rgalland/SNES_S-CPU_Schematics/S-CPU_gates/AND.png

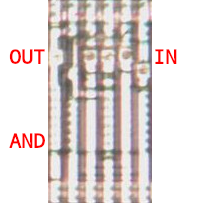
S-CPU_gates/AND.png
