rgalland/SNES_S-CPU_Schematics/S-CPU_gates/AOI_22.png

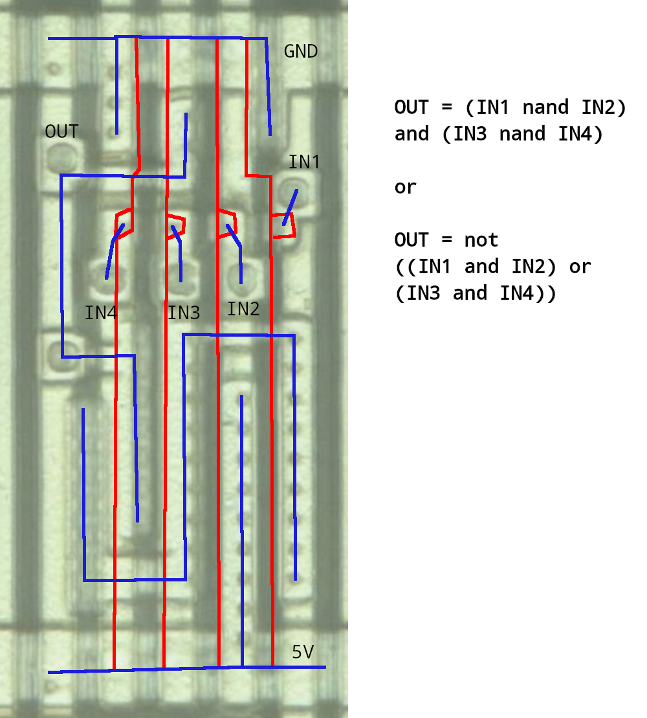
S-CPU_gates/AOI_22.png
