rgalland/SNES_S-CPU_Schematics/S-CPU_gates/AOI_222.png

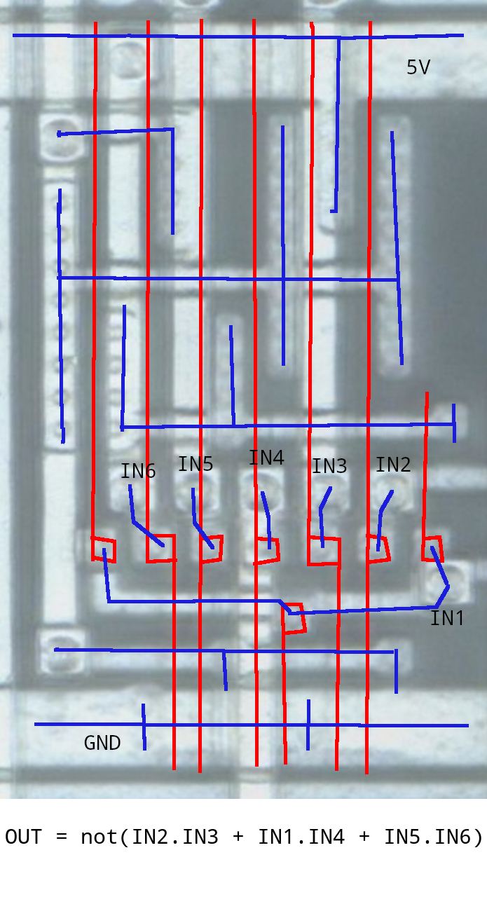
S-CPU_gates/AOI_222.png
