rgalland/SNES_S-CPU_Schematics/S-CPU_gates/Buf.png

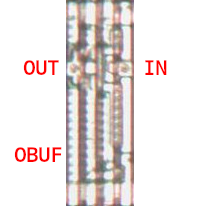
S-CPU_gates/Buf.png
