rgalland/SNES_S-CPU_Schematics/S-CPU_gates/BUF_HiZ.png

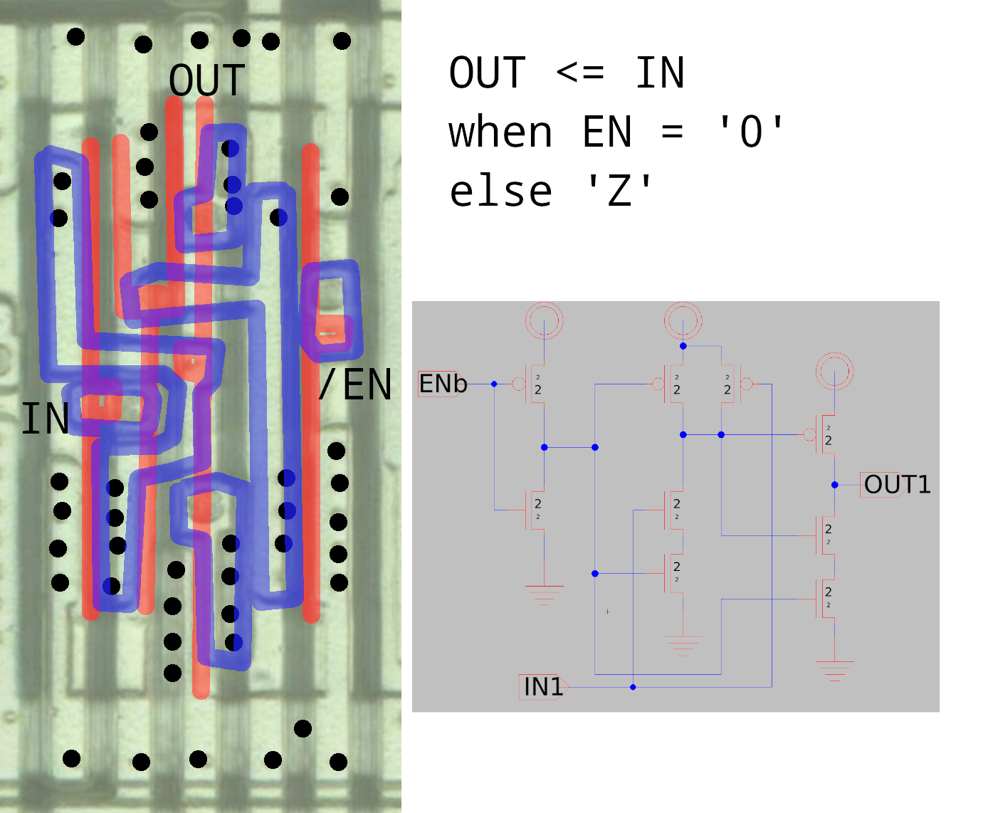
S-CPU_gates/BUF_HiZ.png
