rgalland/SNES_S-CPU_Schematics/S-CPU_gates/bus_direction_buffer.png

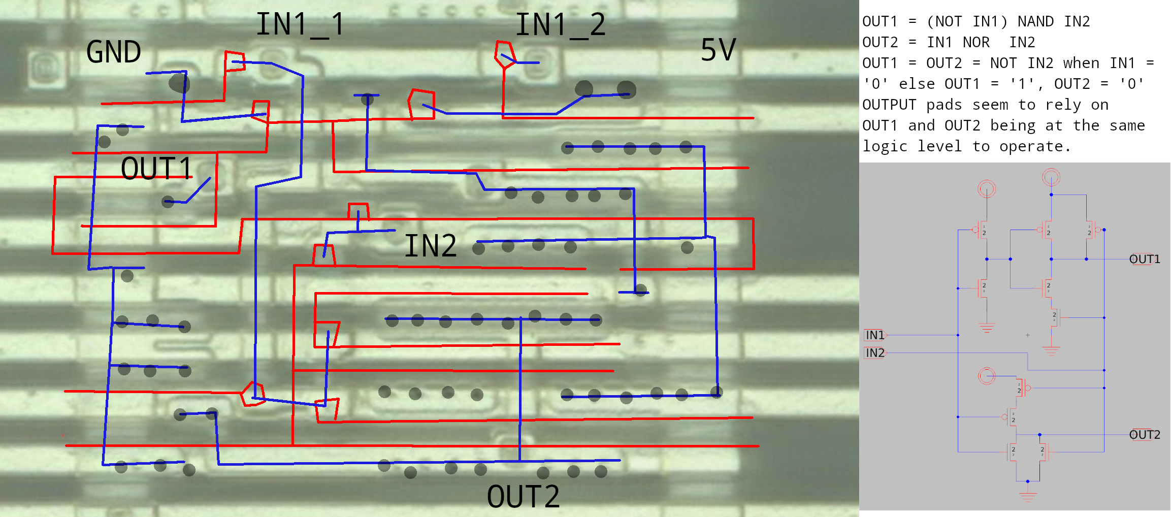
S-CPU_gates/bus_direction_buffer.png
