rgalland/SNES_S-CPU_Schematics/S-CPU_gates/DEMUX_3-8.png

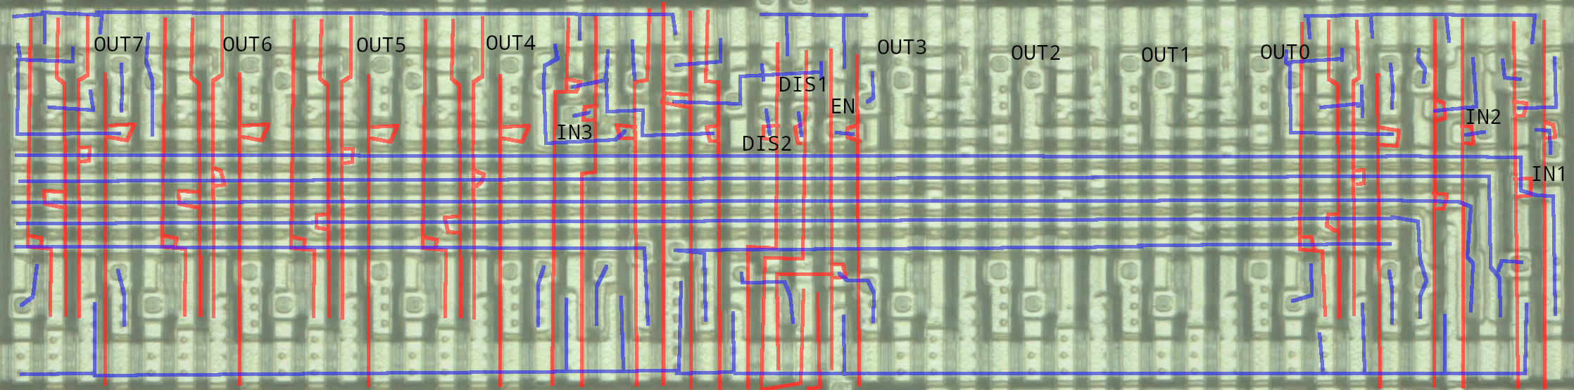
S-CPU_gates/DEMUX_3-8.png
