rgalland/SNES_S-CPU_Schematics/S-CPU_gates/dff.png

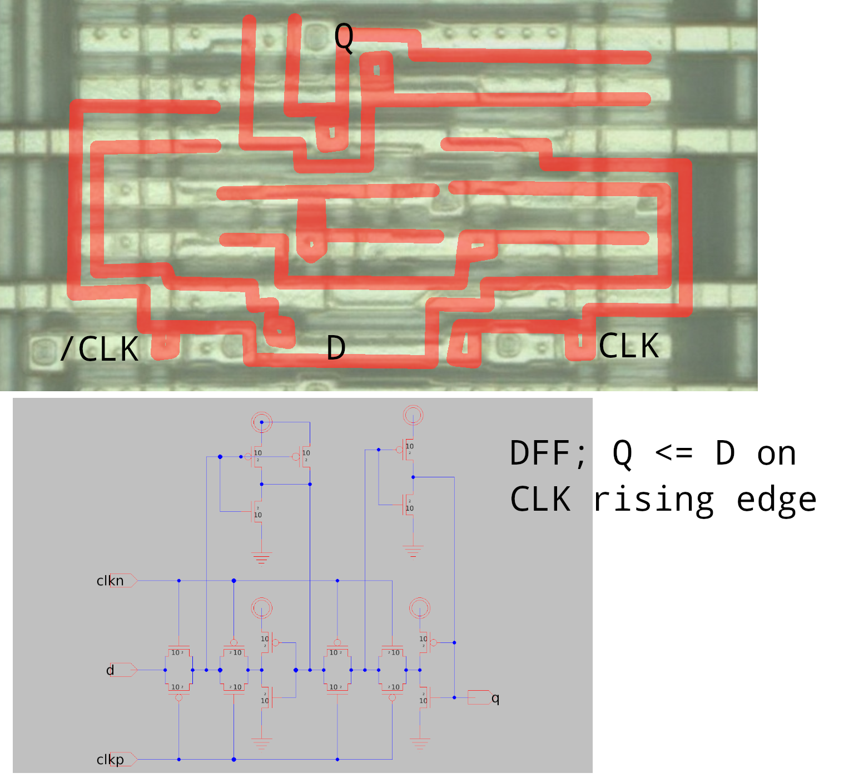
S-CPU_gates/dff.png
