rgalland/SNES_S-CPU_Schematics/S-CPU_gates/dff_wEn.png

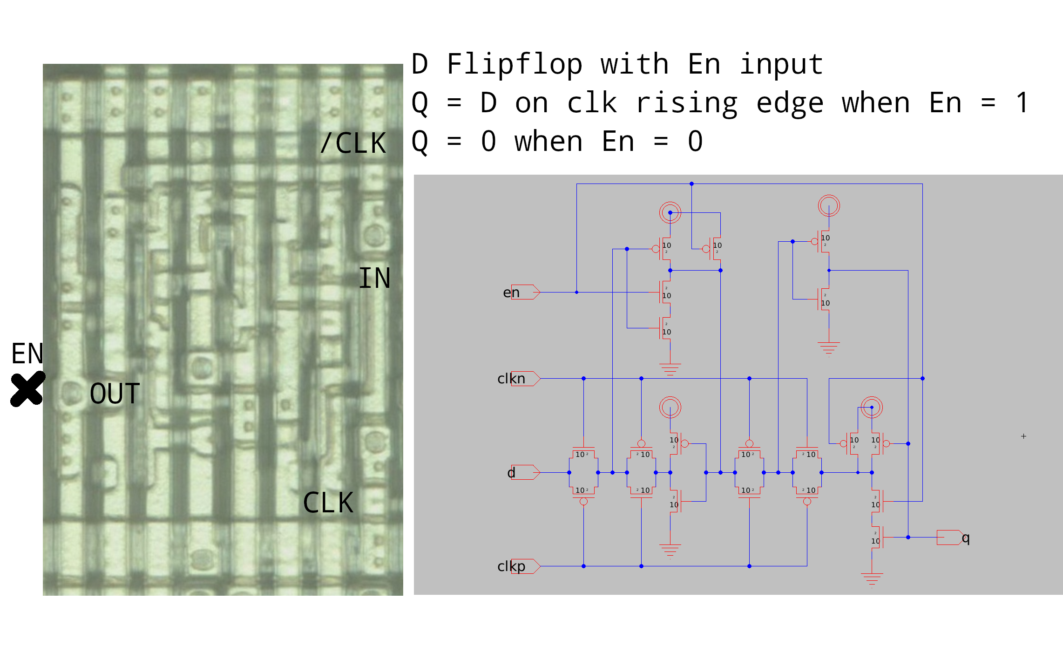
S-CPU_gates/dff_wEn.png
