rgalland/SNES_S-CPU_Schematics/S-CPU_gates/dff_wEn_v4.png

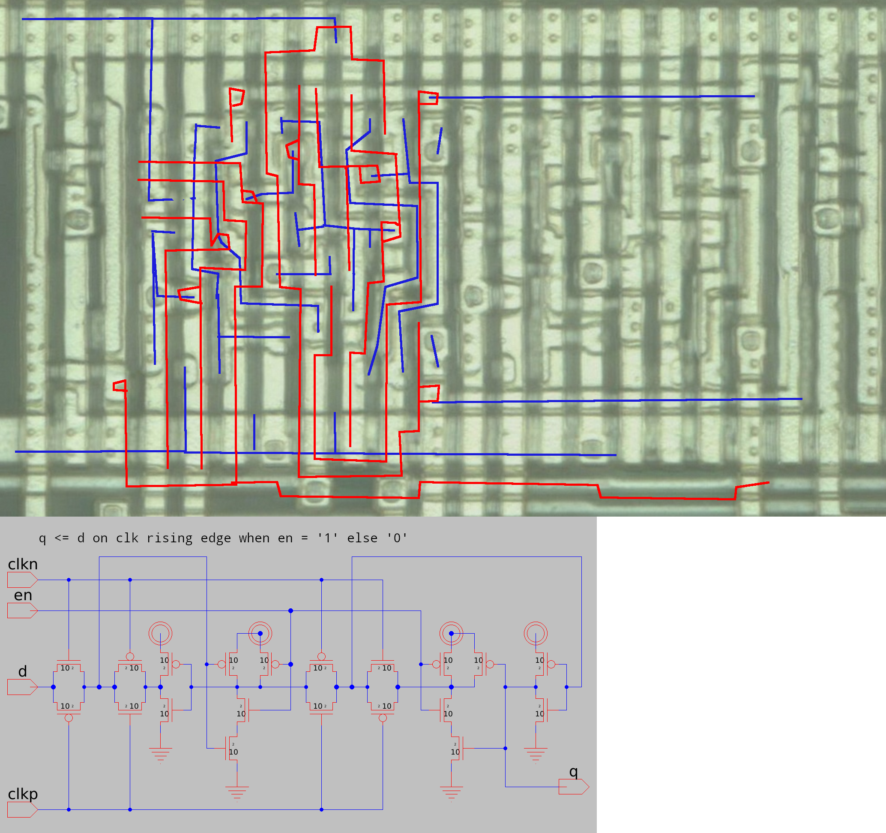
S-CPU_gates/dff_wEn_v4.png
