rgalland/SNES_S-CPU_Schematics/S-CPU_gates/dff_wEn_wCLKInv.png

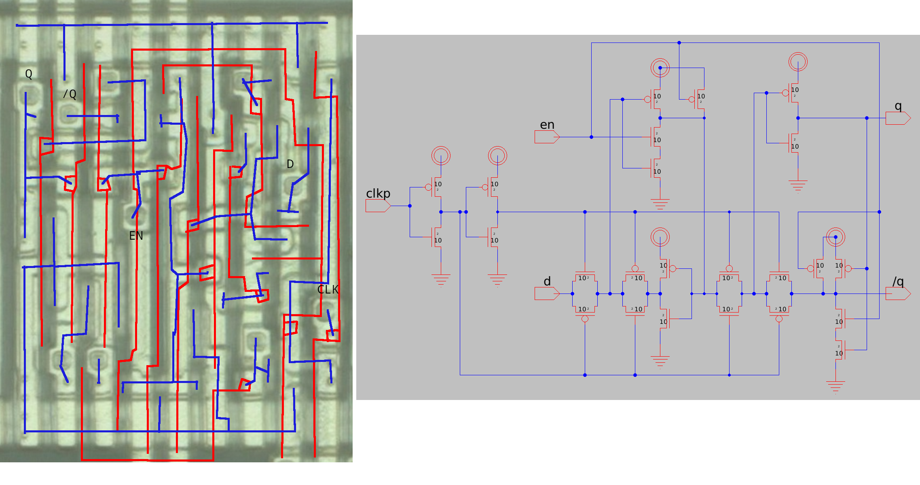
S-CPU_gates/dff_wEn_wCLKInv.png
