rgalland/SNES_S-CPU_Schematics/S-CPU_gates/dff_wRST_wCLKInv.png

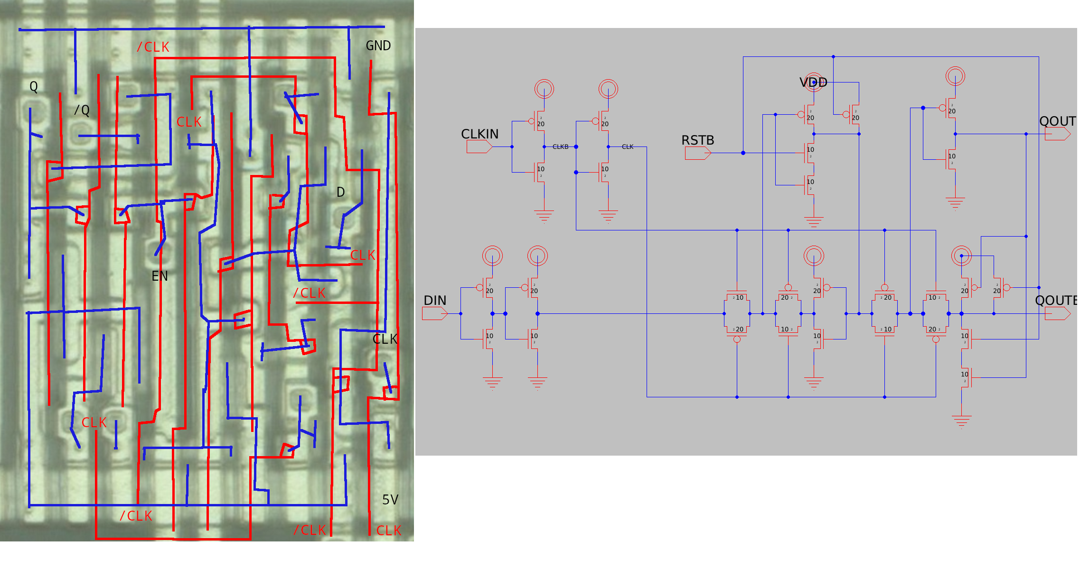
S-CPU_gates/dff_wRST_wCLKInv.png
