rgalland/SNES_S-CPU_Schematics/S-CPU_gates/DFFR_wCLKInv.png

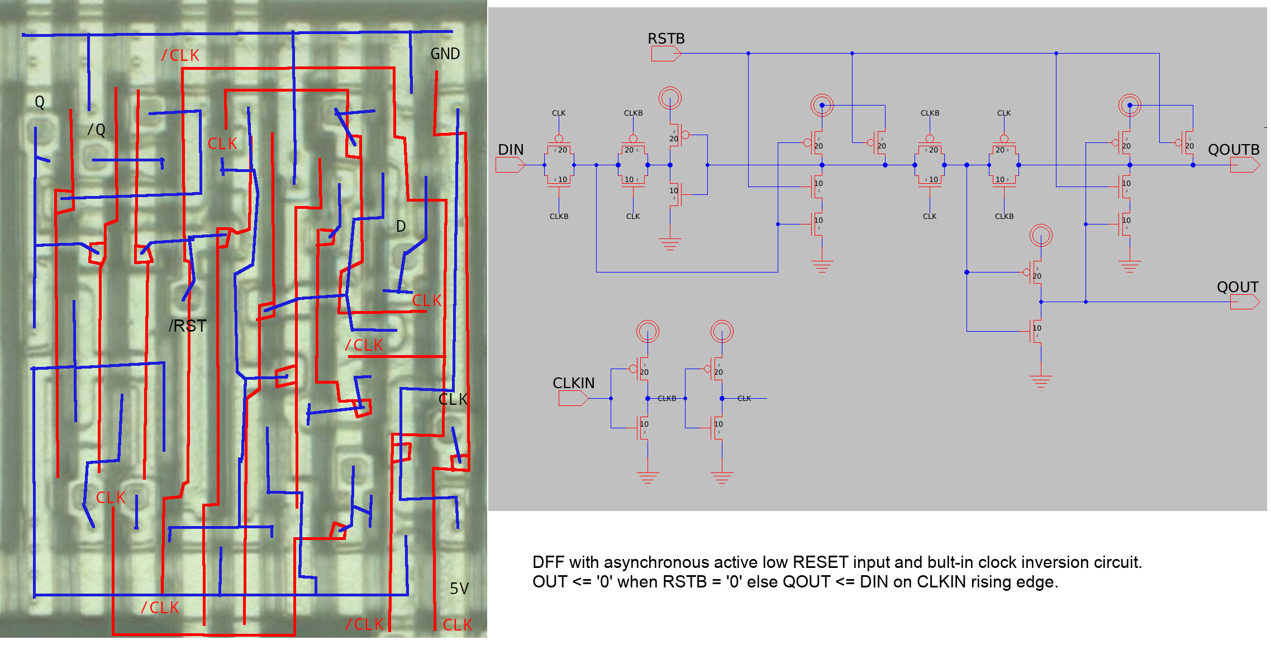
S-CPU_gates/DFFR_wCLKInv.png
