rgalland/SNES_S-CPU_Schematics/S-CPU_gates/latch.png

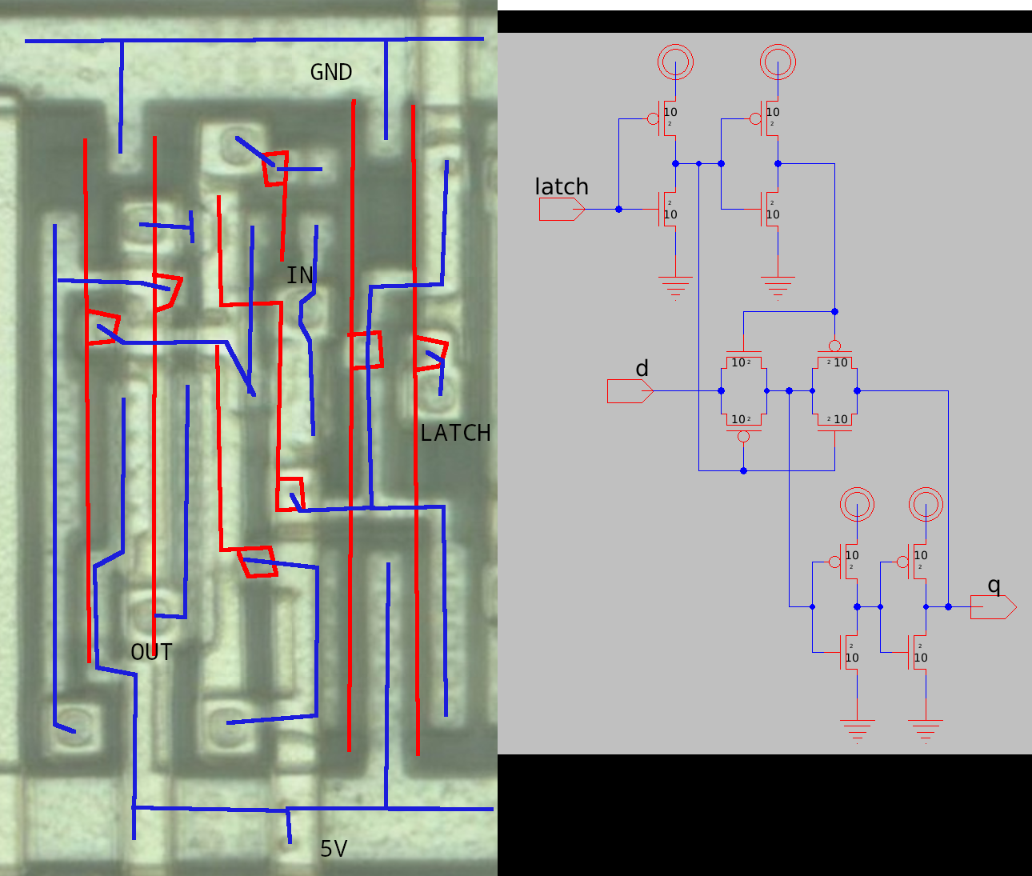
S-CPU_gates/latch.png
