rgalland/SNES_S-CPU_Schematics/S-CPU_gates/latch_wDIS_RST.png

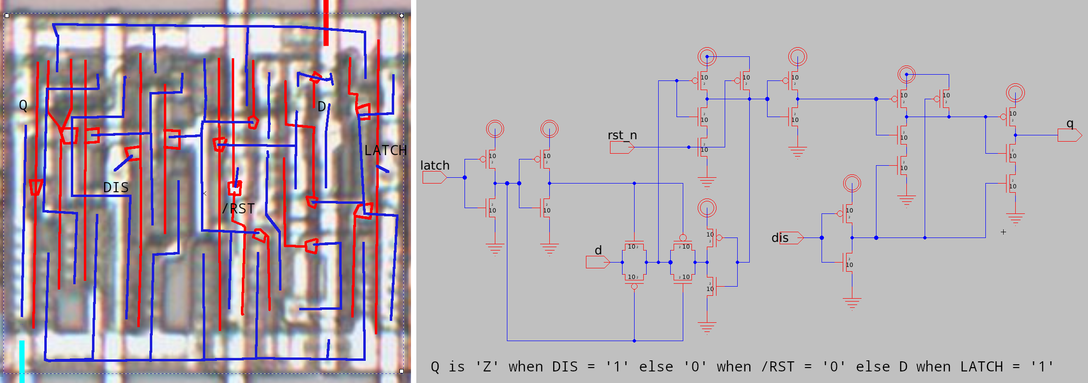
S-CPU_gates/latch_wDIS_RST.png
