rgalland/SNES_S-CPU_Schematics/S-CPU_gates/latch_wRST.png

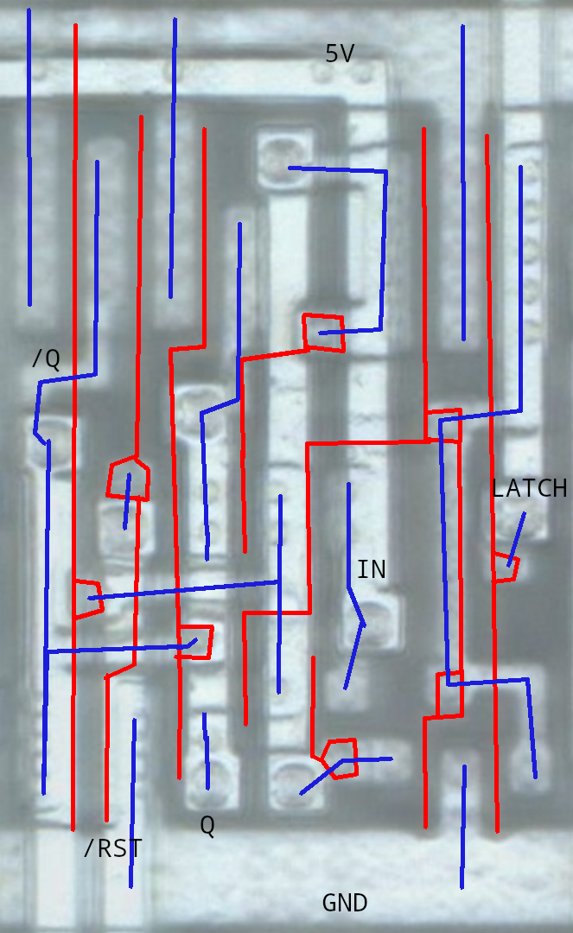
S-CPU_gates/latch_wRST.png
