rgalland/SNES_S-CPU_Schematics/S-CPU_gates/MUX_2:1x4.png

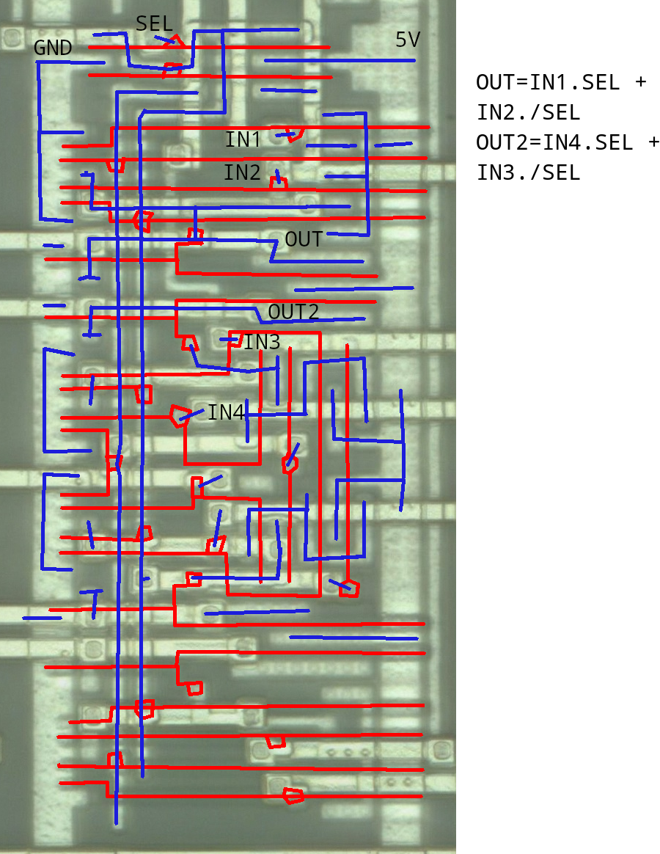
S-CPU_gates/MUX_2:1x4.png
