rgalland/SNES_S-CPU_Schematics/S-CPU_gates/MUX_ARRAY_2:1.png

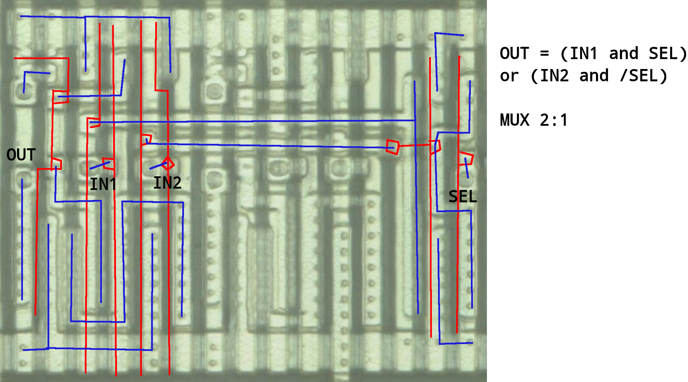
S-CPU_gates/MUX_ARRAY_2:1.png
