rgalland/SNES_S-CPU_Schematics/S-CPU_gates/NAND_LATCH.png

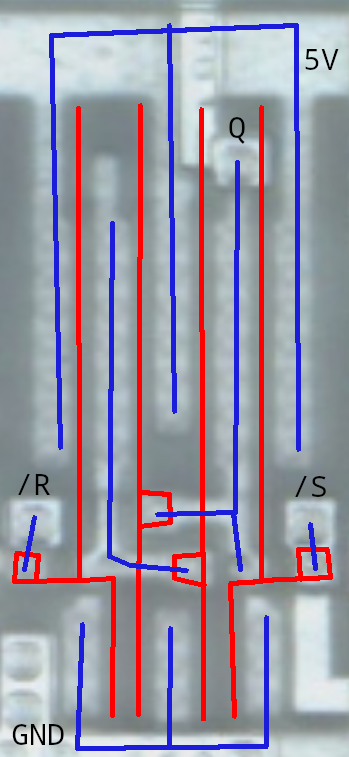
S-CPU_gates/NAND_LATCH.png
