rgalland/SNES_S-CPU_Schematics/S-CPU_gates/NOR_6.png

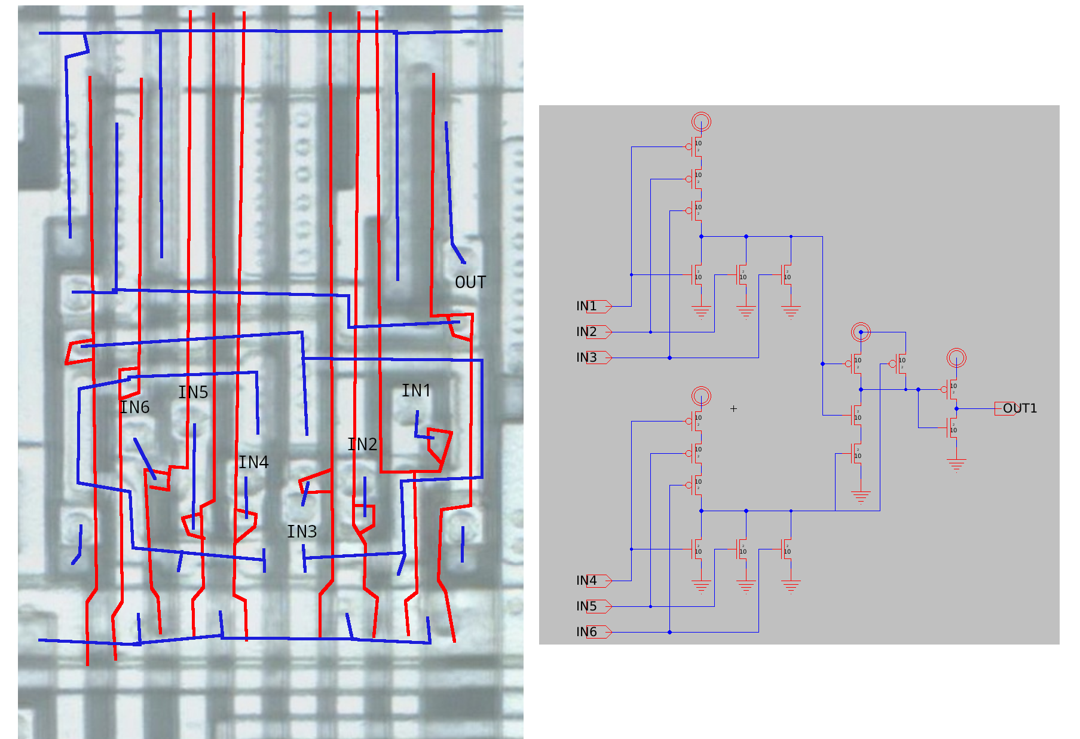
S-CPU_gates/NOR_6.png
