rgalland/SNES_S-CPU_Schematics/S-CPU_gates/NOT.png

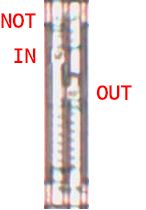
S-CPU_gates/NOT.png
