rgalland/SNES_S-CPU_Schematics/S-CPU_gates/OAI_13.png

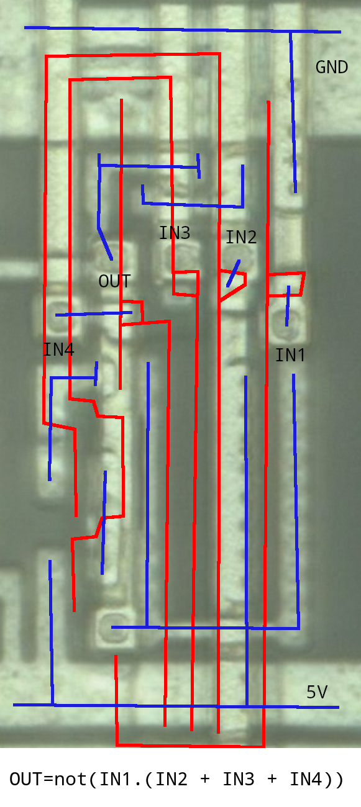
S-CPU_gates/OAI_13.png
