rgalland/SNES_S-CPU_Schematics/S-CPU_gates/OAI_22.png

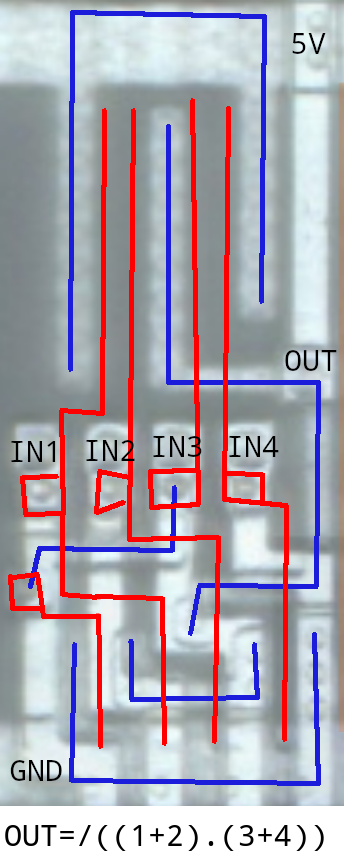
S-CPU_gates/OAI_22.png
