rgalland/SNES_S-CPU_Schematics/S-CPU_gates/OAI_112.png

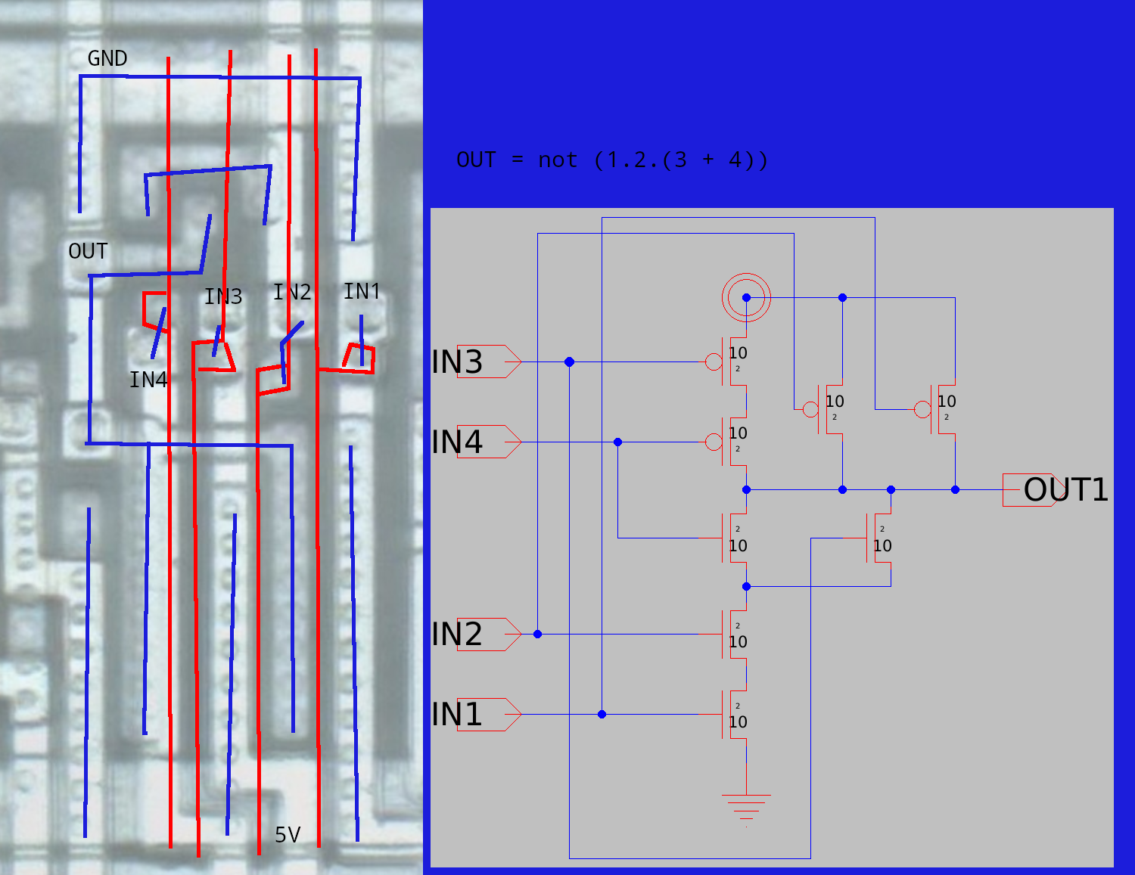
S-CPU_gates/OAI_112.png
