rgalland/SNES_S-CPU_Schematics/S-CPU_gates/OAI_2222.png

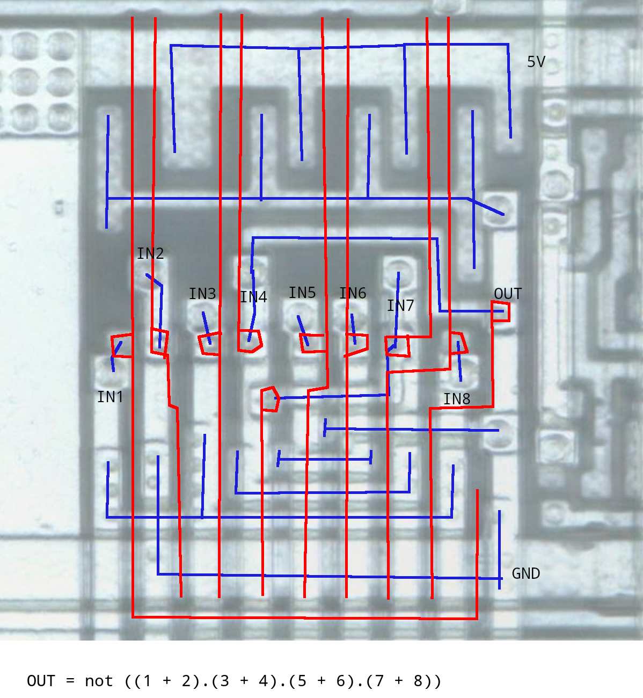
S-CPU_gates/OAI_2222.png
