rgalland/SNES_S-CPU_Schematics/S-CPU_gates/TriBuf.png

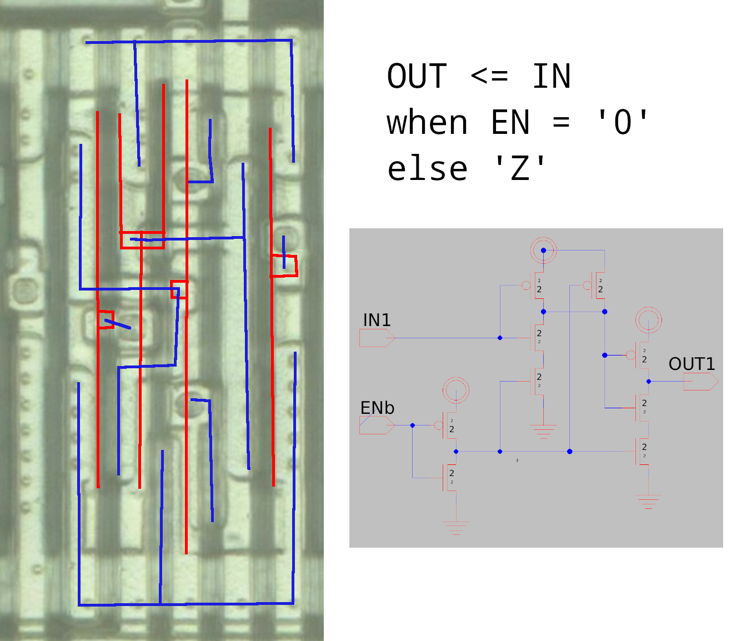
S-CPU_gates/TriBuf.png
