rgalland/SNES_S-CPU_Schematics/S-CPU_gates/TriBuf_3.png

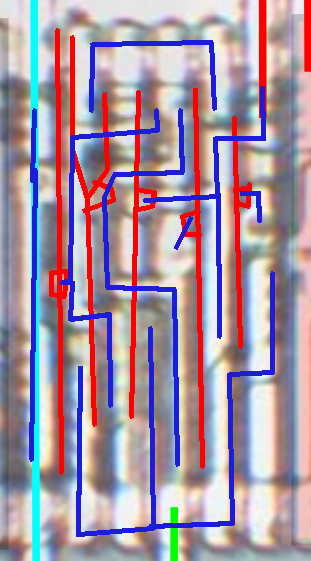
S-CPU_gates/TriBuf_3.png
