rgalland/SNES_S-CPU_Schematics/S-CPU_gates/XOR.png

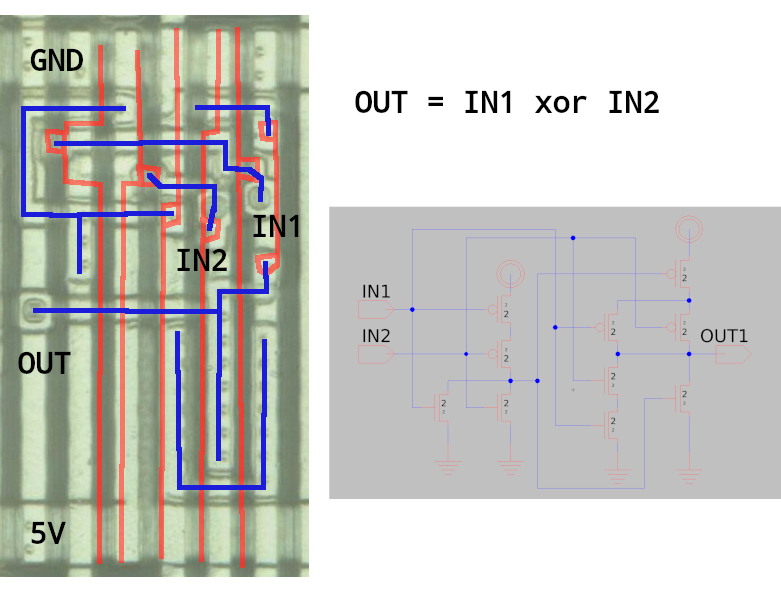
S-CPU_gates/XOR.png
