rgalland/SNES_S-CPU_Schematics/S-CPU_vlsi/and2nor3.png

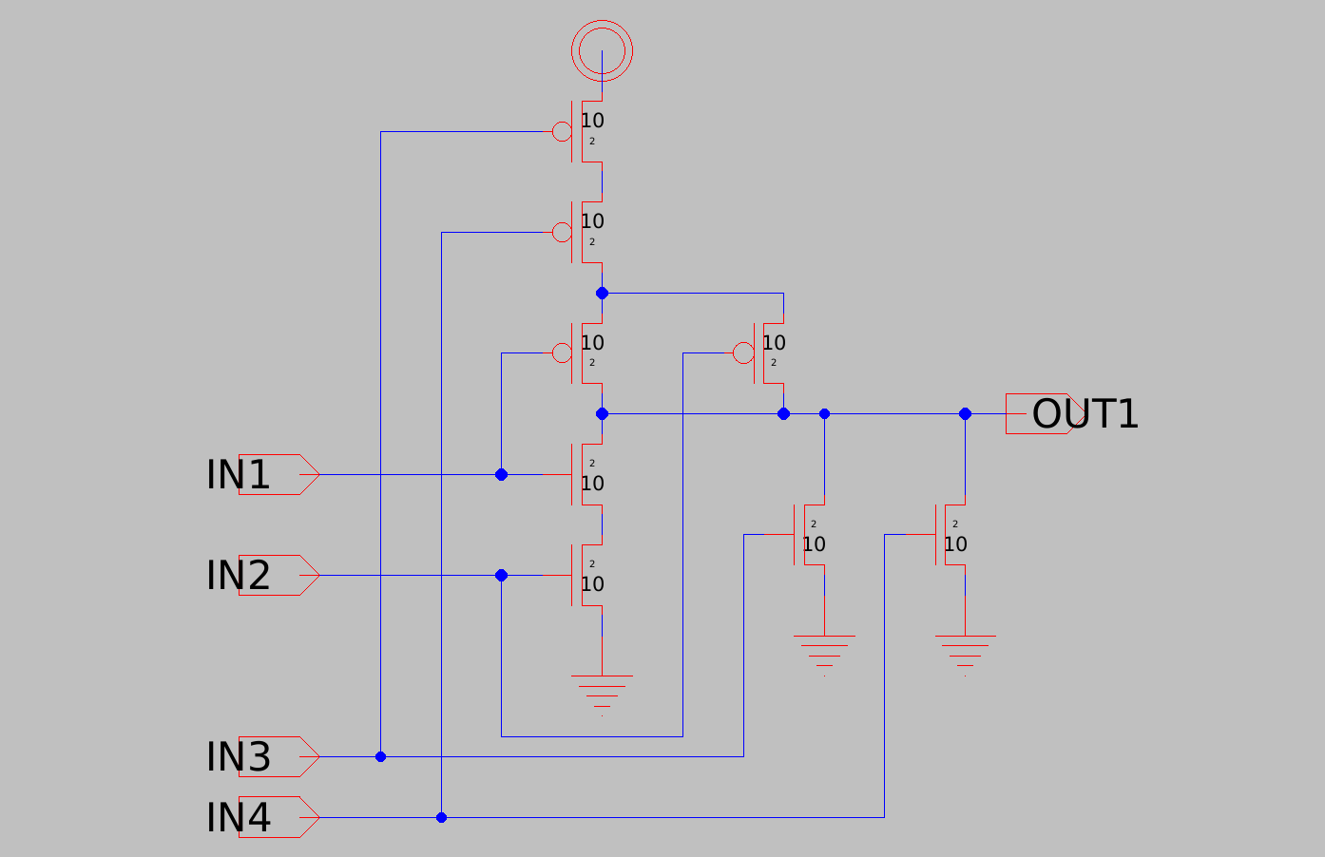
S-CPU_vlsi/and2nor3.png
