rgalland/SNES_S-CPU_Schematics/S-CPU_vlsi/buffer_wEN.png

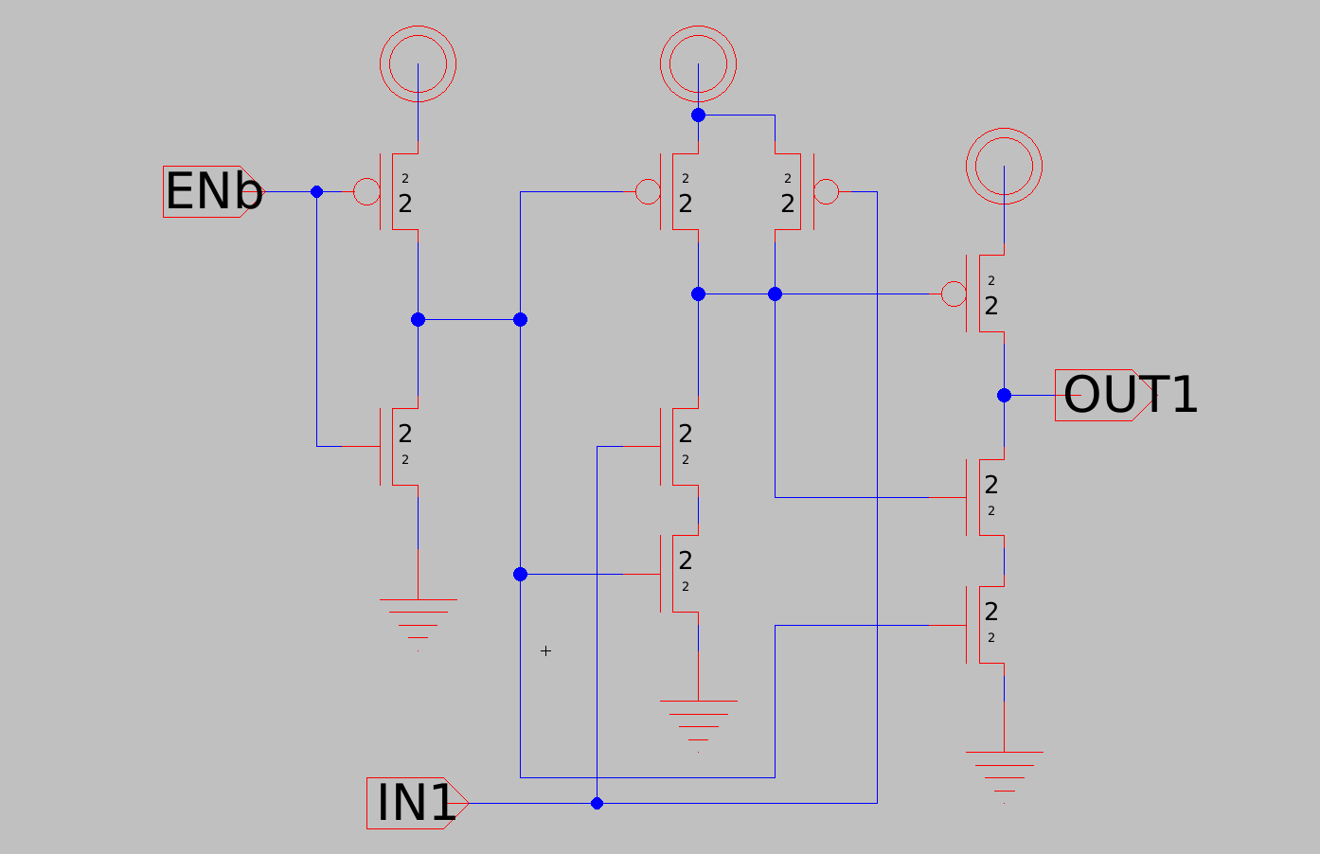
S-CPU_vlsi/buffer_wEN.png
