rgalland/SNES_S-CPU_Schematics/S-CPU_vlsi/bus_direction_buffer.png

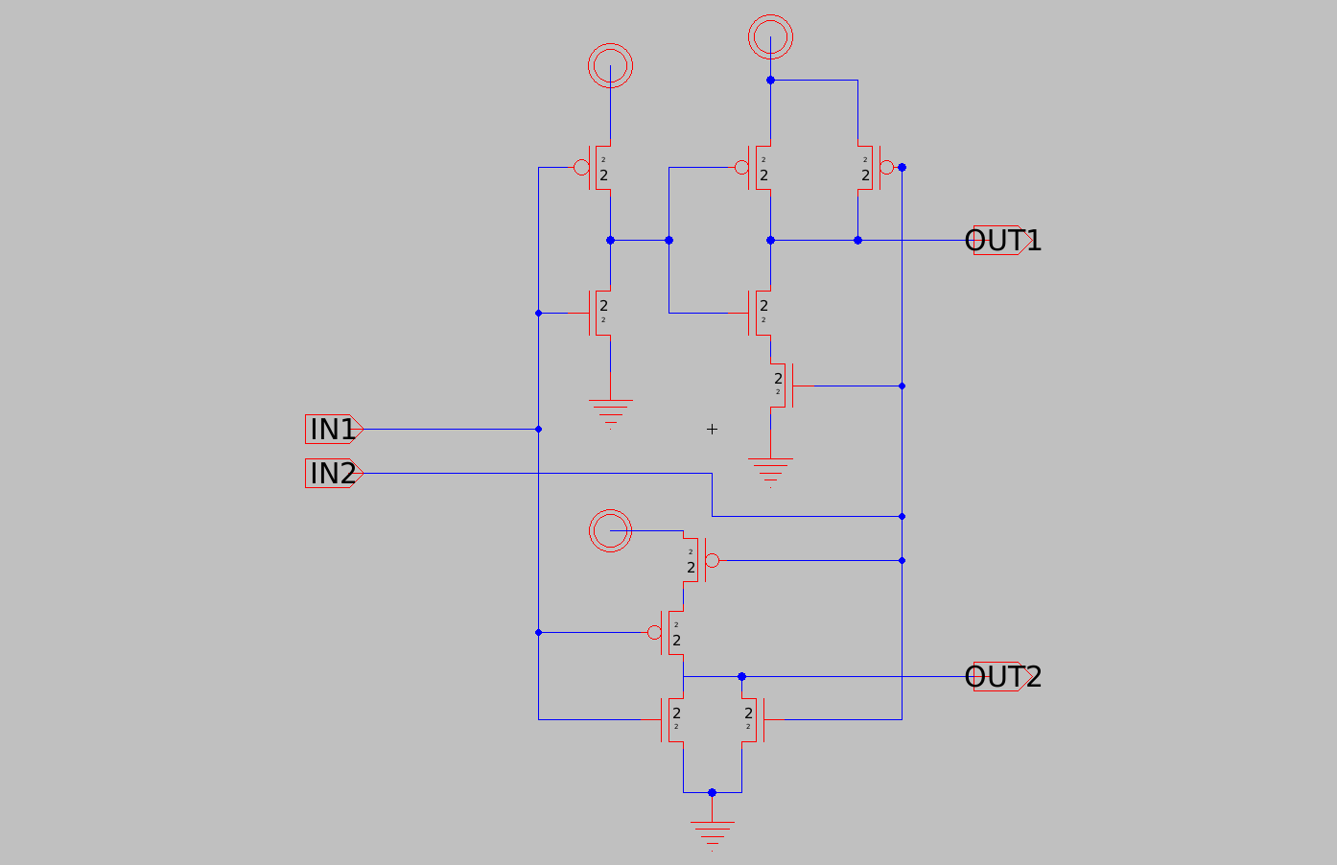
S-CPU_vlsi/bus_direction_buffer.png
