rgalland/SNES_S-CPU_Schematics/S-CPU_vlsi/dff.png

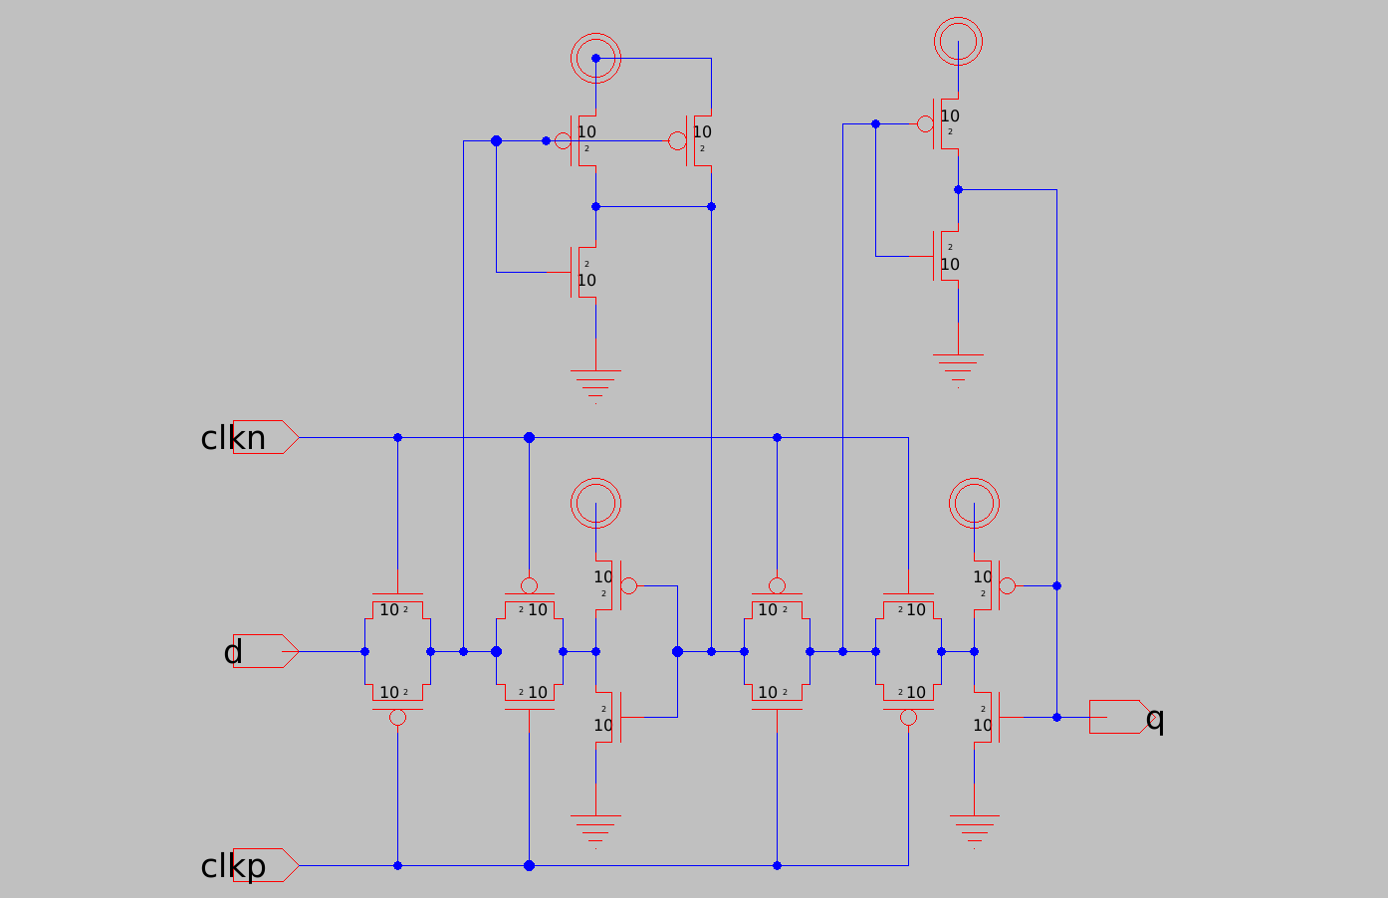
S-CPU_vlsi/dff.png
