rgalland/SNES_S-CPU_Schematics/S-CPU_vlsi/dff_wEN.png

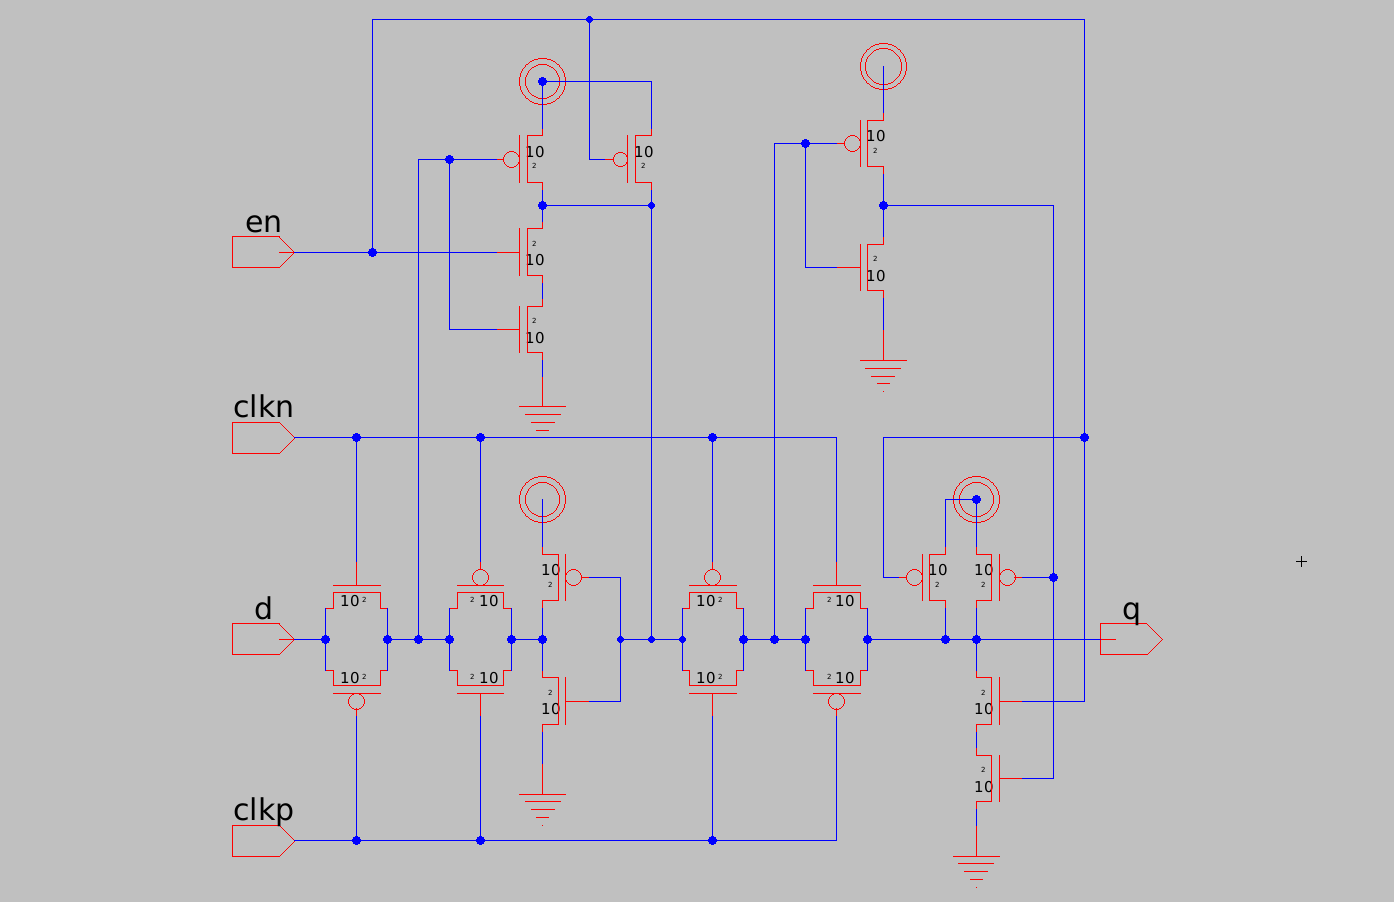
S-CPU_vlsi/dff_wEN.png
