rgalland/SNES_S-CPU_Schematics/S-CPU_vlsi/dff_wEN_type2.png

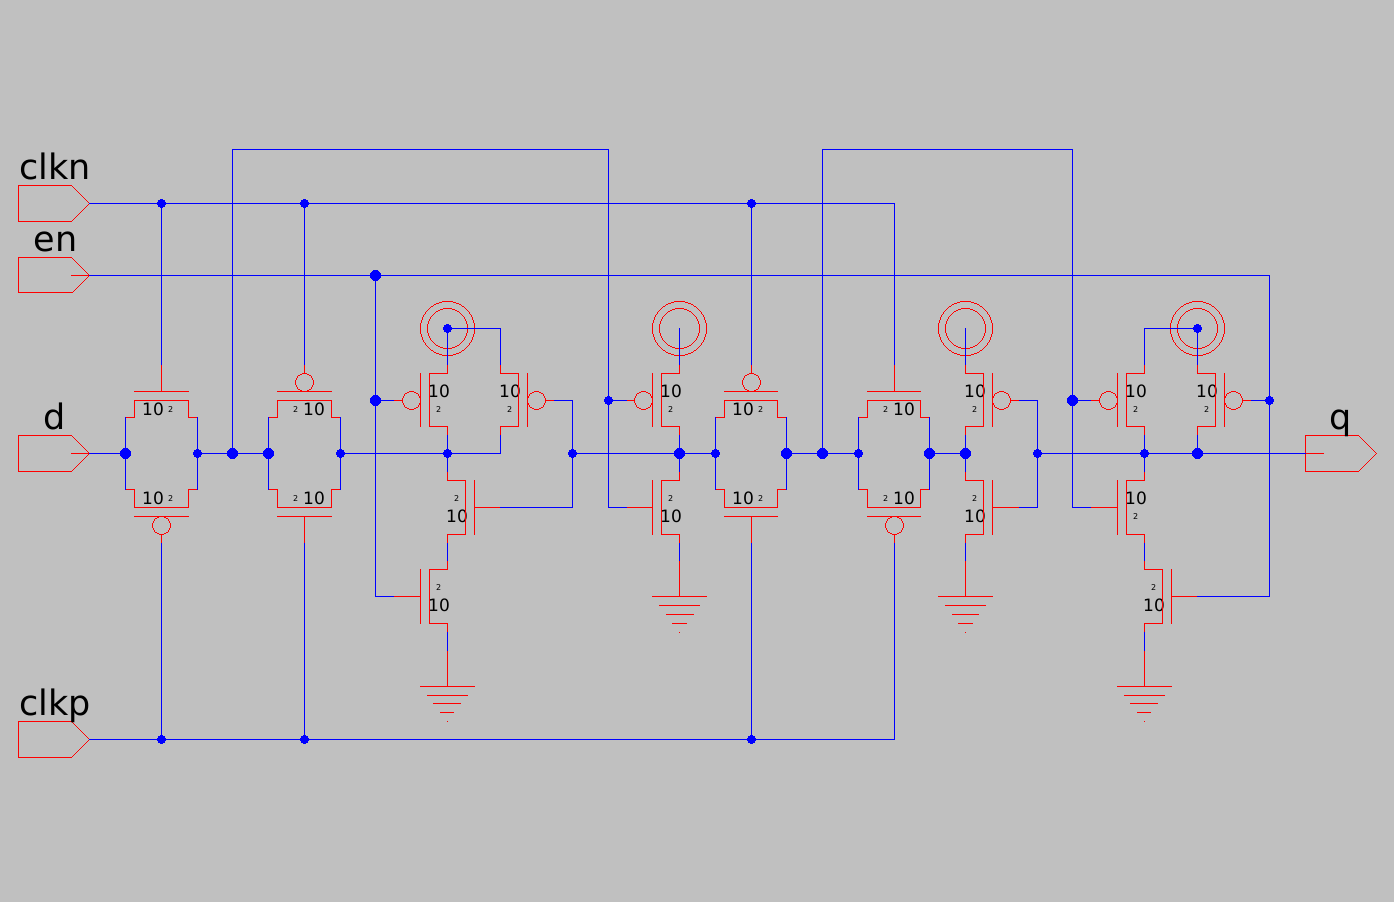
S-CPU_vlsi/dff_wEN_type2.png
