rgalland/SNES_S-CPU_Schematics/S-CPU_vlsi/dff_wRST_CLKInv.png

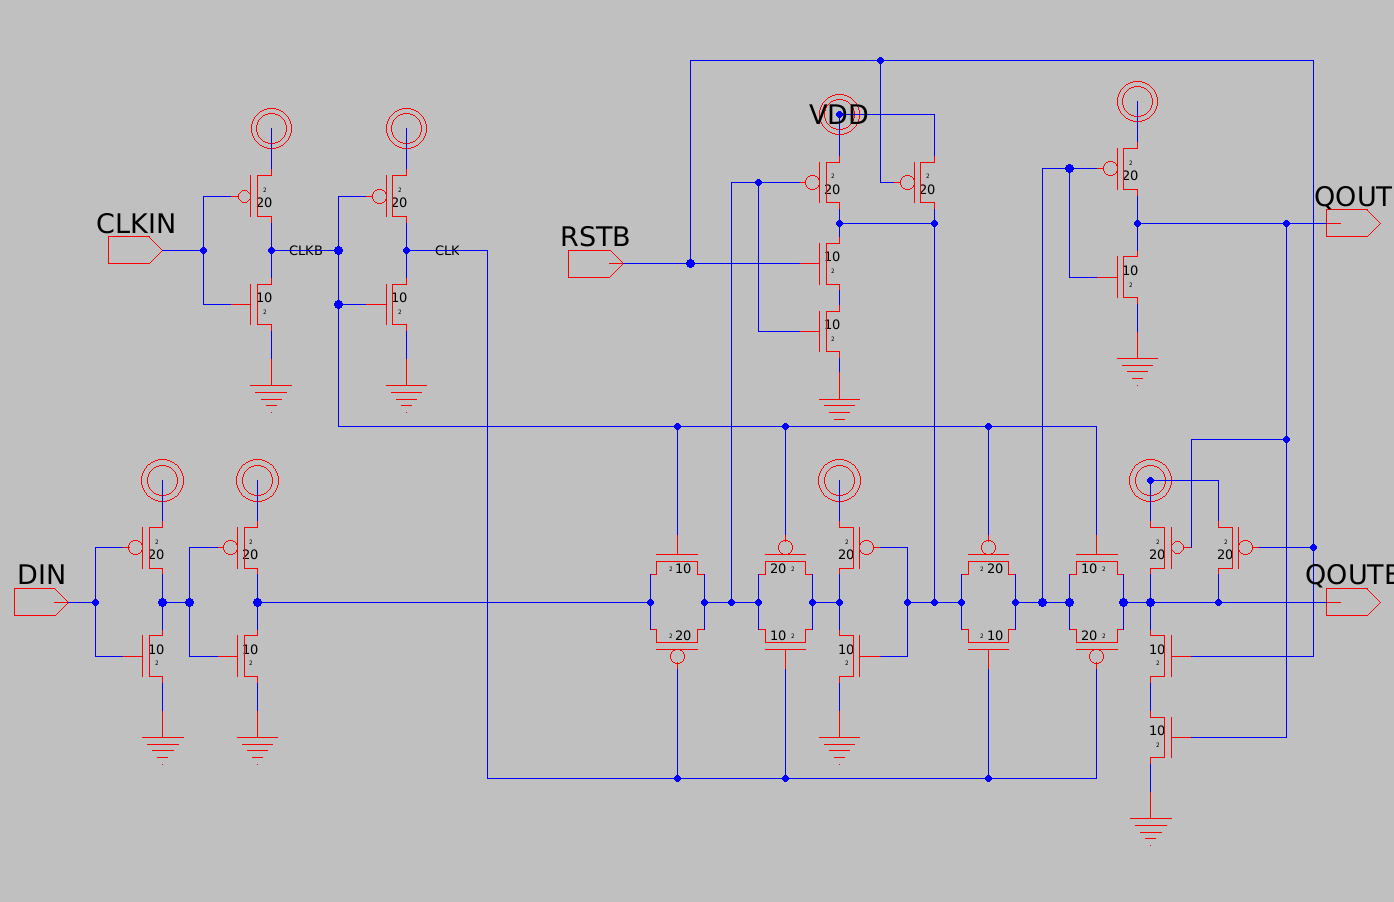
S-CPU_vlsi/dff_wRST_CLKInv.png
