rgalland/SNES_S-CPU_Schematics/S-CPU_vlsi/DFFR_wCLKInv.png

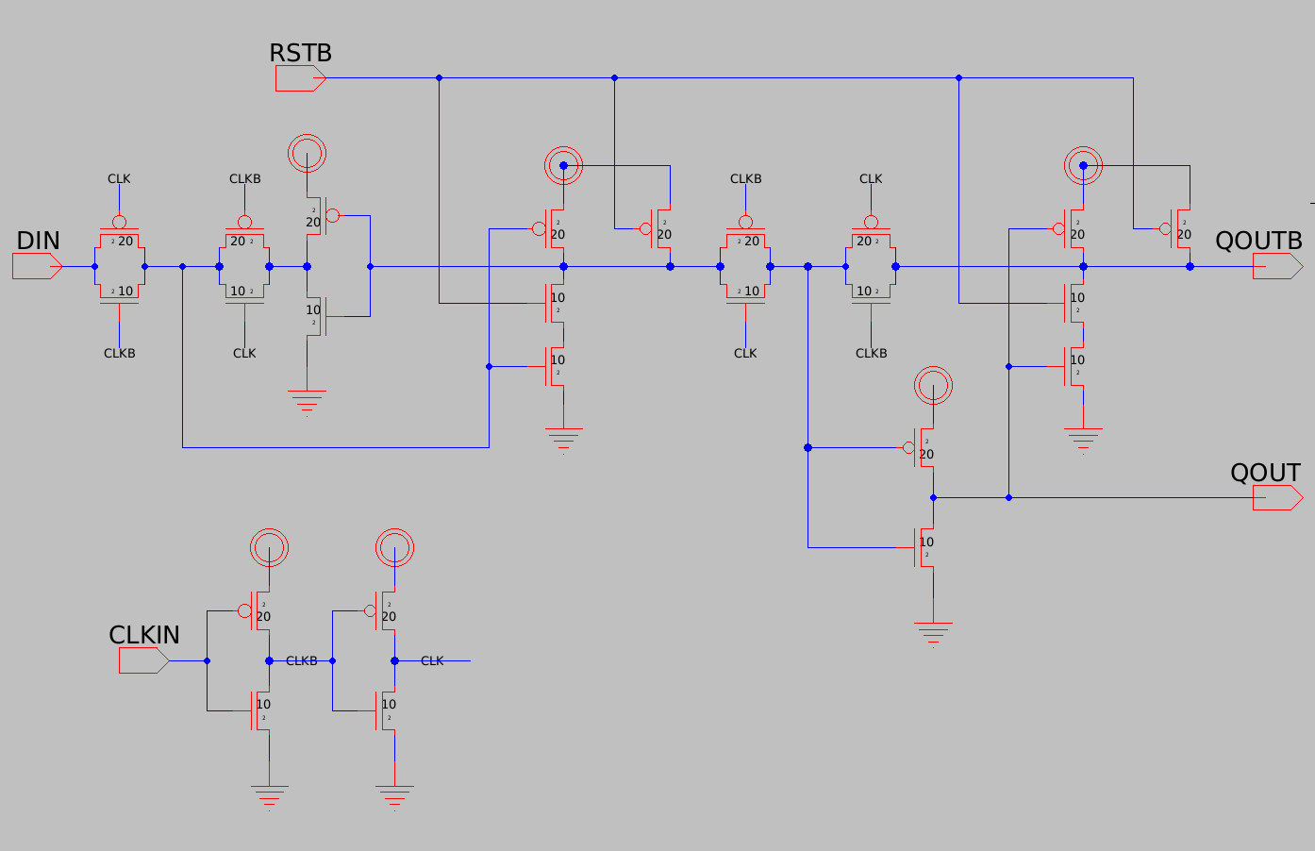
S-CPU_vlsi/DFFR_wCLKInv.png
