rgalland/SNES_S-CPU_Schematics/S-CPU_vlsi/latch.png

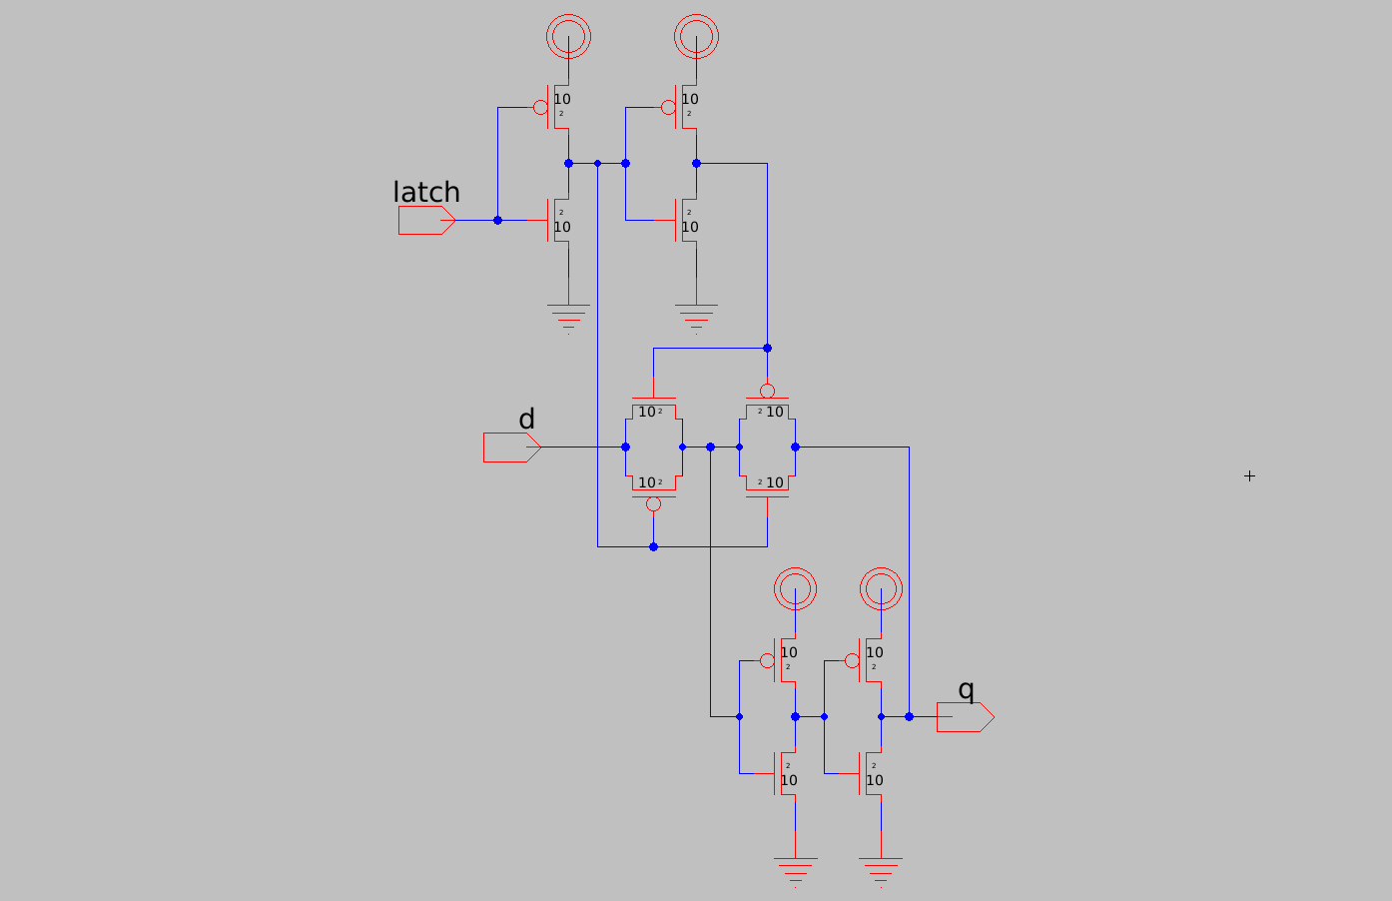
S-CPU_vlsi/latch.png
