rgalland/SNES_S-CPU_Schematics/S-CPU_vlsi/latch_wDIS_RST.png

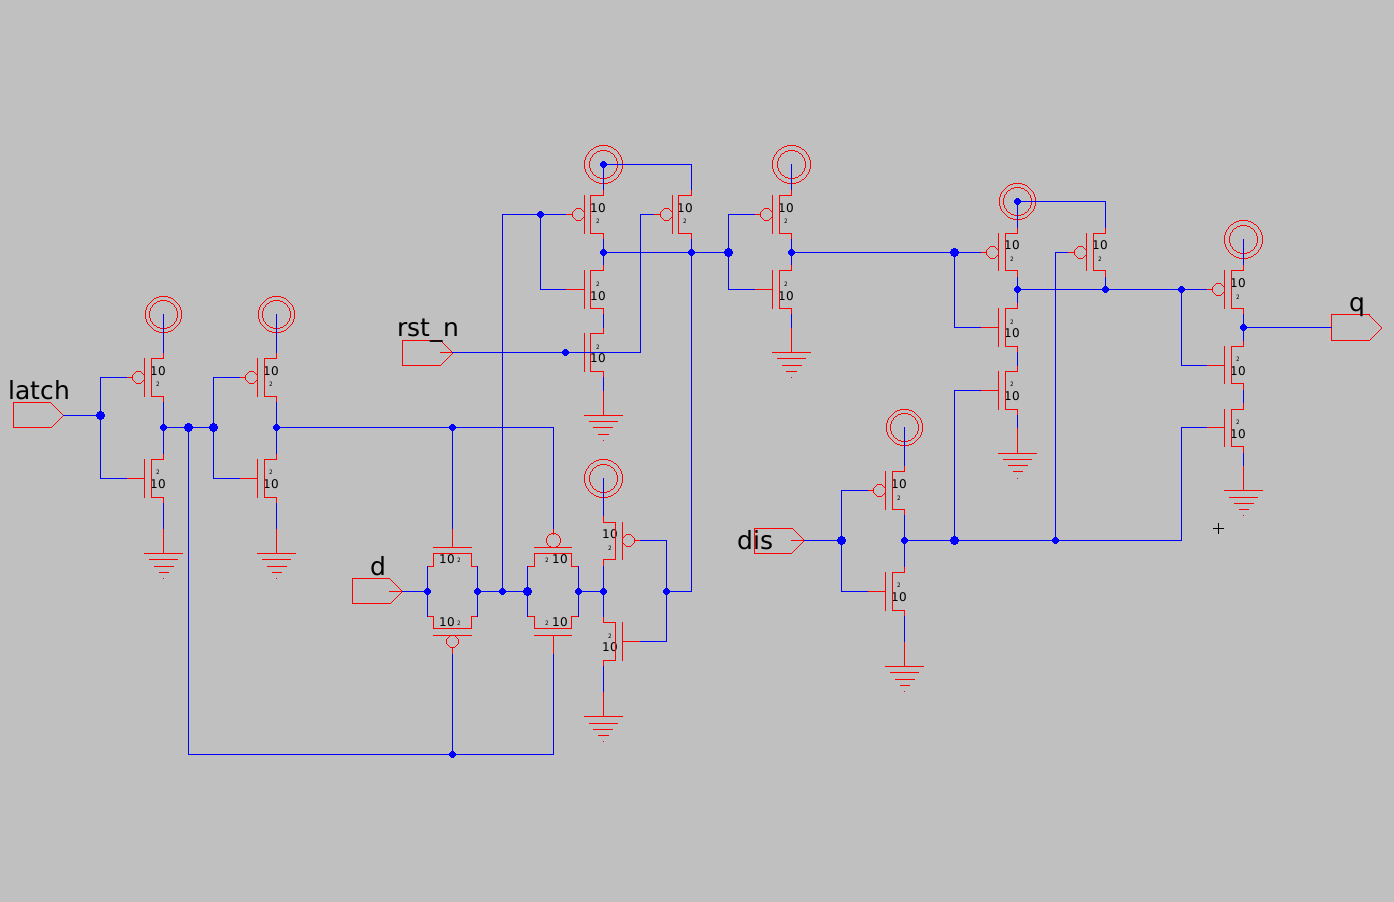
S-CPU_vlsi/latch_wDIS_RST.png
