rgalland/SNES_S-CPU_Schematics/S-CPU_vlsi/mux_4to1.png

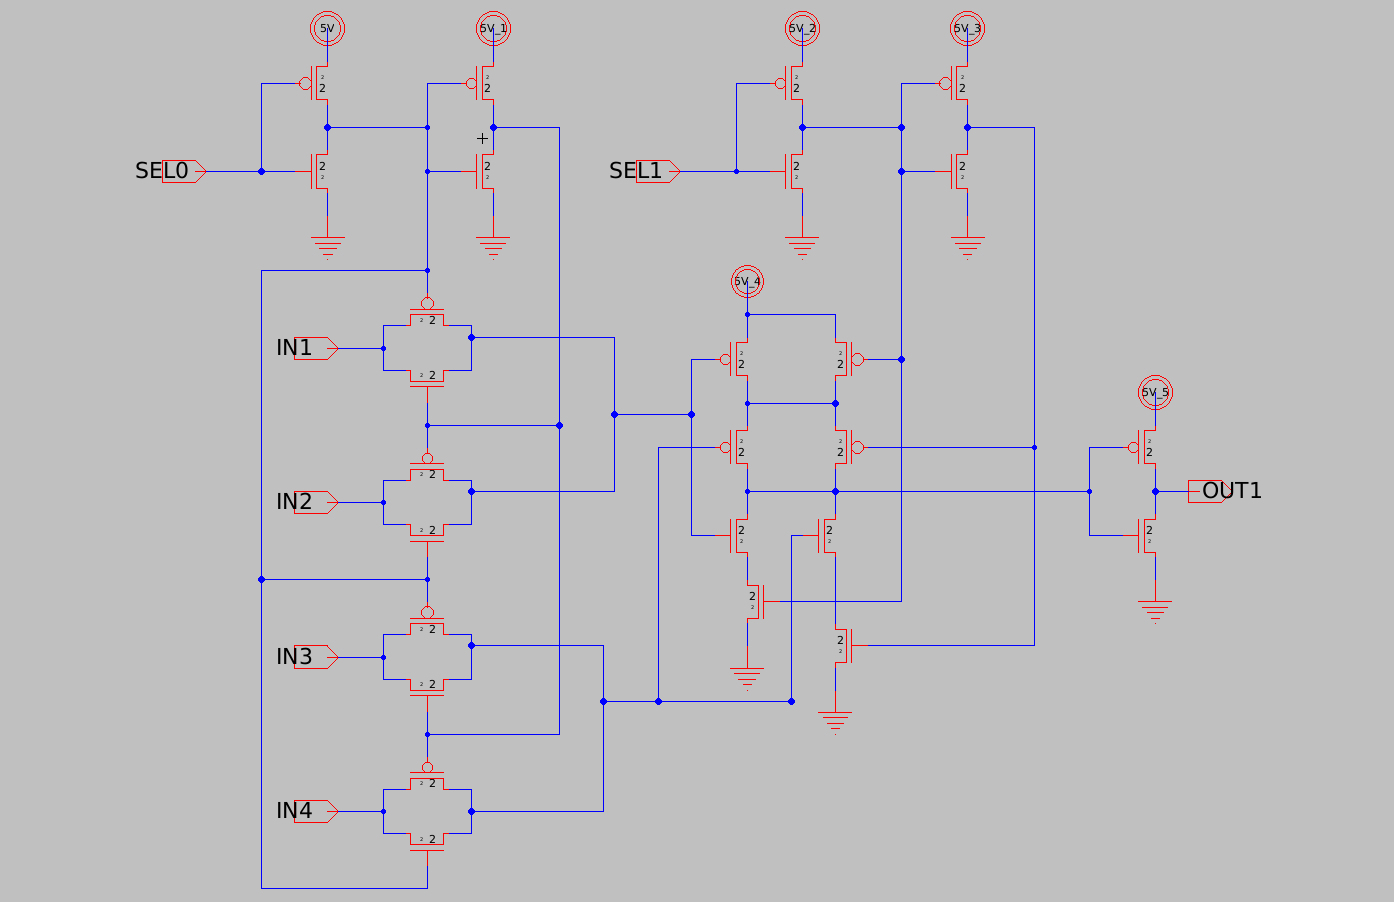
S-CPU_vlsi/mux_4to1.png
