rgalland/SNES_S-CPU_Schematics/S-CPU_vlsi/nor6.png

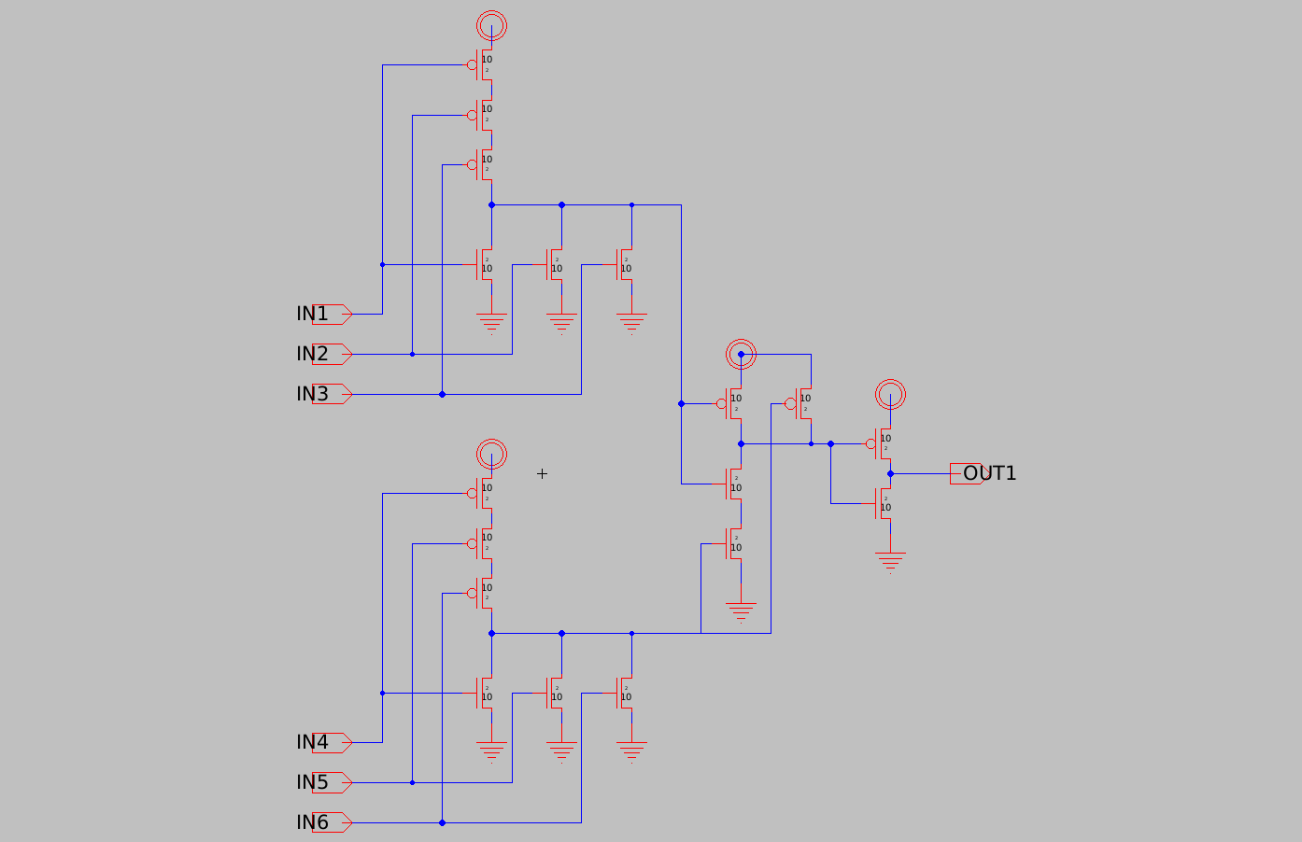
S-CPU_vlsi/nor6.png
