rgalland/SNES_S-CPU_Schematics/S-CPU_vlsi/OAI_112.png

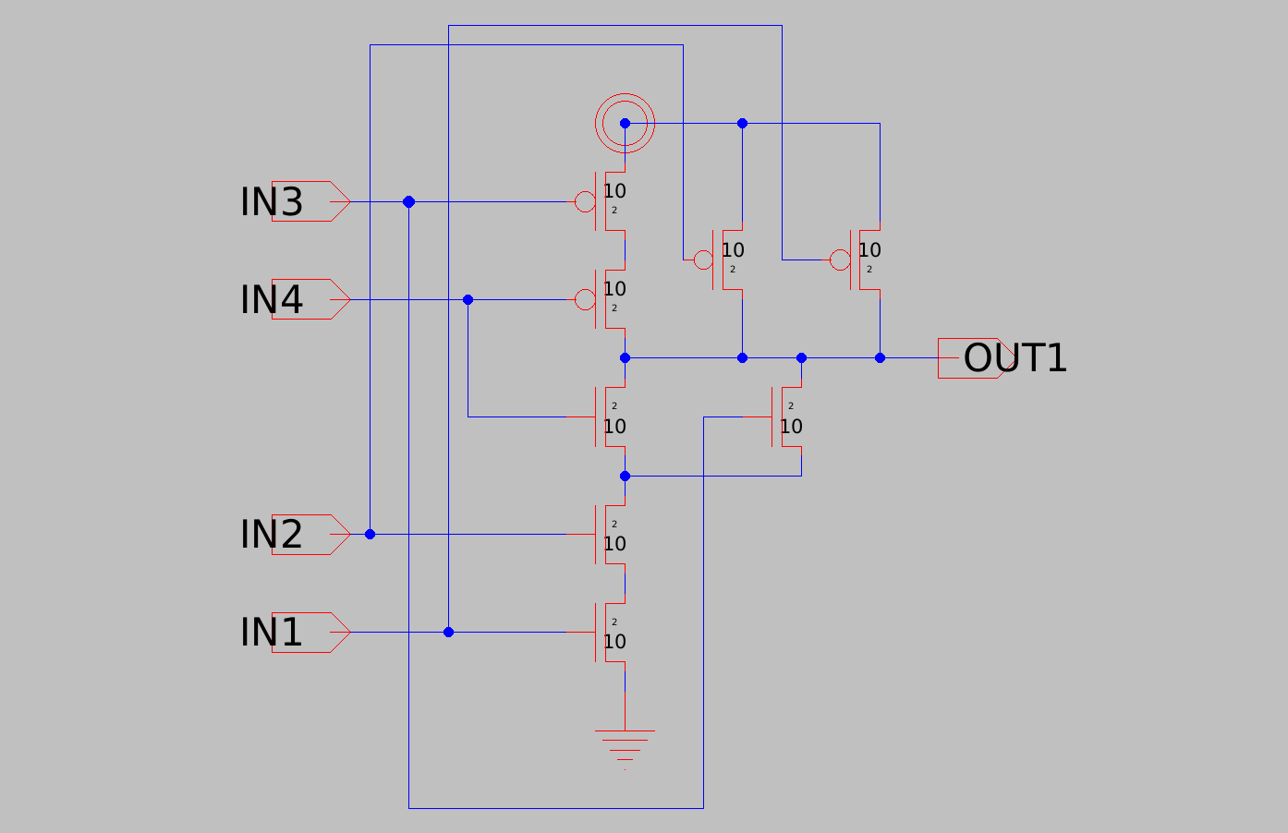
S-CPU_vlsi/OAI_112.png
