rgalland/SNES_S-CPU_Schematics/S-CPU_vlsi/TriBuff.png

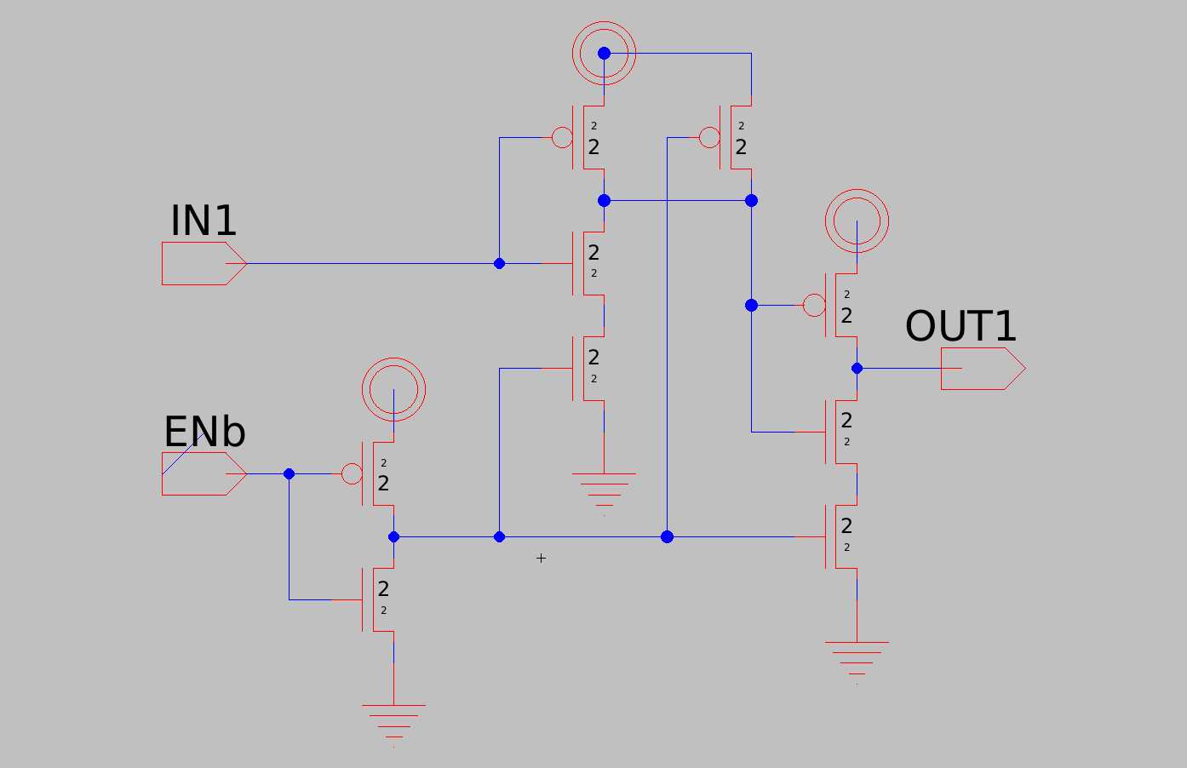
S-CPU_vlsi/TriBuff.png
