rgalland/SNES_S-CPU_Schematics/S-CPU_vlsi/xor.png

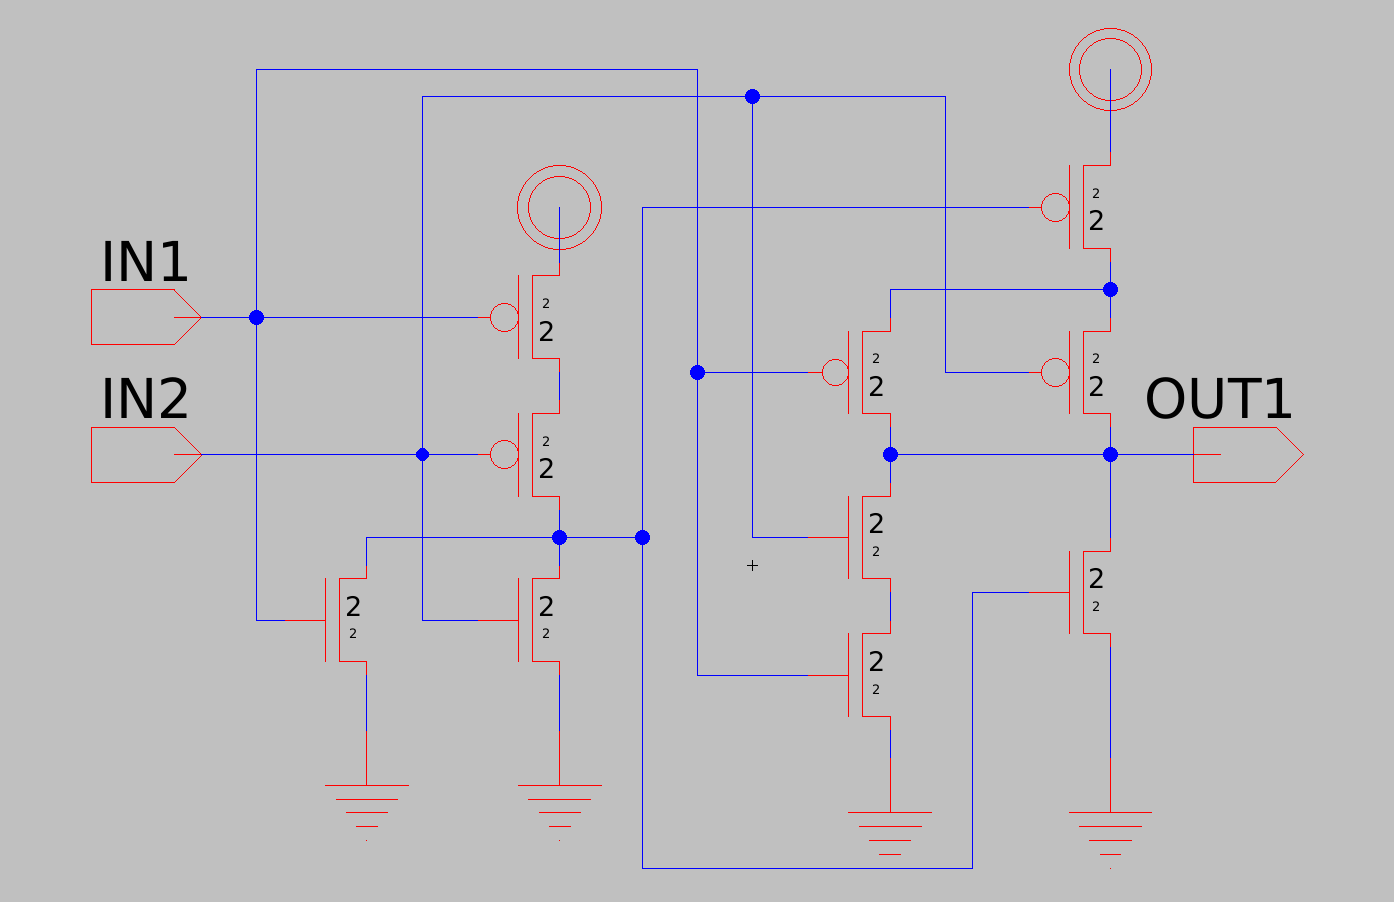
S-CPU_vlsi/xor.png
