rgalland/SNES_S-CPU_Schematics/S-CPU_kicad/42XX.kicad_sch

## KiCad design S-CPU_kicad/42XX.kicad_sch (2024-12-24, an earlier design)

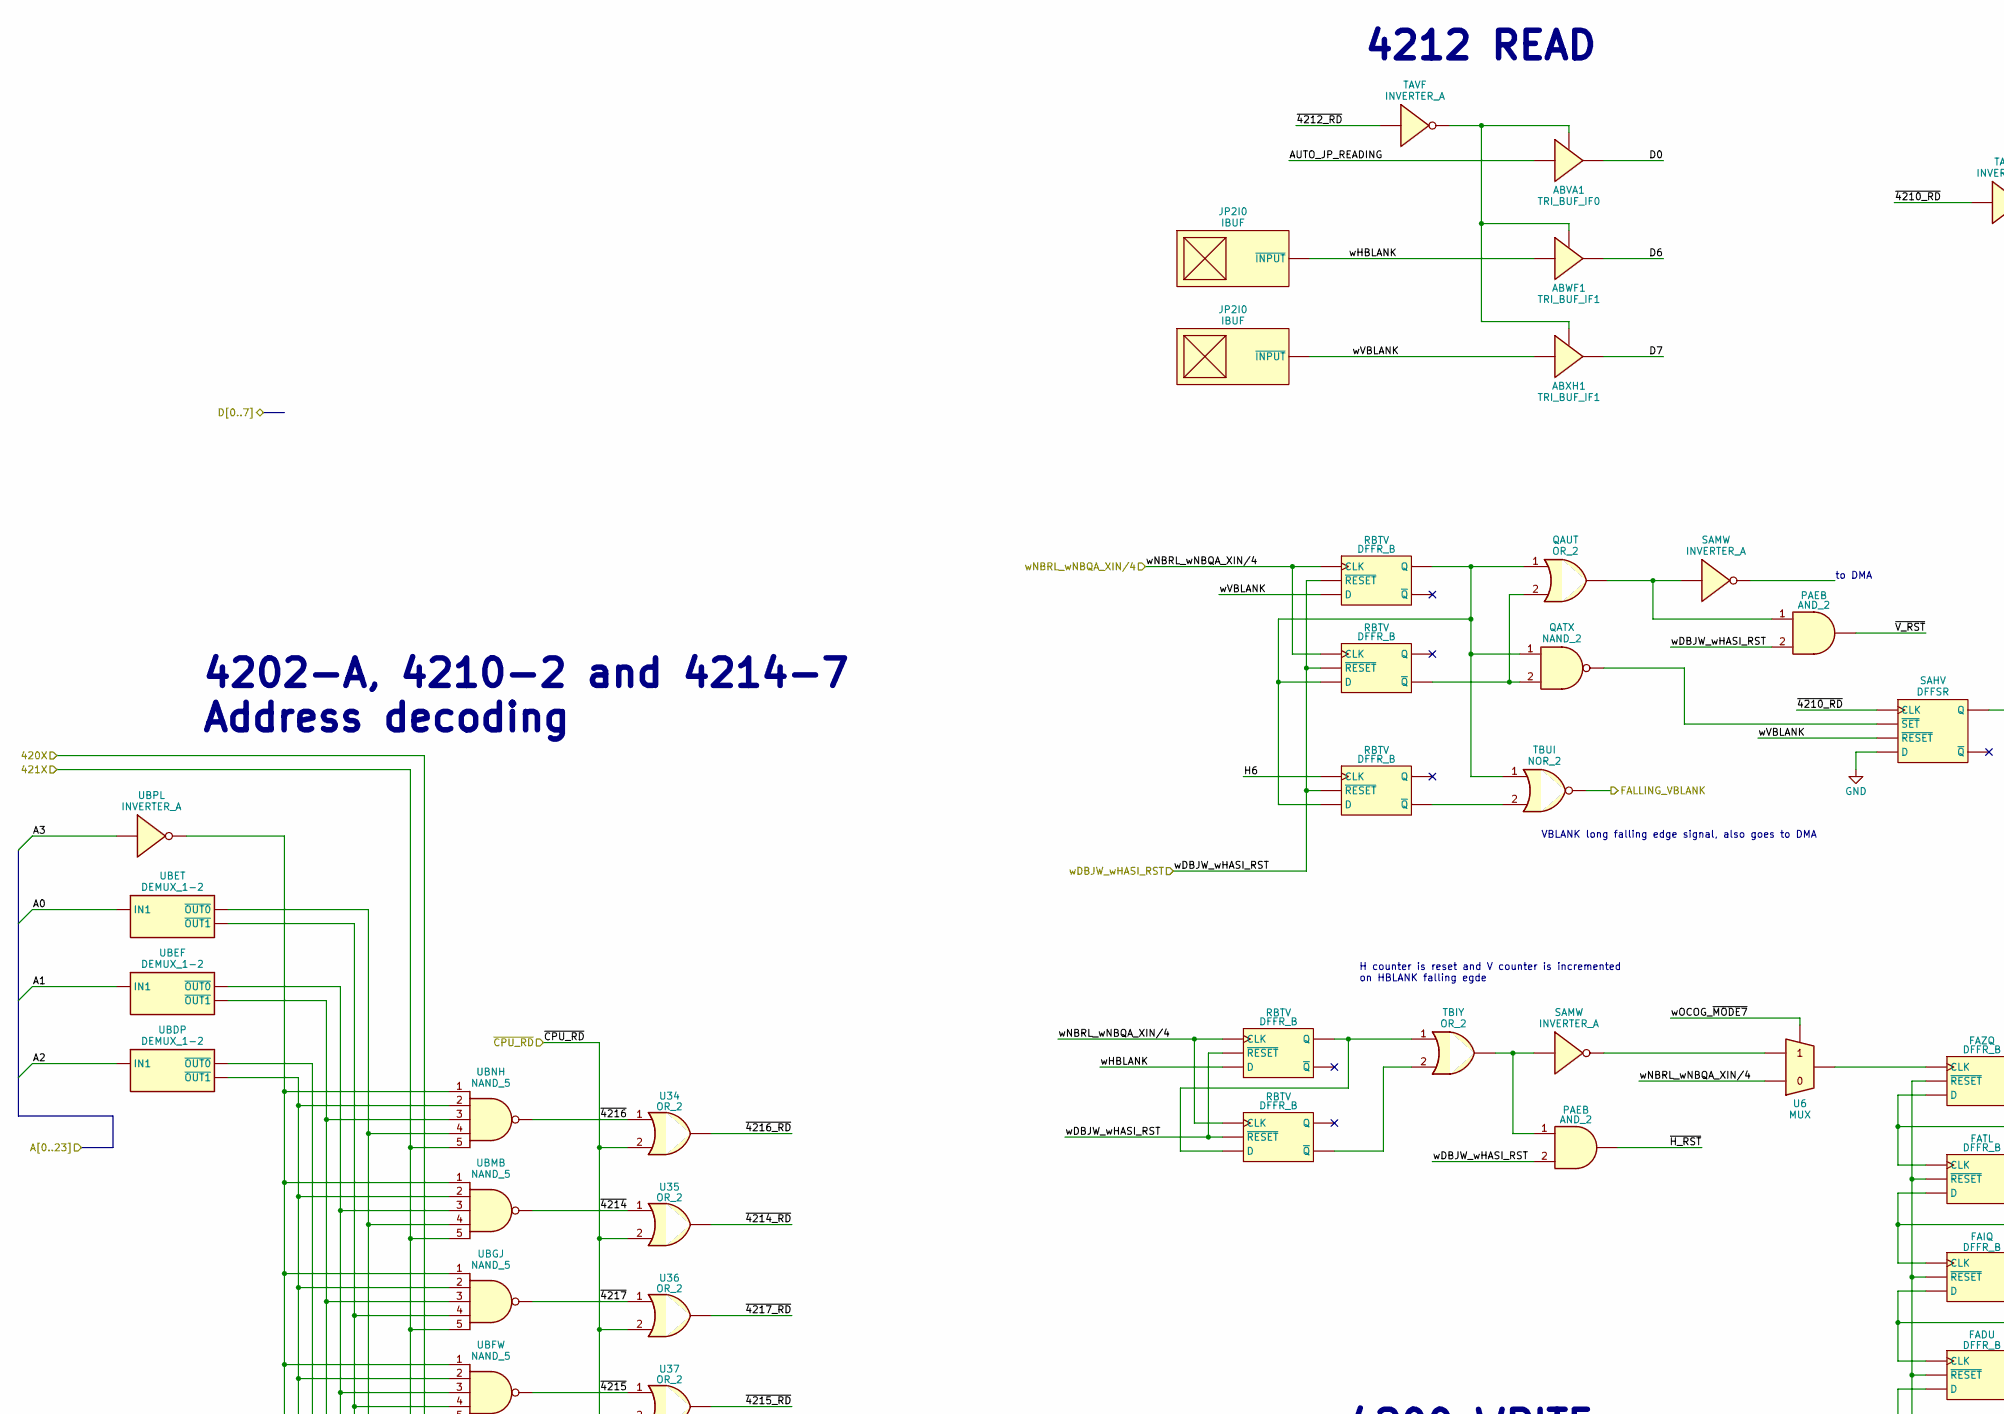
[picture p51: schematic 42XX.kicad_sch, part in row 1, column 1]

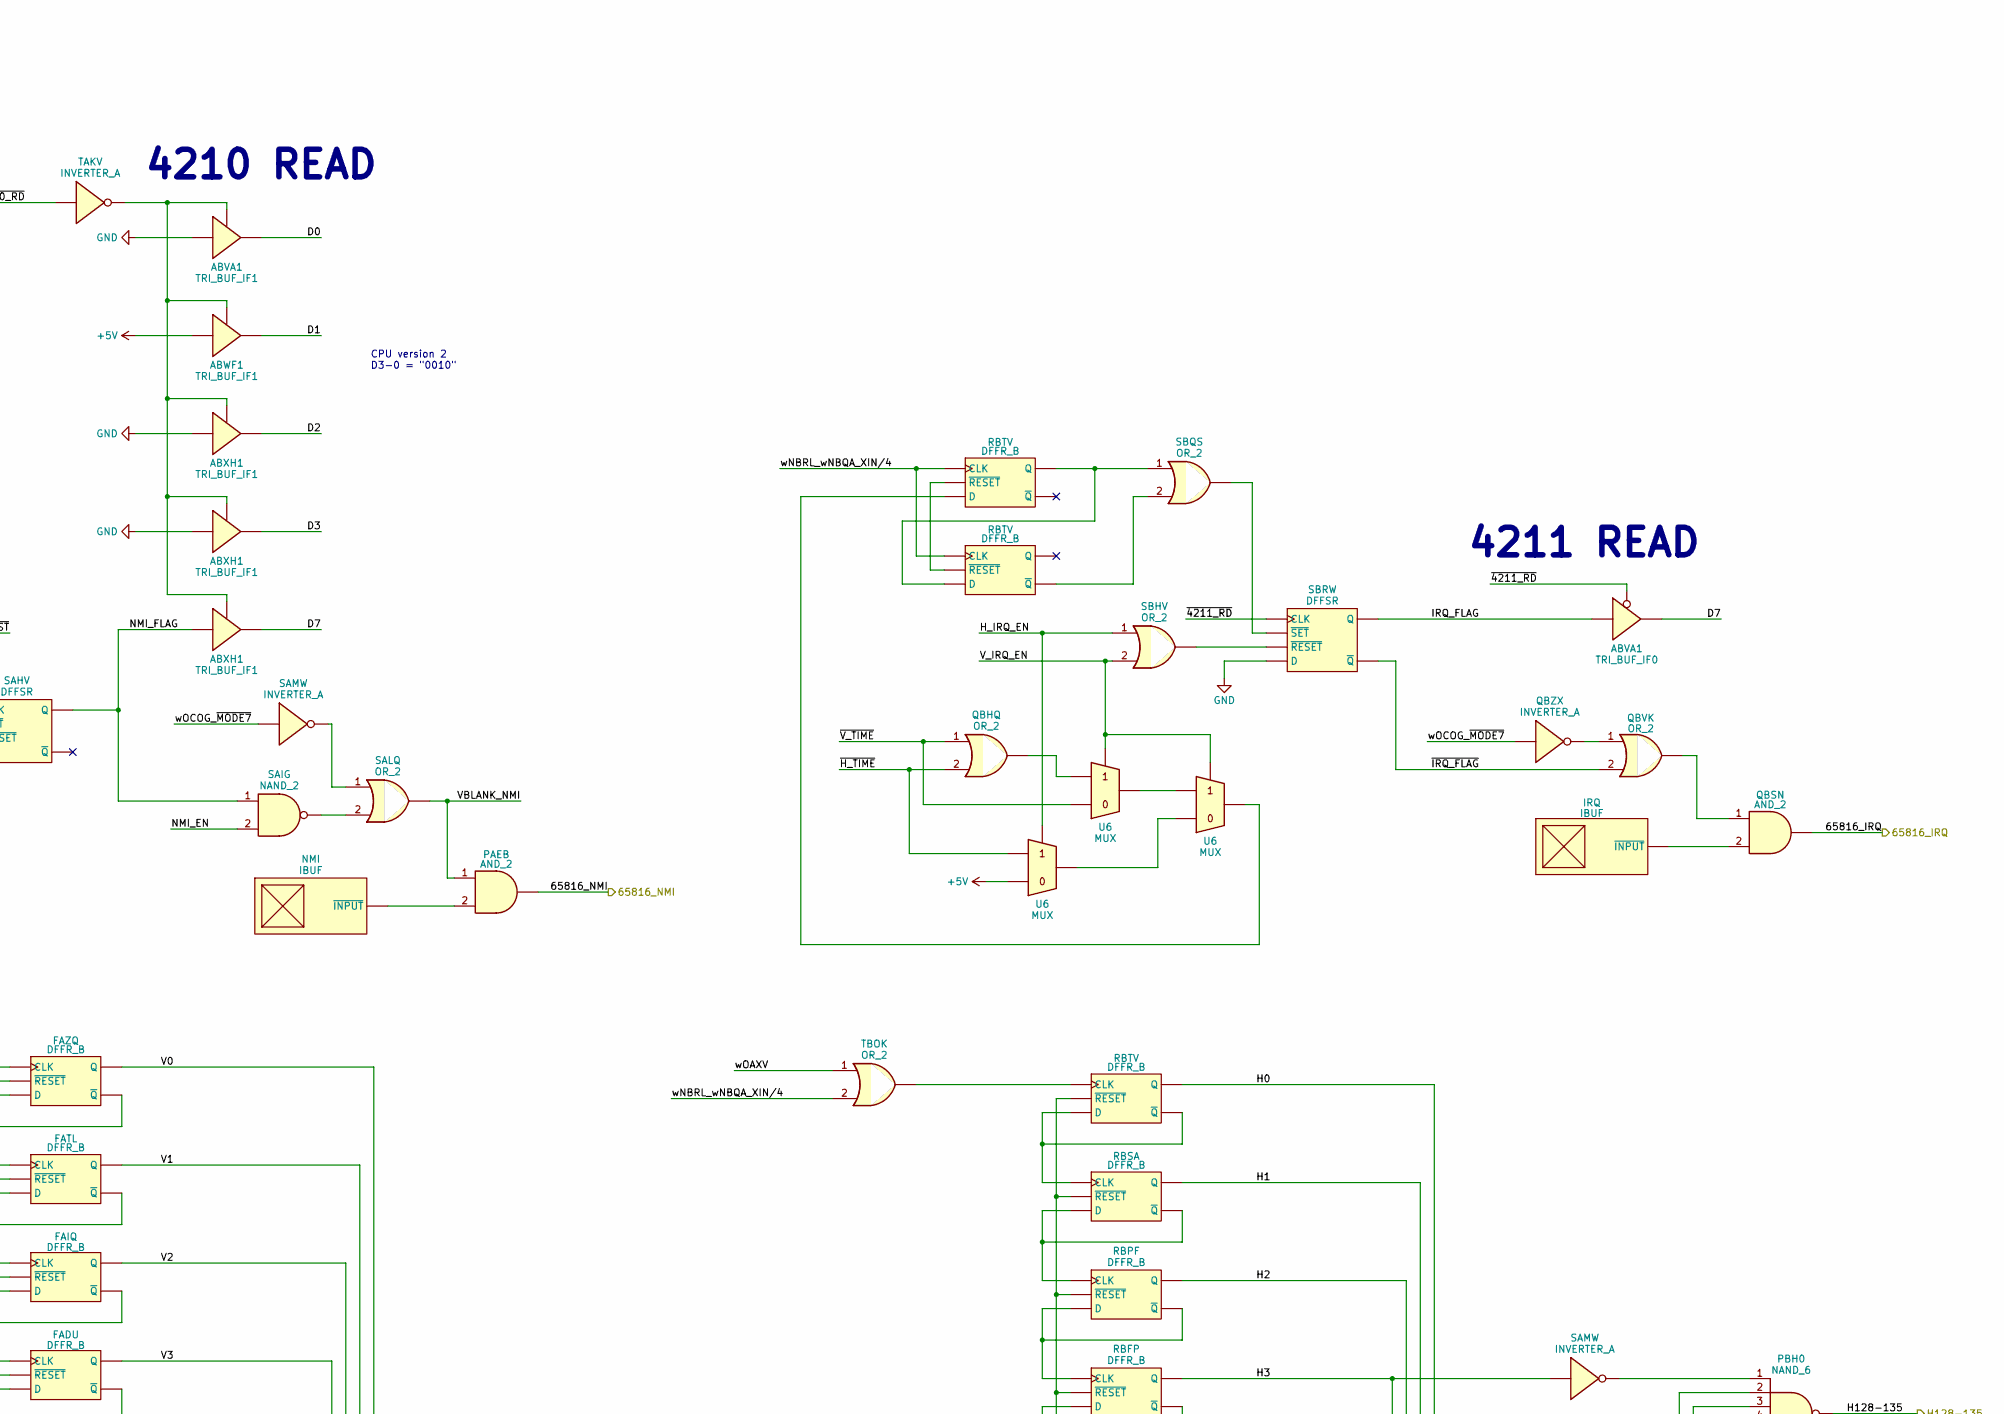
[picture p52: schematic 42XX.kicad_sch, part in row 1, column 2]

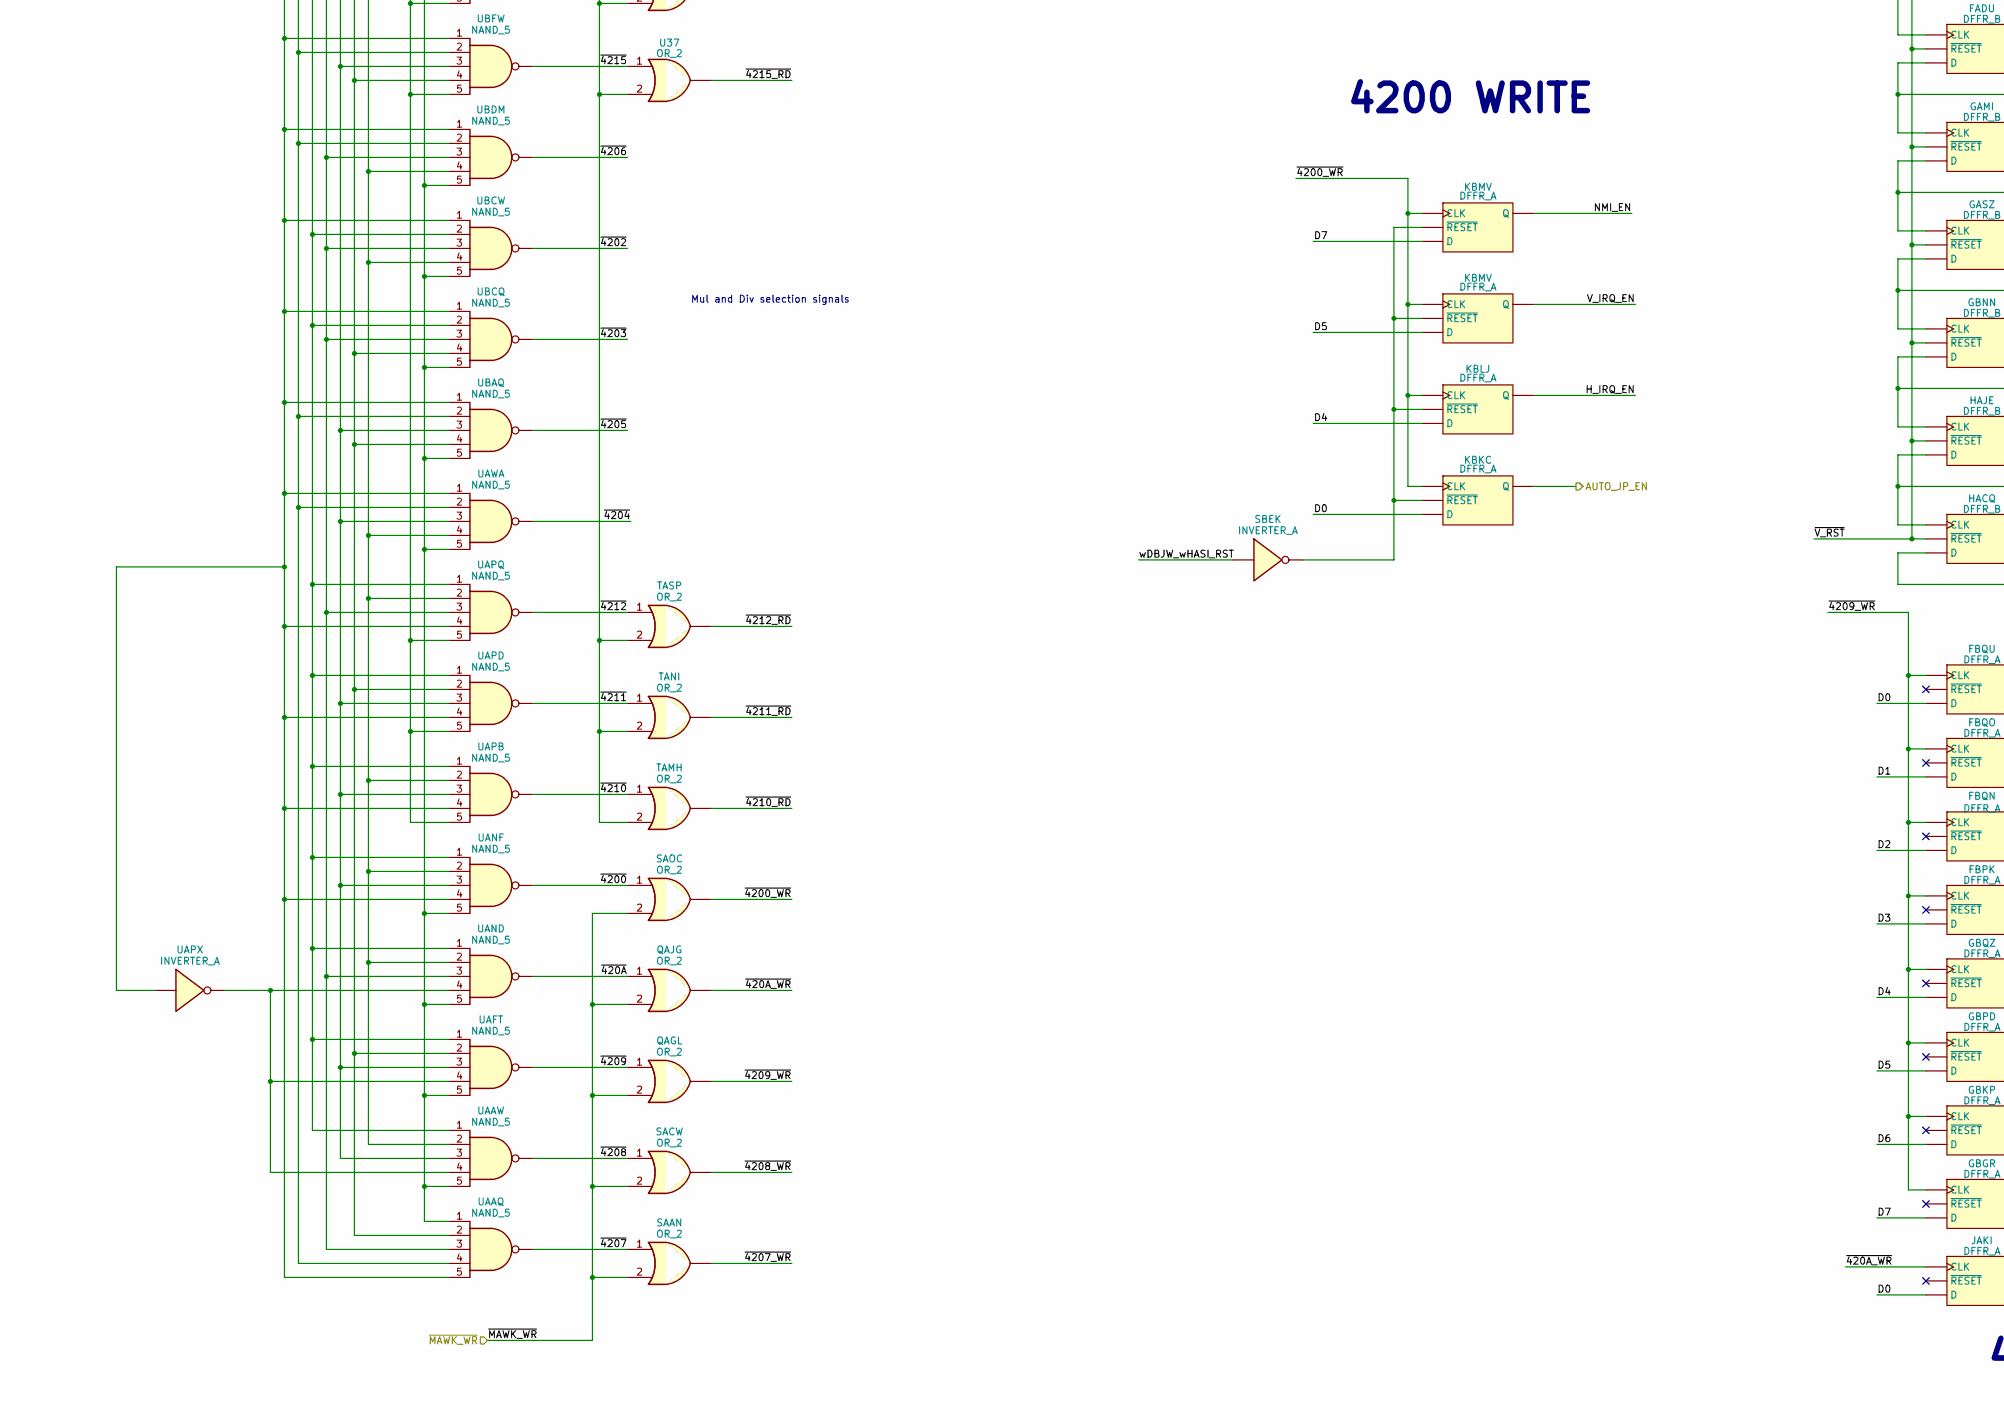
[picture p53: schematic 42XX.kicad_sch, part in row 2, column 1]

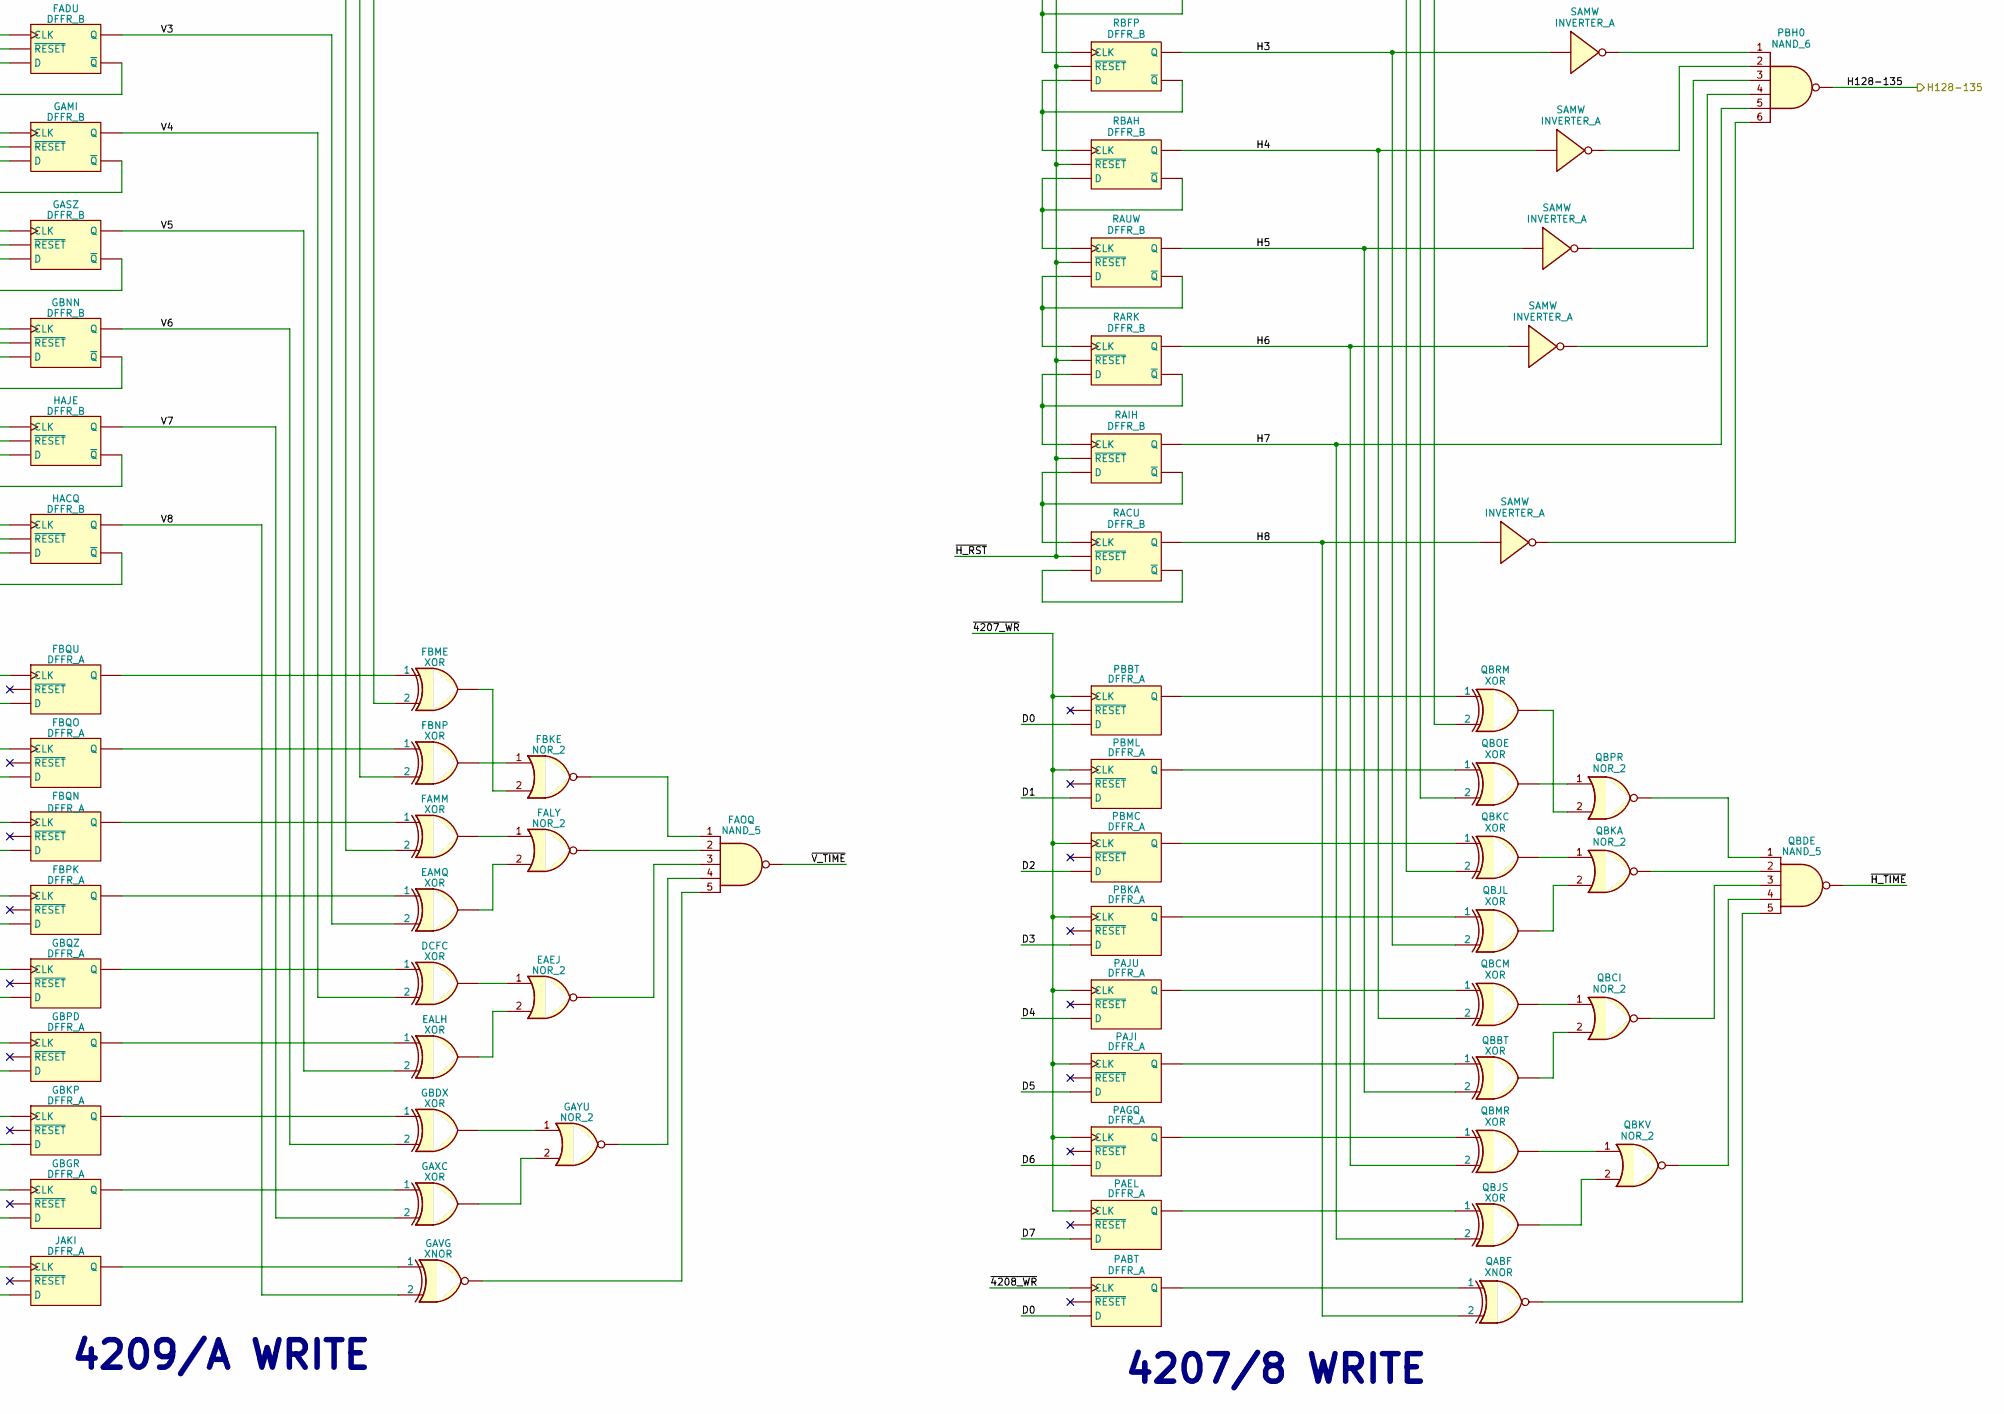
[picture p54: schematic 42XX.kicad_sch, part in row 2, column 2]

Parts:
ABVA1: TRI_BUF_IF0
ABWF1: TRI_BUF_IF1
ABXH1: TRI_BUF_IF1
DCFC: XOR
EAEJ: NOR_2
EALH: XOR
EAMQ: XOR
FADU: DFFR_B
FAIQ: DFFR_B
FALY: NOR_2
FAMM: XOR
FAOQ: NAND_5
FATL: DFFR_B
FAZQ: DFFR_B
FBKE: NOR_2
FBME: XOR
FBNP: XOR
FBPK: DFFR_A
FBQN: DFFR_A
FBQO: DFFR_A
FBQU: DFFR_A
GAMI: DFFR_B
GASZ: DFFR_B
GAVG: XNOR
GAXC: XOR
GAYU: NOR_2
GBDX: XOR
GBGR: DFFR_A
GBKP: DFFR_A
GBNN: DFFR_B
GBPD: DFFR_A
GBQZ: DFFR_A
HACQ: DFFR_B
HAJE: DFFR_B
IRQ: IBUF
JAKI: DFFR_A
JP2I0: IBUF
KBKC: DFFR_A
KBLJ: DFFR_A
KBMV: DFFR_A
NMI: IBUF
PABT: DFFR_A
PAEB: AND_2
PAEL: DFFR_A
PAGQ: DFFR_A
PAJI: DFFR_A
PAJU: DFFR_A
PBBT: DFFR_A
PBH0: NAND_6
PBKA: DFFR_A
PBMC: DFFR_A
PBML: DFFR_A
QABF: XNOR
QAGL: OR_2
QAJG: OR_2
QATX: NAND_2
QAUT: OR_2
QBBT: XOR
QBCI: NOR_2
QBCM: XOR
QBDE: NAND_5
QBHQ: OR_2
QBJL: XOR
QBJS: XOR
QBKA: NOR_2
QBKC: XOR
QBKV: NOR_2
QBMR: XOR
QBOE: XOR
QBPR: NOR_2
QBRM: XOR
QBSN: AND_2
QBVK: OR_2
QBZX: INVERTER_A
RACU: DFFR_B
RAIH: DFFR_B
RARK: DFFR_B
RAUW: DFFR_B
RBAH: DFFR_B
RBFP: DFFR_B
RBPF: DFFR_B
RBSA: DFFR_B
RBTV: DFFR_B
SAAN: OR_2
SACW: OR_2
SAHV: DFFSR
SAIG: NAND_2
SALQ: OR_2
SAMW: INVERTER_A
SAOC: OR_2
SBEK: INVERTER_A
SBHV: OR_2
SBQS: OR_2
SBRW: DFFSR
TAKV: INVERTER_A
TAMH: OR_2
TANI: OR_2
TASP: OR_2
TAVF: INVERTER_A
TBIY: OR_2
TBOK: OR_2
TBUI: NOR_2
U6: MUX
U34, U35, U36, U37: OR_2
UAAQ: NAND_5
UAAW: NAND_5
UAFT: NAND_5
UAND: NAND_5
UANF: NAND_5
UAPB: NAND_5
UAPD: NAND_5
UAPQ: NAND_5
UAPX: INVERTER_A
UAWA: NAND_5
UBAQ: NAND_5
UBCQ: NAND_5
UBCW: NAND_5
UBDM: NAND_5
UBDP: DEMUX_1-2
UBEF: DEMUX_1-2
UBET: DEMUX_1-2
UBFW: NAND_5
UBGJ: NAND_5
UBMB: NAND_5
UBNH: NAND_5
UBPL: INVERTER_A

Connections:
420X: UAAQ.1, UAAW.5, UAFT.5, UAND.5, UANF.5, UAWA.5, UBAQ.5, UBCQ.5, UBCW.5, UBDM.5
421X: UAPB.5, UAPD.5, UAPQ.5, UBFW.5, UBGJ.5, UBMB.5, UBNH.5
65816_IRQ: QBSN.3
65816_NMI: PAEB.3
+5V: ABWF1.1 (IN), ABWF1.3 (IN), U6.3
A0: UBET.
A1: UBEF.
A2: UBDP.
A3: UBPL.1
AUTO_JP_EN: KBKC.6 (Q)
AUTO_JP_READING: ABVA1.1 (IN), ABVA1.3 (IN)
D0: ABVA1.4, FBQU.2 (D), JAKI.2 (D), KBKC.2 (D), PABT.2 (D), PBBT.2 (D)
D1: ABWF1.4, FBQO.2 (D), PBML.2 (D)
D2: ABXH1.4, FBQN.2 (D), PBMC.2 (D)
D3: ABXH1.4, FBPK.2 (D), PBKA.2 (D)
D4: GBQZ.2 (D), KBLJ.2 (D), PAJU.2 (D)
D5: GBPD.2 (D), KBMV.2 (D), PAJI.2 (D)
D6: ABWF1.4, GBKP.2 (D), PAGQ.2 (D)
D7: ABVA1.4, ABXH1.4, GBGR.2 (D), KBMV.2 (D), PAEL.2 (D)
FALLING_VBLANK: TBUI.3
GND: ABVA1.1 (IN), ABVA1.3 (IN), ABXH1.1 (IN), ABXH1.3 (IN), SAHV.2 (D), SBRW.2 (D)
H0: QBRM.3 (2), RBTV.7 (Q)
H1: QBOE.3 (2), RBSA.7 (Q)
H2: QBKC.3 (2), RBPF.7 (Q)
H3: QBJL.3 (2), RBFP.7 (Q), SAMW.1
H4: QBCM.3 (2), RBAH.7 (Q), SAMW.1
H5: QBBT.3 (2), RAUW.7 (Q), SAMW.1
H6: QBMR.3 (2), RARK.7 (Q), RBTV.3 (CLK), RBTV.4 (~CLK), SAMW.1
H7: PBH0.5, QBJS.3 (2), RAIH.7 (Q)
H8: QABF.3 (2), RACU.7 (Q), SAMW.1
H128-135: PBH0.7
H_IRQ_EN: KBLJ.6 (Q), SBHV.1, U6.1
IRQ_FLAG: ABVA1.1 (IN), ABVA1.3 (IN), SBRW.5 (Q)
NMI_EN: KBMV.6 (Q), SAIG.2
NMI_FLAG: ABXH1.1 (IN), ABXH1.3 (IN), SAHV.5 (Q), SAIG.1
unnamed: ABVA1.2 (~ENA), ABWF1.2 (~ENA), ABXH1.2 (~ENA), TAKV.2, TAVF.2
unnamed: DCFC.1, EAEJ.1
unnamed: DCFC.2 (1), GBQZ.6 (Q)
unnamed: EAEJ.2, EALH.1
unnamed: EAEJ.3, FAOQ.3
unnamed: EALH.2 (1), GBPD.6 (Q)
unnamed: EAMQ.1, FALY.2
unnamed: EAMQ.2 (1), FBPK.6 (Q)
unnamed: FADU.2 (D), FADU.6 (~Q), GAMI.3 (CLK), GAMI.4 (~CLK)
unnamed: FADU.3 (CLK), FADU.4 (~CLK), FAIQ.2 (D), FAIQ.6 (~Q)
unnamed: FAIQ.3 (CLK), FAIQ.4 (~CLK), FATL.2 (D), FATL.6 (~Q)
unnamed: FALY.1, FAMM.1
unnamed: FALY.3, FAOQ.2
unnamed: FAMM.2 (1), FBQN.6 (Q)
unnamed: FAOQ.1, FBKE.3
unnamed: FAOQ.4, GAYU.3
unnamed: FAOQ.5, GAVG.1
unnamed: FATL.3 (CLK), FATL.4 (~CLK), FAZQ.2 (D), FAZQ.6 (~Q)
unnamed: FAZQ.3 (CLK), FAZQ.4 (~CLK), U6.4
unnamed: FBKE.1, FBNP.1
unnamed: FBKE.2, FBME.1
unnamed: FBME.2 (1), FBQU.6 (Q)
unnamed: FBNP.2 (1), FBQO.6 (Q)
unnamed: FBPK.1 (~RESET), FBPK.5 (~RESET)
unnamed: FBQN.1 (~RESET), FBQN.5 (~RESET)
unnamed: FBQO.1 (~RESET), FBQO.5 (~RESET)
unnamed: FBQU.1 (~RESET), FBQU.5 (~RESET)
unnamed: GAMI.2 (D), GAMI.6 (~Q), GASZ.3 (CLK), GASZ.4 (~CLK)
unnamed: GASZ.2 (D), GASZ.6 (~Q), GBNN.3 (CLK), GBNN.4 (~CLK)
unnamed: GAVG.2 (1), JAKI.6 (Q)
unnamed: GAXC.1, GAYU.2
unnamed: GAXC.2 (1), GBGR.6 (Q)
unnamed: GAYU.1, GBDX.1
unnamed: GBDX.2 (1), GBKP.6 (Q)
unnamed: GBGR.1 (~RESET), GBGR.5 (~RESET)
unnamed: GBKP.1 (~RESET), GBKP.5 (~RESET)
unnamed: GBNN.2 (D), GBNN.6 (~Q), HAJE.3 (CLK), HAJE.4 (~CLK)
unnamed: GBPD.1 (~RESET), GBPD.5 (~RESET)
unnamed: GBQZ.1 (~RESET), GBQZ.5 (~RESET)
unnamed: HACQ.2 (D), HACQ.6 (~Q)
unnamed: HACQ.3 (CLK), HACQ.4 (~CLK), HAJE.2 (D), HAJE.6 (~Q)
unnamed: IRQ.1, QBSN.2
unnamed: JAKI.1 (~RESET), JAKI.5 (~RESET)
unnamed: KBKC.1 (~RESET), KBKC.5 (~RESET), KBLJ.1 (~RESET), KBLJ.5 (~RESET), KBMV.1 (~RESET), KBMV.5 (~RESET), SBEK.2
unnamed: NMI.1, PAEB.2
unnamed: PABT.1 (~RESET), PABT.5 (~RESET)
unnamed: PABT.6 (Q), QABF.2 (1)
unnamed: PAEB.1, QAUT.3, SAMW.1, TBIY.3
unnamed: PAEL.1 (~RESET), PAEL.5 (~RESET)
unnamed: PAEL.6 (Q), QBJS.2 (1)
unnamed: PAGQ.1 (~RESET), PAGQ.5 (~RESET)
unnamed: PAGQ.6 (Q), QBMR.2 (1)
unnamed: PAJI.1 (~RESET), PAJI.5 (~RESET)
unnamed: PAJI.6 (Q), QBBT.2 (1)
unnamed: PAJU.1 (~RESET), PAJU.5 (~RESET)
unnamed: PAJU.6 (Q), QBCM.2 (1)
unnamed: PBBT.1 (~RESET), PBBT.5 (~RESET)
unnamed: PBBT.6 (Q), QBRM.2 (1)
unnamed: PBH0.1, SAMW.2
unnamed: PBH0.2, SAMW.2
unnamed: PBH0.3, SAMW.2
unnamed: PBH0.4, SAMW.2
unnamed: PBH0.6, SAMW.2
unnamed: PBKA.1 (~RESET), PBKA.5 (~RESET)
unnamed: PBKA.6 (Q), QBJL.2 (1)
unnamed: PBMC.1 (~RESET), PBMC.5 (~RESET)
unnamed: PBMC.6 (Q), QBKC.2 (1)
unnamed: PBML.1 (~RESET), PBML.5 (~RESET)
unnamed: PBML.6 (Q), QBOE.2 (1)
unnamed: QABF.1, QBDE.5
unnamed: QATX.1, QAUT.1, RBTV.2 (D), RBTV.7 (Q), TBUI.1
unnamed: QATX.2, QAUT.2, RBTV.6 (~Q)
unnamed: QATX.3, SAHV.1 (~SET), SAHV.3 (~SET)
unnamed: QBBT.1, QBCI.2
unnamed: QBCI.1, QBCM.1
unnamed: QBCI.3, QBDE.3
unnamed: QBDE.1, QBPR.3
unnamed: QBDE.2, QBKA.3
unnamed: QBDE.4, QBKV.3
unnamed: QBHQ.3, U6.2
unnamed: QBJL.1, QBKA.2
unnamed: QBJS.1, QBKV.2
unnamed: QBKA.1, QBKC.1
unnamed: QBKV.1, QBMR.1
unnamed: QBOE.1, QBPR.1
unnamed: QBPR.2, QBRM.1
unnamed: QBSN.1, QBVK.3
unnamed: QBVK.1, QBZX.2
unnamed: RACU.2 (D), RACU.6 (~Q)
unnamed: RACU.3 (CLK), RACU.4 (~CLK), RAIH.2 (D), RAIH.6 (~Q)
unnamed: RAIH.3 (CLK), RAIH.4 (~CLK), RARK.2 (D), RARK.6 (~Q)
unnamed: RARK.3 (CLK), RARK.4 (~CLK), RAUW.2 (D), RAUW.6 (~Q)
unnamed: RAUW.3 (CLK), RAUW.4 (~CLK), RBAH.2 (D), RBAH.6 (~Q)
unnamed: RBAH.3 (CLK), RBAH.4 (~CLK), RBFP.2 (D), RBFP.6 (~Q)
unnamed: RBFP.3 (CLK), RBFP.4 (~CLK), RBPF.2 (D), RBPF.6 (~Q)
unnamed: RBPF.3 (CLK), RBPF.4 (~CLK), RBSA.2 (D), RBSA.6 (~Q)
unnamed: RBSA.3 (CLK), RBSA.4 (~CLK), RBTV.2 (D), RBTV.6 (~Q)
unnamed: RBTV.1 (~RESET), RBTV.5 (~RESET)
unnamed: RBTV.2 (D), RBTV.7 (Q), SBQS.1, TBIY.1, U6.4
unnamed: RBTV.3 (CLK), RBTV.4 (~CLK), TBOK.3
unnamed: RBTV.6 (~Q), SBQS.2, TBIY.2, TBUI.2
unnamed: SAIG.3, SALQ.2
unnamed: SALQ.1, SAMW.2
unnamed: SAMW.2, U6.2
unnamed: SBHV.3, SBRW.6 (~RESET)
unnamed: SBQS.3, SBRW.1 (~SET), SBRW.3 (~SET)
unnamed: U6.2, U6.4
unnamed: U6.3, U6.4
unnamed: UAAQ.2, UAFT.2, UAPD.2, UBAQ.4, UBCQ.4, UBET., UBFW.4, UBGJ.4
unnamed: UAAQ.3, UAND.3, UAPQ.3, UBCQ.3, UBCW.3, UBDM.3, UBEF., UBGJ.3, UBNH.3
unnamed: UAAQ.4, UAWA.2, UBAQ.2, UBDM.2, UBDP., UBFW.2, UBGJ.2, UBMB.2, UBNH.2
unnamed: UAAQ.5, UANF.4, UAPB.4, UAPD.4, UAPQ.4, UAPX.1, UAWA.1, UBAQ.1, UBCQ.1, UBCW.1, UBDM.1, UBFW.1, UBGJ.1, UBMB.1, UBNH.1, UBPL.2
unnamed: UAAW.1, UAFT.1, UAND.1, UANF.1, UAPB.1, UAPD.1, UAPQ.1, UBCQ.2, UBCW.2, UBDP.
unnamed: UAAW.2, UAND.2, UANF.2, UAPB.2, UAPQ.2, UAWA.4, UBCW.4, UBDM.4, UBET., UBMB.4, UBNH.4
unnamed: UAAW.3, UAFT.3, UANF.3, UAPB.3, UAPD.3, UAWA.3, UBAQ.3, UBEF., UBFW.3, UBMB.3
unnamed: UAAW.4, UAFT.4, UAND.4, UAPX.2
V0: FAZQ.7 (Q), FBME.3 (2)
V1: FATL.7 (Q), FBNP.3 (2)
V2: FAIQ.7 (Q), FAMM.3 (2)
V3: EAMQ.3 (2), FADU.7 (Q)
V4: DCFC.3 (2), GAMI.7 (Q)
V5: EALH.3 (2), GASZ.7 (Q)
V6: GBDX.3 (2), GBNN.7 (Q)
V7: GAXC.3 (2), HAJE.7 (Q)
V8: GAVG.3 (2), HACQ.7 (Q)
VBLANK_NMI: PAEB.1, SALQ.3
V_IRQ_EN: KBMV.6 (Q), SBHV.2, U6.1
wDBJW_wHASI_RST: PAEB.2, RBTV.1 (~RESET), RBTV.5 (~RESET), SBEK.1
wHBLANK: ABWF1.1 (IN), ABWF1.3 (IN), JP2I0.1, RBTV.2 (D)
wNBRL_wNBQA_XIN/4: RBTV.3 (CLK), RBTV.4 (~CLK), TBOK.2, U6.3
wOAXV: TBOK.1
wOCOG_~MODE7: QBZX.1, SAMW.1, U6.1
wVBLANK: ABXH1.1 (IN), ABXH1.3 (IN), JP2I0.1, RBTV.2 (D), SAHV.6 (~RESET)
~420A_WR: JAKI.3 (CLK), JAKI.4 (~CLK), QAJG.3
~420A: QAJG.1, UAND.6
~4200_WR: KBKC.3 (CLK), KBKC.4 (~CLK), KBLJ.3 (CLK), KBLJ.4 (~CLK), KBMV.3 (CLK), KBMV.4 (~CLK), SAOC.3
~4200: SAOC.1, UANF.6
~4202: UBCW.6
~4203: UBCQ.6
~4204: UAWA.6
~4205: UBAQ.6
~4206: UBDM.6
~4207_WR: PAEL.3 (CLK), PAEL.4 (~CLK), PAGQ.3 (CLK), PAGQ.4 (~CLK), PAJI.3 (CLK), PAJI.4 (~CLK), PAJU.3 (CLK), PAJU.4 (~CLK), PBBT.3 (CLK), PBBT.4 (~CLK), PBKA.3 (CLK), PBKA.4 (~CLK), PBMC.3 (CLK), PBMC.4 (~CLK), PBML.3 (CLK), PBML.4 (~CLK), SAAN.3
~4207: SAAN.1, UAAQ.6
~4208_WR: PABT.3 (CLK), PABT.4 (~CLK), SACW.3
~4208: SACW.1, UAAW.6
~4209_WR: FBPK.3 (CLK), FBPK.4 (~CLK), FBQN.3 (CLK), FBQN.4 (~CLK), FBQO.3 (CLK), FBQO.4 (~CLK), FBQU.3 (CLK), FBQU.4 (~CLK), GBGR.3 (CLK), GBGR.4 (~CLK), GBKP.3 (CLK), GBKP.4 (~CLK), GBPD.3 (CLK), GBPD.4 (~CLK), GBQZ.3 (CLK), GBQZ.4 (~CLK), QAGL.3
~4209: QAGL.1, UAFT.6
~4210_RD: SAHV.7 (CLK), TAKV.1, TAMH.3
~4210: TAMH.1, UAPB.6
~4211_RD: ABVA1.2 (~ENA), SBRW.7 (CLK), TANI.3
~4211: TANI.1, UAPD.6
~4212_RD: TASP.3, TAVF.1
~4212: TASP.1, UAPQ.6
~4214_RD: U35.3
~4214: U35.1, UBMB.6
~4215_RD: U37.3
~4215: U37.1, UBFW.6
~4216_RD: U34.3
~4216: U34.1, UBNH.6
~4217_RD: U36.3
~4217: U36.1, UBGJ.6
~CPU_RD: TAMH.2, TANI.2, TASP.2, U34.2, U35.2, U36.2, U37.2
~H_RST: PAEB.3, RACU.1 (~RESET), RACU.5 (~RESET), RAIH.1 (~RESET), RAIH.5 (~RESET), RARK.1 (~RESET), RARK.5 (~RESET), RAUW.1 (~RESET), RAUW.5 (~RESET), RBAH.1 (~RESET), RBAH.5 (~RESET), RBFP.1 (~RESET), RBFP.5 (~RESET), RBPF.1 (~RESET), RBPF.5 (~RESET), RBSA.1 (~RESET), RBSA.5 (~RESET), RBTV.1 (~RESET), RBTV.5 (~RESET)
~H_TIME: QBDE.6, QBHQ.2, U6.2
~IRQ_FLAG: QBVK.2, SBRW.4 (~Q)
~MAWK_WR: QAGL.2, QAJG.2, SAAN.2, SACW.2, SAOC.2
~V_RST: FADU.1 (~RESET), FADU.5 (~RESET), FAIQ.1 (~RESET), FAIQ.5 (~RESET), FATL.1 (~RESET), FATL.5 (~RESET), FAZQ.1 (~RESET), FAZQ.5 (~RESET), GAMI.1 (~RESET), GAMI.5 (~RESET), GASZ.1 (~RESET), GASZ.5 (~RESET), GBNN.1 (~RESET), GBNN.5 (~RESET), HACQ.1 (~RESET), HACQ.5 (~RESET), HAJE.1 (~RESET), HAJE.5 (~RESET), PAEB.3
~V_TIME: FAOQ.6, QBHQ.1, U6.3

Notes on the sheet:
4209/A WRITE
CPU version 2 D3-0 = "0010"
4211 READ
Mul and Div selection signals
H counter is reset and V counter is incremented on HBLANK falling egde
4212 READ
VBLANK long falling edge signal, also goes to DMA
4207/8 WRITE
4202-A, 4210-2 and 4214-7 Address decoding
to DMA
4200 WRITE
4210 READ
