rgalland/SNES_S-CPU_Schematics/S-CPU_kicad/65c816.kicad_sch

## KiCad design S-CPU_kicad/65c816.kicad_sch (2024-12-24, an earlier design)

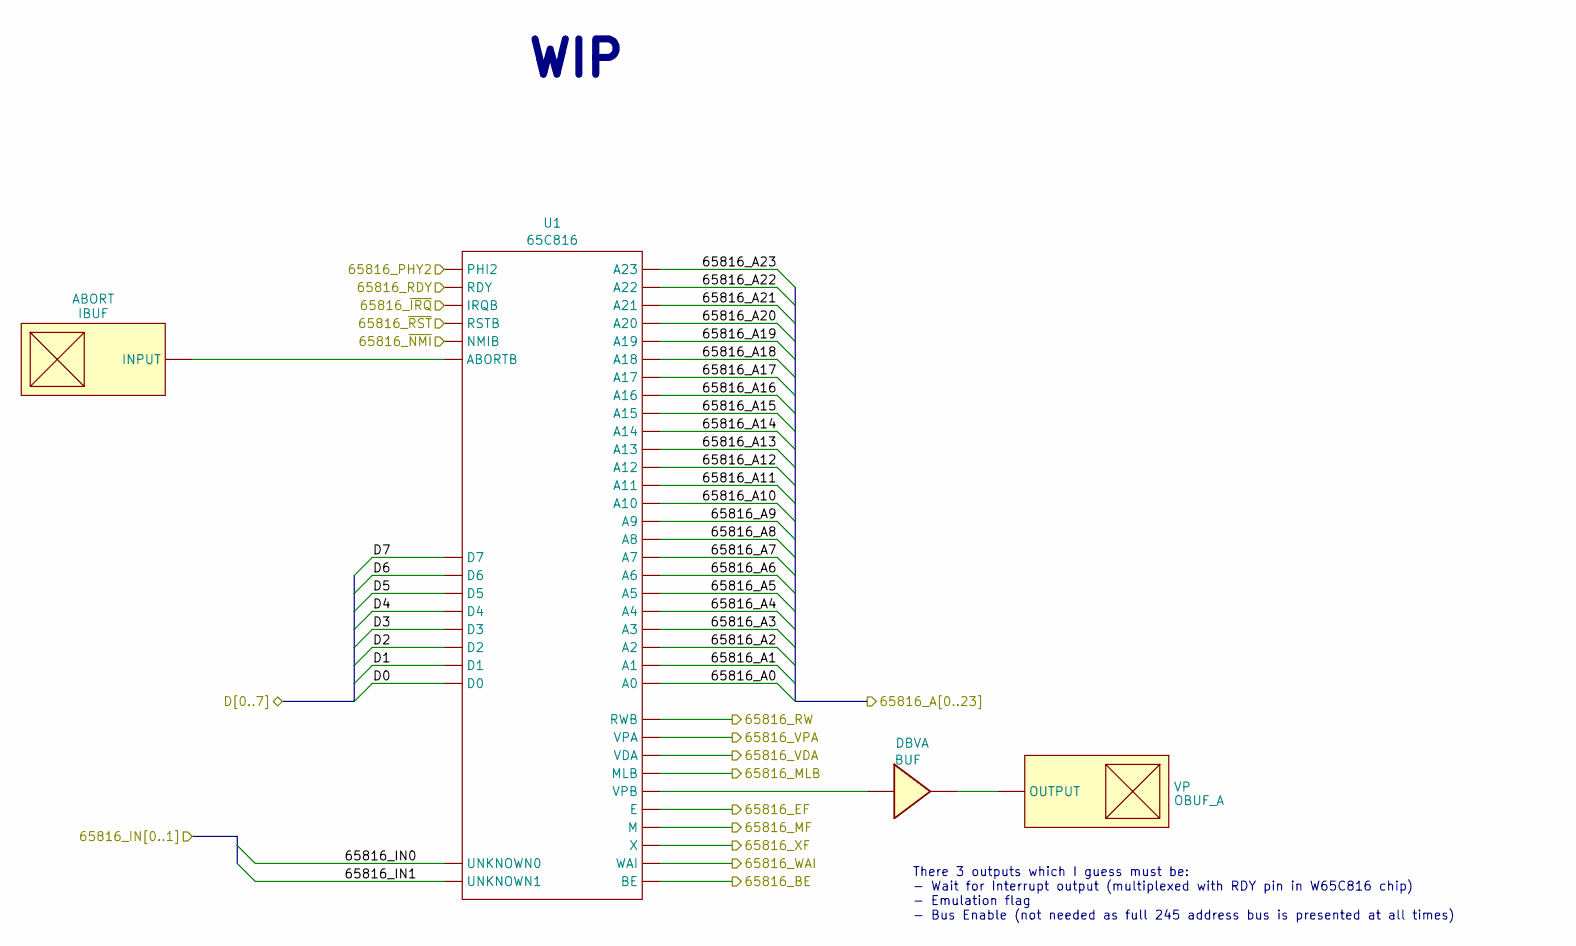
[picture p55: schematic 65c816.kicad_sch]

Parts:
ABORT: IBUF
DBVA: BUF
U1: 65C816
VP: OBUF_A

Connections:
65816_A0: U1.
65816_A1: U1.
65816_A2: U1.
65816_A3: U1.
65816_A4: U1.
65816_A5: U1.
65816_A6: U1.
65816_A7: U1.
65816_A8: U1.
65816_A9: U1.
65816_A10: U1.
65816_A11: U1.
65816_A12: U1.
65816_A13: U1.
65816_A14: U1.
65816_A15: U1.
65816_A16: U1.
65816_A17: U1.
65816_A18: U1.
65816_A19: U1.
65816_A20: U1.
65816_A21: U1.
65816_A22: U1.
65816_A23: U1.
65816_BE: U1.
65816_EF: U1.
65816_IN0: U1.
65816_IN1: U1.
65816_MF: U1.
65816_MLB: U1.
65816_PHY2: U1.
65816_RDY: U1.
65816_RW: U1.
65816_VDA: U1.
65816_VPA: U1.
65816_WAI: U1.
65816_XF: U1.
65816_~IRQ: U1.
65816_~NMI: U1.
65816_~RST: U1.
D0: U1.
D1: U1.
D2: U1.
D3: U1.
D4: U1.
D5: U1.
D6: U1.
D7: U1.
unnamed: ABORT.1, U1.
unnamed: DBVA.1, U1.
unnamed: DBVA.2, VP.1

Notes on the sheet:
There 3 outputs which I guess must be: - Wait for Interrupt output (multiplexed with RDY pin in W65C816 chip) - Emulation flag - Bus Enable (not needed as full 245 address bus is presented at all times)
WIP
