rgalland/SNES_S-CPU_Schematics/S-CPU_kicad/DMAothers.kicad_sch

## KiCad design S-CPU_kicad/DMAothers.kicad_sch (2024-12-24, an earlier design)

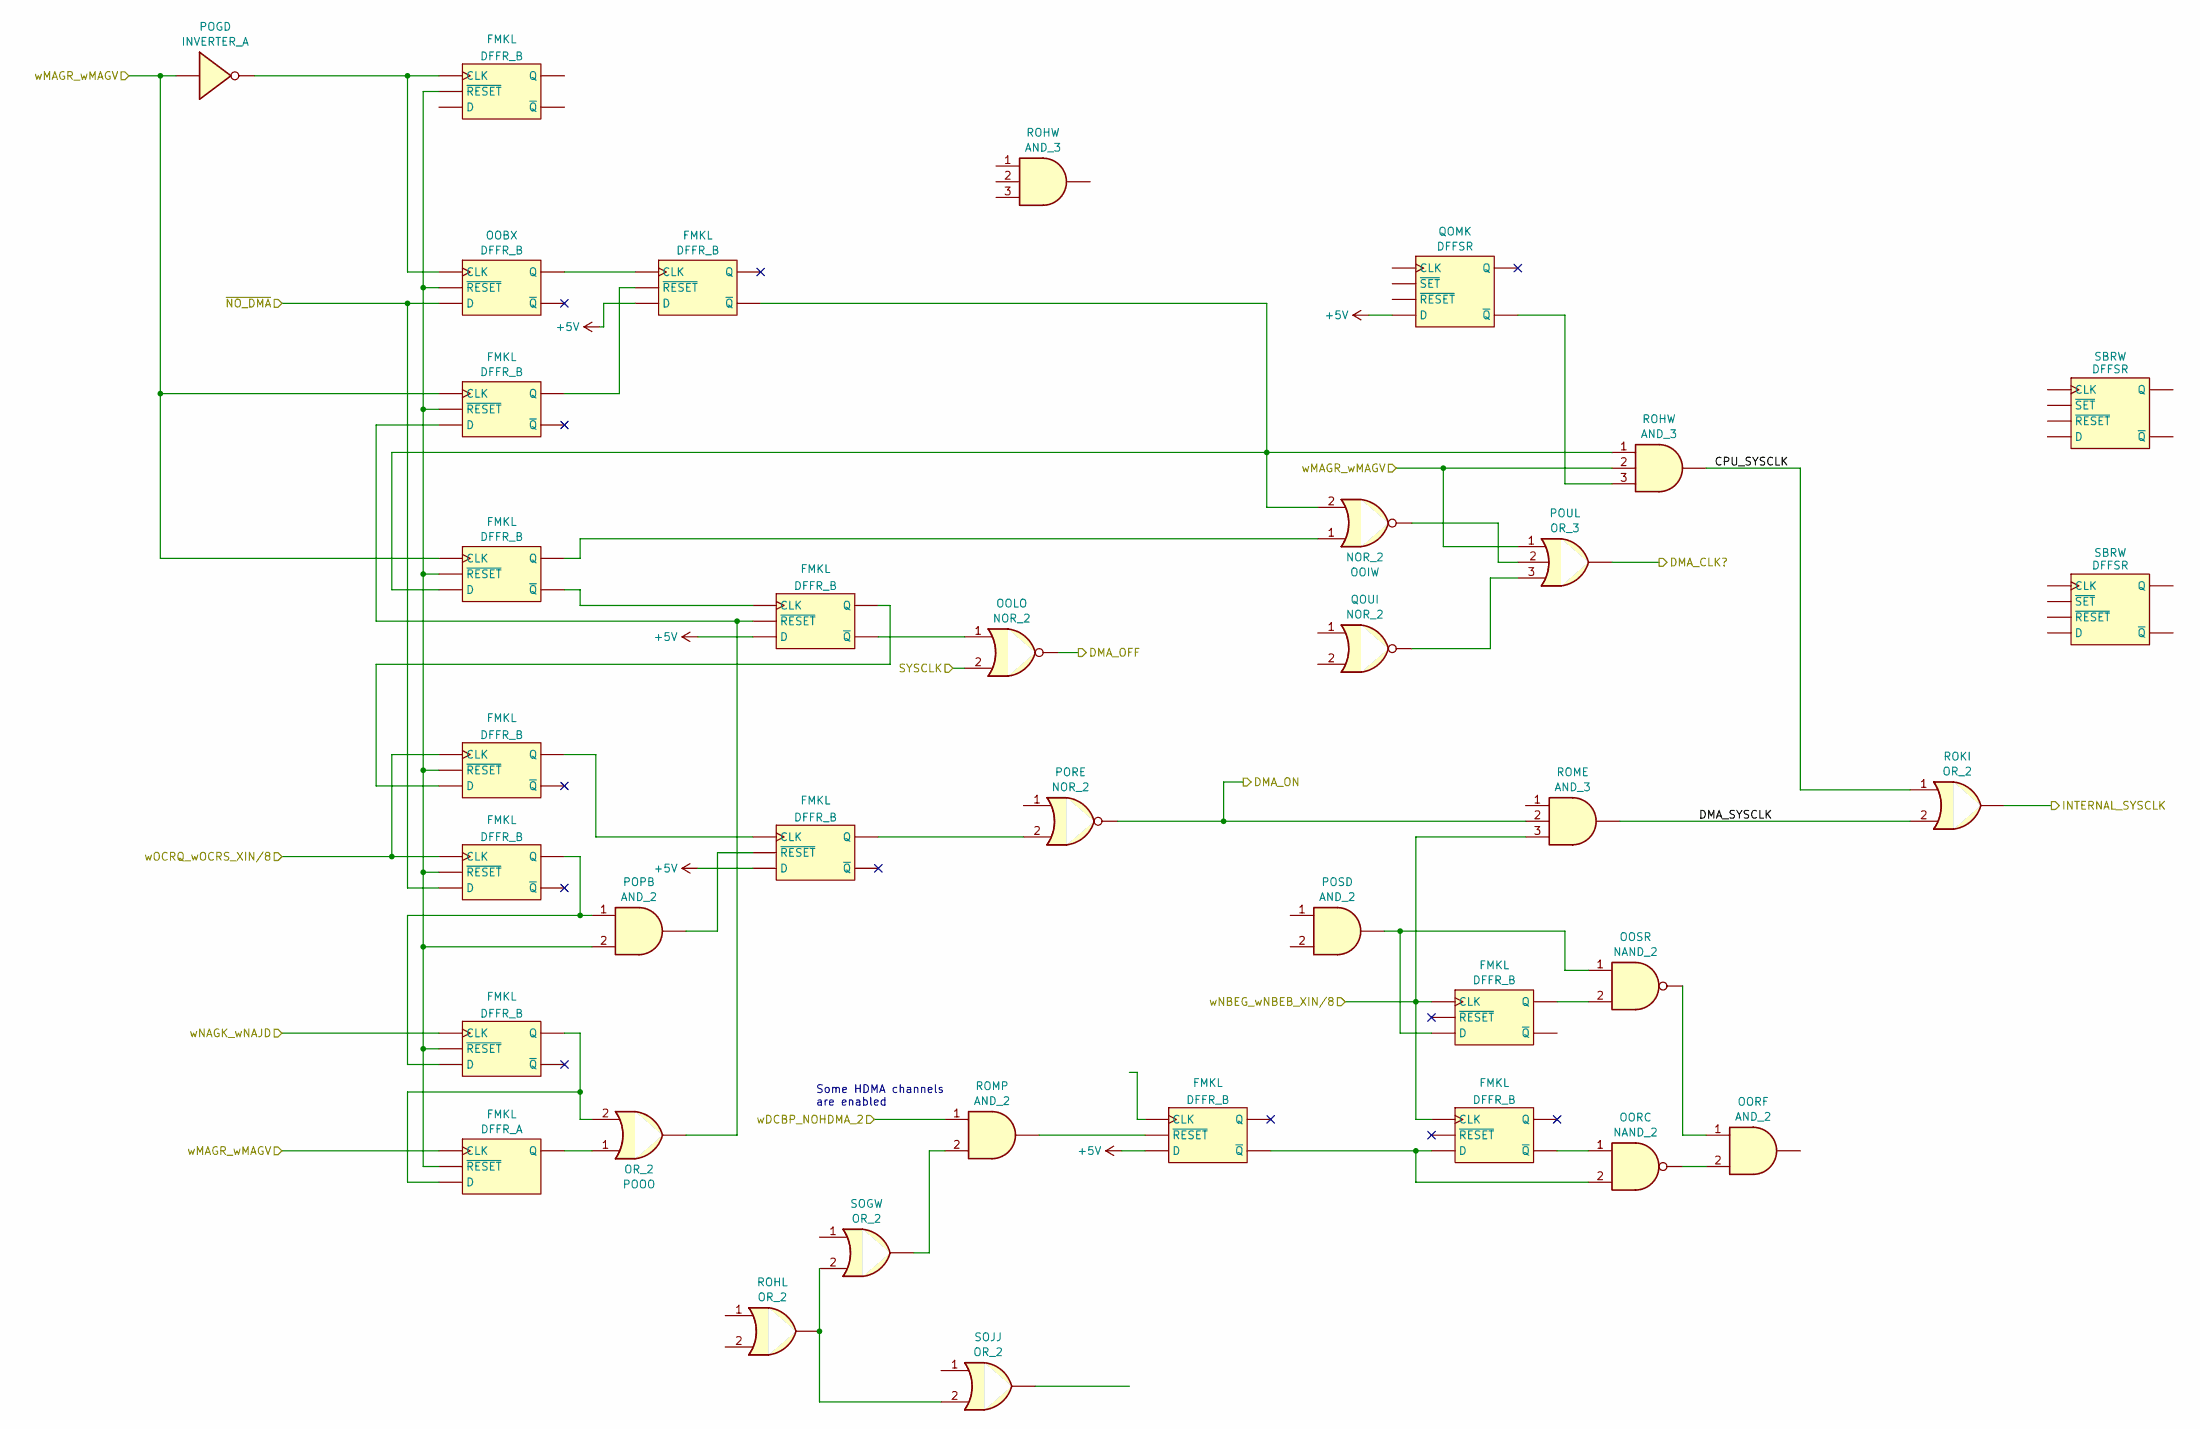
[picture p56: schematic DMAothers.kicad_sch]

Parts:
FMKL: DFFR_B
OOBX: DFFR_B
OOIW: NOR_2
OOLO: NOR_2
OORC: NAND_2
OORF: AND_2
OOSR: NAND_2
POGD: INVERTER_A
POOO: OR_2
POPB: AND_2
PORE: NOR_2
POSD: AND_2
POUL: OR_3
QOMK: DFFSR
QOUI: NOR_2
ROHL: OR_2
ROHW: AND_3
ROKI: OR_2
ROME: AND_3
ROMP: AND_2
SBRW: DFFSR
SOGW: OR_2
SOJJ: OR_2

Connections:
+5V: FMKL.2 (D), QOMK.2 (D)
CPU_SYSCLK: ROHW.4, ROKI.1
DMA_CLK?: POUL.4
DMA_OFF: OOLO.3
DMA_ON: PORE.3, ROME.2
DMA_SYSCLK: ROKI.2, ROME.4
INTERNAL_SYSCLK: ROKI.3
unnamed: FMKL.1 (~RESET), FMKL.2 (D), FMKL.5 (~RESET), FMKL.7 (Q), OOBX.1 (~RESET), OOBX.5 (~RESET), POOO.3, POPB.2, POPB.3, ROMP.3
unnamed: FMKL.2 (D), FMKL.6 (Q), FMKL.7 (Q), OOIW.2, OORC.2, OOSR.1, POOO.2, POPB.1, POSD.3, ROHW.1
unnamed: FMKL.3 (CLK), FMKL.4 (~CLK), FMKL.6 (Q), FMKL.7 (Q), OOBX.3 (CLK), OOBX.4 (~CLK), OOBX.7 (Q), POGD.2
unnamed: FMKL.6 (Q), OOLO.1, OORC.1, POOO.1
unnamed: FMKL.7 (Q), OOIW.1, OOSR.2, PORE.2
unnamed: OOIW.3, POUL.2
unnamed: OORC.3, OORF.2
unnamed: OORF.1, OOSR.3
unnamed: POUL.3, QOUI.3
unnamed: QOMK.1 (~SET), QOMK.3 (~SET)
unnamed: QOMK.4 (~Q), ROHW.3
unnamed: ROHL.3, SOGW.2, SOJJ.2
unnamed: ROMP.2, SOGW.3
unnamed: SBRW.1 (~SET), SBRW.3 (~SET)
SYSCLK: OOLO.2
wDCBP_NOHDMA_2: ROMP.1
wMAGR_wMAGV: FMKL.3 (CLK), FMKL.4 (~CLK), POGD.1, POUL.1, ROHW.2
wNAGK_wNAJD: FMKL.3 (CLK), FMKL.4 (~CLK)
wNBEG_wNBEB_XIN/8: FMKL.3 (CLK), FMKL.4 (~CLK), ROME.3
wOCRQ_wOCRS_XIN/8: FMKL.3 (CLK), FMKL.4 (~CLK)
~NO_DMA: FMKL.2 (D), OOBX.2 (D)

Notes on the sheet:
Some HDMA channels are enabled
