rgalland/SNES_S-CPU_Schematics/S-CPU_kicad/S-CPU.kicad_sch

## KiCad design S-CPU_kicad/S-CPU.kicad_sch (2024-12-24, an earlier design)

Schematic: S-CPU.kicad_sch

Parts:
AABC: BUF
AABZ: BUF
AAFD: OR_2
AAHT: AND_2
AAJX: NAND_4
AAKO: AND_2
AALV: NAND_4
AAMX: INVERTER_A
AAVE: XNOR
AAXD: NOR_2
ABORT: IBUF
ABRB: TRI_INV_IF2
ACKS: OR_3
ACLK: OBUF_A
ACOU: TRI_BUF_IF1
ACPQ: DELAY_BUF
BAAG: BUF
BAAO: BUF
BABK: BUF
BABL: BUF
BABW: INVERTER_A
BAEH: NOR_2
BAEW: NOR_2
BAFF: NOR_2
BAGU: AND_2
BAIS: OR_4
BALC: OR_2
BANP: OR_2
BANW: INVERTER_A
BANX: NAND_2
BAOZ: NAND_4
BAPI: NAND_3
BASL: NAND_3
BATZ: NAND_3
BAUV: INVERTER_A
BAYS: INVERTER_A
BBAR: AND_2
BBER: AND_3
BBFY: XNOR
BBHQ: XNOR
BBKM: NOR_2
BBKY: NOR_3
BBNU: NOR_5
BBNW: DFFR_A
BBQF: INVERTER_A
BBSQ: NAND_5
BBUI: NAND_4
BBWK: NAND_2
BBXY: INVERTER_A
BBYP: INVERTER_A
BBZQ: NAND_5
BBZX: AND_4_NOR_2
BCDB: AND_3_AND_3_NOR_2
BCFJ: AND_4
BCGJ: XOR
CABL: OR_2_NAND_3
CACL: BUF
CACT: AND_3
CACW: AND_3
CADW: INVERTER_A
CAEI: INVERTER_A
CAEO: NAND_4
CAFH: BUF
CAHN: AND_3
CAJX: NOR_3
CAKS: DFFR_B
CAKW: DFFR_B
CANH: DFFR_B
CAQL: DFFR_B
CARY: NOR_6
CAWC: XNOR
CAWE: INVERTER_A
CAXV: NOR_4
CAXW: XNOR
CAZC: INVERTER_A
CAZD: NOR_6
CBAM: XOR
CBDC: DFFR_B
CBEP: DFFR_B
CBFI: DFFR_B
CBGC: DFFR_B
CBIS: INVERTER_A
CPUCK: OBUF_A
DBHA: NAND_4
DBIS: BUF
DBJW: BUF
DBPI: BUF
DBPP: BUF
DBVA: BUF
DBWG: OR_4
DBZJ: OR_4
DCBP: OR_2
DCDY: INVERTER_A
DCEG: TRI_INV_IF2
DCIN: INVERTER_A
DCQF: DELAY_BUF
DFAA: DELAY_BUF
DFAF: DELAY_BUF
DRAMMODE: IBUF
EACZ: NOR_2
EAHW: INVERTER_A
EAMV: NOR_5
EANE: NOR_5
EAOI: NOR_6
EAPY: NOR_8
EARJ: INVERTER_A
EASO: INVERTER_A
EAVX: DFFR_A
EBBE: INVERTER_A
EBCS: NAND_3
EBMJ: INVERTER_A
EBMQ: INVERTER_A
EBOS: INVERTER_A
EBQY: AND_2
EBRW: DELAY_BUF
EBSG: DFFR_A
EBVQ: DFFR_A
EBXE: DFFR_A
EBYP: DFFR_A
ECCU: DFFR_A
ECEK: DFFR_A
ECGN: DFFR_A
ECGO: DFFR_A
EFED: INVERTER_A
EFEL: NOR_2
FBAC: AND_4_NOR_2
FBBC: INVERTER_A
FBFE: OR_2
FBII: NAND_5
FBPE: INVERTER_A
FBSI: TRI_INV_IF2
FBTA: BUF
FFCV: NAND_2
FFGS: NAND_2
GAJP: BUF
GBEG: OR_3
GBEI: OR_2
GBEV: NAND_3
GBGK: DELAY_BUF
GBTC: INVERTER_A
GBTL: BUF
GFAY: DELAY_BUF
GFCD: DELAY_BUF
HAAI: NAND_2
HAKW: BUF
HALC: OR_2
HALT: IBUF
HAMT: TRI_BUF_IF0
HANA: INVERTER_A
HASI: BUF
HAXK: BUF
HAZL: INVERTER_A
HBCA: TRI_BUF_IF1
HBCT: OR_2
HBEP: TRI_BUF_IF1
HBFW: TRI_BUF_IF0
HBGA: OR_2
HBGC: TRI_BUF_IF0
HBPL: BUF
HBQJ: INVERTER_A
HBQO: TRI_BUF_IF0
HVCM: IBUF
IAAG: DELAY_BUF
IANF: OR_2
IAQD: AND_2
IAQS: INVERTER_A
IAQU: OR_2
IAQV: AND_2
IARB: TRI_BUF_IF0
IARF: OR_3
IARQ: NOR_2
IAUB: INVERTER_A
IAUO: DFFR_A
IAYI: DFFR_A
IBAL: DFFR_A
IBEP: BUF
IBGG: OR_2
IBKU: OR_2
IBNJ: INVERTER_A
IBPD: TRI_BUF_IF0
IBPR: INVERTER_A
IBPY: NOR_2
IBSM: TRI_BUF_IF1
IBTS: TRI_INV_IF2
IBUA: OR_2
IBUD: BUF
IOAW: TRI_BUF_IF0
JAFF: DFFR_A
JAGY: INVERTER_A
JAHF: AND_2
JAKD: NOR_3
JAOO: DFFR_A
JAQD: DFFR_A
JAWP: INVERTER_A
JAXB: INVERTER_A
JAXC: AND_2
JAXO: MUX
JBCR: OR_2
JBDE: INVERTER_A
JBDJ: BUF
JBHT: DFFR_A
JBIL: BUF
JBNA: OR_2_NAND_3
JBND: NAND_2
JBPY: NAND_2
JBQK: BUF
JBQV: AND_2
JBRI: AND_2
JBRX: INVERTER_A
JBSB: TRI_BUF_IF0
JBSU: NOR_2
KAAQ: INVERTER_A
KAEZ: DFFR_A
KAHG: AND_2
KAQE: OR_2_NAND_3
KARA: AND_4
KAVS: DFFR_A
KAYP: DFFR_A
KBGM: DFFR_A
KBGO: DFFR_A
KBIE: DFFR_A
KBIF: DFFR_A
KBKC: DFFR_A
KBLJ: DFFR_A
KBMV: DFFR_A
KBNZ: BUF_INV
KBOI: NAND_3
KBPI: NAND_4
KBSI: INVERTER_A
KBTI: INVERTER_A
KBUP: NAND_2
KBVA: OR_2
KBWT: OR_2
KBWU: TRI_BUF_IF0
LBOQ: OR_2
LBQM: OR_2
LBWH: INVERTER_A
LBXR: TRI_BUF_IF1
LBYR: INVERTER_A
LCIH: BUF
LCLC: NAND_2
LCLR: INVERTER_A
LCNI: NAND_3
LCPE: NAND_3
LCQL: NAND_3
LCQV: NAND_3
LCQZ: NOR_2
LCSG: AND_2
LCSU: OR_3
LCWR: TRI_BUF_IF0
LDAD: INVERTER_A
MAAG: AND_2
MABB: AND_2
MAGI: INVERTER_A
MAGR: BUF
MAGV: BUF
MAHR: OR_2
MAJY: OR_2
MAMK: INVERTER_A
MAOG: DFFR_B
MASS: BUF
MAVB: AND_2
MAWK: BUF
MAWW: OR_2
MAXX: MUX
MBBX: INVERTER_A
MBCD: BUF
MBDX: OR_2
MBFM: DFFR_B
MBLO: DFFR_B
MBNS: INVERTER_A
MBPY: OR_3
MBRP: NAND_2
MBSK: BUF
MBUB: INVERTER_A
MBUP: AND_4_NOR_2
MBXS: NAND_2
MBZG: OR_2
MCBW: NAND_3
MCCZ: OR_3
MF: OBUF_A
NAGK: BUF
NAJD: BUF
NAPN: INVERTER_A
NAPZ: AND_2
NAQE: BUF
NBBM: BUF
NBCF: AND_2
NBEB: BUF
NBEG: BUF
NBEP: AND_2
NBHJ: BUF
NBHM: BUF
NBIE: AND_2
NBIV: DFFR_B
NBIZ: DFFR_B
NBJW: OR_2
NBKW: BUF
NBPG: BUF
NBQA: BUF
NBRL: BUF_INV
NBSM: DFFR_B
NBUB: OR_2
NBWF: DFFR_B
NBXE: TRI_BUF_IF0
NBZA: OR_2
NBZE: NAND_2
NCAN: OR_2
OAAF: INVERTER_A
OACU: BUF
OAFI: BUF
OAFM: BUF
OAGC: BUF
OAGE: BUF
OAHW: OR_2
OALA: AND_2
OANZ: BUF
OAOU: DFFR_A
OATI: BUF
OATK: NAND_2
OAUS: TRI_BUF_IF0
OBBW: INVERTER_A
OBEA: INVERTER_A
OBEE: AND_2
OBEQ: AND_2
OBHN: DFFR_B
OBIW: DFFR_B
OBNR: NAND_2
OBNU: OR_2_OR_2_OR_2_OR_2_NAND_4
OBRC: INVERTER_A
OBWM0, OBWM1: MUX
OBXF: INVERTER_A
OBXV: INVERTER_A
OBXZ: BUF
OCBU: TRI_BUF_IF0
OCDM: AND_3_AND_3_NOR_2
OCEG: AND_2
OCFG: INVERTER_A
OCHV: BUF
OCIS: TRI_BUF_IF0
OCLC: DFFR_A
OCLX: DFFR_A
OCOG: BUF
OCQI: AND_2
OCRQ: BUF
OCRS: BUF
OCSD: NAND_2
OCTG: DEMUX_3-8
OCVK: AND_2
ODIB: BUF
ODNR: TRI_BUF_IF0
ODQC: BUF
ODSN: BUF
ODYH: INVERTER_A
OEAE: BUF
PASU: AND_2
PAWC: AND_2
PAWH: AND_2
PBAD: DFFR_A
PBEG: DFFR_A
QBOC: AND_2
RDY: IBUF
REFRESH: OBUF_A
RES: IBUF
RW: IOBUF_A
SYSCLK: IOBUF_A
TM: IBUF
U6: IAOO1
U8: IAOO0
U10, U11, U12, U13, U14, U20, U21, U22: TRI_BUF_IF1
U18: HAUU1
U19: HAUU0
UBNH: NAND_5
UNCONNECTEDPIN: IBUF
VDA: IOBUF_A
VP: OBUF_A
VPA: IOBUF_A
XF: OBUF_A
XIN: IBUF
~{CPU_RD}: OBUF_A
~{CPU_WR}: OBUF_A
~{DMA}: OBUF_A
~{ML}: OBUF_A
~{PARD}: OBUF_A
~{PAWR}: OBUF_A
~{RAM_SEL}: OBUF_A
~{ROM_SEL}: OBUF_A

Connections:
21XX: BBSQ.2, BBZQ.2, EBQY.3
21XX_DMA_RD?: BBZX.1, BCFJ.5
420X: CACL.2, FBII.1, UBNH.1
421X: CAFH.2, FBBC.1
4000-41FF: BAYS.1, BBAR.3, U18.2
65816_?: LBOQ.3, MAWW.3, U6.4, U8.4
65816_ABORT: ABORT.1
65816_IRQ: NCAN.1
65816_MF: HBGC.1 (IN), HBGC.3 (IN)
65816_ML: ODNR.1 (IN), ODNR.3 (IN)
65816_NMI: KBWT.1
65816_RW: IBSM.1 (IN), IBSM.3 (IN)
65816_VDA: IAQD.2
65816_VP: DBVA.1
65816_VPA: IAQV.2
65816_XF: HBQO.1 (IN), HBQO.3 (IN)
65816_~RDY: HANA.1, JBND.3
+5V: BBWK.1, DBHA.1, DBHA.2, DBHA.3, FFCV.1, FFGS.1, HAAI.1, JBHT.2 (D), OCDM.1, OCTG.
A0: BATZ.1, BAUV.1, FBII.4, UBNH.4
A1: EBOS.1, FBPE.1, UBNH.3
A2: EBMJ.1, FBII.3
A3: EAPY.3, FBII.2, UBNH.2
A4: CACW.1, CADW.1
A5: CAJX.1
A6: CAJX.2
A7: CAJX.3, EAOI.1
A8: EAMV.1, EAPY.5, EASO.1
A9: CAZD.1, EANE.2, EAPY.6, EARJ.1
A10: CARY.1, CAZD.2
A11: CARY.2, CAZD.3
A12: CARY.3, CAZD.4
A13: BAFF.1, BAIS.1, BAPI.2, CAZD.5, EAHW.1, EAMV.3, EAOI.4, EAPY.7
A14: BAFF.2, BAIS.2, BAPI.3, CAZC.1, EANE.4, EBMQ.1
A15: BAEH.1, BAEW.1, BAIS.3, CARY.4
A16: U22.4
A17: GBEV.3, U21.4
A18: GBEV.2, U20.4
A19: GBEV.1, U14.4
A20: CAEO.4, U12.4
A21: CAEO.3, U11.4
A22: BAEH.2, BAEW.2, BAIS.4, CAEO.2, CARY.5, U10.4
A23: BANW.1, CAEI.1, U13.4
AAA: JBDE.1, JBPY.2, KBOI.2, NBZA.1
BANK_DIR_OUT_EN: JBQV.3
CONTROLLER: JAKD.2, JAOO.6 (Q), KARA.1, MAMK.1
D0: EBBE.1, ECGO.2 (D)
D1: ECGN.2 (D)
D2: ECEK.2 (D)
D3: ECCU.2 (D)
D4: EBYP.2 (D)
D5: EBXE.2 (D)
D6: EBVQ.2 (D)
D7: EBSG.2 (D)
DIR_OUT_EN: ABRB.1 (~ENA), JBQV.1, NBRL.2
DMA_CLK?: IBUA.1, JAOO.3 (CLK), JAOO.4 (~CLK), JAQD.3 (CLK), JAQD.4 (~CLK), U8.2
DMA_ON: JAXO.1, JBSU.1, MAXX.1
DMA_ON?: LBXR.1 (IN), LBXR.3 (IN)
DMA_RW: AAJX.2, AAMX.1, BCFJ.2, KBSI.1, OCIS.1 (IN), OCIS.3 (IN), OCLC.6 (Q)
FALLING_VBLANK: OAOU.2 (D)
FromDMA: OCLC.2 (D), OCLX.2 (D)
GND: EACZ.2, EFEL.2, OCTG., U10.1 (IN), U10.3 (IN), U11.1 (IN), U11.3 (IN), U12.1 (IN), U12.3 (IN), U13.1 (IN), U13.3 (IN), U14.1 (IN), U14.3 (IN), U20.1 (IN), U20.3 (IN), U21.1 (IN), U21.3 (IN), U22.1 (IN), U22.3 (IN)
H0: OAHW.2
H1: QBOC.1
H3: QBOC.2
H128-135: PBEG.2 (D)
H146_OR_H150: PASU.1, PAWC.3
HBLANK: OBIW.2 (D)
INTERNAL_SYSCLK: JBSB.1 (IN), JBSB.3 (IN)
IO_RANGE: BAEW.3, BANP.2, BANX.1, BAOZ.1, BAPI.1, BBAR.1
MODE1_OR_MODE3: MAHR.2, MAJY.1, NBZE.3
MODE2_OR_MODE3: EAMV.5, EANE.5, EAOI.6, GBEG.3, IARQ.2, IBPR.1, OBNR.3
MODE4_OR_MODE5: OBXV.1, OCFG.1, OCSD.3
MODE5_OR_MODE7: OATK.3
unnamed: AABC.1, AAFD.3
unnamed: AABZ.1, DCQF.2
unnamed: AABZ.2, BBWK.2
unnamed: AAFD.1, BABW.2
unnamed: AAFD.2, BAEH.3
unnamed: AAHT.3, EBRW.1
unnamed: AAJX.1, AALV.1, BBXY.1, BCDB.1, BCDB.4, BCFJ.1, DCIN.2
unnamed: AAJX.4, AALV.4, BCFJ.4, CBIS.2
unnamed: AAJX.5, ACPQ.1
unnamed: AAKO.3, BABK.1
unnamed: AALV.2, AAMX.2, BCDB.5
unnamed: AAVE.1, CBEP.2 (D)
unnamed: AAVE.2 (1), AAXD.3
unnamed: AAVE.3 (2), ACKS.3, CBEP.6 (~Q)
unnamed: AAXD.1, ACKS.1, BCGJ.2 (1), CBGC.2 (D), CBGC.6 (~Q)
unnamed: AAXD.2, ACKS.2, BCGJ.3 (2), CBFI.6 (~Q)
unnamed: ABRB.3, RW.1 (DRV_LOW), RW.3 (~DRV_HIGH)
unnamed: ACKS.4, BBKM.1, BBKY.1, BBNU.1, CAXV.1, CBAM.2 (1)
unnamed: ACLK.1, DBPP.2
unnamed: ACOU.1 (IN), ACOU.3 (IN), RW.2 (~INPUT)
unnamed: BAAG.1, BAGU.3
unnamed: BAAO.1, BBER.4
unnamed: BABK.2, EFED.1
unnamed: BABL.1, HBQO.4, KBWU.4, LCWR.4
unnamed: BABL.2, XF.1
unnamed: BABW.1, BAGU.2, BALC.3
unnamed: BAFF.3, BANX.2
unnamed: BAGU.1, BAIS.5
unnamed: BALC.1, CAEO.5
unnamed: BALC.2, GBEV.4
unnamed: BANP.1, BANW.2
unnamed: BAOZ.5, CABL.2
unnamed: BASL.2, BATZ.2, EAPY.9
unnamed: BASL.3, BATZ.3, CACT.2, CACW.2, CAHN.4
unnamed: BBAR.2, CAZD.7
unnamed: BBER.3, BBNW.6 (Q)
unnamed: BBFY.1, CAKS.2 (D)
unnamed: BBFY.2 (1), BBNU.6
unnamed: BBFY.3 (2), CAKS.6 (~Q)
unnamed: BBHQ.1, CAQL.2 (D)
unnamed: BBHQ.2 (1), BBKM.3
unnamed: BBHQ.3 (2), BBKY.3, BBNU.3, CAQL.6 (~Q), CAXV.3
unnamed: BBKM.2, BBKY.2, BBNU.2, CAXV.2, CBAM.3 (2), CBDC.6 (~Q)
unnamed: BBKY.4, CAWC.2 (1)
unnamed: BBNU.4, CANH.6 (~Q), CAWC.3 (2), CAXV.4
unnamed: BBNU.5, CAKW.6 (~Q), CAXW.3 (2)
unnamed: BBNW.1 (~RESET), BBNW.5 (~RESET)
unnamed: BBQF.1, BBWK.3
unnamed: BBQF.2, EACZ.1
unnamed: BBSQ.1, BBUI.1, BBZQ.1, BBZX.5, CABL.1, CAWE.1, GBEG.4
unnamed: BBSQ.3, BBUI.2, BBXY.2, BBZQ.3, BBZX.4
unnamed: BBYP.2, BBZQ.4, BBZX.3
unnamed: BCDB.3, CBIS.1, KBTI.1, OCLX.6 (Q)
unnamed: BCGJ.1, CBFI.2 (D)
unnamed: CABL.5, U19.2
unnamed: CACL.1, CACT.4
unnamed: CACT.3, CACW.3, EAMV.6
unnamed: CACW.4, CAFH.1
unnamed: CAEI.2, CAEO.1
unnamed: CAHN.1, CARY.7, EBCS.2, EBQY.1
unnamed: CAHN.2, CAJX.4
unnamed: CAHN.3, EBCS.1, LBQM.3
unnamed: CAKS.1 (~RESET), CAKS.5 (~RESET), CAKW.1 (~RESET), CAKW.5 (~RESET), CANH.1 (~RESET), CANH.5 (~RESET), CAQL.1 (~RESET), CAQL.5 (~RESET), CBDC.1 (~RESET), CBDC.5 (~RESET), CBEP.1 (~RESET), CBEP.5 (~RESET), CBFI.1 (~RESET), CBFI.5 (~RESET), CBGC.1 (~RESET), CBGC.5 (~RESET), DBJW.1, HASI.1, IAUO.6 (Q), IAYI.2 (D)
unnamed: CAKS.7 (Q), MBLO.2 (D)
unnamed: CAKW.2 (D), CAXW.1
unnamed: CANH.2 (D), CAWC.1
unnamed: CARY.6, CAWE.2
unnamed: CAXV.5, CAXW.2 (1)
unnamed: CAZC.2, CAZD.6
unnamed: CBAM.1, CBDC.2 (D)
unnamed: CBEP.7 (Q), MBFM.2 (D)
unnamed: CBFI.7 (Q), NBSM.2 (D)
unnamed: CBGC.7 (Q), NBWF.2 (D)
unnamed: CPUCK.1, HBPL.2
unnamed: DBHA.4, EACZ.3
unnamed: DBHA.5, ~{CPU_RD}.1
unnamed: DBIS.1, FBTA.2
unnamed: DBIS.2, ~{CPU_WR}.1
unnamed: DBPI.1, HBGC.4, NBXE.4, OAUS.4
unnamed: DBPI.2, MF.1
unnamed: DBWG.1, EBYP.6 (Q)
unnamed: DBWG.2, EBXE.6 (Q)
unnamed: DBWG.3, EBVQ.6 (Q)
unnamed: DBWG.4, EBSG.6 (Q)
unnamed: DBWG.5, DCBP.2
unnamed: DBZJ.1, ECGO.6 (Q)
unnamed: DBZJ.2, ECGN.6 (Q)
unnamed: DBZJ.3, ECEK.6 (Q)
unnamed: DBZJ.4, ECCU.6 (Q)
unnamed: DBZJ.5, DCBP.1
unnamed: DCBP.3, OBEE.1
unnamed: DCDY.1, UNCONNECTEDPIN.1
unnamed: DCDY.2, IBPY.2
unnamed: DCEG.3, VPA.1 (DRV_LOW), VPA.3 (~DRV_HIGH)
unnamed: DFAA.1, DFAF.2
unnamed: DFAA.2, ~{PAWR}.1
unnamed: DFAF.1, EFEL.3
unnamed: DRAMMODE.1, ODYH.1
unnamed: EANE.6, EBQY.2
unnamed: EAOI.7, EBCS.3
unnamed: EAVX.2 (D), EBBE.2
unnamed: EBRW.2, IAAG.1, IANF.2
unnamed: EFED.2, EFEL.1
unnamed: FBSI.3, VDA.1 (DRV_LOW), VDA.3 (~DRV_HIGH)
unnamed: FBTA.1, GAJP.2
unnamed: FFCV.2, JBIL.2
unnamed: FFCV.3, FFGS.2
unnamed: FFGS.3, GFCD.1
unnamed: GAJP.1, HAAI.3
unnamed: GBEI.1, GBGK.2
unnamed: GBEI.3, OAAF.1
unnamed: GBTC.1, IBPR.2, JBQV.2, JBRI.1
unnamed: GBTC.2, U10.2 (~ENA), U11.2 (~ENA), U12.2 (~ENA), U13.2 (~ENA), U14.2 (~ENA), U20.2 (~ENA), U21.2 (~ENA), U22.2 (~ENA)
unnamed: GBTL.1, JBRI.3
unnamed: GFAY.1, GFCD.2
unnamed: GFAY.2, ~{PARD}.1
unnamed: HAAI.2, OAAF.2
unnamed: HAKW.1, HALC.3
unnamed: HALC.1, HAMT.4
unnamed: HALC.2, HAMT.1 (IN), HAMT.3 (IN), HANA.2
unnamed: HALT.1, OCTG.
unnamed: HAZL.1, IARB.2 (~ENA), IOAW.2 (~ENA), JAXC.3
unnamed: HAZL.2, HBCA.2 (~ENA), HBEP.2 (~ENA)
unnamed: HBCA.1 (IN), HBCA.3 (IN), HBCT.3
unnamed: HBCT.1, VPA.2 (~INPUT)
unnamed: HBEP.1 (IN), HBEP.3 (IN), HBGA.3
unnamed: HBFW.1 (IN), HBFW.3 (IN), SYSCLK.2 (~INPUT)
unnamed: HBFW.2 (~ENA), JBRX.1, OCDM.3
unnamed: HBGA.1, VDA.2 (~INPUT)
unnamed: HBPL.1, IBUA.3
unnamed: HBQJ.1, RDY.1
unnamed: HVCM.1, OCTG.
unnamed: IAAG.2, IANF.1
unnamed: IANF.3, JBIL.1
unnamed: IAQD.1, IAQU.3, IAQV.1
unnamed: IAQD.3, IOAW.1 (IN), IOAW.3 (IN)
unnamed: IAQS.2, IAQU.2
unnamed: IAQV.3, IARB.1 (IN), IARB.3 (IN)
unnamed: IARF.1, JBDE.2
unnamed: IARQ.1, IAUB.2
unnamed: IARQ.3, IAUO.2 (D)
unnamed: IAUO.1 (~RESET), IAUO.5 (~RESET)
unnamed: IAYI.1 (~RESET), IAYI.5 (~RESET)
unnamed: IBAL.1 (~RESET), IBAL.5 (~RESET)
unnamed: IBAL.6 (Q), MASS.1
unnamed: IBEP.1, IBGG.3
unnamed: IBGG.2, IBNJ.2
unnamed: IBKU.3, IBTS.2
unnamed: IBPD.1 (IN), IBPD.3 (IN), IBSM.4
unnamed: IBTS.1 (~ENA), JBRX.2, JBSB.2 (~ENA)
unnamed: IBTS.3, SYSCLK.1 (DRV_LOW), SYSCLK.3 (~DRV_HIGH)
unnamed: IBUD.1, JBSU.3
unnamed: IBUD.2, ~{DMA}.1
unnamed: JAFF.6 (Q), JAGY.1
unnamed: JAGY.2, JAHF.1, JAKD.3
unnamed: JAHF.2, JAKD.1, JAQD.6 (Q)
unnamed: JAHF.3, KAQE.2
unnamed: JAKD.4, KAHG.1
unnamed: JAXB.1, JBNA.4, JBPY.1, KBUP.3
unnamed: JAXB.2, JAXC.1
unnamed: JBCR.3, MAWK.1
unnamed: JBDJ.1, JBHT.6 (Q)
unnamed: JBHT.3 (CLK), JBHT.4 (~CLK), LBWH.2
unnamed: JBNA.1, LBXR.4
unnamed: JBND.2, JBPY.3
unnamed: KAAQ.2, KAEZ.3 (CLK), KAEZ.4 (~CLK)
unnamed: KAEZ.2 (D), MAJY.3
unnamed: KAHG.3, KAQE.3
unnamed: KAQE.4, KARA.5
unnamed: KAQE.5, KBMV.2 (D)
unnamed: KAVS.2 (D), KAYP.6 (Q)
unnamed: KBGM.2 (D), KBGO.6 (Q)
unnamed: KBIE.2 (D), KBIF.6 (Q)
unnamed: KBLJ.2 (D), KBMV.6 (Q)
unnamed: KBOI.1, KBPI.1, LCLR.1, LCQL.1, LCQZ.3
unnamed: KBOI.4, LCLC.1
unnamed: KBPI.2, KBTI.2
unnamed: KBPI.3, KBSI.2
unnamed: KBPI.5, MBRP.1
unnamed: KBUP.2, KBVA.3
unnamed: KBWT.3, LCWR.1 (IN), LCWR.3 (IN)
unnamed: LBYR.2, LCQL.3, LCQV.1
unnamed: LCIH.1, LCLC.3
unnamed: LCLR.2, LCNI.2, LCQV.2, LCSU.3
unnamed: LCNI.4, MCBW.2
unnamed: LCPE.1, LCQL.4
unnamed: LCPE.2, LCQV.4
unnamed: LCPE.3, MBPY.4
unnamed: LCPE.4, OBWM0.2
unnamed: LCSU.4, MCBW.1
unnamed: LDAD.2, MBXS.1
unnamed: MAAG.3, MBCD.1
unnamed: MABB.1, MAGI.2
unnamed: MABB.3, MAGR.1, MAGV.1, NAPN.1
unnamed: MAGR.2, MAGV.2, NBIV.3 (CLK), NBIV.4 (~CLK), NBIZ.3 (CLK), NBIZ.4 (~CLK), OBHN.3 (CLK), OBHN.4 (~CLK), OBIW.3 (CLK), OBIW.4 (~CLK)
unnamed: MAHR.1, MAJY.2
unnamed: MAHR.3, MAOG.2 (D)
unnamed: MAMK.2, OAHW.1
unnamed: MAOG.3 (CLK), MAOG.4 (~CLK), MBDX.1, MBFM.6 (~Q)
unnamed: MAVB.3, MAXX.2
unnamed: MAXX.3, MBCD.2
unnamed: MAXX.4, OANZ.1
unnamed: MBBX.2, MBZG.2
unnamed: MBDX.3, OCRQ.1, OCRS.1
unnamed: MBFM.3 (CLK), MBFM.4 (~CLK), MBLO.3 (CLK), MBLO.4 (~CLK), NBJW.2, NBQA.1, NBRL.1, NBSM.6 (~Q)
unnamed: MBNS.2, MBPY.3
unnamed: MBPY.1, MCCZ.3, OBBW.2
unnamed: MBRP.2, MBXS.3
unnamed: MBRP.3, OBRC.1, OBWM1.3
unnamed: MBSK.1, MBUP.3
unnamed: MBUB.2, MBUP.4
unnamed: MBZG.3, ODSN.1
unnamed: MCBW.3, MCCZ.4
unnamed: MCBW.4, OBWM1.2
unnamed: NAGK.1, NAJD.1, NAPN.2
unnamed: NAGK.2, NAJD.2
unnamed: NAPZ.2, NBSM.7 (Q), OAFM.1, OAGC.1
unnamed: NAPZ.3, OACU.1, OAFI.1
unnamed: NAQE.1, NBBM.1, NBCF.3
unnamed: NAQE.2, NBBM.2
unnamed: NBCF.2, NBHJ.1, NBHM.1, NBWF.7 (Q)
unnamed: NBEB.1, NBEG.1, NBEP.3
unnamed: NBEB.2, NBEG.2, OAOU.3 (CLK), OAOU.4 (~CLK)
unnamed: NBIE.1, NBIV.2 (D), NBIZ.7 (Q)
unnamed: NBIE.2, NBIV.6 (~Q)
unnamed: NBIV.1 (~RESET), NBIV.5 (~RESET)
unnamed: NBIZ.1 (~RESET), NBIZ.5 (~RESET)
unnamed: NBIZ.2 (D), OAOU.6 (Q)
unnamed: NBJW.3, NBKW.1, NBPG.1
unnamed: NBKW.2, NBPG.2
unnamed: NBRL.1, OBNU.5
unnamed: NBSM.1 (~RESET), NBSM.5 (~RESET)
unnamed: NBSM.3 (CLK), NBSM.4 (~CLK), NBUB.2, NBWF.6 (~Q)
unnamed: NBUB.3, OBXZ.1, OCHV.1
unnamed: NBWF.1 (~RESET), NBWF.5 (~RESET)
unnamed: NBXE.1 (IN), NBXE.3 (IN), NBZA.3
unnamed: NBXE.2 (~ENA), OBXV.2
unnamed: NCAN.3, OCBU.1 (IN), OCBU.3 (IN)
unnamed: OACU.2, OAFI.2
unnamed: OAHW.3, OALA.1
unnamed: OALA.2, QBOC.3
unnamed: OALA.3, PBAD.2 (D)
unnamed: OANZ.2, REFRESH.1
unnamed: OAOU.1 (~RESET), OAOU.5 (~RESET)
unnamed: OBEA.2, OBNU.6
unnamed: OBEQ.1, OBHN.2 (D), OBIW.7 (Q)
unnamed: OBEQ.2, OBHN.6 (~Q)
unnamed: OBHN.1 (~RESET), OBHN.5 (~RESET)
unnamed: OBIW.1 (~RESET), OBIW.5 (~RESET)
unnamed: OBNU.8, OBXF.2
unnamed: OBRC.2, OBWM0.3
unnamed: OBWM0.4, ODQC.1
unnamed: OBWM1.4, ODIB.1
unnamed: OBXZ.2, OCHV.2
unnamed: OCBU.4, OCIS.4, ODNR.4, OEAE.1
unnamed: OCLC.1 (~RESET), OCLC.5 (~RESET)
unnamed: OCLX.1 (~RESET), OCLX.5 (~RESET)
unnamed: OCRQ.2, OCRS.2
unnamed: OCTG., OCVK.2, TM.1
unnamed: ODYH.2, PASU.2
unnamed: OEAE.2, ~{ML}.1
unnamed: PAWC.1, PBEG.6 (Q)
unnamed: PAWC.2, PAWH.3
unnamed: PAWH.2, PBAD.6 (Q)
ODQC: ODQC.2
RW: ABRB.2, ACOU.4, BBSQ.4, BBUI.3, BBYP.1, IBPD.4, LCQL.2, LCSU.1, MBNS.1, MCCZ.2
Reg_Read: FBAC.3, KBPI.4, LBYR.1, LCNI.1, MBXS.2
TCKSEL0_MUXOUT0?: U18.1, U19.1
TCKSEL1_MUXOUT1?: U19.3
TCKSEL1_MUXOUT2?: U18.3
VP: DBVA.2, VP.1
XIN: CAKS.3 (CLK), CAKS.4 (~CLK), CAKW.3 (CLK), CAKW.4 (~CLK), CANH.3 (CLK), CANH.4 (~CLK), CAQL.3 (CLK), CAQL.4 (~CLK), CBDC.3 (CLK), CBDC.4 (~CLK), CBEP.3 (CLK), CBEP.4 (~CLK), CBFI.3 (CLK), CBFI.4 (~CLK), CBGC.3 (CLK), CBGC.4 (~CLK), JAWP.1, XIN.1
wBCDB: BBER.2, BBNW.2 (D), BCDB.3
wDBJW_wHASI_RST: DBJW.2, EAVX.1 (~RESET), EAVX.5 (~RESET), EBSG.1 (~RESET), EBSG.5 (~RESET), EBVQ.1 (~RESET), EBVQ.5 (~RESET), EBXE.1 (~RESET), EBXE.5 (~RESET), EBYP.1 (~RESET), EBYP.5 (~RESET), ECCU.1 (~RESET), ECCU.5 (~RESET), ECEK.1 (~RESET), ECEK.5 (~RESET), ECGN.1 (~RESET), ECGN.5 (~RESET), ECGO.1 (~RESET), ECGO.5 (~RESET), HASI.2, JAFF.1 (~RESET), JAFF.5 (~RESET), JAOO.1 (~RESET), JAOO.5 (~RESET), JAQD.1 (~RESET), JAQD.5 (~RESET), KAEZ.1 (~RESET), KAEZ.5 (~RESET), KAVS.1 (~RESET), KAVS.5 (~RESET), KAYP.1 (~RESET), KAYP.5 (~RESET), KBGM.1 (~RESET), KBGM.5 (~RESET), KBGO.1 (~RESET), KBGO.5 (~RESET), KBIE.1 (~RESET), KBIE.5 (~RESET), KBIF.1 (~RESET), KBIF.5 (~RESET), KBKC.1 (~RESET), KBKC.5 (~RESET), KBLJ.1 (~RESET), KBLJ.5 (~RESET), KBMV.1 (~RESET), KBMV.5 (~RESET), MAOG.1 (~RESET), MAOG.5 (~RESET), MBFM.1 (~RESET), MBFM.5 (~RESET), MBLO.1 (~RESET), MBLO.5 (~RESET), PAWH.1, PBAD.1 (~RESET), PBAD.5 (~RESET), PBEG.1 (~RESET), PBEG.5 (~RESET)
wGBTL: ACOU.2 (~ENA), GBTL.2
wHAKW: HAKW.2, IBPD.2 (~ENA)
wHAUU0: JAQD.2 (D), U19.4
wHAUU1: JAOO.2 (D), U18.4
wIARB_or_wHBCA: DCEG.2, HBCA.4, IARB.4, IARF.3
wIARF: GBEG.2, IARF.4
wIAYI: IAYI.6 (Q), JBHT.1 (~RESET), JBHT.5 (~RESET)
wIBEP: IBEP.2
wIBPY: HBCT.2, HBGA.2, IBKU.1, IBPY.3, IBUA.2, JBSU.2, KBWT.2, NBZA.2, NCAN.2
wIOAW_or_wHBEP: FBSI.2, HBEP.4, IARF.2, IOAW.4
wJAXC: DCEG.1 (~ENA), FBSI.1 (~ENA)
wJAXO: GBEG.1, JAXO.4, JBCR.2
wJBDJ: IAQU.1, IBGG.1, JBDJ.2, JBNA.2, U6.2
wJBNA: DCIN.1, JBNA.5, JBQK.1
wJBQK: JBQK.2, LBQM.2, MBUP.2, OBNU.7, OBWM0.1, OBWM1.1
wJP2I0: U6.3
wJP2I1: LBOQ.1
wJP2I2: OBBW.1, OBEA.1
wJP2I3: U8.3
wJP2I4: MAWW.1
wKAEZ: JAFF.2 (D), JAXO.3, KAEZ.6 (Q), MAAG.1, MAGI.1
wKAVS: KARA.4, KAVS.6 (Q)
wKBGM: KARA.3, KAYP.2 (D), KBGM.6 (Q)
wKBIE: KAHG.2, KARA.2, KBGO.2 (D), KBIE.6 (Q)
wKBKC: KAQE.1, KBIF.2 (D), KBKC.6 (Q), KBNZ.1
wKBLJ: JAFF.3 (CLK), JAFF.4 (~CLK), KAAQ.1, KBKC.2 (D), KBLJ.6 (Q), MAAG.2, MABB.2, OAGE.1
wKBNZ: DBPP.1, KBNZ.2, KBOI.3, LCSU.2
wLCIH: HAMT.2 (~ENA), IBSM.2 (~ENA), LCIH.2
wMAOG: JAXO.2, MAOG.7 (Q), MAVB.2, MBDX.2, NBJW.1, NBUB.1
wMASS: MASS.2
wMBFM: MAVB.1, MBFM.7 (Q), NBEP.1
wMBLO: LBWH.1, MBLO.6 (~Q), OATI.1
wMBSK: JBRI.2, MBSK.2
wNBHM: LBXR.2 (~ENA), NBHJ.2, NBHM.2, OCLC.3 (CLK), OCLC.4 (~CLK), OCLX.3 (CLK), OCLX.4 (~CLK)
wNBRL_wNBQA_XIN/4: NBQA.2, NBRL.2
wOAFM: OAFM.2, OAGC.2, PBAD.3 (CLK), PBAD.4 (~CLK), PBEG.3 (CLK), PBEG.4 (~CLK)
wOATI_~XIN/256: OATI.2, OAUS.1 (IN), OAUS.3 (IN)
wOCLX: KBWU.1 (IN), KBWU.3 (IN)
wOCOG_~MODE7: IAQS.1, IBNJ.1, JAXC.2, JBND.1, LBOQ.2, LCLC.2, LCNI.3, LCQV.3, MAWW.2, MBBX.1, MBPY.2, MCCZ.1, OBNU.5, OCOG.2, U6.1, U8.1
wODIB: ODIB.2
wPASU: PASU.3
wRES: IAUB.1, IBAL.2 (D), RES.1
wSYSCLK: AAJX.3, AALV.3, BBSQ.5, BBUI.4, BBZQ.5, BBZX.2, BCDB.2, BCDB.6, BCFJ.3, HBFW.4, IBKU.2, JBSB.4, MBZG.1
~0000-1FFF: BANX.3, BAOZ.3
~21XX_DMA_RD?: AAHT.2, ACPQ.2
~21XX_DMA_WR?: AAKO.2, AALV.5
~21XX_RD: AAHT.1, BBSQ.6
~21XX_WR: AAKO.1, BBZQ.6
~420B_WR: EBSG.3 (CLK), EBSG.4 (~CLK), EBVQ.3 (CLK), EBVQ.4 (~CLK), EBXE.3 (CLK), EBXE.4 (~CLK), EBYP.3 (CLK), EBYP.4 (~CLK), ECCU.3 (CLK), ECCU.4 (~CLK), ECEK.3 (CLK), ECEK.4 (~CLK), ECGN.3 (CLK), ECGN.4 (~CLK), ECGO.3 (CLK), ECGO.4 (~CLK)
~420D_WR: EAVX.3 (CLK), EAVX.4 (~CLK), FBFE.3
~420D: FBFE.1, FBII.6
~421X: FBAC.3, FBBC.2
~4000-41FF: BAOZ.2, BAYS.2
~4016: BASL.4, FBAC.4
~4017: BATZ.4, FBAC.5
~4300-437F: EBCS.4, FBAC.2
~6000-7FFF: BAOZ.4, BAPI.4
~A0: BASL.1, BAUV.2
~A1_1: EAPY.1, EBOS.2
~A1_2: FBII.5, FBPE.2
~A2: EAPY.2, EBMJ.2
~A4: CACT.1, CADW.2, EAPY.4
~A8: EANE.1, EAOI.2, EASO.2
~A9: EAMV.2, EAOI.3, EARJ.2
~A13: EAHW.2, EANE.3
~A14: EAMV.4, EAOI.5, EAPY.8, EBMQ.2
~CPU_RD: BAAO.2, DCQF.1, FBAC.1
~CPU_WR: FBFE.2, GBEI.2, GBGK.1, HAXK.2
~FAST_ROM_EN: CABL.4, EAVX.6 (Q)
~FAST_ROM: BANP.3, CABL.3
~MAWK_WR: MAWK.2
~MODE0-3_OR_MODE7: HBGC.2 (~ENA), HBQO.2 (~ENA), JBNA.3, MBUP.1, OBXF.1, OCVK.3, ODNR.2 (~ENA)
~MODE0_OR_MODE1: LCQZ.2, LCSG.3
~MODE0_OR_MODE6: OCDM.2, OCDM.4, OCQI.3
~MODE0: KBUP.1, LCSG.1, OBNU.3, OCQI.2, OCTG.
~MODE1: KBVA.2, LCSG.2, MBUB.1, NBZE.1, OBNU.1, OCDM.5, OCTG.
~MODE2: OBNR.1, OCTG.
~MODE3: NBZE.2, OBNR.2, OCTG.
~MODE4_OR_MODE5: OCDM.6, OCFG.2
~MODE4_OR_MODE6: LCWR.2 (~ENA), OCBU.2 (~ENA), OCEG.3
~MODE4: IBPY.1, LDAD.1, OCEG.1, OCSD.1, OCTG.
~MODE5: KBWU.2 (~ENA), LBQM.1, OATK.1, OCIS.2 (~ENA), OCSD.2, OCTG.
~MODE6: OAUS.2 (~ENA), OCEG.2, OCQI.1, OCTG.
~MODE7: OATK.2, OCOG.1, OCTG., OCVK.1
~RAM_SEL: BAAG.2, ~{RAM_SEL}.1
~RD: BBER.1, BBUI.5
~ROM_SEL: AABC.2, ~{ROM_SEL}.1
~WR: BBZX.3, HAXK.1, JBCR.1
~XIN1: BBNW.3 (CLK), BBNW.4 (~CLK), IAUO.3 (CLK), IAUO.4 (~CLK), IAYI.3 (CLK), IAYI.4 (~CLK), IBAL.3 (CLK), IBAL.4 (~CLK), JAWP.2, KAVS.3 (CLK), KAVS.4 (~CLK), KAYP.3 (CLK), KAYP.4 (~CLK), KBGM.3 (CLK), KBGM.4 (~CLK), KBGO.3 (CLK), KBGO.4 (~CLK), KBIE.3 (CLK), KBIE.4 (~CLK), KBIF.3 (CLK), KBIF.4 (~CLK), KBKC.3 (CLK), KBKC.4 (~CLK), KBLJ.3 (CLK), KBLJ.4 (~CLK), KBMV.3 (CLK), KBMV.4 (~CLK), NBWF.3 (CLK), NBWF.4 (~CLK)
~wMAOG: MAOG.6 (~Q), NAPZ.1, NBCF.1, NBEP.2
~wRDY: HBQJ.2, KBVA.1, LCQZ.1, MBUP.3, OBNU.2, OBNU.4, OCDM.3

Notes on the sheet:
External SYSCLK when 1) RDY = 0 and mode 1-5 or 7 2) mode 2-3 or mode 7
To DMA
to DMA
To DMA section
12 cycle flag?
KAQE to be determined
To bottom section
8 cycle flag?
Connected to Data OUT Bus enable pins
420X To bottom section for all registers execpt 420D
SNES regs reset
B-BUS select (21XX) when not in MODE2 or 3
Goes low during internal CPU cycles VDA and VPA are low and DMA is not running
Latch signal for readable registers?
TCLK o DMA section
XIN/4
~{0000-1FFF} is WRAM ~{6000-7FFF} is expansion ~{4000-41FF} is controller 0000-7FFF is IO range BOAZ is low when accessing 2000-3FFF range (PPU, APU) and 4200-5FFF range (CPU + DMA) BANP is low when A23 is high but not in IO range i.e. FAST ROM access Therefore CABL will be high to allow 6 master c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
XIN/2
Goes to DMA too
from DMA
To DMA too
Enables 65816 Addresses when OCOG is low MODE7, external ADDRESS and DATA
XIN/8
CLK/8 Goes to DMA
To DMA section and bottom section
Modes are active low - inputs seems to be active low MODE7 = Test mode with external CPU connections bypassing 65816 MODE4-6 = DMA test modes MODE2-3 = NES modes where 4200-43FF registers are disabled MODE0-1 = SNES modes
To_bottom_of_chip_too Reg Read occurs when RW = '1', SYSCLK = '1', NOT an internal cycle
Checked items
IO range: x0xx xxxx 0xxx xxxx xxxx xxxx
XIN/256
420D WRITE
enables a Data bus IO buffers on end of row O
~{ROMSEL} = ~{A23}.A22.A21.A20.A19.A18.A17 + ~{A22}.~{A15} Consistent with access to: - 00-3F/80-BF:8000-FFFF or - 40-7D/C0-FF:0000-FFFF ~{RAMSEL} = not (~{/A23}.A22.A21.A20.A19.A18.A17 + ~{A22}.~{A15}.~{A14}.~{A13}) Consistent with access to: - 00-3F/80-BF:0000-1FFF or - 7E-7F:0000-FFFF
Connected to Data IN Bus enable pins
DMA rgisters 4300-437F active low select
Disconnects 65816 in MODE7, in MODE1 when RDY is low and during DMA Works with LCIH HAMT and IBSM might be inverting tri buffers for this to make sense.
Low when RDY = 0 in mode 1 or mode 4-6 and DMA on
JP regs reset
