rgalland/SNES_S-CPU_Schematics/S-CPU_kicad/addrdatabuses.kicad_sch

## KiCad design S-CPU_kicad/addrdatabuses.kicad_sch (2024-12-24, an earlier design)

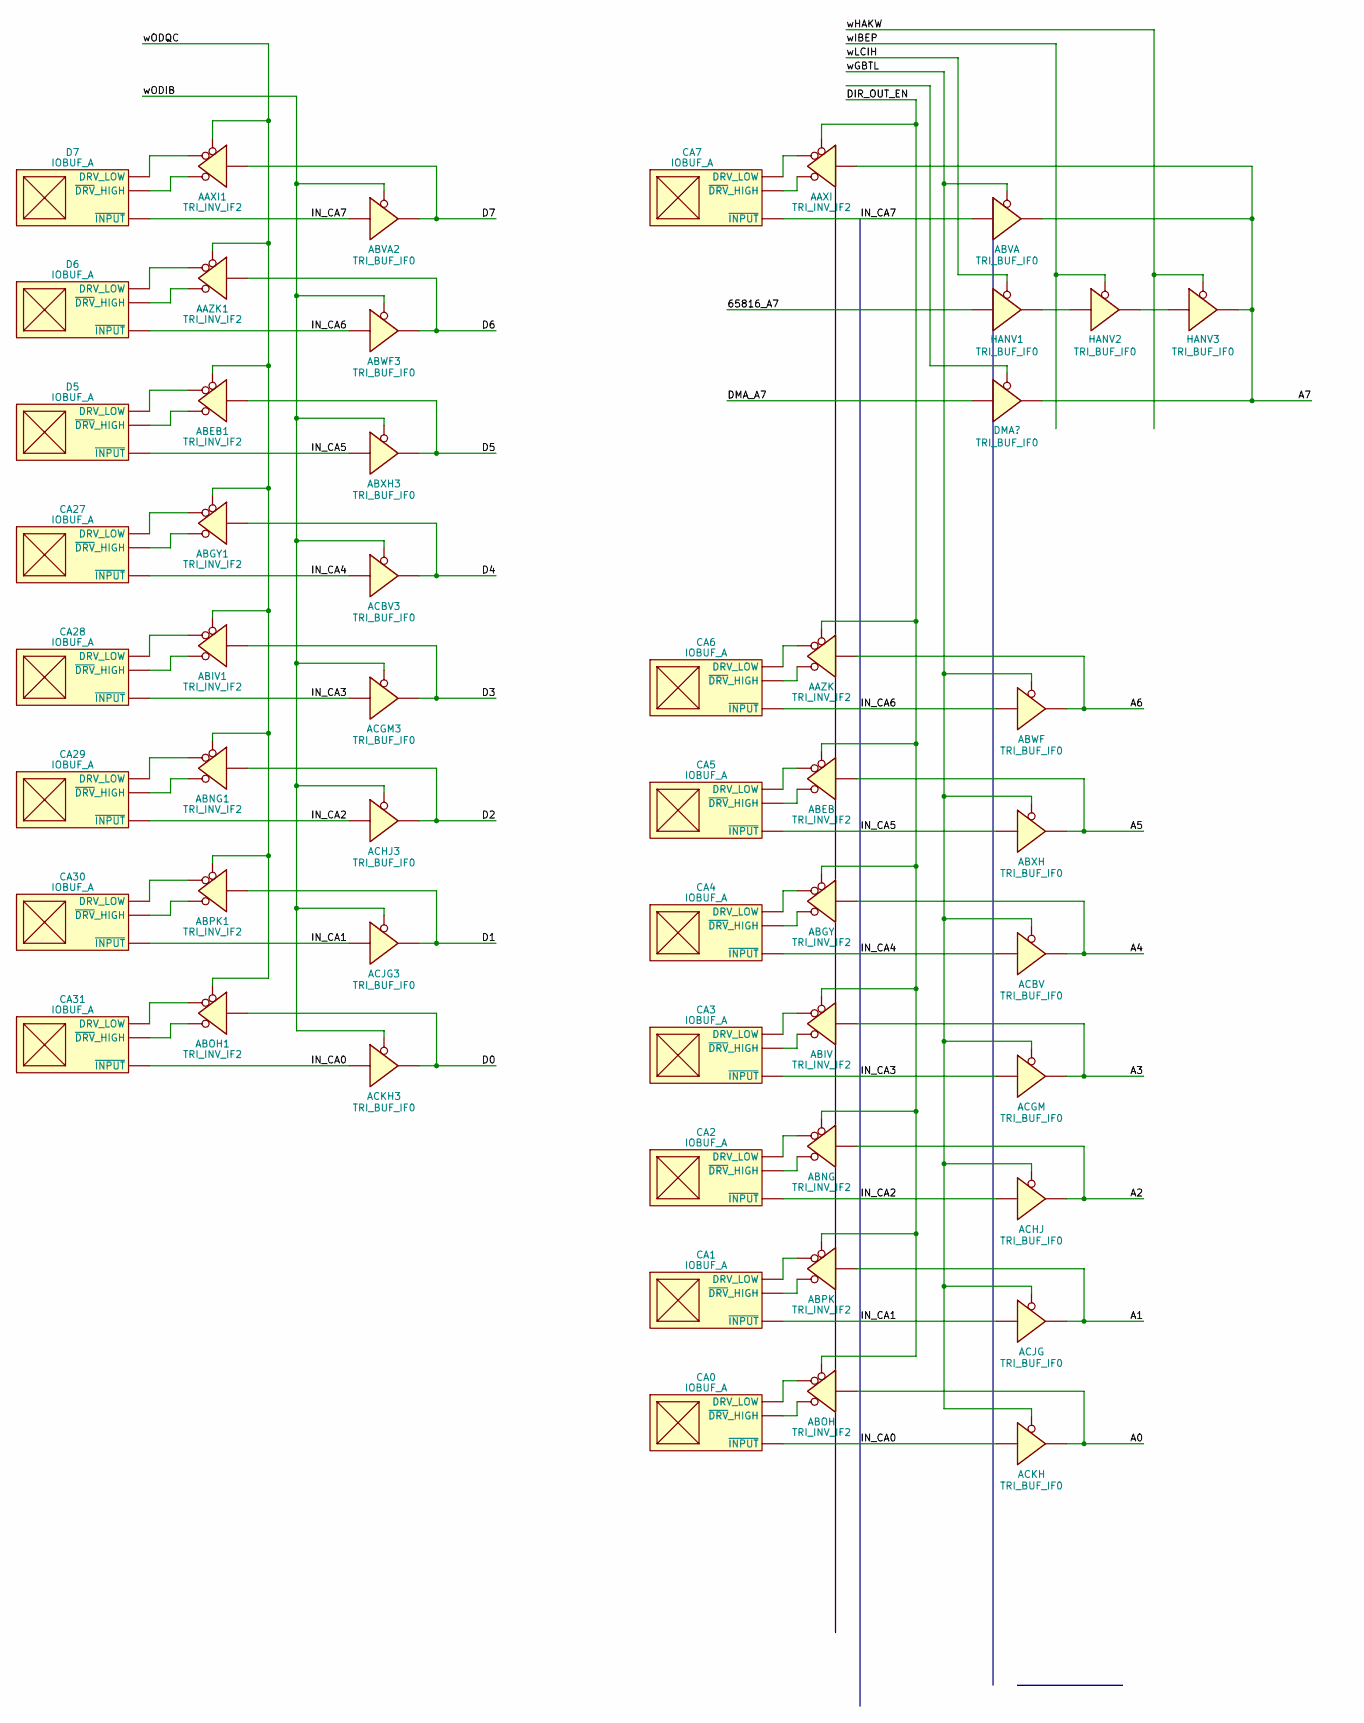
[picture p57: schematic addrdatabuses.kicad_sch, part in row 1, column 1]

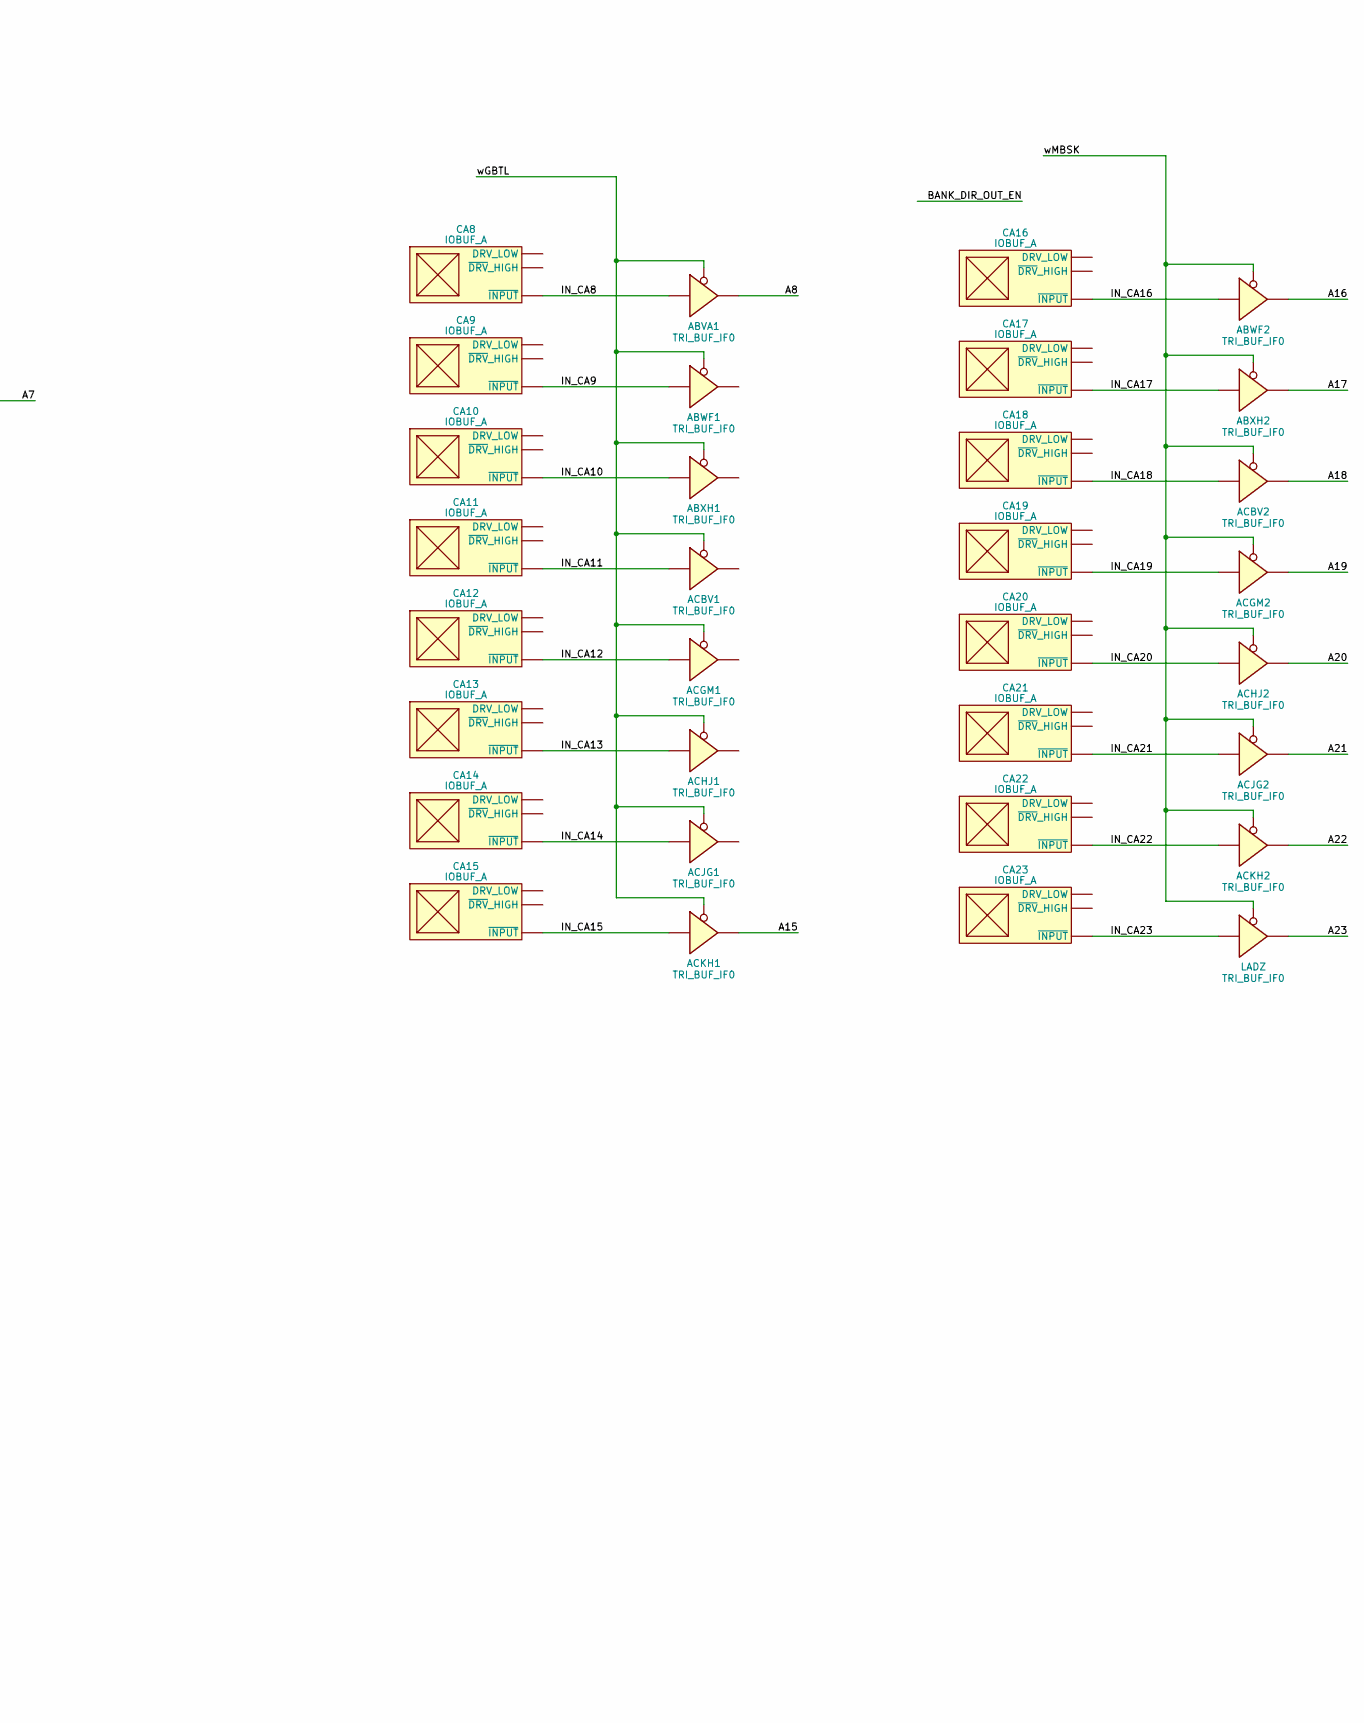
[picture p58: schematic addrdatabuses.kicad_sch, part in row 1, column 2]

Parts:
AAXI, AAXI1: TRI_INV_IF2
AAZK, AAZK1: TRI_INV_IF2
ABEB, ABEB1: TRI_INV_IF2
ABGY, ABGY1: TRI_INV_IF2
ABIV, ABIV1: TRI_INV_IF2
ABNG, ABNG1: TRI_INV_IF2
ABOH, ABOH1: TRI_INV_IF2
ABPK, ABPK1: TRI_INV_IF2
ABVA, ABVA1, ABVA2: TRI_BUF_IF0
ABWF, ABWF1, ABWF2, ABWF3: TRI_BUF_IF0
ABXH, ABXH1, ABXH2, ABXH3: TRI_BUF_IF0
ACBV, ACBV1, ACBV2, ACBV3: TRI_BUF_IF0
ACGM, ACGM1, ACGM2, ACGM3: TRI_BUF_IF0
ACHJ, ACHJ1, ACHJ2, ACHJ3: TRI_BUF_IF0
ACJG, ACJG1, ACJG2, ACJG3: TRI_BUF_IF0
ACKH, ACKH1, ACKH2, ACKH3: TRI_BUF_IF0
CA0, CA1, CA2, CA3, CA4, CA5, CA6, CA7, CA8, CA9, CA10, CA11, CA12, CA13, CA14, CA15, CA16, CA17, CA18, CA19, CA20, CA21, CA22, CA23, CA27, CA28, CA29, CA30, CA31: IOBUF_A
D5, D6, D7: IOBUF_A
HANV1, HANV2, HANV3: TRI_BUF_IF0
LADZ: TRI_BUF_IF0

Connections:
65816_A7: HANV1.1 (IN), HANV1.3 (IN)
A0: ABOH.2, ACKH.4
A1: ABPK.2, ACJG.4
A2: ABNG.2, ACHJ.4
A3: ABIV.2, ACGM.4
A4: ABGY.2, ACBV.4
A5: ABEB.2, ABXH.4
A6: AAZK.2, ABWF.4
A7: AAXI.2, ABVA.4, HANV3.4
A8: ABVA1.4
A15: ACKH1.4
A16: ABWF2.4
A17: ABXH2.4
A18: ACBV2.4
A19: ACGM2.4
A20: ACHJ2.4
A21: ACJG2.4
A22: ACKH2.4
A23: LADZ.4
D0: ABOH1.2, ACKH3.4
D1: ABPK1.2, ACJG3.4
D2: ABNG1.2, ACHJ3.4
D3: ABIV1.2, ACGM3.4
D4: ABGY1.2, ACBV3.4
D5: ABEB1.2, ABXH3.4
D6: AAZK1.2, ABWF3.4
D7: AAXI1.2, ABVA2.4
DIR_OUT_EN: AAXI.1 (~ENA), AAZK.1 (~ENA), ABEB.1 (~ENA), ABGY.1 (~ENA), ABIV.1 (~ENA), ABNG.1 (~ENA), ABOH.1 (~ENA), ABPK.1 (~ENA)
IN_CA0: ACKH.1 (IN), ACKH.3 (IN), ACKH3.1 (IN), ACKH3.3 (IN), CA0.2 (~INPUT), CA31.2 (~INPUT)
IN_CA1: ACJG.1 (IN), ACJG.3 (IN), ACJG3.1 (IN), ACJG3.3 (IN), CA1.2 (~INPUT), CA30.2 (~INPUT)
IN_CA2: ACHJ.1 (IN), ACHJ.3 (IN), ACHJ3.1 (IN), ACHJ3.3 (IN), CA2.2 (~INPUT), CA29.2 (~INPUT)
IN_CA3: ACGM.1 (IN), ACGM.3 (IN), ACGM3.1 (IN), ACGM3.3 (IN), CA3.2 (~INPUT), CA28.2 (~INPUT)
IN_CA4: ACBV.1 (IN), ACBV.3 (IN), ACBV3.1 (IN), ACBV3.3 (IN), CA4.2 (~INPUT), CA27.2 (~INPUT)
IN_CA5: ABXH.1 (IN), ABXH.3 (IN), ABXH3.1 (IN), ABXH3.3 (IN), CA5.2 (~INPUT), D5.2 (~INPUT)
IN_CA6: ABWF.1 (IN), ABWF.3 (IN), ABWF3.1 (IN), ABWF3.3 (IN), CA6.2 (~INPUT), D6.2 (~INPUT)
IN_CA7: ABVA.1 (IN), ABVA.3 (IN), ABVA2.1 (IN), ABVA2.3 (IN), CA7.2 (~INPUT), D7.2 (~INPUT)
IN_CA8: ABVA1.1 (IN), ABVA1.3 (IN), CA8.2 (~INPUT)
IN_CA9: ABWF1.1 (IN), ABWF1.3 (IN), CA9.2 (~INPUT)
IN_CA10: ABXH1.1 (IN), ABXH1.3 (IN), CA10.2 (~INPUT)
IN_CA11: ACBV1.1 (IN), ACBV1.3 (IN), CA11.2 (~INPUT)
IN_CA12: ACGM1.1 (IN), ACGM1.3 (IN), CA12.2 (~INPUT)
IN_CA13: ACHJ1.1 (IN), ACHJ1.3 (IN), CA13.2 (~INPUT)
IN_CA14: ACJG1.1 (IN), ACJG1.3 (IN), CA14.2 (~INPUT)
IN_CA15: ACKH1.1 (IN), ACKH1.3 (IN), CA15.2 (~INPUT)
IN_CA16: ABWF2.1 (IN), ABWF2.3 (IN), CA16.2 (~INPUT)
IN_CA17: ABXH2.1 (IN), ABXH2.3 (IN), CA17.2 (~INPUT)
IN_CA18: ACBV2.1 (IN), ACBV2.3 (IN), CA18.2 (~INPUT)
IN_CA19: ACGM2.1 (IN), ACGM2.3 (IN), CA19.2 (~INPUT)
IN_CA20: ACHJ2.1 (IN), ACHJ2.3 (IN), CA20.2 (~INPUT)
IN_CA21: ACJG2.1 (IN), ACJG2.3 (IN), CA21.2 (~INPUT)
IN_CA22: ACKH2.1 (IN), ACKH2.3 (IN), CA22.2 (~INPUT)
IN_CA23: CA23.2 (~INPUT), LADZ.1 (IN), LADZ.3 (IN)
unnamed: AAXI1.3, D7.1 (DRV_LOW), D7.3 (~DRV_HIGH)
unnamed: AAXI.3, CA7.1 (DRV_LOW), CA7.3 (~DRV_HIGH)
unnamed: AAZK1.3, D6.1 (DRV_LOW), D6.3 (~DRV_HIGH)
unnamed: AAZK.3, CA6.1 (DRV_LOW), CA6.3 (~DRV_HIGH)
unnamed: ABEB1.3, D5.1 (DRV_LOW), D5.3 (~DRV_HIGH)
unnamed: ABEB.3, CA5.1 (DRV_LOW), CA5.3 (~DRV_HIGH)
unnamed: ABGY1.3, CA27.1 (DRV_LOW), CA27.3 (~DRV_HIGH)
unnamed: ABGY.3, CA4.1 (DRV_LOW), CA4.3 (~DRV_HIGH)
unnamed: ABIV1.3, CA28.1 (DRV_LOW), CA28.3 (~DRV_HIGH)
unnamed: ABIV.3, CA3.1 (DRV_LOW), CA3.3 (~DRV_HIGH)
unnamed: ABNG1.3, CA29.1 (DRV_LOW), CA29.3 (~DRV_HIGH)
unnamed: ABNG.3, CA2.1 (DRV_LOW), CA2.3 (~DRV_HIGH)
unnamed: ABOH1.3, CA31.1 (DRV_LOW), CA31.3 (~DRV_HIGH)
unnamed: ABOH.3, CA0.1 (DRV_LOW), CA0.3 (~DRV_HIGH)
unnamed: ABPK1.3, CA30.1 (DRV_LOW), CA30.3 (~DRV_HIGH)
unnamed: ABPK.3, CA1.1 (DRV_LOW), CA1.3 (~DRV_HIGH)
unnamed: HANV1.4, HANV2.1 (IN), HANV2.3 (IN)
unnamed: HANV2.4, HANV3.1 (IN), HANV3.3 (IN)
wGBTL: ABVA.2 (~ENA), ABVA1.2 (~ENA), ABWF.2 (~ENA), ABWF1.2 (~ENA), ABXH.2 (~ENA), ABXH1.2 (~ENA), ACBV.2 (~ENA), ACBV1.2 (~ENA), ACGM.2 (~ENA), ACGM1.2 (~ENA), ACHJ.2 (~ENA), ACHJ1.2 (~ENA), ACJG.2 (~ENA), ACJG1.2 (~ENA), ACKH.2 (~ENA), ACKH1.2 (~ENA)
wHAKW: HANV3.2 (~ENA)
wIBEP: HANV2.2 (~ENA)
wLCIH: HANV1.2 (~ENA)
wMBSK: ABWF2.2 (~ENA), ABXH2.2 (~ENA), ACBV2.2 (~ENA), ACGM2.2 (~ENA), ACHJ2.2 (~ENA), ACJG2.2 (~ENA), ACKH2.2 (~ENA), LADZ.2 (~ENA)
wODIB: ABVA2.2 (~ENA), ABWF3.2 (~ENA), ABXH3.2 (~ENA), ACBV3.2 (~ENA), ACGM3.2 (~ENA), ACHJ3.2 (~ENA), ACJG3.2 (~ENA), ACKH3.2 (~ENA)
wODQC: AAXI1.1 (~ENA), AAZK1.1 (~ENA), ABEB1.1 (~ENA), ABGY1.1 (~ENA), ABIV1.1 (~ENA), ABNG1.1 (~ENA), ABOH1.1 (~ENA), ABPK1.1 (~ENA)
