rgalland/SNES_S-CPU_Schematics/S-CPU_kicad/addrdecod.kicad_sch

## KiCad design S-CPU_kicad/addrdecod.kicad_sch (2024-12-24, an earlier design)

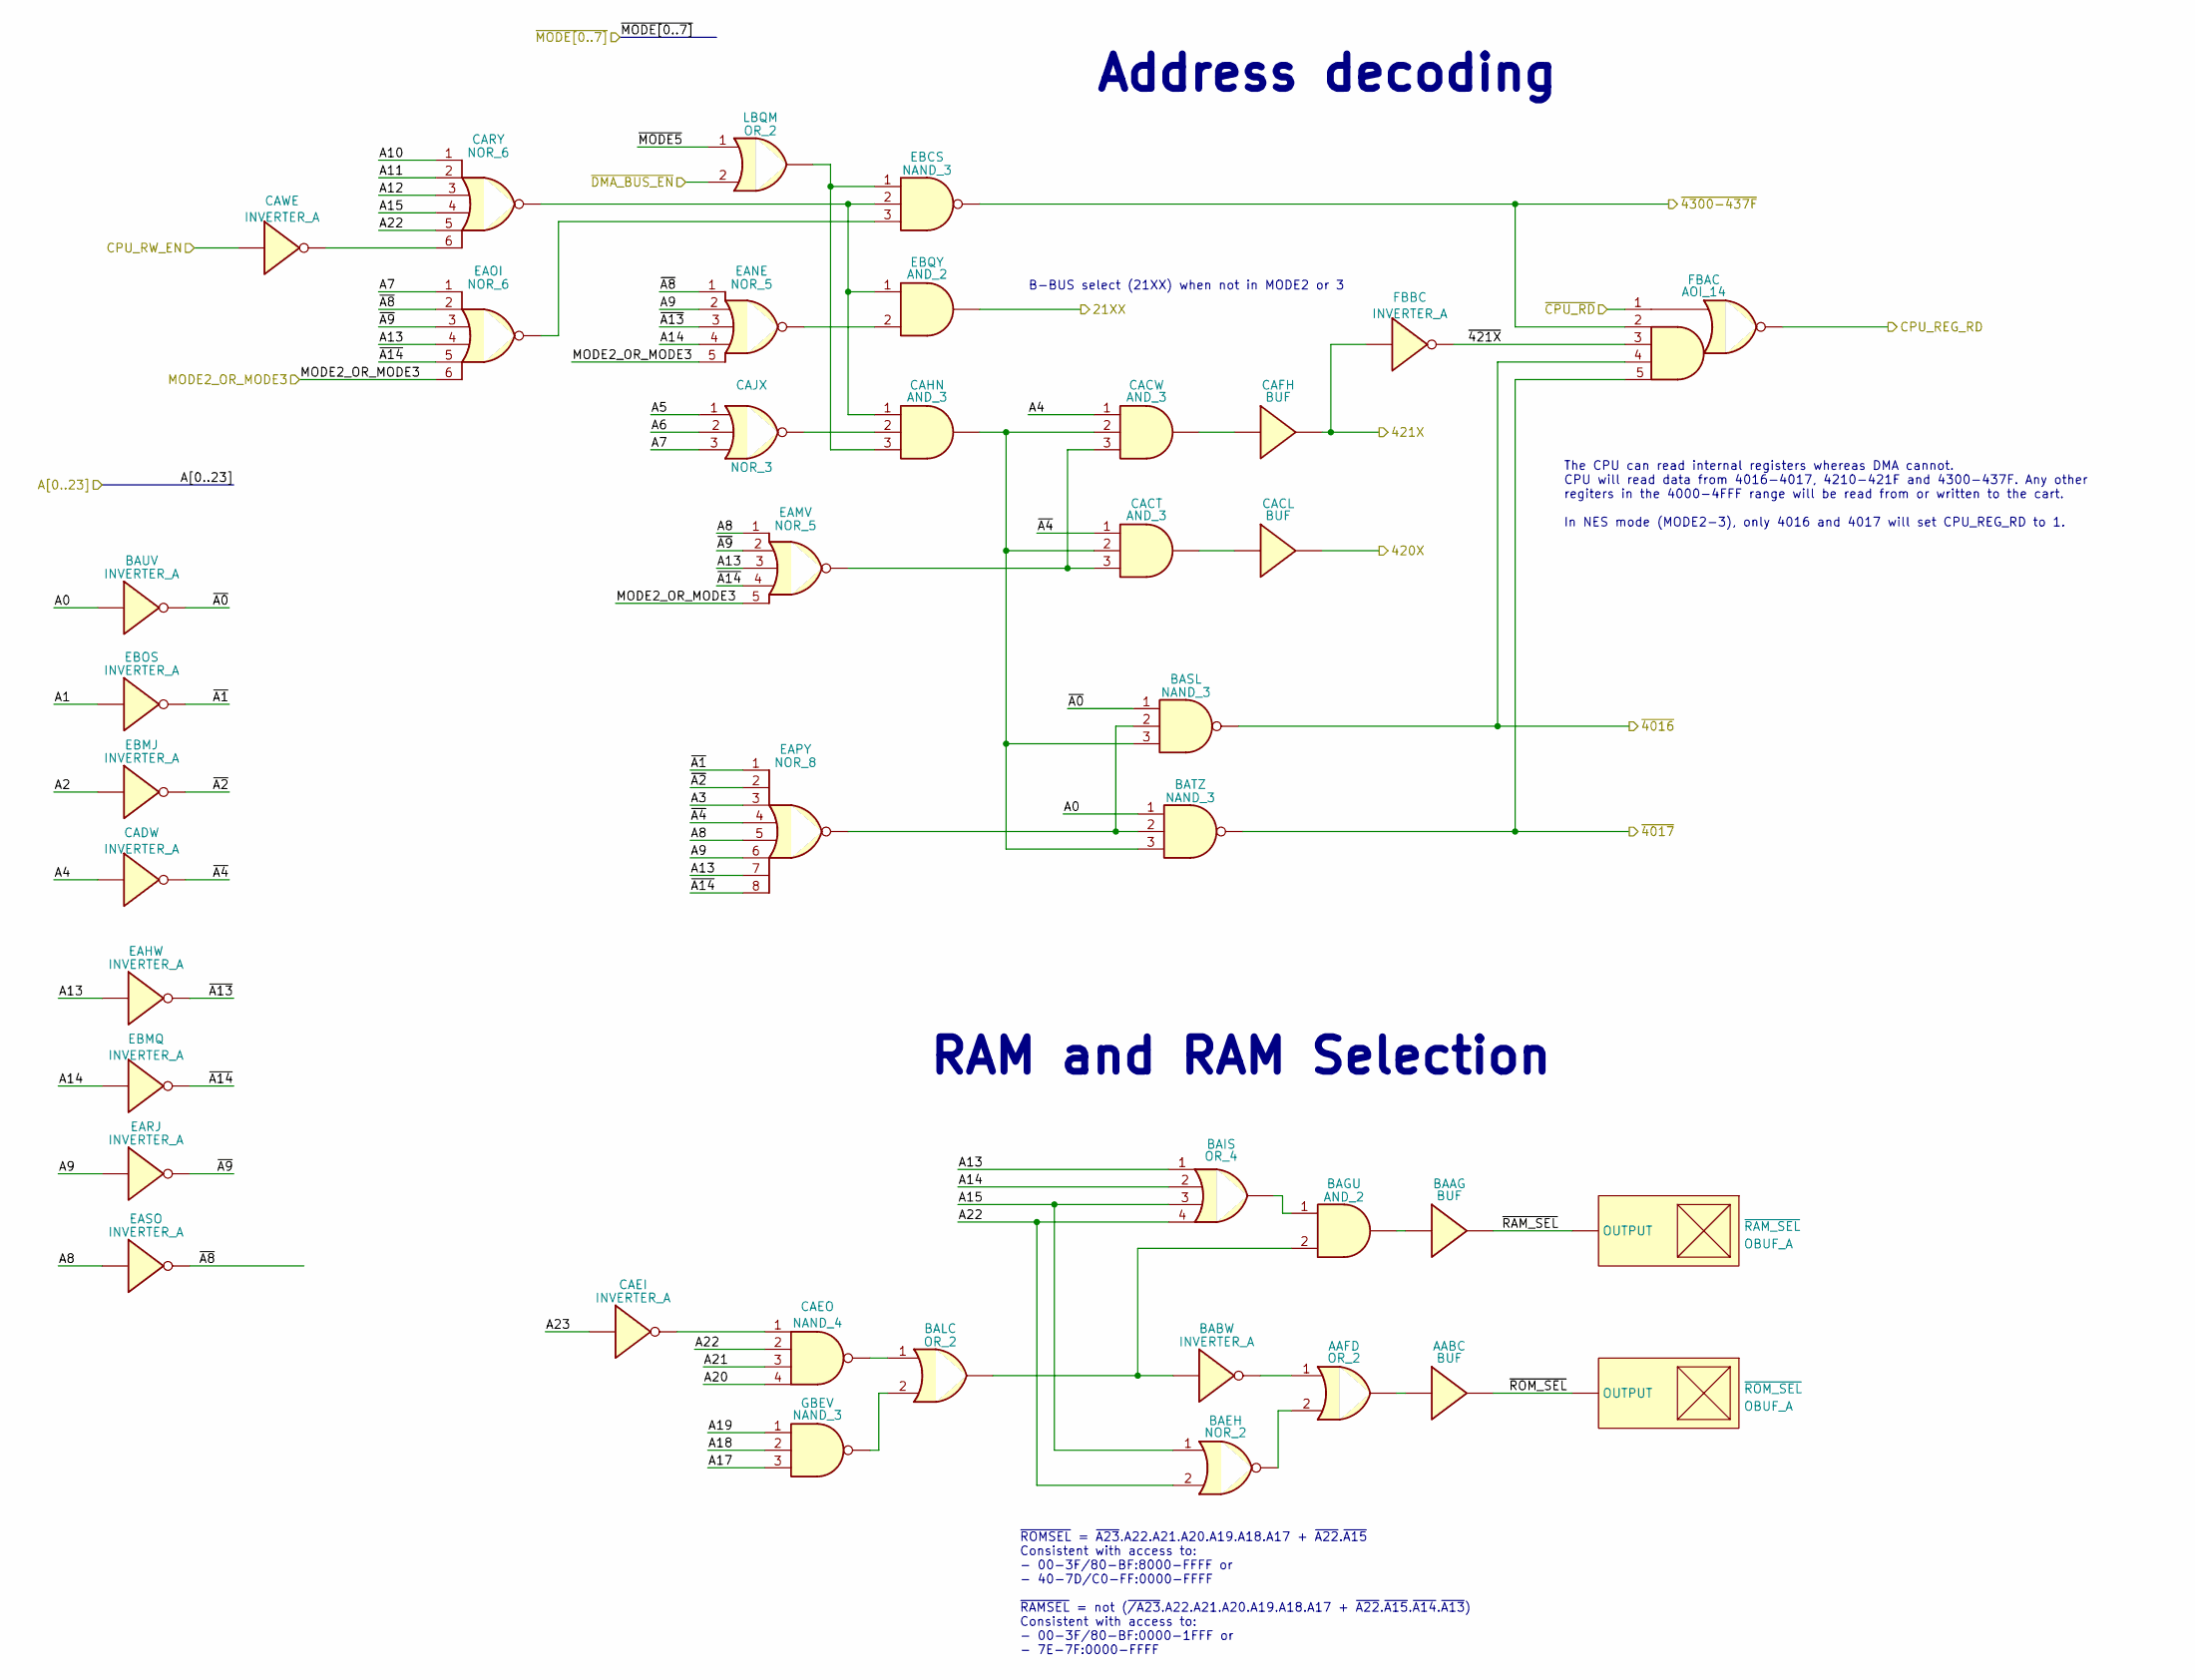
[picture p59: schematic addrdecod.kicad_sch]

Parts:
AABC: BUF
AAFD: OR_2
BAAG: BUF
BABW: INVERTER_A
BAEH: NOR_2
BAGU: AND_2
BAIS: OR_4
BALC: OR_2
BASL: NAND_3
BATZ: NAND_3
BAUV: INVERTER_A
CACL: BUF
CACT: AND_3
CACW: AND_3
CADW: INVERTER_A
CAEI: INVERTER_A
CAEO: NAND_4
CAFH: BUF
CAHN: AND_3
CAJX: NOR_3
CARY: NOR_6
CAWE: INVERTER_A
EAHW: INVERTER_A
EAMV: NOR_5
EANE: NOR_5
EAOI: NOR_6
EAPY: NOR_8
EARJ: INVERTER_A
EASO: INVERTER_A
EBCS: NAND_3
EBMJ: INVERTER_A
EBMQ: INVERTER_A
EBOS: INVERTER_A
EBQY: AND_2
FBAC: AOI_14
FBBC: INVERTER_A
GBEV: NAND_3
LBQM: OR_2
~{RAM_SEL}: OBUF_A
~{ROM_SEL}: OBUF_A

Connections:
21XX: EBQY.3
420X: CACL.2
421X: CAFH.2, FBBC.1
A0: BATZ.1, BAUV.1
A1: EBOS.1
A2: EBMJ.1
A3: EAPY.3
A4: CACW.1, CADW.1
A5: CAJX.1
A6: CAJX.2
A7: CAJX.3, EAOI.1
A8: EAMV.1, EAPY.5, EASO.1
A9: EANE.2, EAPY.6, EARJ.1
A10: CARY.1
A11: CARY.2
A12: CARY.3
A13: BAIS.1, EAHW.1, EAMV.3, EAOI.4, EAPY.7
A14: BAIS.2, EANE.4, EBMQ.1
A15: BAEH.1, BAIS.3, CARY.4
A17: GBEV.3
A18: GBEV.2
A19: GBEV.1
A20: CAEO.4
A21: CAEO.3
A22: BAEH.2, BAIS.4, CAEO.2, CARY.5
A23: CAEI.1
CPU_REG_RD: FBAC.3
CPU_RW_EN: CAWE.1
MODE2_OR_MODE3: EAMV.5, EANE.5, EAOI.6
unnamed: AABC.1, AAFD.3
unnamed: AAFD.1, BABW.2
unnamed: AAFD.2, BAEH.3
unnamed: BAAG.1, BAGU.3
unnamed: BABW.1, BAGU.2, BALC.3
unnamed: BAGU.1, BAIS.5
unnamed: BALC.1, CAEO.5
unnamed: BALC.2, GBEV.4
unnamed: BASL.2, BATZ.2, EAPY.9
unnamed: BASL.3, BATZ.3, CACT.2, CACW.2, CAHN.4
unnamed: CACL.1, CACT.4
unnamed: CACT.3, CACW.3, EAMV.6
unnamed: CACW.4, CAFH.1
unnamed: CAEI.2, CAEO.1
unnamed: CAHN.1, CARY.7, EBCS.2, EBQY.1
unnamed: CAHN.2, CAJX.4
unnamed: CAHN.3, EBCS.1, LBQM.3
unnamed: CARY.6, CAWE.2
unnamed: EANE.6, EBQY.2
unnamed: EAOI.7, EBCS.3
~421X: FBAC.3, FBBC.2
~4016: BASL.4, FBAC.4
~4017: BATZ.4, FBAC.5
~4300-437F: EBCS.4, FBAC.2
~A0: BASL.1, BAUV.2
~A1: EAPY.1, EBOS.2
~A2: EAPY.2, EBMJ.2
~A4: CACT.1, CADW.2, EAPY.4
~A8: EANE.1, EAOI.2, EASO.2
~A9: EAMV.2, EAOI.3, EARJ.2
~A13: EAHW.2, EANE.3
~A14: EAMV.4, EAOI.5, EAPY.8, EBMQ.2
~CPU_RD: FBAC.1
~DMA_BUS_EN: LBQM.2
~MODE5: LBQM.1
~RAM_SEL: BAAG.2, ~{RAM_SEL}.1
~ROM_SEL: AABC.2, ~{ROM_SEL}.1

Notes on the sheet:
B-BUS select (21XX) when not in MODE2 or 3
The CPU can read internal registers whereas DMA cannot. CPU will read data from 4016-4017, 4210-421F and 4300-437F. Any other regiters in the 4000-4FFF range will be read from or written to the cart. In NES mode (MODE2-3), only 4016 and 4017 will set CPU_REG_RD to 1.
Address decoding
RAM and RAM Selection
~{ROMSEL} = ~{A23}.A22.A21.A20.A19.A18.A17 + ~{A22}.~{A15} Consistent with access to: - 00-3F/80-BF:8000-FFFF or - 40-7D/C0-FF:0000-FFFF ~{RAMSEL} = not (~{/A23}.A22.A21.A20.A19.A18.A17 + ~{A22}.~{A15}.~{A14}.~{A13}) Consistent with access to: - 00-3F/80-BF:0000-1FFF or - 7E-7F:0000-FFFF
