rgalland/SNES_S-CPU_Schematics/S-CPU_kicad/bbus.kicad_sch

## KiCad design S-CPU_kicad/bbus.kicad_sch (2024-12-24, an earlier design)

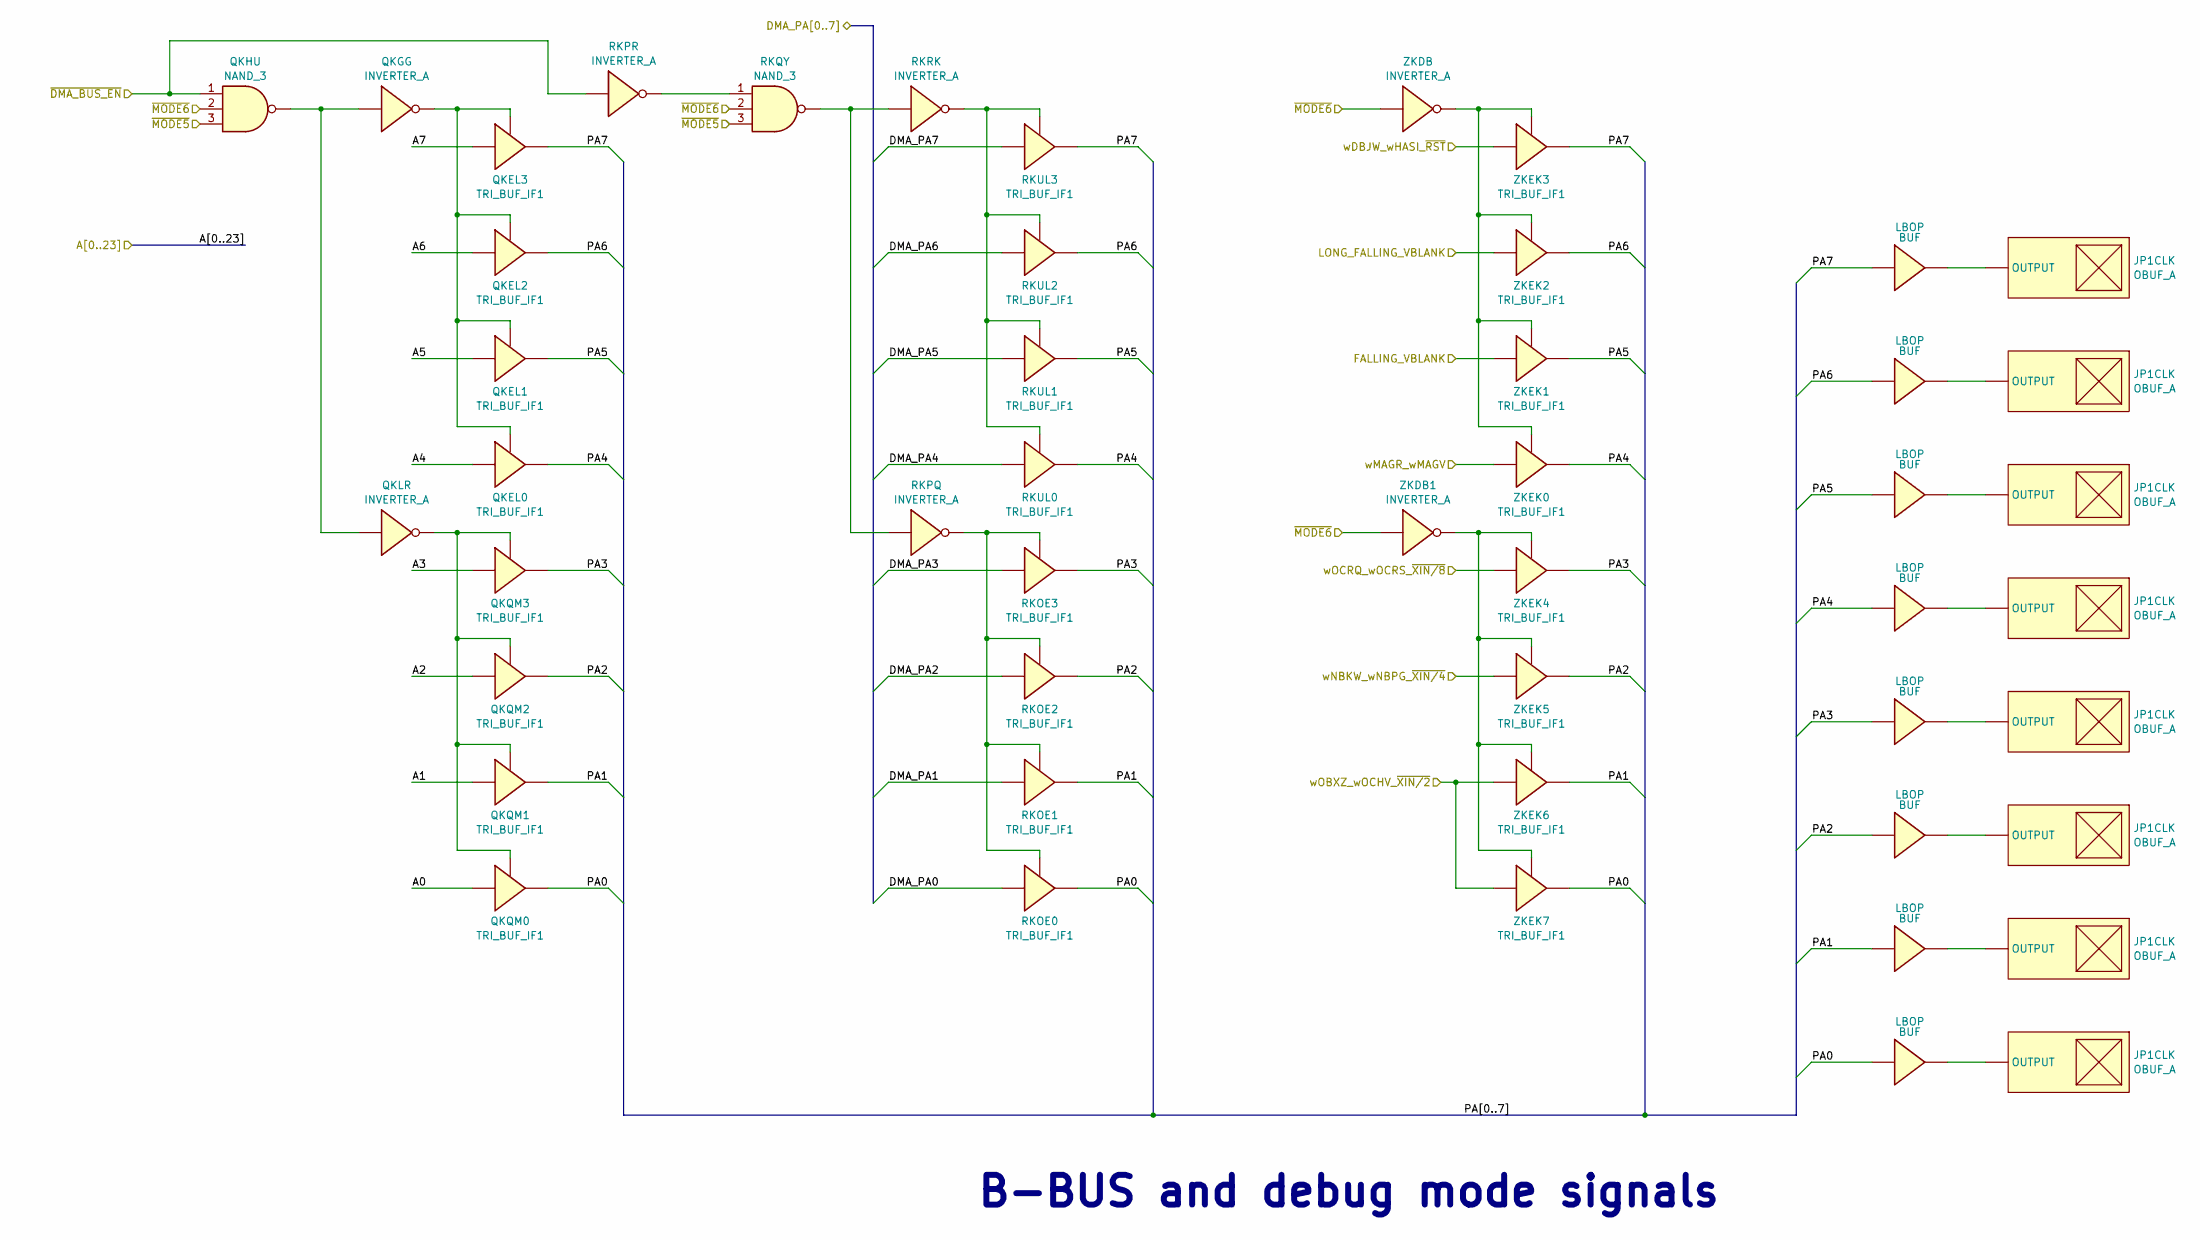
[picture p60: schematic bbus.kicad_sch]

Parts:
JP1CLK: OBUF_A
LBOP: BUF
QKEL0, QKEL1, QKEL2, QKEL3: TRI_BUF_IF1
QKGG: INVERTER_A
QKHU: NAND_3
QKLR: INVERTER_A
QKQM0, QKQM1, QKQM2, QKQM3: TRI_BUF_IF1
RKOE0, RKOE1, RKOE2, RKOE3: TRI_BUF_IF1
RKPQ: INVERTER_A
RKPR: INVERTER_A
RKQY: NAND_3
RKRK: INVERTER_A
RKUL0, RKUL1, RKUL2, RKUL3: TRI_BUF_IF1
ZKDB, ZKDB1: INVERTER_A
ZKEK0, ZKEK1, ZKEK2, ZKEK3, ZKEK4, ZKEK5, ZKEK6, ZKEK7: TRI_BUF_IF1

Connections:
A0: QKQM0.1 (IN), QKQM0.3 (IN)
A1: QKQM1.1 (IN), QKQM1.3 (IN)
A2: QKQM2.1 (IN), QKQM2.3 (IN)
A3: QKQM3.1 (IN), QKQM3.3 (IN)
A4: QKEL0.1 (IN), QKEL0.3 (IN)
A5: QKEL1.1 (IN), QKEL1.3 (IN)
A6: QKEL2.1 (IN), QKEL2.3 (IN)
A7: QKEL3.1 (IN), QKEL3.3 (IN)
DMA_PA0: RKOE0.1 (IN), RKOE0.3 (IN)
DMA_PA1: RKOE1.1 (IN), RKOE1.3 (IN)
DMA_PA2: RKOE2.1 (IN), RKOE2.3 (IN)
DMA_PA3: RKOE3.1 (IN), RKOE3.3 (IN)
DMA_PA4: RKUL0.1 (IN), RKUL0.3 (IN)
DMA_PA5: RKUL1.1 (IN), RKUL1.3 (IN)
DMA_PA6: RKUL2.1 (IN), RKUL2.3 (IN)
DMA_PA7: RKUL3.1 (IN), RKUL3.3 (IN)
FALLING_VBLANK: ZKEK1.1 (IN), ZKEK1.3 (IN)
LONG_FALLING_VBLANK: ZKEK2.1 (IN), ZKEK2.3 (IN)
unnamed: JP1CLK.1, LBOP.2
unnamed: QKEL0.2 (~ENA), QKEL1.2 (~ENA), QKEL2.2 (~ENA), QKEL3.2 (~ENA), QKGG.2
unnamed: QKGG.1, QKHU.4, QKLR.1
unnamed: QKLR.2, QKQM0.2 (~ENA), QKQM1.2 (~ENA), QKQM2.2 (~ENA), QKQM3.2 (~ENA)
unnamed: RKOE0.2 (~ENA), RKOE1.2 (~ENA), RKOE2.2 (~ENA), RKOE3.2 (~ENA), RKPQ.2
unnamed: RKPQ.1, RKQY.4, RKRK.1
unnamed: RKPR.2, RKQY.1
unnamed: RKRK.2, RKUL0.2 (~ENA), RKUL1.2 (~ENA), RKUL2.2 (~ENA), RKUL3.2 (~ENA)
unnamed: ZKDB1.2, ZKEK4.2 (~ENA), ZKEK5.2 (~ENA), ZKEK6.2 (~ENA), ZKEK7.2 (~ENA)
unnamed: ZKDB.2, ZKEK0.2 (~ENA), ZKEK1.2 (~ENA), ZKEK2.2 (~ENA), ZKEK3.2 (~ENA)
PA0: LBOP.1, QKQM0.4, RKOE0.4, ZKEK7.4
PA1: LBOP.1, QKQM1.4, RKOE1.4, ZKEK6.4
PA2: LBOP.1, QKQM2.4, RKOE2.4, ZKEK5.4
PA3: LBOP.1, QKQM3.4, RKOE3.4, ZKEK4.4
PA4: LBOP.1, QKEL0.4, RKUL0.4, ZKEK0.4
PA5: LBOP.1, QKEL1.4, RKUL1.4, ZKEK1.4
PA6: LBOP.1, QKEL2.4, RKUL2.4, ZKEK2.4
PA7: LBOP.1, QKEL3.4, RKUL3.4, ZKEK3.4
wDBJW_wHASI_~RST: ZKEK3.1 (IN), ZKEK3.3 (IN)
wMAGR_wMAGV: ZKEK0.1 (IN), ZKEK0.3 (IN)
wNBKW_wNBPG_~XIN/4: ZKEK5.1 (IN), ZKEK5.3 (IN)
wOBXZ_wOCHV_~XIN/2: ZKEK6.1 (IN), ZKEK6.3 (IN), ZKEK7.1 (IN), ZKEK7.3 (IN)
wOCRQ_wOCRS_~XIN/8: ZKEK4.1 (IN), ZKEK4.3 (IN)
~DMA_BUS_EN: QKHU.1, RKPR.1
~MODE5: QKHU.3, RKQY.3
~MODE6: QKHU.2, RKQY.2, ZKDB.1, ZKDB1.1

Notes on the sheet:
B-BUS and debug mode signals
