rgalland/SNES_S-CPU_Schematics/S-CPU_kicad/buscontrol.kicad_sch

## KiCad design S-CPU_kicad/buscontrol.kicad_sch (2024-12-24, an earlier design)

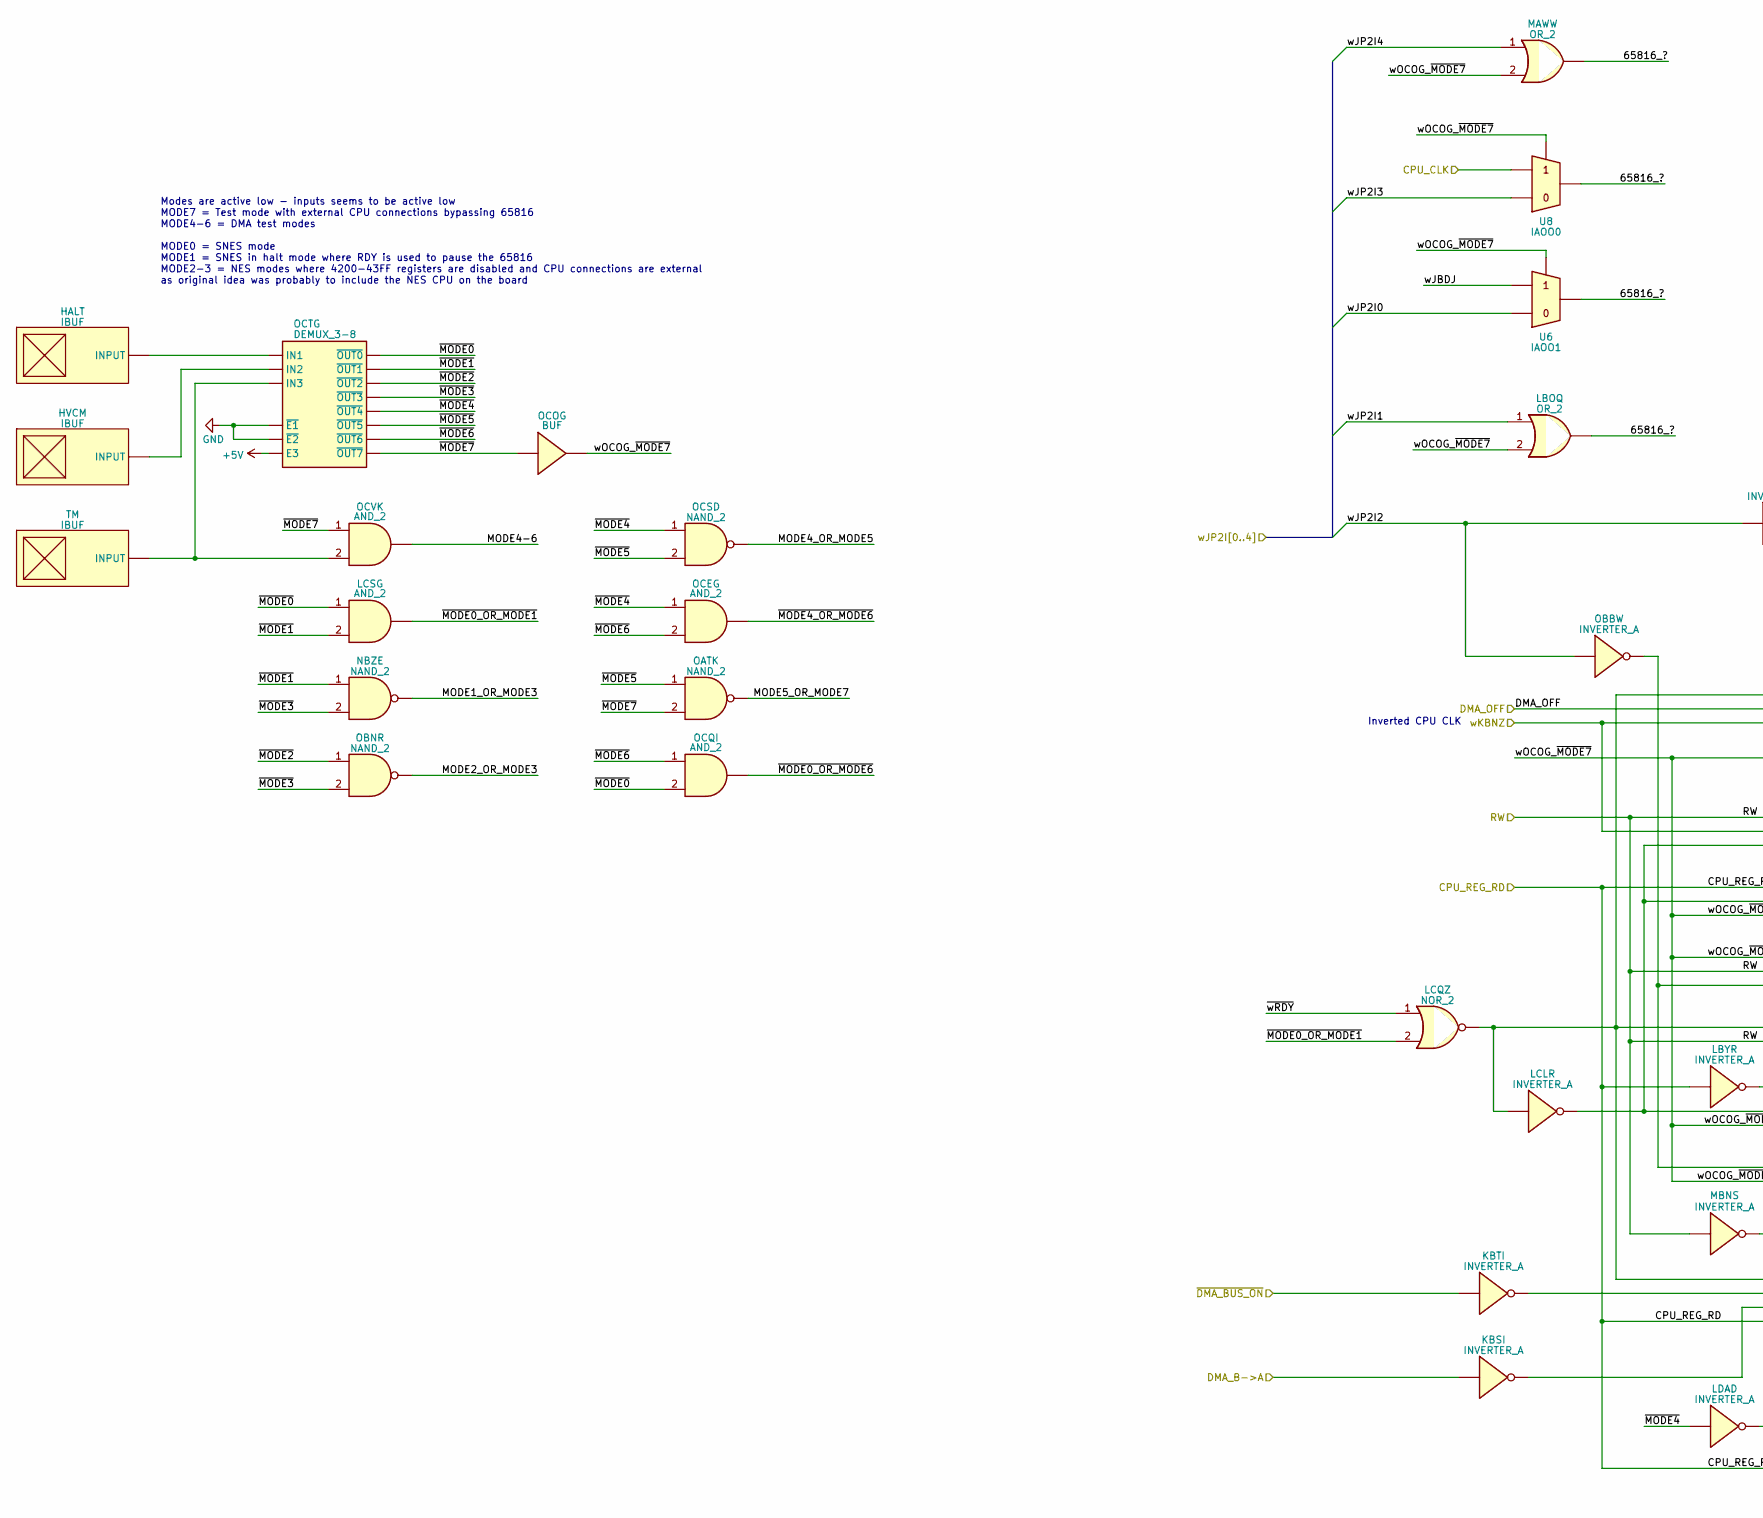
[picture p61: schematic buscontrol.kicad_sch, part in row 1, column 1]

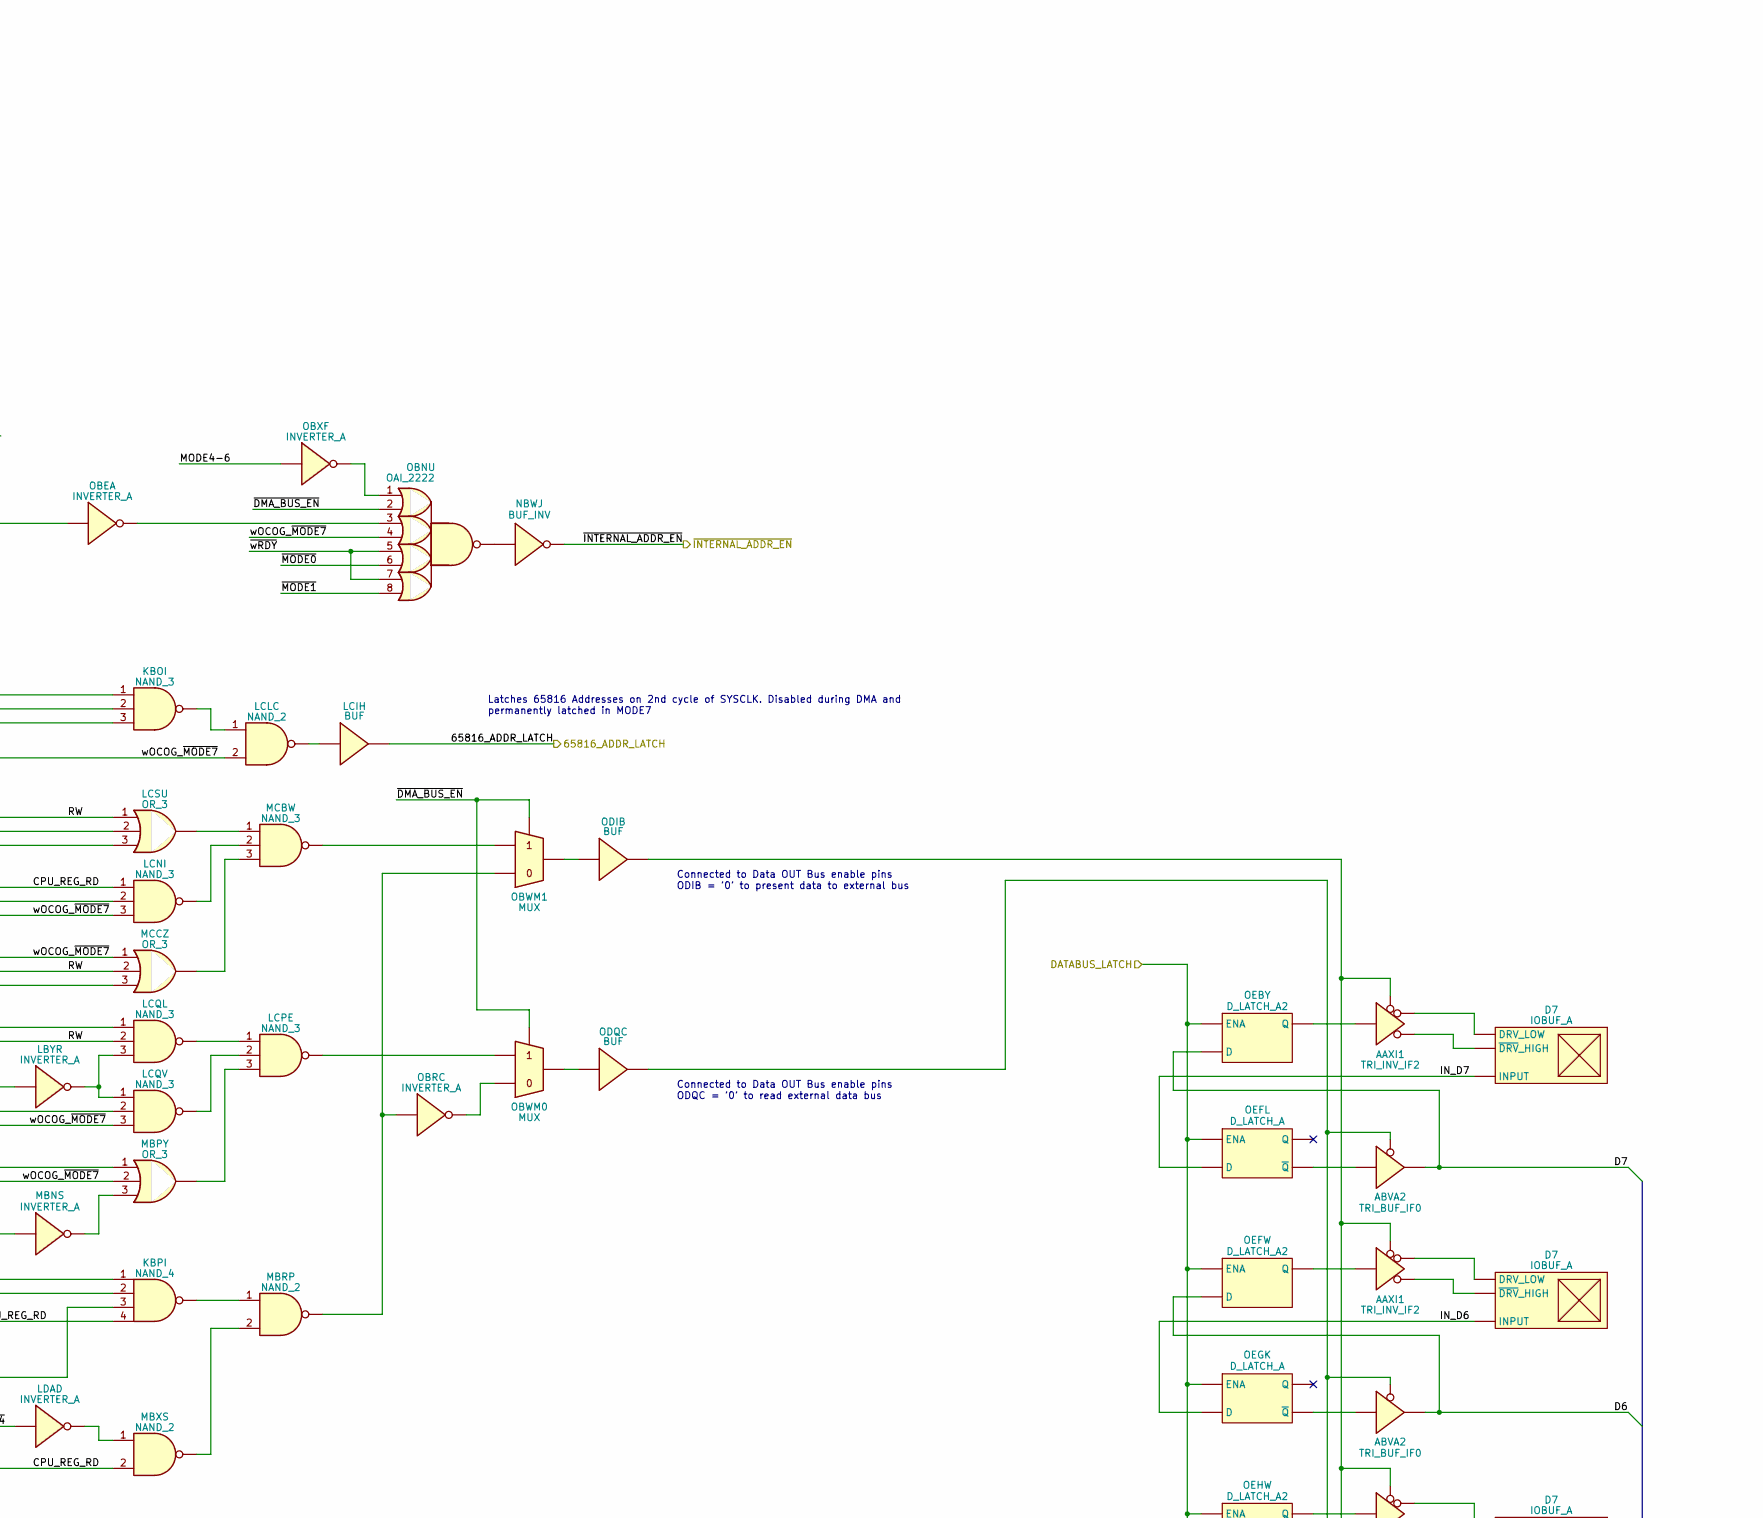
[picture p62: schematic buscontrol.kicad_sch, part in row 1, column 2]

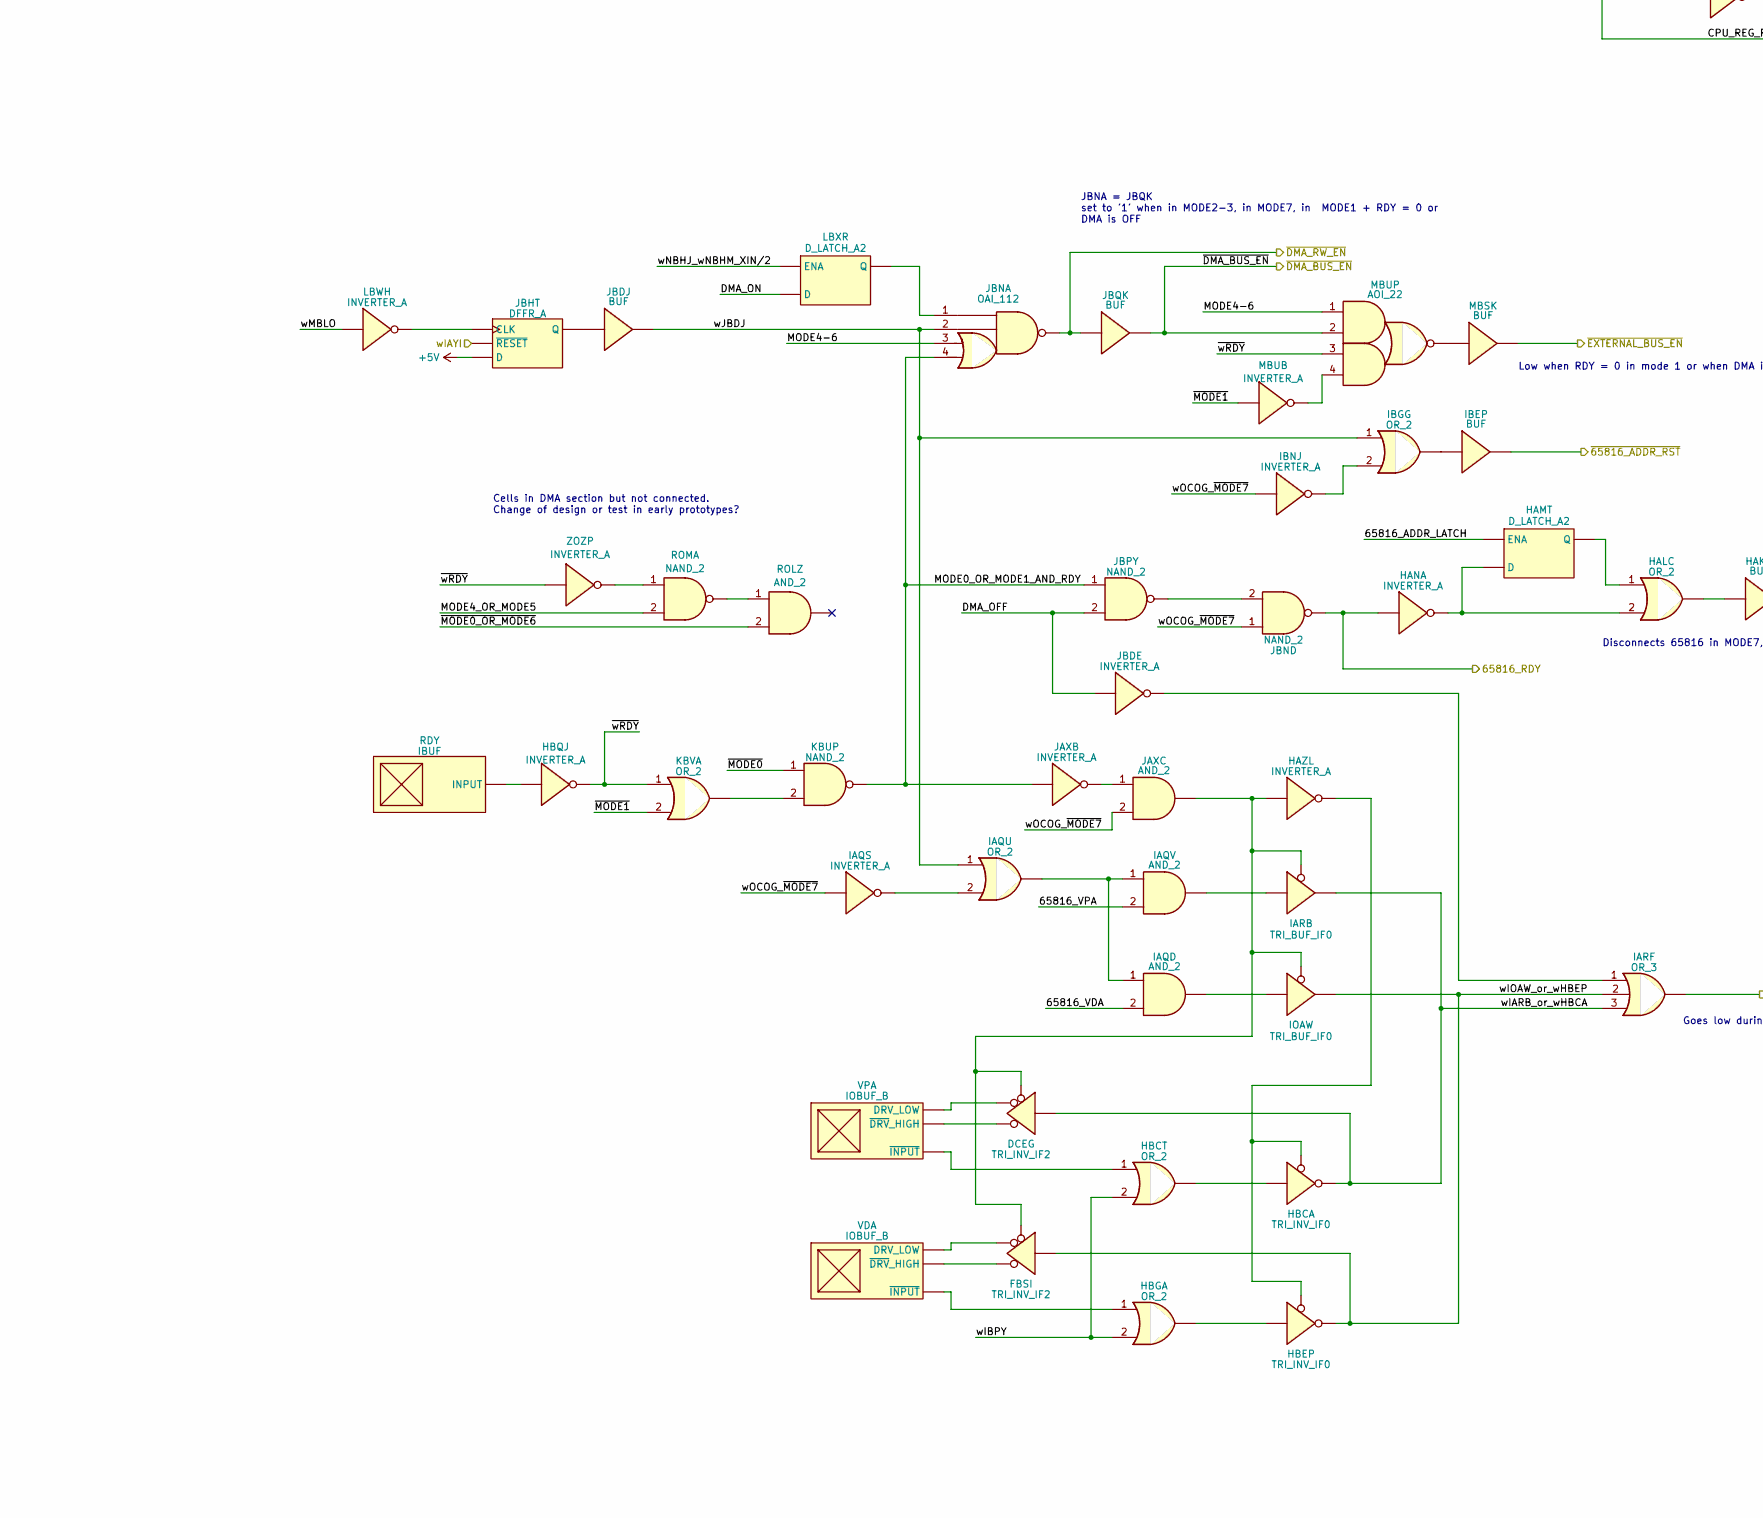
[picture p63: schematic buscontrol.kicad_sch, part in row 2, column 1]

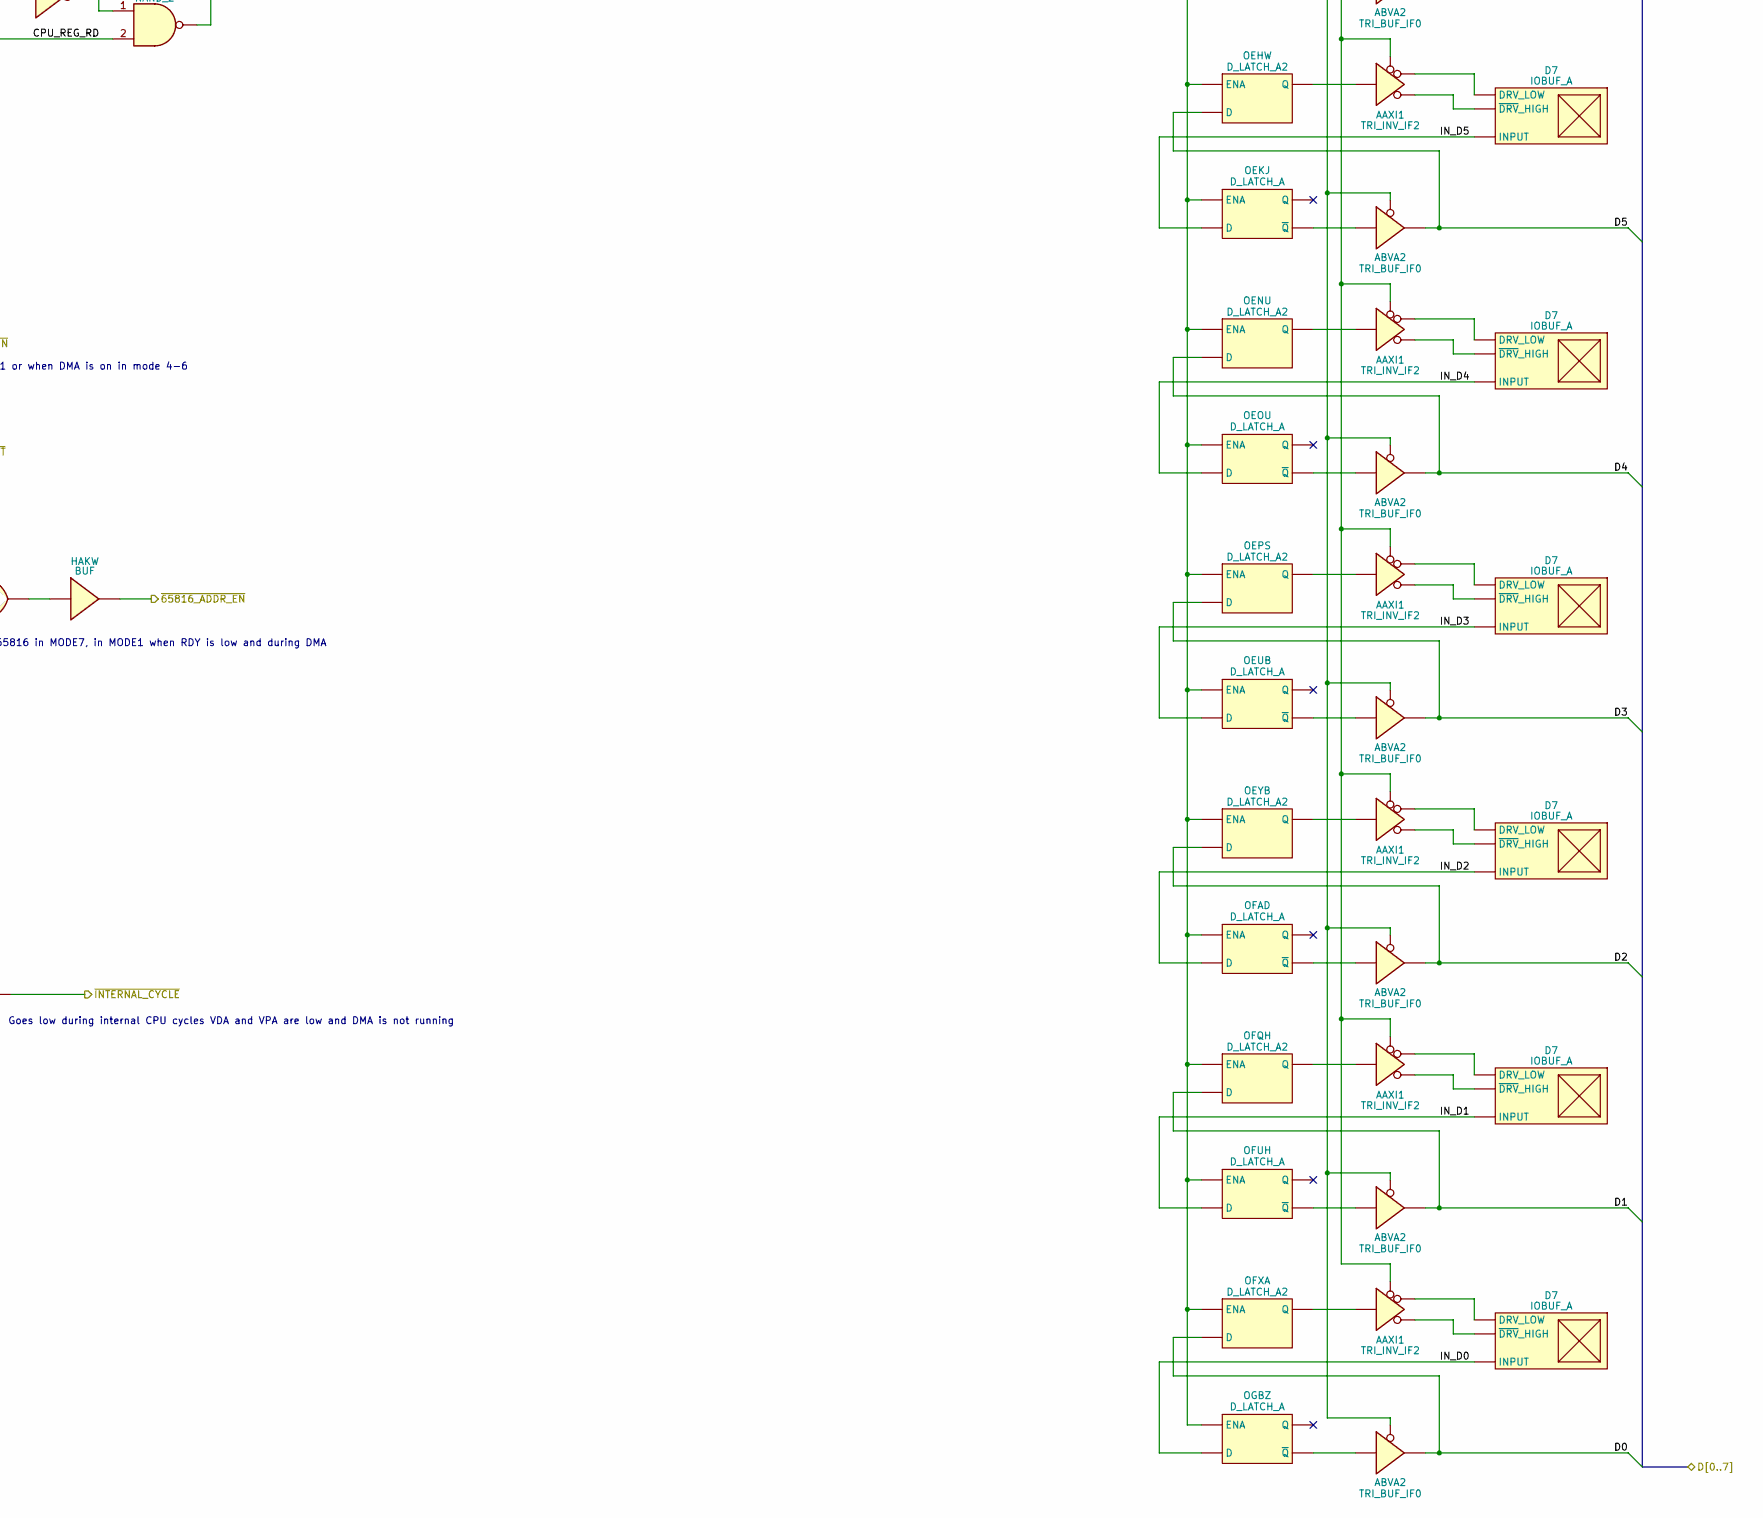
[picture p64: schematic buscontrol.kicad_sch, part in row 2, column 2]

Parts:
AAXI1: TRI_INV_IF2
ABVA2: TRI_BUF_IF0
D7: IOBUF_A
DCEG: TRI_INV_IF2
FBSI: TRI_INV_IF2
HAKW: BUF
HALC: OR_2
HALT: IBUF
HAMT: D_LATCH_A2
HANA: INVERTER_A
HAZL: INVERTER_A
HBCA: TRI_INV_IF0
HBCT: OR_2
HBEP: TRI_INV_IF0
HBGA: OR_2
HBQJ: INVERTER_A
HVCM: IBUF
IAQD: AND_2
IAQS: INVERTER_A
IAQU: OR_2
IAQV: AND_2
IARB: TRI_BUF_IF0
IARF: OR_3
IBEP: BUF
IBGG: OR_2
IBNJ: INVERTER_A
IOAW: TRI_BUF_IF0
JAXB: INVERTER_A
JAXC: AND_2
JBDE: INVERTER_A
JBDJ: BUF
JBHT: DFFR_A
JBNA: OAI_112
JBND: NAND_2
JBPY: NAND_2
JBQK: BUF
KBOI: NAND_3
KBPI: NAND_4
KBSI: INVERTER_A
KBTI: INVERTER_A
KBUP: NAND_2
KBVA: OR_2
LBOQ: OR_2
LBWH: INVERTER_A
LBXR: D_LATCH_A2
LBYR: INVERTER_A
LCIH: BUF
LCLC: NAND_2
LCLR: INVERTER_A
LCNI: NAND_3
LCPE: NAND_3
LCQL: NAND_3
LCQV: NAND_3
LCQZ: NOR_2
LCSG: AND_2
LCSU: OR_3
LDAD: INVERTER_A
MAWW: OR_2
MBNS: INVERTER_A
MBPY: OR_3
MBRP: NAND_2
MBSK: BUF
MBUB: INVERTER_A
MBUP: AOI_22
MBXS: NAND_2
MCBW: NAND_3
MCCZ: OR_3
NBWJ: BUF_INV
NBZE: NAND_2
OATK: NAND_2
OBBW: INVERTER_A
OBEA: INVERTER_A
OBNR: NAND_2
OBNU: OAI_2222
OBRC: INVERTER_A
OBWM0, OBWM1: MUX
OBXF: INVERTER_A
OCEG: AND_2
OCOG: BUF
OCQI: AND_2
OCSD: NAND_2
OCTG: DEMUX_3-8
OCVK: AND_2
ODIB: BUF
ODQC: BUF
OEBY: D_LATCH_A2
OEFL: D_LATCH_A
OEFW: D_LATCH_A2
OEGK: D_LATCH_A
OEHW: D_LATCH_A2
OEKJ: D_LATCH_A
OENU: D_LATCH_A2
OEOU: D_LATCH_A
OEPS: D_LATCH_A2
OEUB: D_LATCH_A
OEYB: D_LATCH_A2
OFAD: D_LATCH_A
OFQH: D_LATCH_A2
OFUH: D_LATCH_A
OFXA: D_LATCH_A2
OGBZ: D_LATCH_A
RDY: IBUF
ROLZ: AND_2
ROMA: NAND_2
TM: IBUF
U6: IAOO1
U8: IAOO0
VDA: IOBUF_B
VPA: IOBUF_B
ZOZP: INVERTER_A

Connections:
65816_?: LBOQ.3, MAWW.3, U6.4, U8.4
65816_ADDR_LATCH: HAMT.1 (~ENA), HAMT.3 (ENA), LCIH.2
65816_RDY: HANA.1, JBND.3
65816_VDA: IAQD.2
65816_VPA: IAQV.2
+5V: JBHT.2 (D), OCTG.
CPU_CLK: U8.2
CPU_REG_RD: KBPI.4, LBYR.1, LCNI.1, MBXS.2
D0: ABVA2.4, OFXA.2 (D)
D1: ABVA2.4, OFQH.2 (D)
D2: ABVA2.4, OEYB.2 (D)
D3: ABVA2.4, OEPS.2 (D)
D4: ABVA2.4, OENU.2 (D)
D5: ABVA2.4, OEHW.2 (D)
D6: ABVA2.4, OEFW.2 (D)
D7: ABVA2.4, OEBY.2 (D)
DATABUS_LATCH: OEBY.1 (~ENA), OEBY.3 (ENA), OEFL.1 (~ENA), OEFL.3 (ENA), OEFW.1 (~ENA), OEFW.3 (ENA), OEGK.1 (~ENA), OEGK.3 (ENA), OEHW.1 (~ENA), OEHW.3 (ENA), OEKJ.1 (~ENA), OEKJ.3 (ENA), OENU.1 (~ENA), OENU.3 (ENA), OEOU.1 (~ENA), OEOU.3 (ENA), OEPS.1 (~ENA), OEPS.3 (ENA), OEUB.1 (~ENA), OEUB.3 (ENA), OEYB.1 (~ENA), OEYB.3 (ENA), OFAD.1 (~ENA), OFAD.3 (ENA), OFQH.1 (~ENA), OFQH.3 (ENA), OFUH.1 (~ENA), OFUH.3 (ENA), OFXA.1 (~ENA), OFXA.3 (ENA), OGBZ.1 (~ENA), OGBZ.3 (ENA)
DMA_B->A: KBSI.1
DMA_OFF: JBDE.1, JBPY.2, KBOI.2
DMA_ON: LBXR.2 (D)
GND: OCTG.
IN_D0: D7.2 (INPUT), OGBZ.2 (D)
IN_D1: D7.2 (INPUT), OFUH.2 (D)
IN_D2: D7.2 (INPUT), OFAD.2 (D)
IN_D3: D7.2 (INPUT), OEUB.2 (D)
IN_D4: D7.2 (INPUT), OEOU.2 (D)
IN_D5: D7.2 (INPUT), OEKJ.2 (D)
IN_D6: D7.2 (INPUT), OEGK.2 (D)
IN_D7: D7.2 (INPUT), OEFL.2 (D)
MODE0_OR_MODE1_AND_RDY: JAXB.1, JBNA.4, JBPY.1, KBUP.3
MODE1_OR_MODE3: NBZE.3
MODE2_OR_MODE3: OBNR.3
MODE4-6: JBNA.3, MBUP.1, OBXF.1, OCVK.3
MODE4_OR_MODE5: OCSD.3, ROMA.2
MODE5_OR_MODE7: OATK.3
unnamed: AAXI1.1 (~ENA), ODIB.2
unnamed: AAXI1.2, OEBY.4 (Q), OEFW.4 (Q), OEHW.4 (Q), OENU.4 (Q), OEPS.4 (Q), OEYB.4 (Q), OFQH.4 (Q), OFXA.4 (Q)
unnamed: AAXI1.3, D7.1 (DRV_LOW), D7.3 (~DRV_HIGH)
unnamed: ABVA2.1 (IN), ABVA2.3 (IN), OEFL.5 (~Q), OEGK.5 (~Q), OEKJ.5 (~Q), OEOU.5 (~Q), OEUB.5 (~Q), OFAD.5 (~Q), OFUH.5 (~Q), OGBZ.5 (~Q)
unnamed: ABVA2.2 (~ENA), ODQC.2
unnamed: DCEG.1 (~ENA), FBSI.1 (~ENA), HAZL.1, IARB.2 (~ENA), IOAW.2 (~ENA), JAXC.3
unnamed: DCEG.3, VPA.1 (DRV_LOW), VPA.4 (~DRV_HIGH)
unnamed: FBSI.3, VDA.1 (DRV_LOW), VDA.4 (~DRV_HIGH)
unnamed: HAKW.1, HALC.3
unnamed: HALC.1, HAMT.4 (Q)
unnamed: HALC.2, HAMT.2 (D), HANA.2
unnamed: HALT.1, OCTG.
unnamed: HAZL.2, HBCA.1 (~ENA), HBEP.1 (~ENA)
unnamed: HBCA.2, HBCT.3
unnamed: HBCT.1, VPA.2 (~INPUT)
unnamed: HBEP.2, HBGA.3
unnamed: HBGA.1, VDA.2 (~INPUT)
unnamed: HBQJ.1, RDY.1
unnamed: HVCM.1, OCTG.
unnamed: IAQD.1, IAQU.3, IAQV.1
unnamed: IAQD.3, IOAW.1 (IN), IOAW.3 (IN)
unnamed: IAQS.2, IAQU.2
unnamed: IAQV.3, IARB.1 (IN), IARB.3 (IN)
unnamed: IARF.1, JBDE.2
unnamed: IBEP.1, IBGG.3
unnamed: IBGG.2, IBNJ.2
unnamed: JAXB.2, JAXC.1
unnamed: JBDJ.1, JBHT.6 (Q)
unnamed: JBHT.3 (CLK), JBHT.4 (~CLK), LBWH.2
unnamed: JBNA.1, LBXR.4 (Q)
unnamed: JBND.2, JBPY.3
unnamed: KBOI.1, KBPI.1, LCLR.1, LCQL.1, LCQZ.3
unnamed: KBOI.4, LCLC.1
unnamed: KBPI.2, KBTI.2
unnamed: KBPI.3, KBSI.2
unnamed: KBPI.5, MBRP.1
unnamed: KBUP.2, KBVA.3
unnamed: LBYR.2, LCQL.3, LCQV.1
unnamed: LCIH.1, LCLC.3
unnamed: LCLR.2, LCNI.2, LCQV.2, LCSU.3
unnamed: LCNI.4, MCBW.2
unnamed: LCPE.1, LCQL.4
unnamed: LCPE.2, LCQV.4
unnamed: LCPE.3, MBPY.4
unnamed: LCPE.4, OBWM0.2
unnamed: LCSU.4, MCBW.1
unnamed: LDAD.2, MBXS.1
unnamed: MBNS.2, MBPY.3
unnamed: MBPY.1, MCCZ.3, OBBW.2
unnamed: MBRP.2, MBXS.3
unnamed: MBRP.3, OBRC.1, OBWM1.3
unnamed: MBSK.1, MBUP.3
unnamed: MBUB.2, MBUP.4
unnamed: MCBW.3, MCCZ.4
unnamed: MCBW.4, OBWM1.2
unnamed: NBWJ.1, OBNU.5
unnamed: OBEA.2, OBNU.3
unnamed: OBNU.1, OBXF.2
unnamed: OBRC.2, OBWM0.3
unnamed: OBWM0.4, ODQC.1
unnamed: OBWM1.4, ODIB.1
unnamed: OCTG., OCVK.2, TM.1
unnamed: ROLZ.1, ROMA.3
unnamed: ROMA.1, ZOZP.2
RW: LCQL.2, LCSU.1, MBNS.1, MCCZ.2
wIARB_or_wHBCA: DCEG.2, HBCA.3, IARB.4, IARF.3
wIAYI: JBHT.1 (~RESET), JBHT.5 (~RESET)
wIBPY: HBCT.2, HBGA.2
wIOAW_or_wHBEP: FBSI.2, HBEP.3, IARF.2, IOAW.4
wJBDJ: IAQU.1, IBGG.1, JBDJ.2, JBNA.2, U6.2
wJP2I0: U6.3
wJP2I1: LBOQ.1
wJP2I2: OBBW.1, OBEA.1
wJP2I3: U8.3
wJP2I4: MAWW.1
wKBNZ: KBOI.3, LCSU.2
wMBLO: LBWH.1
wNBHJ_wNBHM_XIN/2: LBXR.1 (~ENA), LBXR.3 (ENA)
wOCOG_~MODE7: IAQS.1, IBNJ.1, JAXC.2, JBND.1, LBOQ.2, LCLC.2, LCNI.3, LCQV.3, MAWW.2, MBPY.2, MCCZ.1, OBNU.4, OCOG.2, U6.1, U8.1
~65816_ADDR_EN: HAKW.2
~65816_ADDR_RST: IBEP.2
~DMA_BUS_EN: JBQK.2, MBUP.2, OBNU.2, OBWM0.1, OBWM1.1
~DMA_BUS_ON: KBTI.1
~DMA_RW_EN: JBNA.5, JBQK.1
~EXTERNAL_BUS_EN: MBSK.2
~INTERNAL_ADDR_EN: NBWJ.2
~INTERNAL_CYCLE: IARF.4
~MODE0_OR_MODE1: LCQZ.2, LCSG.3
~MODE0_OR_MODE6: OCQI.3, ROLZ.2
~MODE0: KBUP.1, LCSG.1, OBNU.6, OCQI.2, OCTG.
~MODE1: KBVA.2, LCSG.2, MBUB.1, NBZE.1, OBNU.8, OCTG.
~MODE2: OBNR.1, OCTG.
~MODE3: NBZE.2, OBNR.2, OCTG.
~MODE4_OR_MODE6: OCEG.3
~MODE4: LDAD.1, OCEG.1, OCSD.1, OCTG.
~MODE5: OATK.1, OCSD.2, OCTG.
~MODE6: OCEG.2, OCQI.1, OCTG.
~MODE7: OATK.2, OCOG.1, OCTG., OCVK.1
~wRDY: HBQJ.2, KBVA.1, LCQZ.1, MBUP.3, OBNU.5, OBNU.7, ZOZP.1

Notes on the sheet:
Low when RDY = 0 in mode 1 or when DMA is on in mode 4-6
Disconnects 65816 in MODE7, in MODE1 when RDY is low and during DMA
Modes are active low - inputs seems to be active low MODE7 = Test mode with external CPU connections bypassing 65816 MODE4-6 = DMA test modes MODE0 = SNES mode MODE1 = SNES in halt mode where RDY is used to pause the 65816 MODE2-3 = NES modes where 4200-43FF registers are disabled and CPU connectio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
Cells in DMA section but not connected. Change of design or test in early prototypes?
Inverted CPU CLK
Connected to Data OUT Bus enable pins ODIB = '0' to present data to external bus
Latches 65816 Addresses on 2nd cycle of SYSCLK. Disabled during DMA and permanently latched in MODE7
Goes low during internal CPU cycles VDA and VPA are low and DMA is not running
Connected to Data OUT Bus enable pins ODQC = '0' to read external data bus
JBNA = JBQK set to '1' when in MODE2-3, in MODE7, in MODE1 + RDY = 0 or DMA is OFF
