rgalland/SNES_S-CPU_Schematics/S-CPU_kicad/clocks.kicad_sch

## KiCad design S-CPU_kicad/clocks.kicad_sch (2024-12-24, an earlier design)

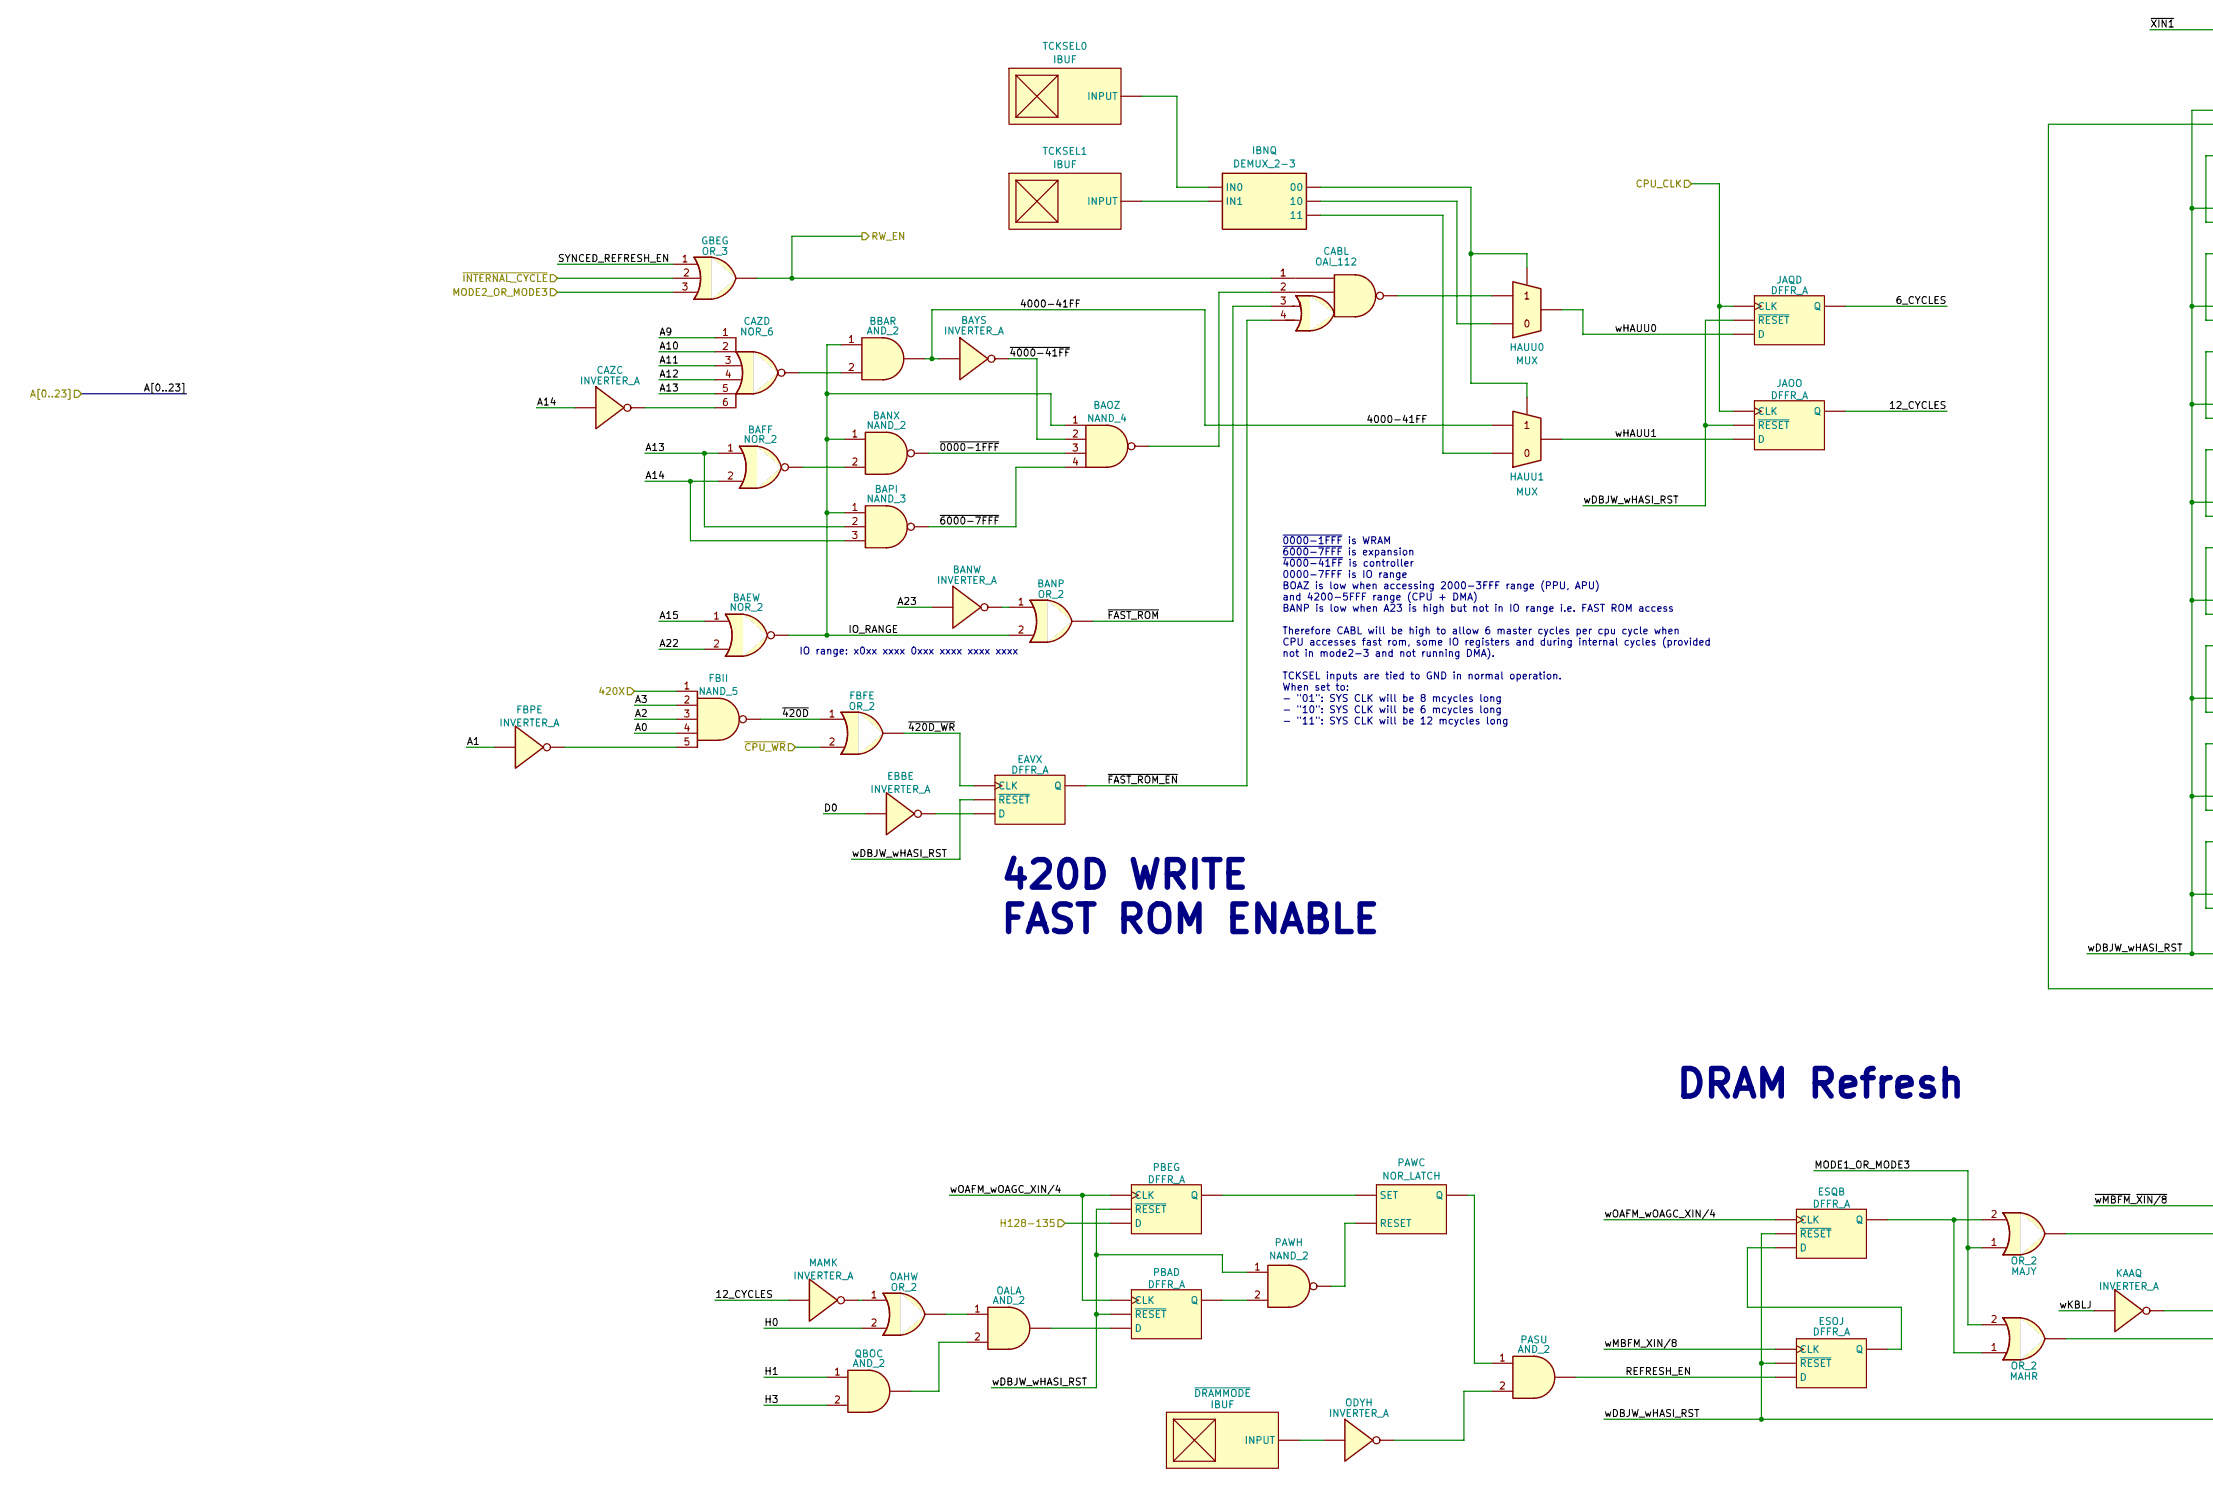
[picture p65: schematic clocks.kicad_sch, part in row 1, column 1]

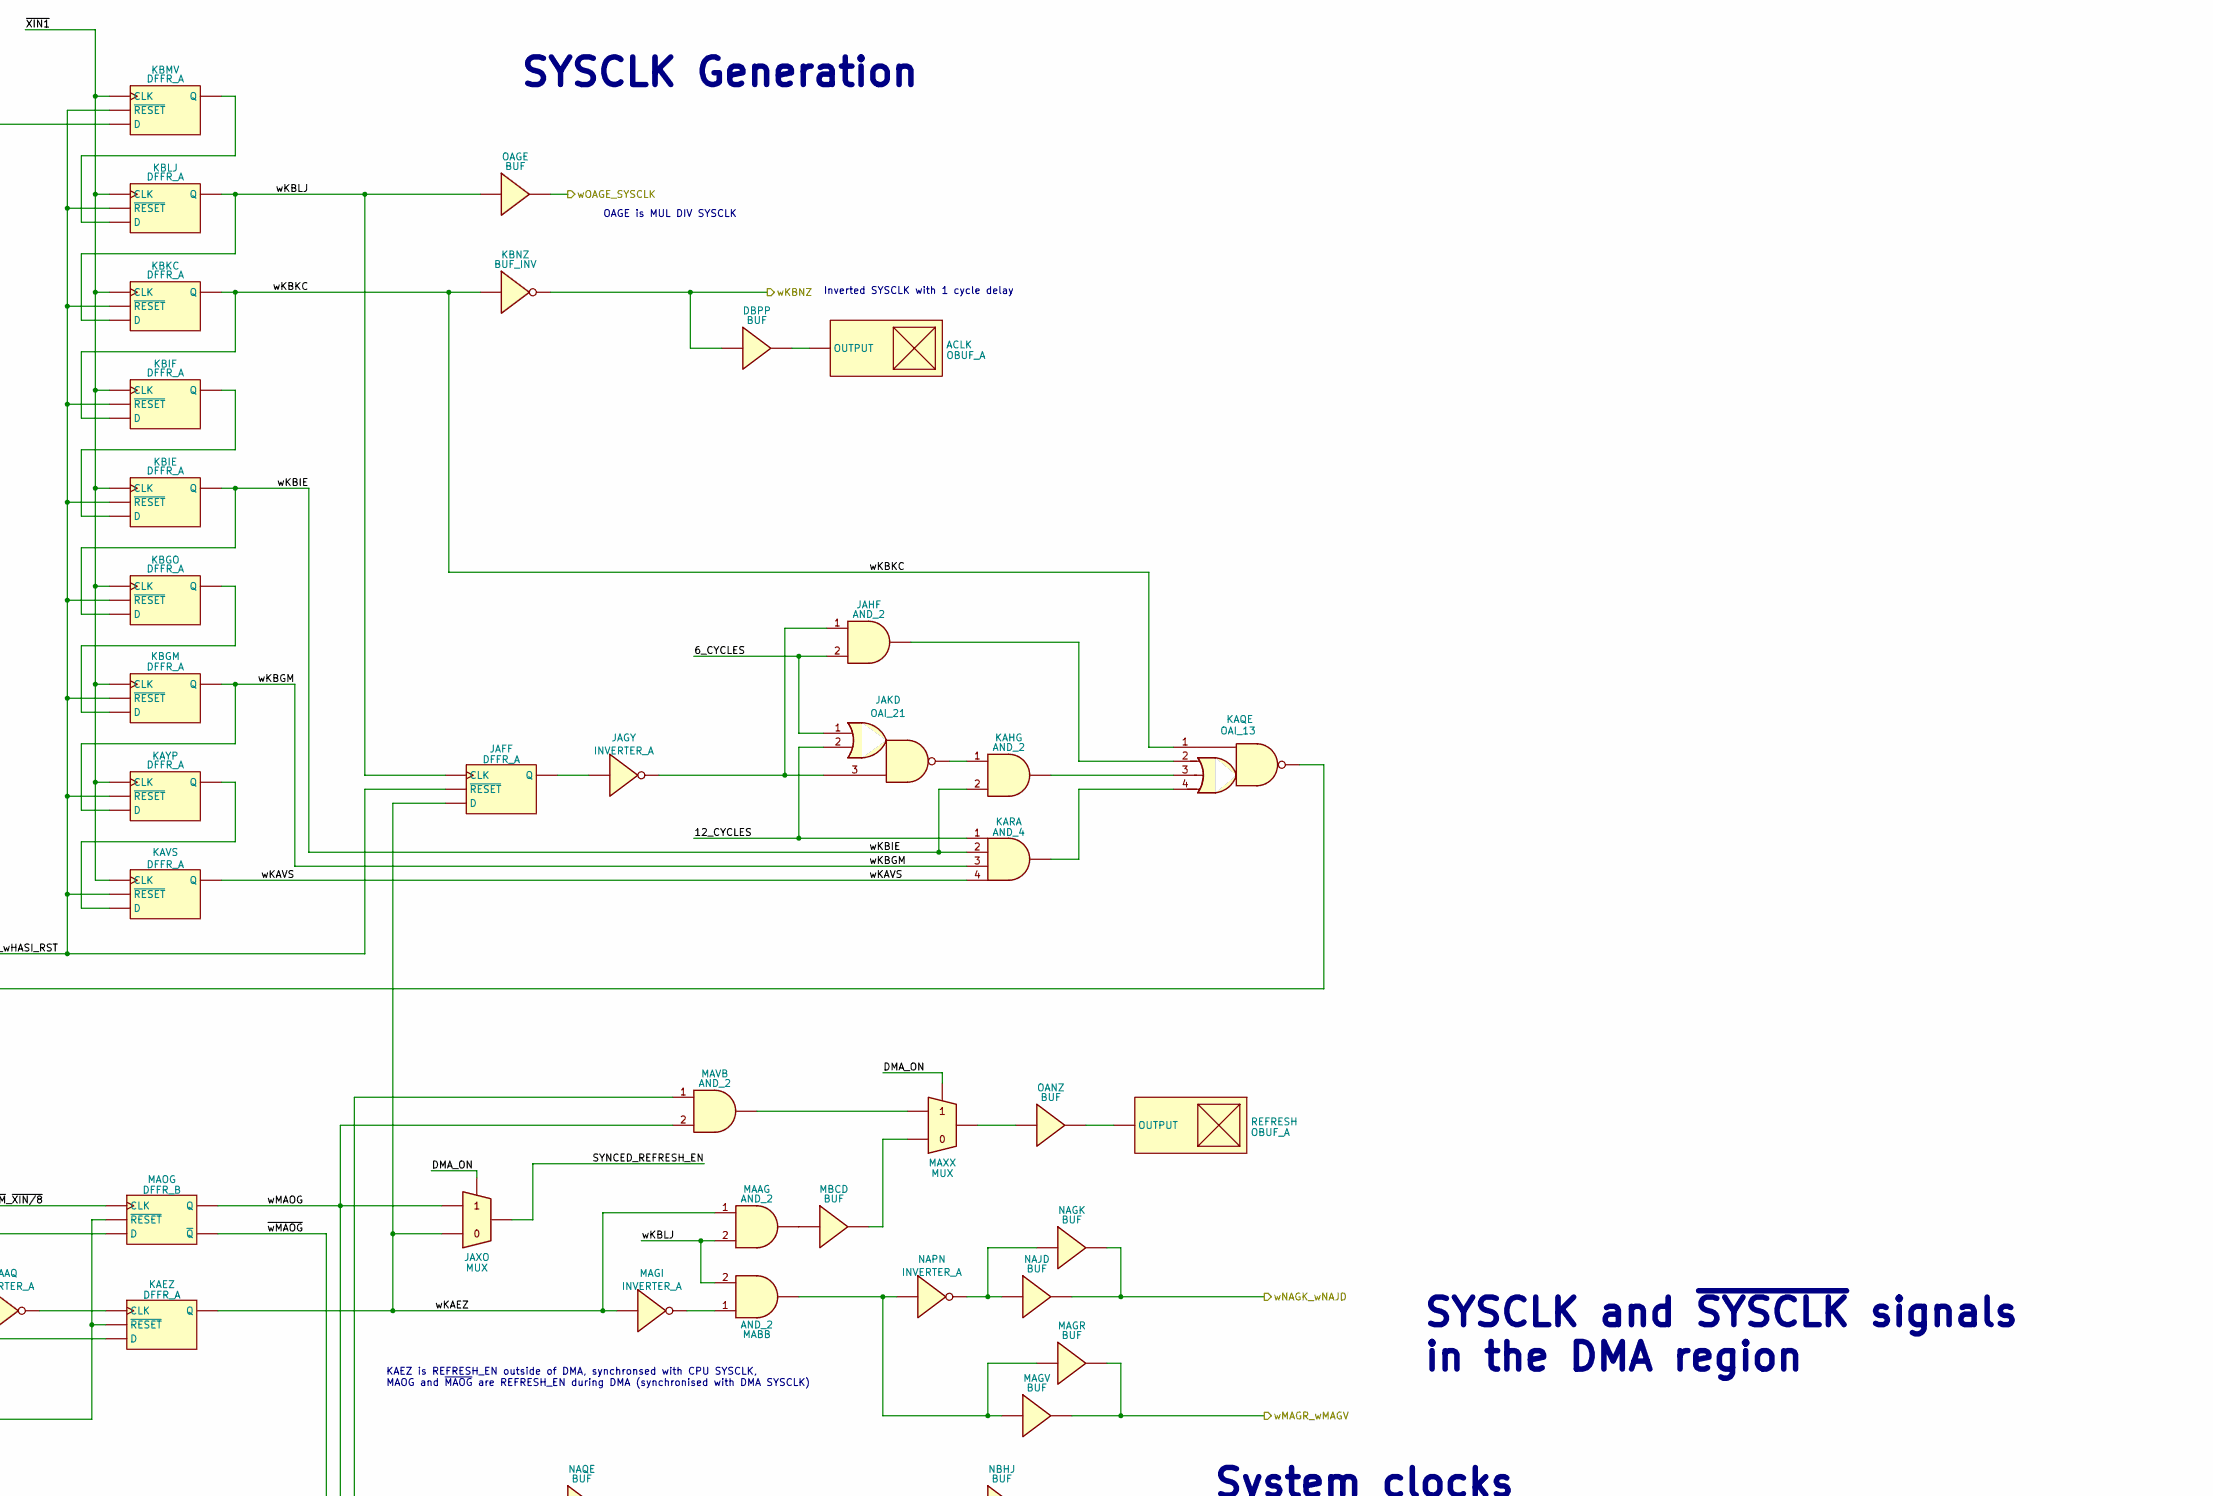
[picture p66: schematic clocks.kicad_sch, part in row 1, column 2]

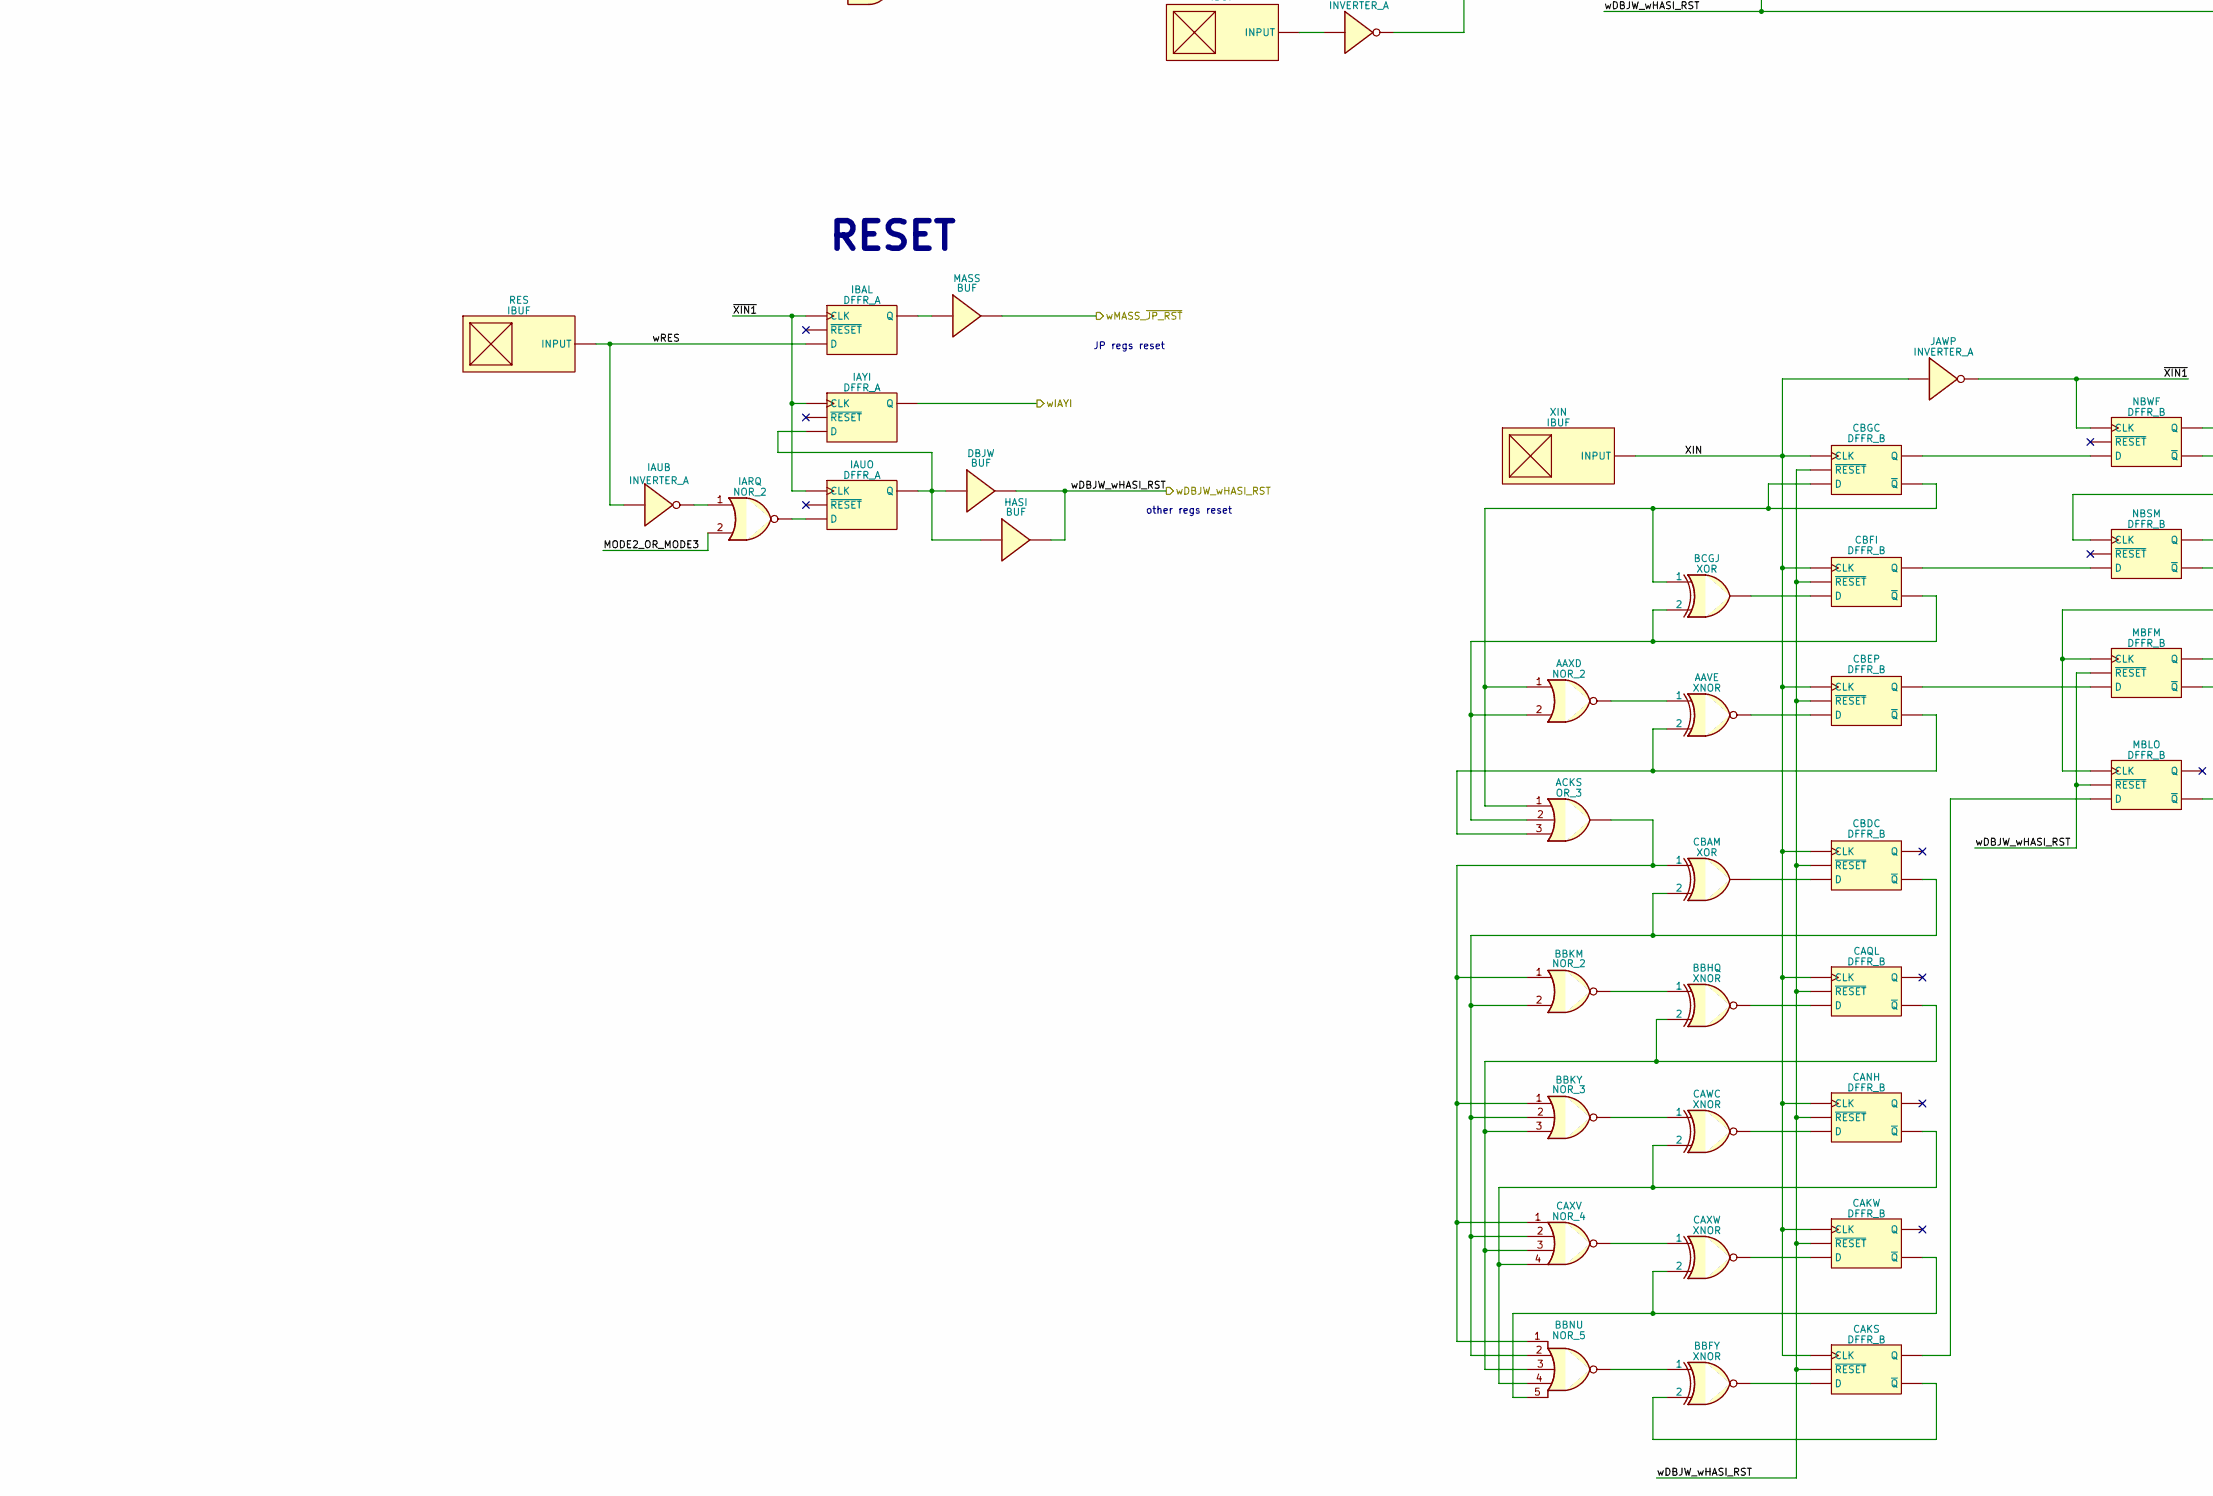
[picture p67: schematic clocks.kicad_sch, part in row 2, column 1]

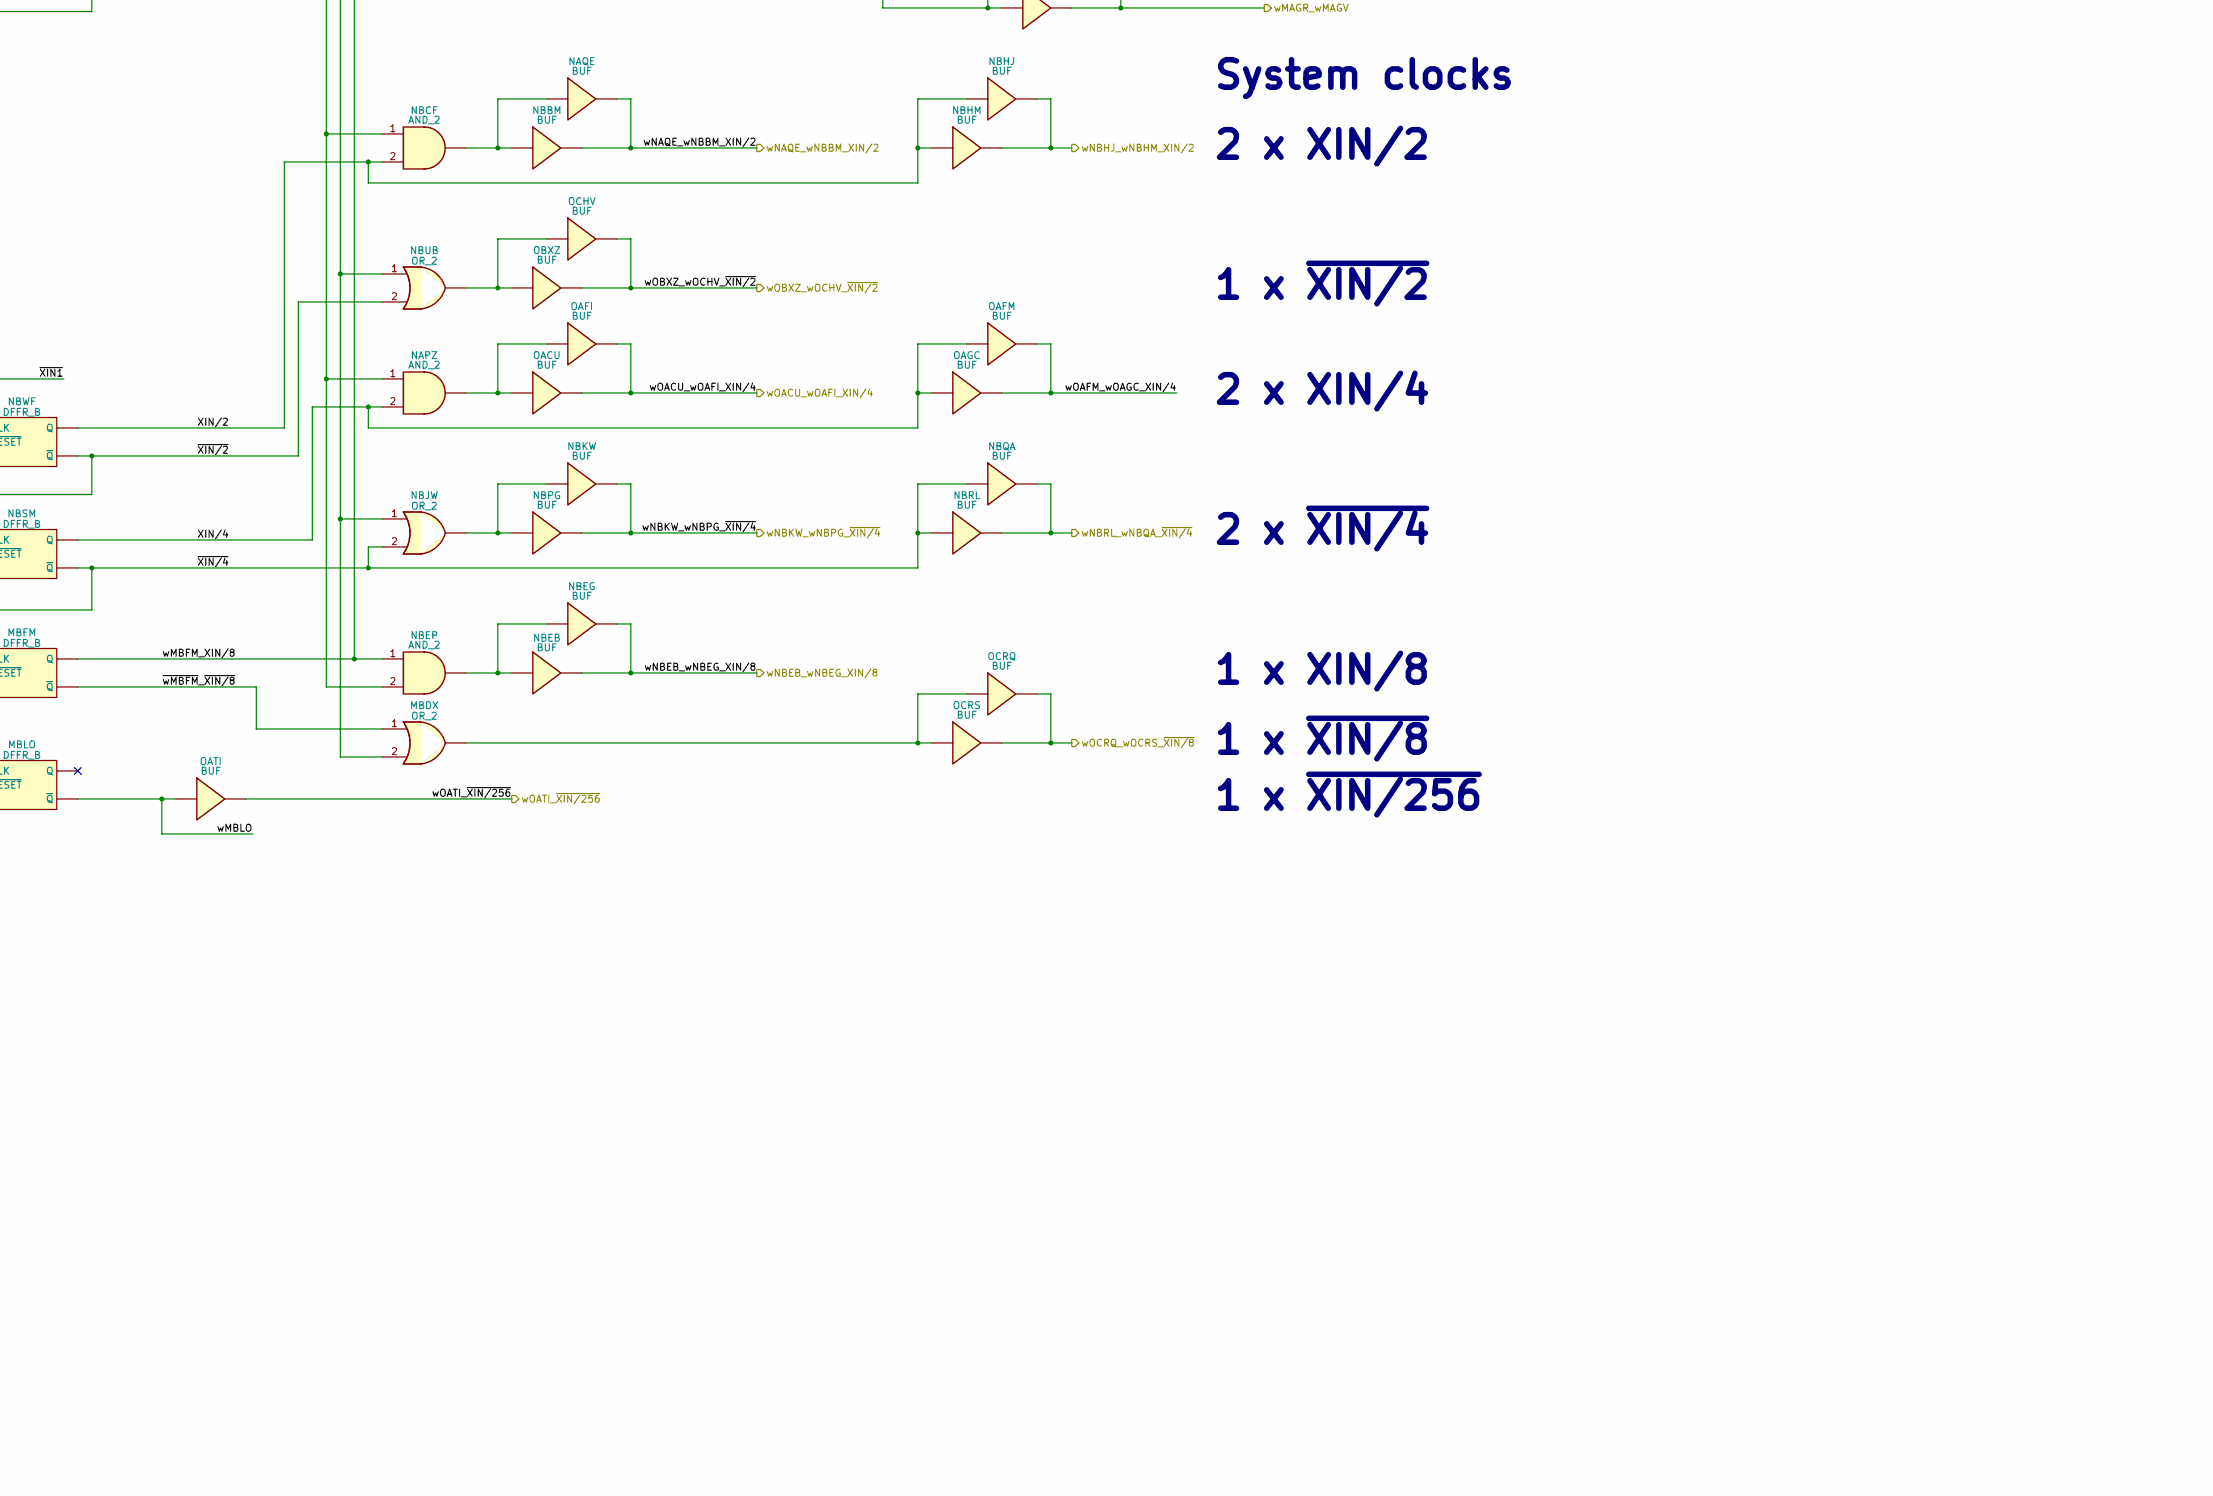
[picture p68: schematic clocks.kicad_sch, part in row 2, column 2]

Parts:
AAVE: XNOR
AAXD: NOR_2
ACKS: OR_3
ACLK: OBUF_A
BAEW: NOR_2
BAFF: NOR_2
BANP: OR_2
BANW: INVERTER_A
BANX: NAND_2
BAOZ: NAND_4
BAPI: NAND_3
BAYS: INVERTER_A
BBAR: AND_2
BBFY: XNOR
BBHQ: XNOR
BBKM: NOR_2
BBKY: NOR_3
BBNU: NOR_5
BCGJ: XOR
CABL: OAI_112
CAKS: DFFR_B
CAKW: DFFR_B
CANH: DFFR_B
CAQL: DFFR_B
CAWC: XNOR
CAXV: NOR_4
CAXW: XNOR
CAZC: INVERTER_A
CAZD: NOR_6
CBAM: XOR
CBDC: DFFR_B
CBEP: DFFR_B
CBFI: DFFR_B
CBGC: DFFR_B
DBJW: BUF
DBPP: BUF
EAVX: DFFR_A
EBBE: INVERTER_A
ESOJ: DFFR_A
ESQB: DFFR_A
FBFE: OR_2
FBII: NAND_5
FBPE: INVERTER_A
GBEG: OR_3
HASI: BUF
HAUU0, HAUU1: MUX
IARQ: NOR_2
IAUB: INVERTER_A
IAUO: DFFR_A
IAYI: DFFR_A
IBAL: DFFR_A
IBNQ: DEMUX_2-3
JAFF: DFFR_A
JAGY: INVERTER_A
JAHF: AND_2
JAKD: OAI_21
JAOO: DFFR_A
JAQD: DFFR_A
JAWP: INVERTER_A
JAXO: MUX
KAAQ: INVERTER_A
KAEZ: DFFR_A
KAHG: AND_2
KAQE: OAI_13
KARA: AND_4
KAVS: DFFR_A
KAYP: DFFR_A
KBGM: DFFR_A
KBGO: DFFR_A
KBIE: DFFR_A
KBIF: DFFR_A
KBKC: DFFR_A
KBLJ: DFFR_A
KBMV: DFFR_A
KBNZ: BUF_INV
MAAG: AND_2
MABB: AND_2
MAGI: INVERTER_A
MAGR: BUF
MAGV: BUF
MAHR: OR_2
MAJY: OR_2
MAMK: INVERTER_A
MAOG: DFFR_B
MASS: BUF
MAVB: AND_2
MAXX: MUX
MBCD: BUF
MBDX: OR_2
MBFM: DFFR_B
MBLO: DFFR_B
NAGK: BUF
NAJD: BUF
NAPN: INVERTER_A
NAPZ: AND_2
NAQE: BUF
NBBM: BUF
NBCF: AND_2
NBEB: BUF
NBEG: BUF
NBEP: AND_2
NBHJ: BUF
NBHM: BUF
NBJW: OR_2
NBKW: BUF
NBPG: BUF
NBQA: BUF
NBRL: BUF
NBSM: DFFR_B
NBUB: OR_2
NBWF: DFFR_B
OACU: BUF
OAFI: BUF
OAFM: BUF
OAGC: BUF
OAGE: BUF
OAHW: OR_2
OALA: AND_2
OANZ: BUF
OATI: BUF
OBXZ: BUF
OCHV: BUF
OCRQ: BUF
OCRS: BUF
ODYH: INVERTER_A
PASU: AND_2
PAWC: NOR_LATCH
PAWH: NAND_2
PBAD: DFFR_A
PBEG: DFFR_A
QBOC: AND_2
REFRESH: OBUF_A
RES: IBUF
TCKSEL0, TCKSEL1: IBUF
XIN: IBUF
~{DRAMMODE}: IBUF

Connections:
6_CYCLES: JAHF.2, JAKD.1, JAQD.6 (Q)
12_CYCLES: JAKD.2, JAOO.6 (Q), KARA.1, MAMK.1
420X: FBII.1
4000-41FF: BAYS.1, BBAR.3, HAUU1.2
A0: FBII.4
A1: FBPE.1
A2: FBII.3
A3: FBII.2
A9: CAZD.1
A10: CAZD.2
A11: CAZD.3
A12: CAZD.4
A13: BAFF.1, BAPI.2, CAZD.5
A14: BAFF.2, BAPI.3, CAZC.1
A15: BAEW.1
A22: BAEW.2
A23: BANW.1
CPU_CLK: JAOO.3 (CLK), JAOO.4 (~CLK), JAQD.3 (CLK), JAQD.4 (~CLK)
D0: EBBE.1
DMA_ON: JAXO.1, MAXX.1
H0: OAHW.2
H1: QBOC.1
H3: QBOC.2
H128-135: PBEG.2 (D)
IO_RANGE: BAEW.3, BANP.2, BANX.1, BAOZ.1, BAPI.1, BBAR.1
MODE1_OR_MODE3: MAHR.2, MAJY.1
MODE2_OR_MODE3: GBEG.3, IARQ.2
unnamed: AAVE.1, CBEP.2 (D)
unnamed: AAVE.2 (1), AAXD.3
unnamed: AAVE.3 (2), ACKS.3, CBEP.6 (~Q)
unnamed: AAXD.1, ACKS.1, BCGJ.2 (1), CBGC.2 (D), CBGC.6 (~Q)
unnamed: AAXD.2, ACKS.2, BCGJ.3 (2), CBFI.6 (~Q)
unnamed: ACKS.4, BBKM.1, BBKY.1, BBNU.1, CAXV.1, CBAM.2 (1)
unnamed: ACLK.1, DBPP.2
unnamed: BAFF.3, BANX.2
unnamed: BANP.1, BANW.2
unnamed: BAOZ.5, CABL.2
unnamed: BBAR.2, CAZD.7
unnamed: BBFY.1, CAKS.2 (D)
unnamed: BBFY.2 (1), BBNU.6
unnamed: BBFY.3 (2), CAKS.6 (~Q)
unnamed: BBHQ.1, CAQL.2 (D)
unnamed: BBHQ.2 (1), BBKM.3
unnamed: BBHQ.3 (2), BBKY.3, BBNU.3, CAQL.6 (~Q), CAXV.3
unnamed: BBKM.2, BBKY.2, BBNU.2, CAXV.2, CBAM.3 (2), CBDC.6 (~Q)
unnamed: BBKY.4, CAWC.2 (1)
unnamed: BBNU.4, CANH.6 (~Q), CAWC.3 (2), CAXV.4
unnamed: BBNU.5, CAKW.6 (~Q), CAXW.3 (2)
unnamed: BCGJ.1, CBFI.2 (D)
unnamed: CABL.5, HAUU0.2
unnamed: CAKS.7 (Q), MBLO.2 (D)
unnamed: CAKW.2 (D), CAXW.1
unnamed: CANH.2 (D), CAWC.1
unnamed: CAXV.5, CAXW.2 (1)
unnamed: CAZC.2, CAZD.6
unnamed: CBAM.1, CBDC.2 (D)
unnamed: CBEP.7 (Q), MBFM.2 (D)
unnamed: CBFI.7 (Q), NBSM.2 (D)
unnamed: CBGC.7 (Q), NBWF.2 (D)
unnamed: DBJW.1, HASI.1, IAUO.6 (Q), IAYI.2 (D)
unnamed: EAVX.2 (D), EBBE.2
unnamed: ESOJ.6 (Q), ESQB.2 (D)
unnamed: ESQB.6 (Q), MAHR.1, MAJY.2
unnamed: FBII.5, FBPE.2
unnamed: HAUU0.1, HAUU1.1, IBNQ.
unnamed: HAUU0.3, IBNQ.
unnamed: HAUU1.3, IBNQ.
unnamed: IARQ.1, IAUB.2
unnamed: IARQ.3, IAUO.2 (D)
unnamed: IAUO.1 (~RESET), IAUO.5 (~RESET)
unnamed: IAYI.1 (~RESET), IAYI.5 (~RESET)
unnamed: IBAL.1 (~RESET), IBAL.5 (~RESET)
unnamed: IBAL.6 (Q), MASS.1
unnamed: IBNQ., TCKSEL0.1, TCKSEL1.1
unnamed: JAFF.6 (Q), JAGY.1
unnamed: JAGY.2, JAHF.1, JAKD.3
unnamed: JAHF.3, KAQE.2
unnamed: JAKD.4, KAHG.1
unnamed: KAAQ.2, KAEZ.3 (CLK), KAEZ.4 (~CLK)
unnamed: KAEZ.2 (D), MAHR.3
unnamed: KAHG.3, KAQE.3
unnamed: KAQE.4, KARA.5
unnamed: KAQE.5, KBMV.2 (D)
unnamed: KAVS.2 (D), KAYP.6 (Q)
unnamed: KBGM.2 (D), KBGO.6 (Q)
unnamed: KBIE.2 (D), KBIF.6 (Q)
unnamed: KBLJ.2 (D), KBMV.6 (Q)
unnamed: MAAG.3, MBCD.1
unnamed: MABB.1, MAGI.2
unnamed: MABB.3, MAGR.1, MAGV.1, NAPN.1
unnamed: MAJY.3, MAOG.2 (D)
unnamed: MAMK.2, OAHW.1
unnamed: MAVB.3, MAXX.2
unnamed: MAXX.3, MBCD.2
unnamed: MAXX.4, OANZ.1
unnamed: MBDX.3, OCRQ.1, OCRS.1
unnamed: NAGK.1, NAJD.1, NAPN.2
unnamed: NAPZ.3, OACU.1, OAFI.1
unnamed: NAQE.1, NBBM.1, NBCF.3
unnamed: NBEB.1, NBEG.1, NBEP.3
unnamed: NBJW.3, NBKW.1, NBPG.1
unnamed: NBSM.1 (~RESET), NBSM.5 (~RESET)
unnamed: NBUB.3, OBXZ.1, OCHV.1
unnamed: NBWF.1 (~RESET), NBWF.5 (~RESET)
unnamed: OAHW.3, OALA.1
unnamed: OALA.2, QBOC.3
unnamed: OALA.3, PBAD.2 (D)
unnamed: OANZ.2, REFRESH.1
unnamed: ODYH.1, ~{DRAMMODE}.1
unnamed: ODYH.2, PASU.2
unnamed: PASU.1, PAWC.3 (Q)
unnamed: PAWC.1 (SET), PBEG.6 (Q)
unnamed: PAWC.4 (RESET), PAWH.3
unnamed: PAWH.2, PBAD.6 (Q)
REFRESH_EN: ESOJ.2 (D), PASU.3
RW_EN: CABL.1, GBEG.4
SYNCED_REFRESH_EN: GBEG.1, JAXO.4
XIN: CAKS.3 (CLK), CAKS.4 (~CLK), CAKW.3 (CLK), CAKW.4 (~CLK), CANH.3 (CLK), CANH.4 (~CLK), CAQL.3 (CLK), CAQL.4 (~CLK), CBDC.3 (CLK), CBDC.4 (~CLK), CBEP.3 (CLK), CBEP.4 (~CLK), CBFI.3 (CLK), CBFI.4 (~CLK), CBGC.3 (CLK), CBGC.4 (~CLK), JAWP.1, XIN.1
XIN/2: NBCF.2, NBHJ.1, NBHM.1, NBWF.7 (Q)
XIN/4: NAPZ.2, NBSM.7 (Q), OAFM.1, OAGC.1
wDBJW_wHASI_RST: CAKS.1 (~RESET), CAKS.5 (~RESET), CAKW.1 (~RESET), CAKW.5 (~RESET), CANH.1 (~RESET), CANH.5 (~RESET), CAQL.1 (~RESET), CAQL.5 (~RESET), CBDC.1 (~RESET), CBDC.5 (~RESET), CBEP.1 (~RESET), CBEP.5 (~RESET), CBFI.1 (~RESET), CBFI.5 (~RESET), CBGC.1 (~RESET), CBGC.5 (~RESET), DBJW.2, EAVX.1 (~RESET), EAVX.5 (~RESET), ESOJ.1 (~RESET), ESOJ.5 (~RESET), ESQB.1 (~RESET), ESQB.5 (~RESET), HASI.2, JAFF.1 (~RESET), JAFF.5 (~RESET), JAOO.1 (~RESET), JAOO.5 (~RESET), JAQD.1 (~RESET), JAQD.5 (~RESET), KAEZ.1 (~RESET), KAEZ.5 (~RESET), KAVS.1 (~RESET), KAVS.5 (~RESET), KAYP.1 (~RESET), KAYP.5 (~RESET), KBGM.1 (~RESET), KBGM.5 (~RESET), KBGO.1 (~RESET), KBGO.5 (~RESET), KBIE.1 (~RESET), KBIE.5 (~RESET), KBIF.1 (~RESET), KBIF.5 (~RESET), KBKC.1 (~RESET), KBKC.5 (~RESET), KBLJ.1 (~RESET), KBLJ.5 (~RESET), KBMV.1 (~RESET), KBMV.5 (~RESET), MAOG.1 (~RESET), MAOG.5 (~RESET), MBFM.1 (~RESET), MBFM.5 (~RESET), MBLO.1 (~RESET), MBLO.5 (~RESET), PAWH.1, PBAD.1 (~RESET), PBAD.5 (~RESET), PBEG.1 (~RESET), PBEG.5 (~RESET)
wHAUU0: HAUU0.4, JAQD.2 (D)
wHAUU1: HAUU1.4, JAOO.2 (D)
wIAYI: IAYI.6 (Q)
wKAEZ: JAFF.2 (D), JAXO.3, KAEZ.6 (Q), MAAG.1, MAGI.1
wKAVS: KARA.4, KAVS.6 (Q)
wKBGM: KARA.3, KAYP.2 (D), KBGM.6 (Q)
wKBIE: KAHG.2, KARA.2, KBGO.2 (D), KBIE.6 (Q)
wKBKC: KAQE.1, KBIF.2 (D), KBKC.6 (Q), KBNZ.1
wKBLJ: JAFF.3 (CLK), JAFF.4 (~CLK), KAAQ.1, KBKC.2 (D), KBLJ.6 (Q), MAAG.2, MABB.2, OAGE.1
wKBNZ: DBPP.1, KBNZ.2
wMAGR_wMAGV: MAGR.2, MAGV.2
wMAOG: JAXO.2, MAOG.7 (Q), MAVB.2, MBDX.2, NBJW.1, NBUB.1
wMASS_~JP_RST: MASS.2
wMBFM_XIN/8: ESOJ.3 (CLK), ESOJ.4 (~CLK), MAVB.1, MBFM.7 (Q), NBEP.1
wMBLO: MBLO.6 (~Q), OATI.1
wNAGK_wNAJD: NAGK.2, NAJD.2
wNAQE_wNBBM_XIN/2: NAQE.2, NBBM.2
wNBEB_wNBEG_XIN/8: NBEB.2, NBEG.2
wNBHJ_wNBHM_XIN/2: NBHJ.2, NBHM.2
wNBKW_wNBPG_~XIN/4: NBKW.2, NBPG.2
wNBRL_wNBQA_~XIN/4: NBQA.2, NBRL.2
wOACU_wOAFI_XIN/4: OACU.2, OAFI.2
wOAFM_wOAGC_XIN/4: ESQB.3 (CLK), ESQB.4 (~CLK), OAFM.2, OAGC.2, PBAD.3 (CLK), PBAD.4 (~CLK), PBEG.3 (CLK), PBEG.4 (~CLK)
wOAGE_SYSCLK: OAGE.2
wOATI_~XIN/256: OATI.2
wOBXZ_wOCHV_~XIN/2: OBXZ.2, OCHV.2
wOCRQ_wOCRS_~XIN/8: OCRQ.2, OCRS.2
wRES: IAUB.1, IBAL.2 (D), RES.1
~0000-1FFF: BANX.3, BAOZ.3
~420D_WR: EAVX.3 (CLK), EAVX.4 (~CLK), FBFE.3
~420D: FBFE.1, FBII.6
~4000-41FF: BAOZ.2, BAYS.2
~6000-7FFF: BAOZ.4, BAPI.4
~CPU_WR: FBFE.2
~FAST_ROM_EN: CABL.4, EAVX.6 (Q)
~FAST_ROM: BANP.3, CABL.3
~INTERNAL_CYCLE: GBEG.2
~XIN1: IAUO.3 (CLK), IAUO.4 (~CLK), IAYI.3 (CLK), IAYI.4 (~CLK), IBAL.3 (CLK), IBAL.4 (~CLK), JAWP.2, KAVS.3 (CLK), KAVS.4 (~CLK), KAYP.3 (CLK), KAYP.4 (~CLK), KBGM.3 (CLK), KBGM.4 (~CLK), KBGO.3 (CLK), KBGO.4 (~CLK), KBIE.3 (CLK), KBIE.4 (~CLK), KBIF.3 (CLK), KBIF.4 (~CLK), KBKC.3 (CLK), KBKC.4 (~CLK), KBLJ.3 (CLK), KBLJ.4 (~CLK), KBMV.3 (CLK), KBMV.4 (~CLK), NBWF.3 (CLK), NBWF.4 (~CLK)
~XIN/2: NBSM.3 (CLK), NBSM.4 (~CLK), NBUB.2, NBWF.6 (~Q)
~XIN/4: MBFM.3 (CLK), MBFM.4 (~CLK), MBLO.3 (CLK), MBLO.4 (~CLK), NBJW.2, NBQA.1, NBRL.1, NBSM.6 (~Q)
~wMAOG: MAOG.6 (~Q), NAPZ.1, NBCF.1, NBEP.2
~wMBFM_~XIN/8: MAOG.3 (CLK), MAOG.4 (~CLK), MBDX.1, MBFM.6 (~Q)

Notes on the sheet:
RESET
KAEZ is REFRESH_EN outside of DMA, synchronsed with CPU SYSCLK, MAOG and ~{MAOG} are REFRESH_EN during DMA (synchronised with DMA SYSCLK)
1 x XIN/8
2 x ~{XIN/4}
1 x ~{XIN/256}
IO range: x0xx xxxx 0xxx xxxx xxxx xxxx
SYSCLK Generation
JP regs reset
Inverted SYSCLK with 1 cycle delay
1 x ~{XIN/8}
1 x ~{XIN/2}
DRAM Refresh
SYSCLK and ~{SYSCLK} signals in the DMA region
2 x XIN/2
2 x XIN/4
~{0000-1FFF} is WRAM ~{6000-7FFF} is expansion ~{4000-41FF} is controller 0000-7FFF is IO range BOAZ is low when accessing 2000-3FFF range (PPU, APU) and 4200-5FFF range (CPU + DMA) BANP is low when A23 is high but not in IO range i.e. FAST ROM access Therefore CABL will be high to allow 6 master c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
System clocks
OAGE is MUL DIV SYSCLK
420D WRITE FAST ROM ENABLE
other regs reset
