rgalland/SNES_S-CPU_Schematics/S-CPU_kicad/divquotient.kicad_sch

## KiCad design S-CPU_kicad/divquotient.kicad_sch (2024-12-24, an earlier design)

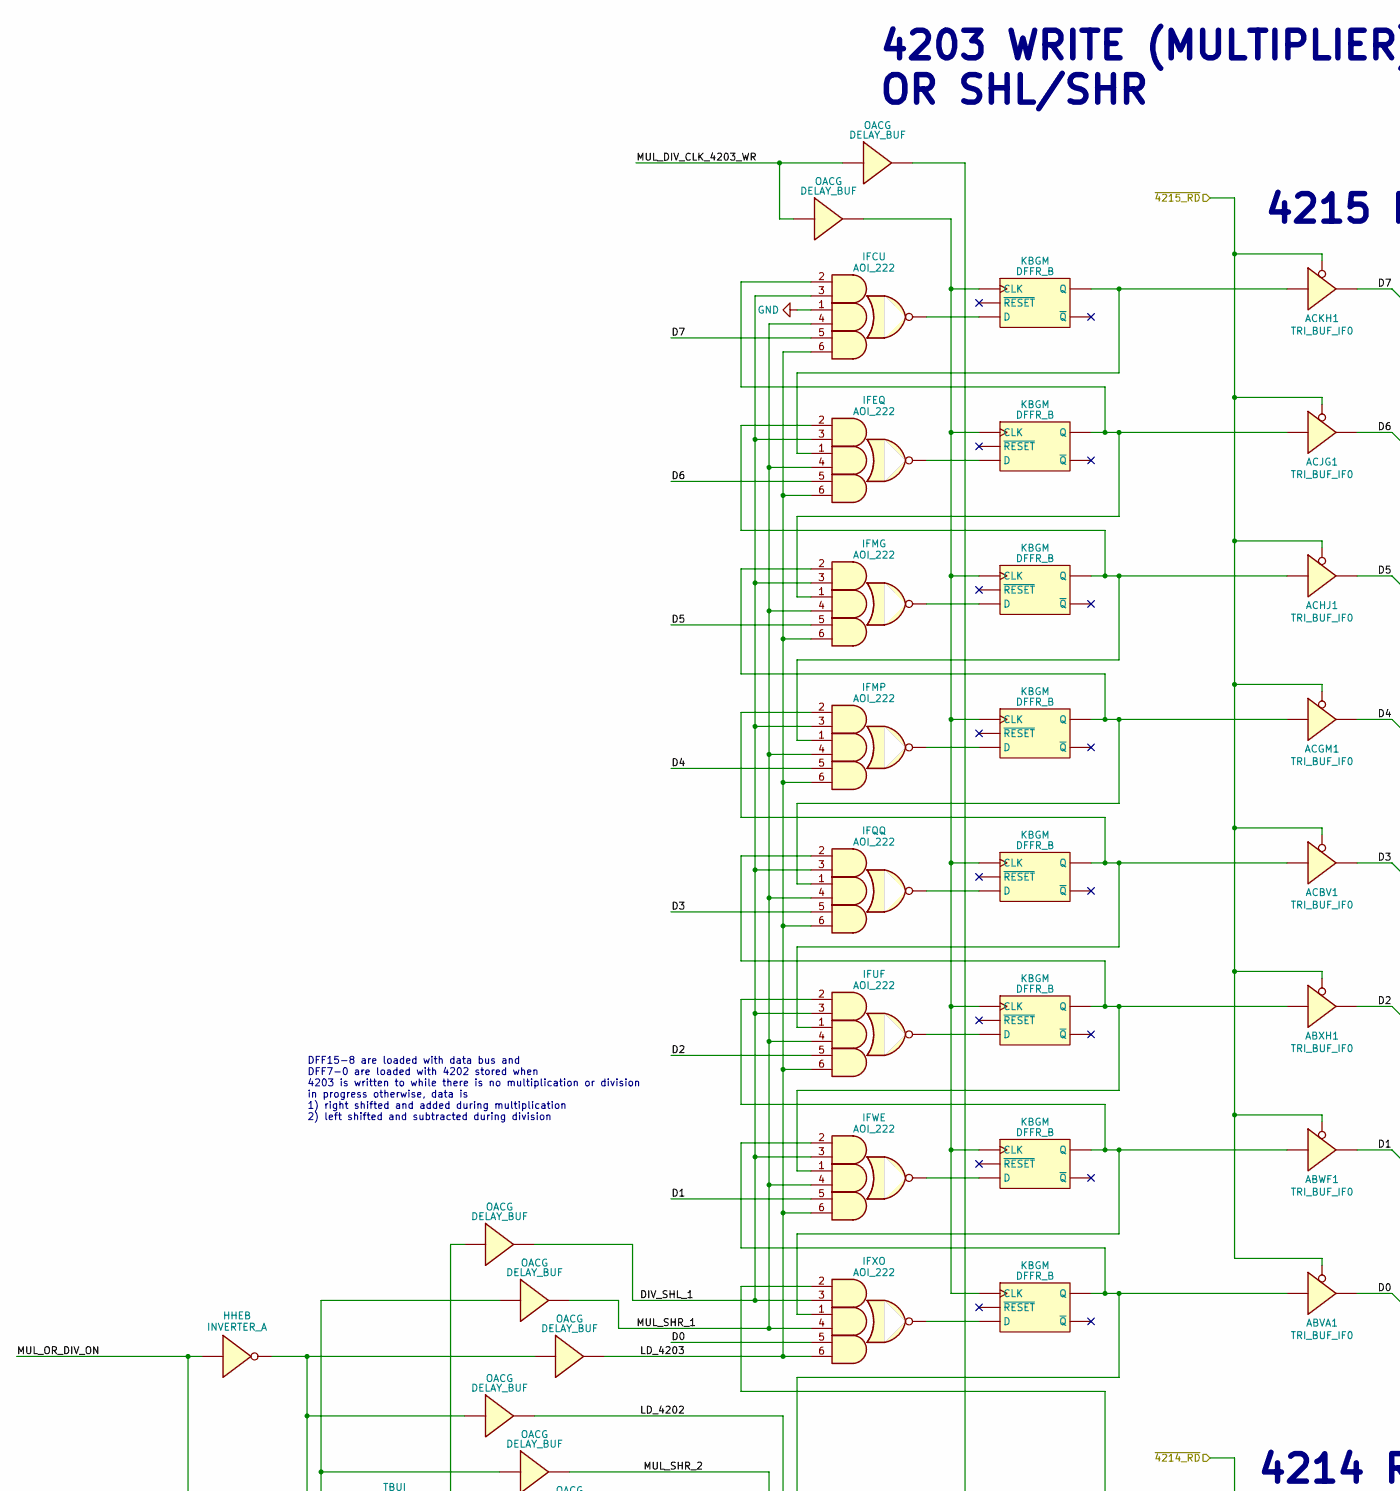
[picture p69: schematic divquotient.kicad_sch, part in row 1, column 1]

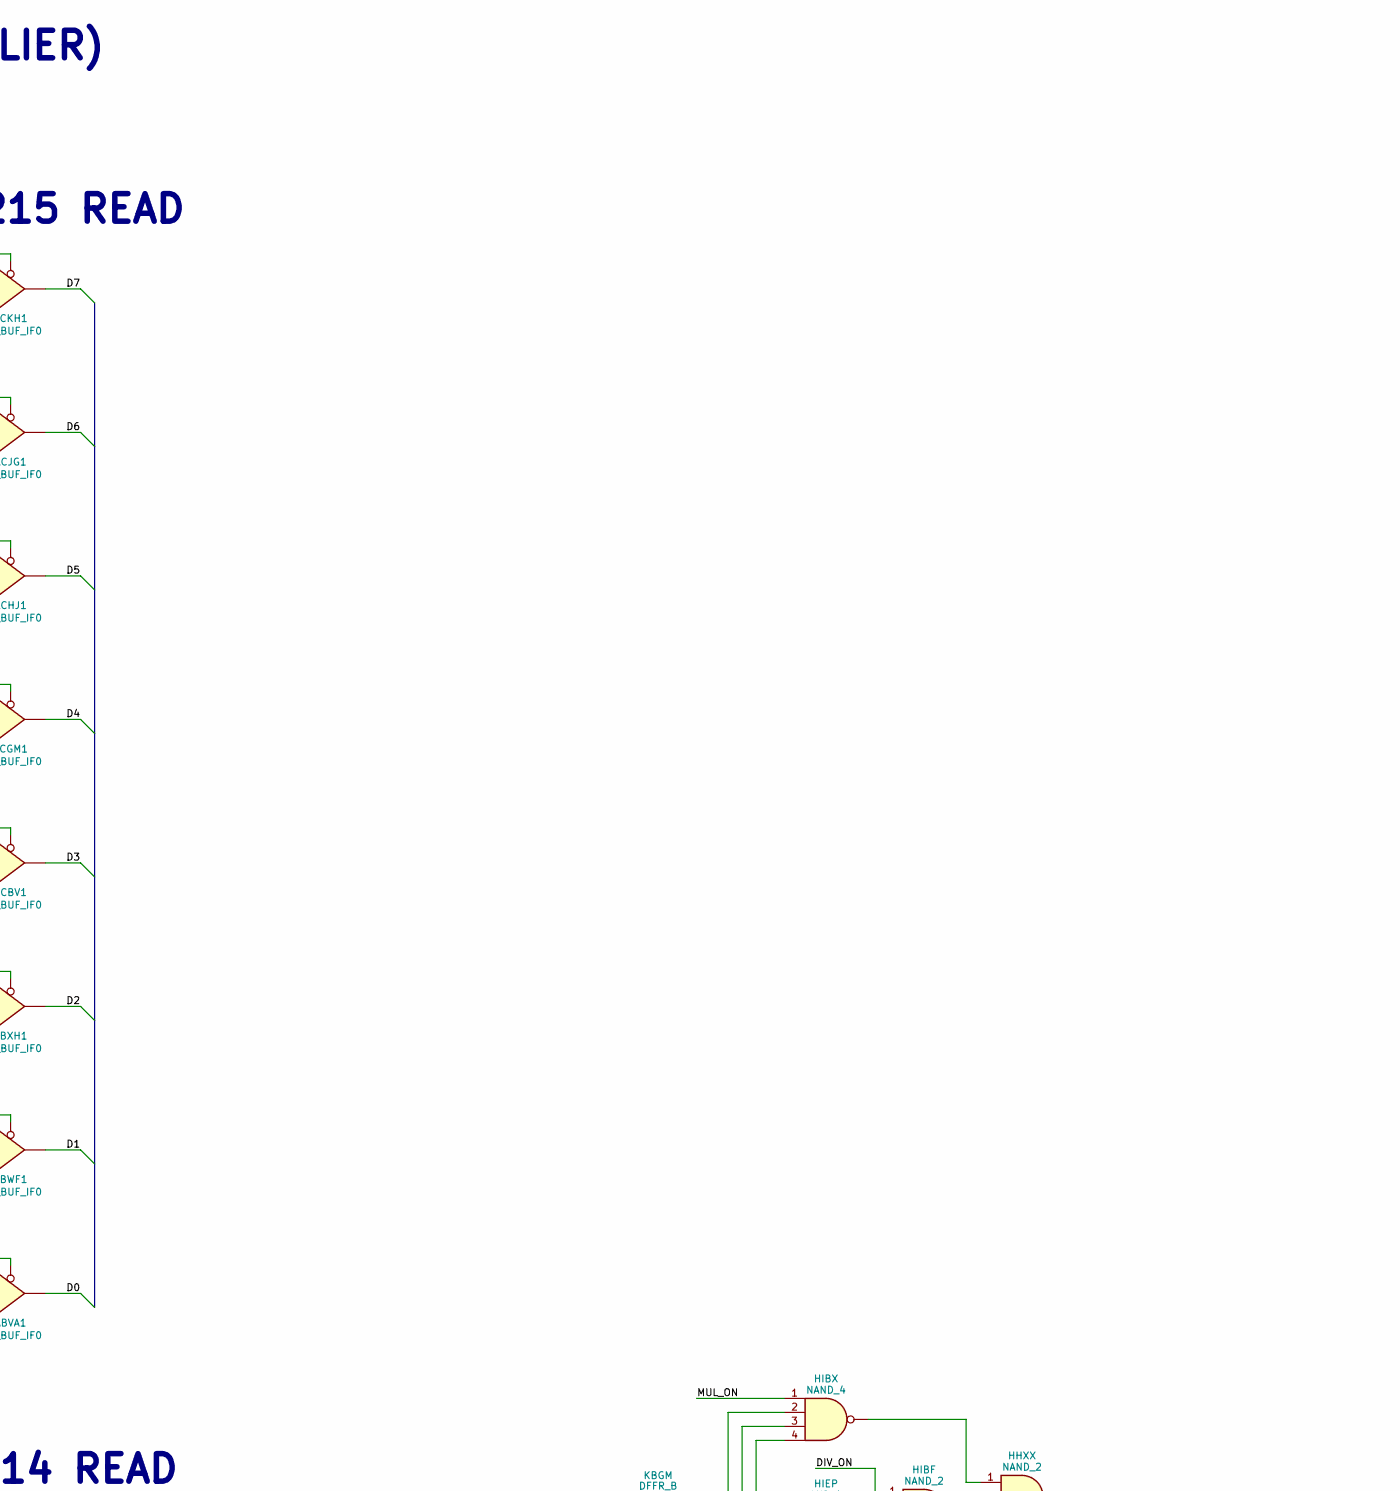
[picture p70: schematic divquotient.kicad_sch, part in row 1, column 2]

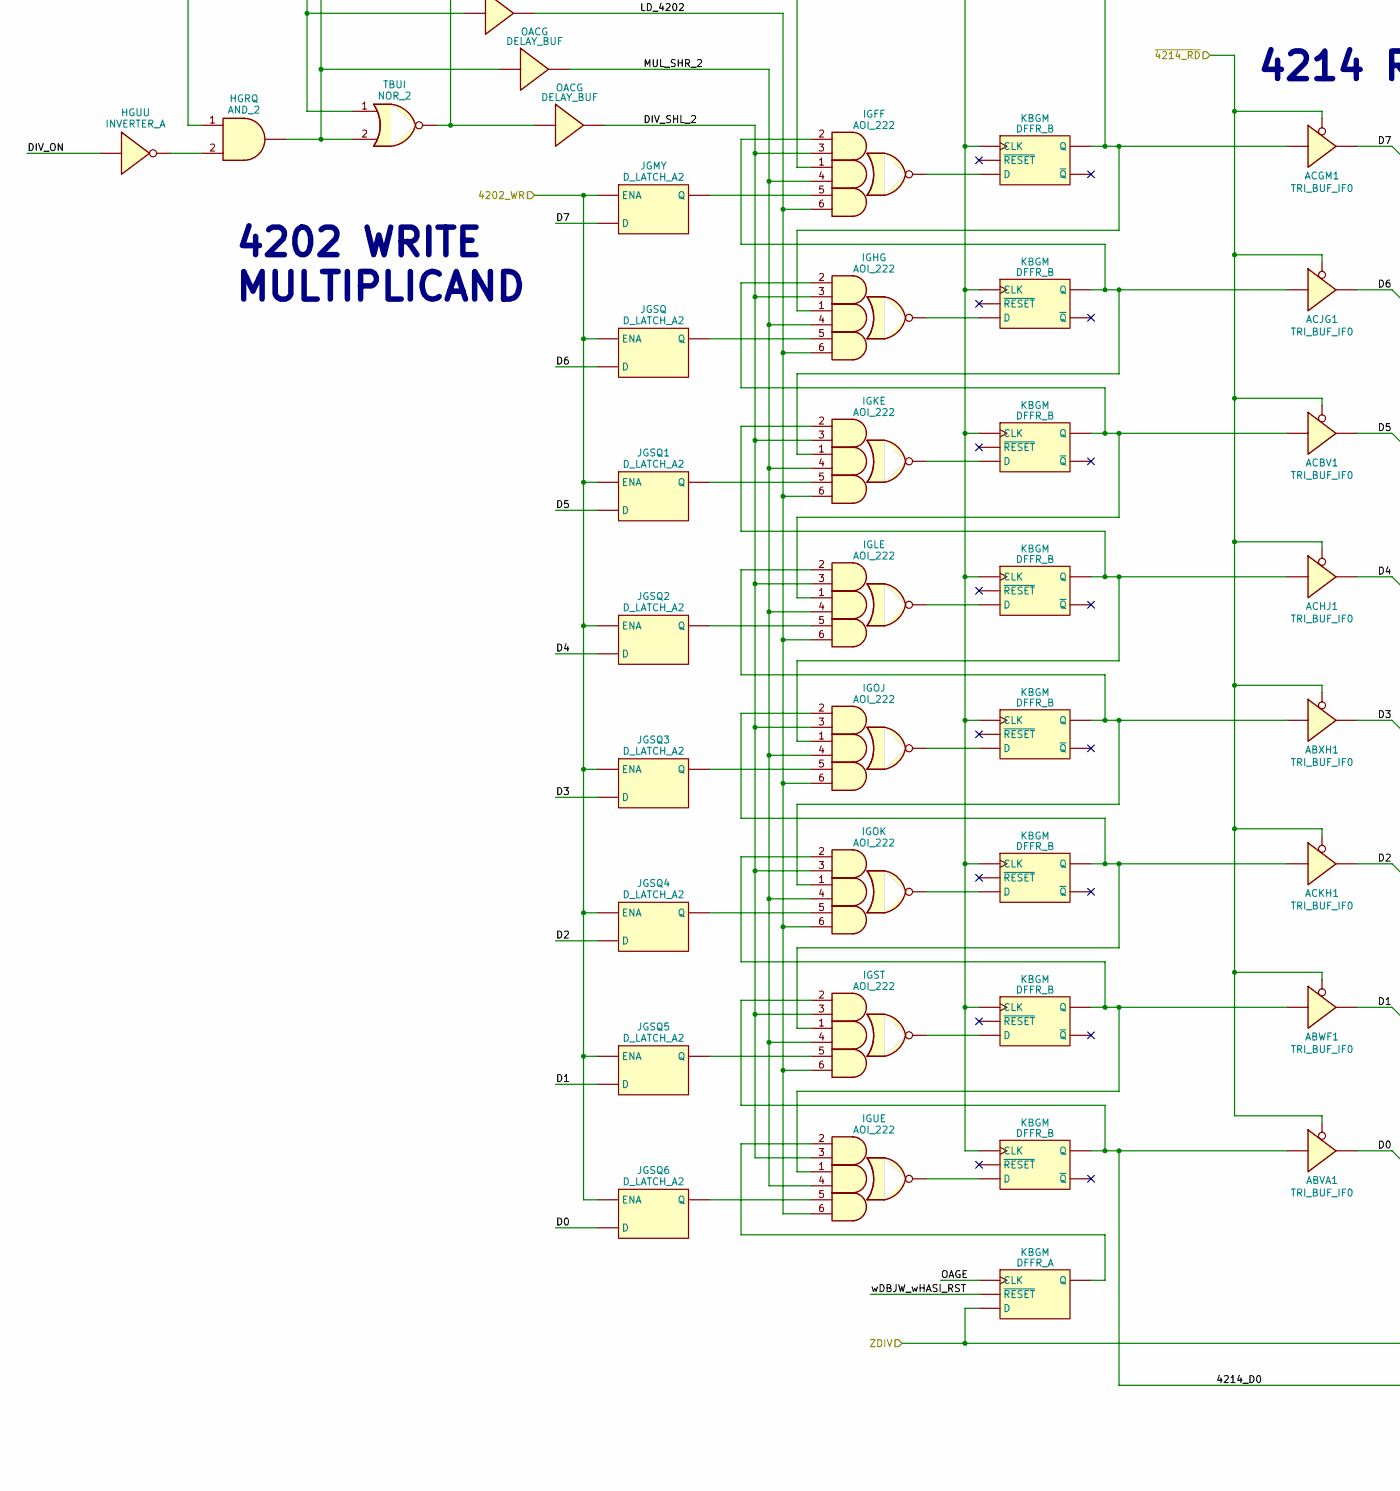
[picture p71: schematic divquotient.kicad_sch, part in row 2, column 1]

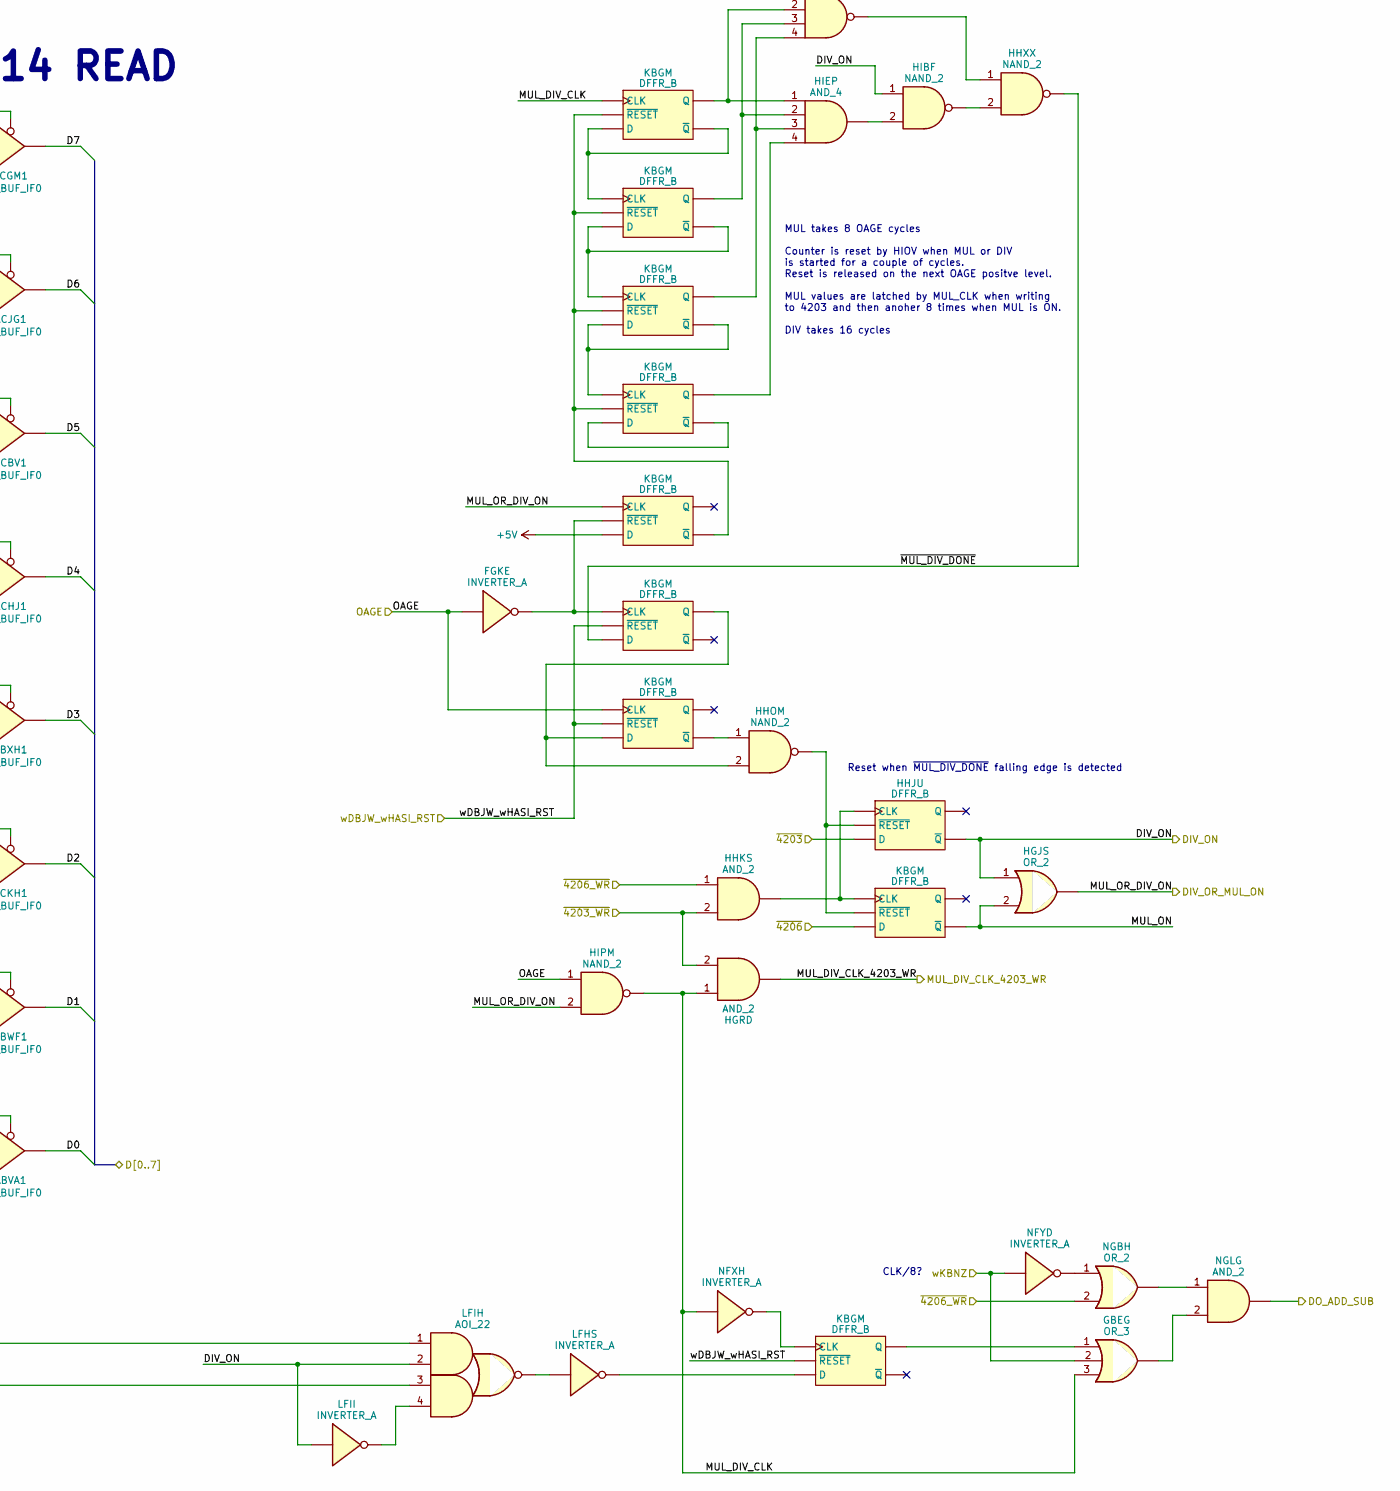
[picture p72: schematic divquotient.kicad_sch, part in row 2, column 2]

Parts:
ABVA1: TRI_BUF_IF0
ABWF1: TRI_BUF_IF0
ABXH1: TRI_BUF_IF0
ACBV1: TRI_BUF_IF0
ACGM1: TRI_BUF_IF0
ACHJ1: TRI_BUF_IF0
ACJG1: TRI_BUF_IF0
ACKH1: TRI_BUF_IF0
FGKE: INVERTER_A
GBEG: OR_3
HGJS: OR_2
HGRD: AND_2
HGRQ: AND_2
HGUU: INVERTER_A
HHEB: INVERTER_A
HHJU: DFFR_B
HHKS: AND_2
HHOM: NAND_2
HHXX: NAND_2
HIBF: NAND_2
HIBX: NAND_4
HIEP: AND_4
HIPM: NAND_2
IFCU: AOI_222
IFEQ: AOI_222
IFMG: AOI_222
IFMP: AOI_222
IFQQ: AOI_222
IFUF: AOI_222
IFWE: AOI_222
IFXO: AOI_222
IGFF: AOI_222
IGHG: AOI_222
IGKE: AOI_222
IGLE: AOI_222
IGOJ: AOI_222
IGOK: AOI_222
IGST: AOI_222
IGUE: AOI_222
JGMY: D_LATCH_A2
JGSQ, JGSQ1, JGSQ2, JGSQ3, JGSQ4, JGSQ5, JGSQ6: D_LATCH_A2
KBGM: DFFR_B
LFHS: INVERTER_A
LFIH: AOI_22
LFII: INVERTER_A
NFXH: INVERTER_A
NFYD: INVERTER_A
NGBH: OR_2
NGLG: AND_2
OACG: DELAY_BUF
TBUI: NOR_2

Connections:
4202_WR: JGMY.1 (~ENA), JGMY.3 (ENA), JGSQ.1 (~ENA), JGSQ.3 (ENA), JGSQ1.1 (~ENA), JGSQ1.3 (ENA), JGSQ2.1 (~ENA), JGSQ2.3 (ENA), JGSQ3.1 (~ENA), JGSQ3.3 (ENA), JGSQ4.1 (~ENA), JGSQ4.3 (ENA), JGSQ5.1 (~ENA), JGSQ5.3 (ENA), JGSQ6.1 (~ENA), JGSQ6.3 (ENA)
4214_D0: ABVA1.1 (IN), ABVA1.3 (IN), IGST.2, KBGM.7 (Q), LFIH.3
+5V: KBGM.2 (D)
D0: ABVA1.4, IFXO.5, JGSQ6.2 (D)
D1: ABWF1.4, IFWE.5, JGSQ5.2 (D)
D2: ABXH1.4, ACKH1.4, IFUF.5, JGSQ4.2 (D)
D3: ABXH1.4, ACBV1.4, IFQQ.5, JGSQ3.2 (D)
D4: ACGM1.4, ACHJ1.4, IFMP.5, JGSQ2.2 (D)
D5: ACBV1.4, ACHJ1.4, IFMG.5, JGSQ1.2 (D)
D6: ACJG1.4, IFEQ.5, JGSQ.2 (D)
D7: ACGM1.4, ACKH1.4, IFCU.5, JGMY.2 (D)
DIV_ON: HGJS.1, HGUU.1, HHJU.6 (~Q), HIBF.1, LFIH.2, LFII.1
DIV_OR_MUL_ON: HGJS.3, HGRQ.1, HHEB.1, HIPM.2, KBGM.3 (CLK), KBGM.4 (~CLK)
DIV_SHL_1: IFCU.3, IFEQ.3, IFMG.3, IFMP.3, IFQQ.3, IFUF.3, IFWE.3, IFXO.3, OACG.2
DIV_SHL_2: IGFF.3, IGHG.3, IGKE.3, IGLE.3, IGOJ.3, IGOK.3, IGST.3, IGUE.3, OACG.2
DO_ADD_SUB: NGLG.3
GND: IFCU.1
LD_4202: IGFF.6, IGHG.6, IGKE.6, IGLE.6, IGOJ.6, IGOK.6, IGST.6, IGUE.6, OACG.2
LD_4203: IFCU.6, IFEQ.6, IFMG.6, IFMP.6, IFQQ.6, IFUF.6, IFWE.6, IFXO.6, OACG.2
MUL_DIV_CLK: GBEG.3, HGRD.1, HIPM.3, KBGM.3 (CLK), KBGM.4 (~CLK), NFXH.1
MUL_DIV_CLK_4203_WR: HGRD.3, OACG.1
MUL_ON: HGJS.2, HIBX.1, KBGM.6 (~Q)
MUL_SHR_1: IFCU.4, IFEQ.4, IFMG.4, IFMP.4, IFQQ.4, IFUF.4, IFWE.4, IFXO.4, OACG.2
MUL_SHR_2: IGFF.4, IGHG.4, IGKE.4, IGLE.4, IGOJ.4, IGOK.4, IGST.4, IGUE.4, OACG.2
unnamed: ABVA1.1 (IN), ABVA1.3 (IN), IFWE.2, IGFF.1, KBGM.7 (Q)
unnamed: ABWF1.1 (IN), ABWF1.3 (IN), IFUF.2, IFXO.1, IGOK.2, IGUE.1, KBGM.7 (Q)
unnamed: ABXH1.1 (IN), ABXH1.3 (IN), IFQQ.2, IFWE.1, IGLE.2, IGOK.1, KBGM.7 (Q)
unnamed: ACBV1.1 (IN), ACBV1.3 (IN), IFMP.2, IFUF.1, IGHG.2, IGLE.1, KBGM.7 (Q)
unnamed: ACGM1.1 (IN), ACGM1.3 (IN), IFMG.2, IFQQ.1, IFXO.2, IGHG.1, KBGM.7 (Q)
unnamed: ACHJ1.1 (IN), ACHJ1.3 (IN), IFEQ.2, IFMP.1, IGKE.2, IGOJ.1, KBGM.7 (Q)
unnamed: ACJG1.1 (IN), ACJG1.3 (IN), IFCU.2, IFMG.1, IGFF.2, IGKE.1, KBGM.7 (Q)
unnamed: ACKH1.1 (IN), ACKH1.3 (IN), IFEQ.1, IGOJ.2, IGST.1, KBGM.7 (Q)
unnamed: FGKE.2, KBGM.1 (~RESET), KBGM.3 (CLK), KBGM.4 (~CLK), KBGM.5 (~RESET)
unnamed: GBEG.1, KBGM.7 (Q)
unnamed: GBEG.4, NGLG.2
unnamed: HGRQ.2, HGUU.2
unnamed: HGRQ.3, OACG.1, TBUI.2
unnamed: HHEB.2, OACG.1, TBUI.1
unnamed: HHJU.1 (~RESET), HHJU.5 (~RESET), HHOM.3, KBGM.1 (~RESET), KBGM.5 (~RESET)
unnamed: HHJU.3 (CLK), HHJU.4 (~CLK), HHKS.3, KBGM.3 (CLK), KBGM.4 (~CLK)
unnamed: HHOM.1, KBGM.6 (~Q)
unnamed: HHOM.2, KBGM.2 (D), KBGM.7 (Q)
unnamed: HHXX.1, HIBX.5
unnamed: HHXX.2, HIBF.3
unnamed: HIBF.2, HIEP.5
unnamed: HIBX.2, HIEP.1, KBGM.7 (Q)
unnamed: HIBX.3, HIEP.2, KBGM.7 (Q)
unnamed: HIBX.4, HIEP.3, KBGM.7 (Q)
unnamed: HIEP.4, KBGM.7 (Q)
unnamed: IFCU.3, KBGM.2 (D)
unnamed: IFEQ.3, KBGM.2 (D)
unnamed: IFMG.3, KBGM.2 (D)
unnamed: IFMP.3, KBGM.2 (D)
unnamed: IFQQ.3, KBGM.2 (D)
unnamed: IFUF.3, KBGM.2 (D)
unnamed: IFWE.3, KBGM.2 (D)
unnamed: IFXO.3, KBGM.2 (D)
unnamed: IGFF.3, KBGM.2 (D)
unnamed: IGFF.5, JGMY.4 (Q)
unnamed: IGHG.3, KBGM.2 (D)
unnamed: IGHG.5, JGSQ.4 (Q)
unnamed: IGKE.3, KBGM.2 (D)
unnamed: IGKE.5, JGSQ1.4 (Q)
unnamed: IGLE.3, KBGM.2 (D)
unnamed: IGLE.5, JGSQ2.4 (Q)
unnamed: IGOJ.3, KBGM.2 (D)
unnamed: IGOJ.5, JGSQ3.4 (Q)
unnamed: IGOK.3, KBGM.2 (D)
unnamed: IGOK.5, JGSQ4.4 (Q)
unnamed: IGST.3, KBGM.2 (D)
unnamed: IGST.5, JGSQ5.4 (Q)
unnamed: IGUE.2, KBGM.6 (~Q)
unnamed: IGUE.3, KBGM.2 (D)
unnamed: IGUE.5, JGSQ6.4 (Q)
unnamed: KBGM.1 (~RESET), KBGM.5 (~RESET), KBGM.6 (~Q)
unnamed: KBGM.2 (D), KBGM.3 (CLK), KBGM.4 (~CLK), KBGM.6 (~Q), LFHS.2
unnamed: KBGM.3 (CLK), KBGM.4 (~CLK), NFXH.2, OACG.2
unnamed: LFHS.1, LFIH.3
unnamed: LFIH.4, LFII.2
unnamed: NFYD.2, NGBH.1
unnamed: NGBH.3, NGLG.1
unnamed: OACG.1, TBUI.3
OAGE: FGKE.1, HIPM.1, KBGM.3 (CLK), KBGM.4 (~CLK)
ZDIV: KBGM.2 (D), LFIH.1
wDBJW_wHASI_RST: KBGM.1 (~RESET), KBGM.5 (~RESET)
wKBNZ: GBEG.2, NFYD.1
~4203_WR: HGRD.2, HHKS.2
~4203: HHJU.2 (D)
~4206_WR: HHKS.1, NGBH.2
~4206: KBGM.2 (D)
~4214_RD: ABVA1.2 (~ENA), ABWF1.2 (~ENA), ABXH1.2 (~ENA), ACBV1.2 (~ENA), ACGM1.2 (~ENA), ACHJ1.2 (~ENA), ACJG1.2 (~ENA), ACKH1.2 (~ENA)
~4215_RD: ABVA1.2 (~ENA), ABWF1.2 (~ENA), ABXH1.2 (~ENA), ACBV1.2 (~ENA), ACGM1.2 (~ENA), ACHJ1.2 (~ENA), ACJG1.2 (~ENA), ACKH1.2 (~ENA)
~MUL_DIV_DONE: HHXX.3, KBGM.2 (D)

Notes on the sheet:
DFF15-8 are loaded with data bus and DFF7-0 are loaded with 4202 stored when 4203 is written to while there is no multiplication or division in progress otherwise, data is 1) right shifted and added during multiplication 2) left shifted and subtracted during division
Reset when ~{MUL_DIV_DONE} falling edge is detected
4203 WRITE (MULTIPLIER) OR SHL/SHR
4202 WRITE MULTIPLICAND
CLK/8?
4215 READ
4214 READ
MUL takes 8 OAGE cycles Counter is reset by HIOV when MUL or DIV is started for a couple of cycles. Reset is released on the next OAGE positve level. MUL values are latched by MUL_CLK when writing to 4203 and then anoher 8 times when MUL is ON. DIV takes 16 cycles
