rgalland/SNES_S-CPU_Schematics/S-CPU_kicad/dma.kicad_sch

## KiCad design S-CPU_kicad/dma.kicad_sch (2024-12-24, an earlier design)

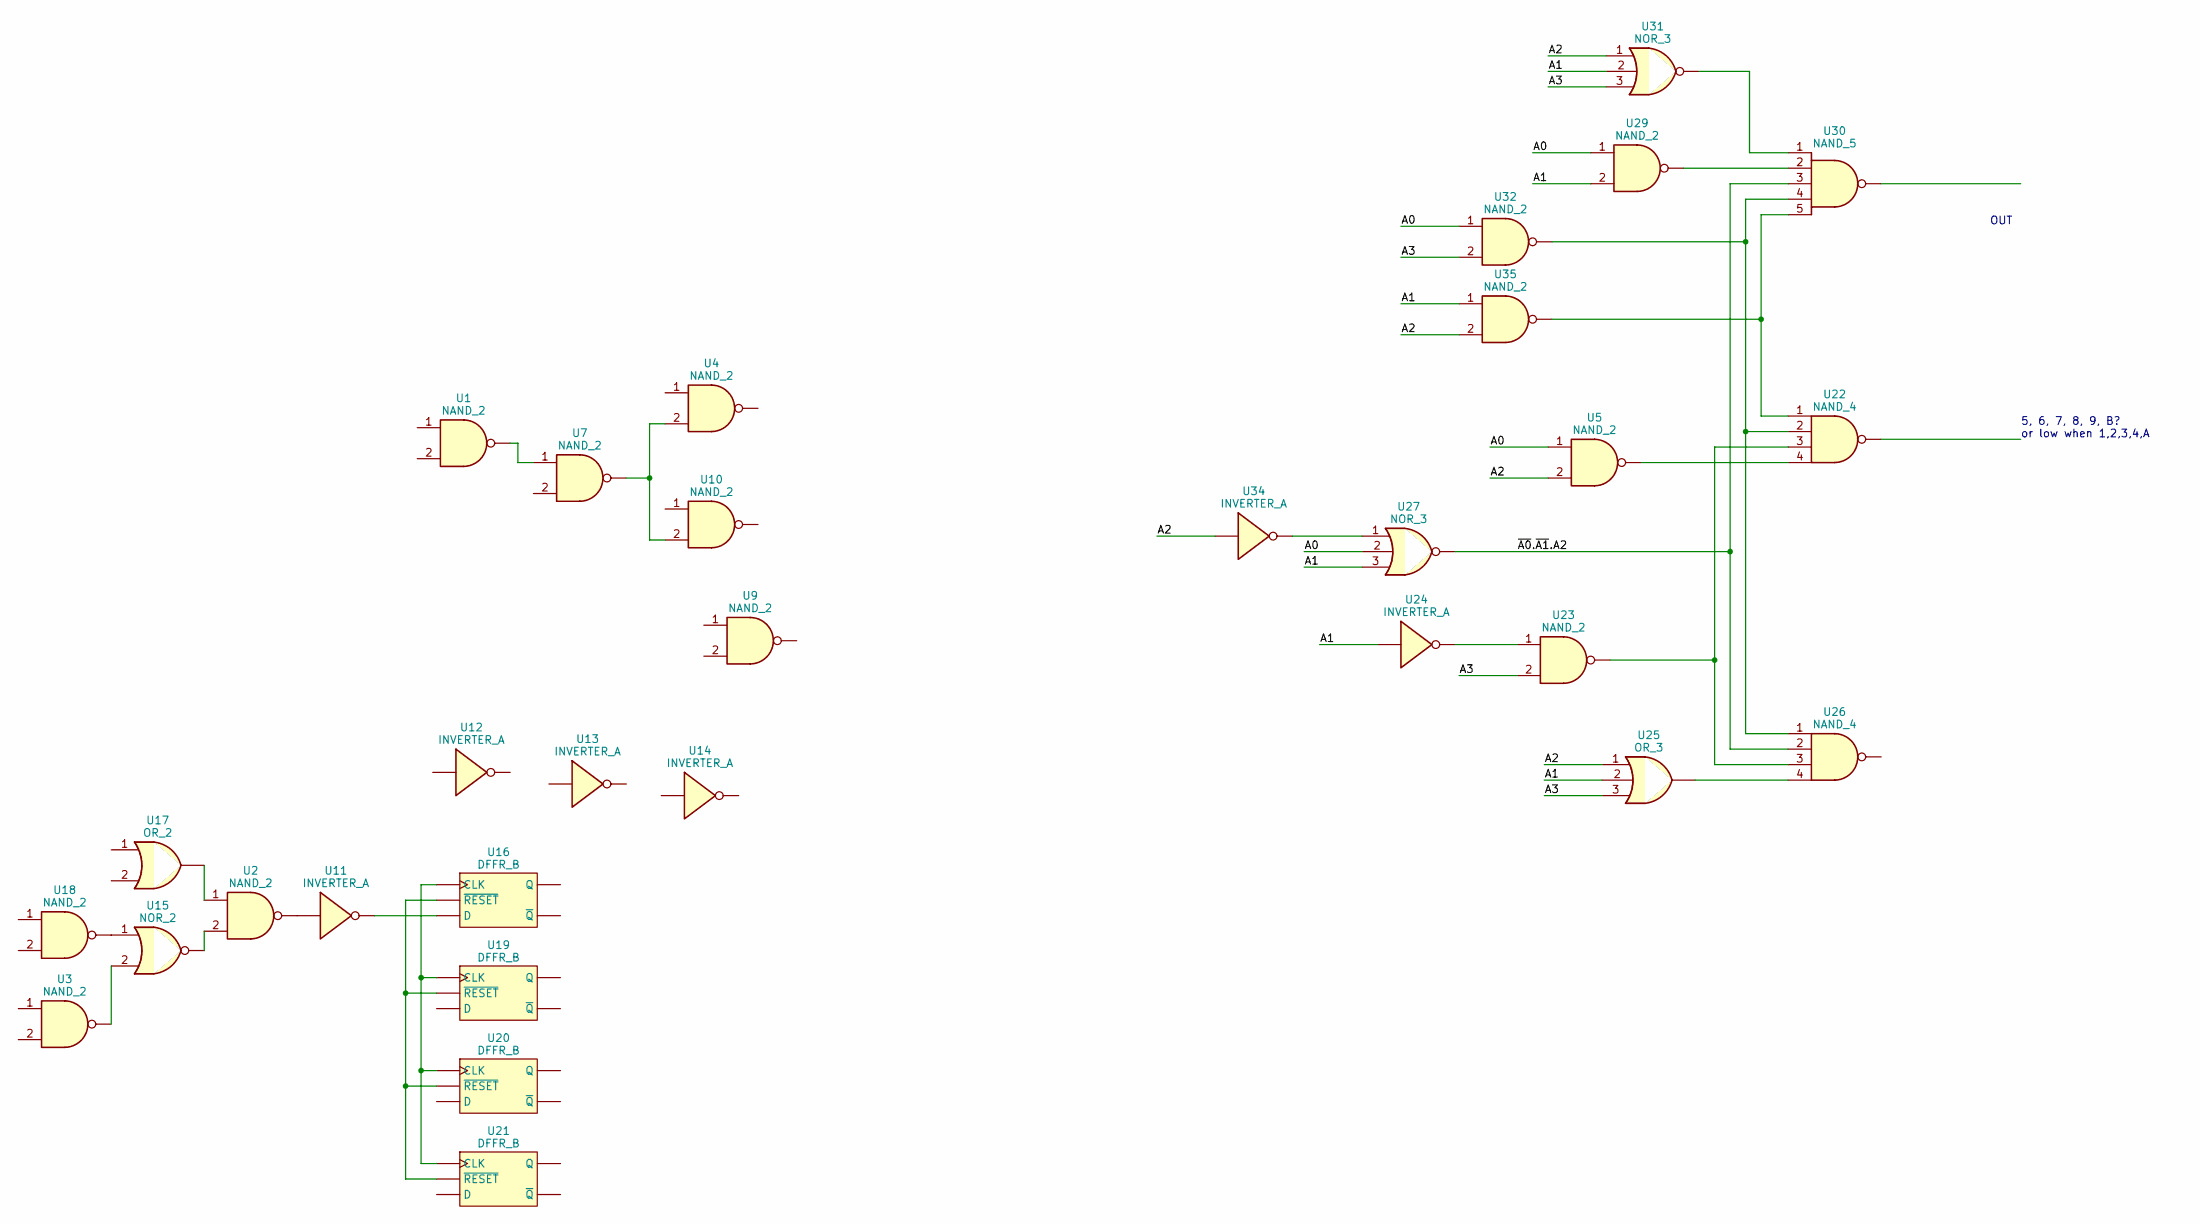
[picture p73: schematic dma.kicad_sch]

Parts:
U1, U2, U3, U4, U5, U7, U9, U10, U18, U23, U29, U32, U35: NAND_2
U11, U12, U13, U14, U24, U34: INVERTER_A
U15: NOR_2
U16, U19, U20, U21: DFFR_B
U17: OR_2
U22, U26: NAND_4
U25: OR_3
U27, U31: NOR_3
U30: NAND_5

Connections:
A0: U5.1, U27.2, U29.1, U32.1
A1: U24.1, U25.2, U27.3, U29.2, U31.2, U35.1
A2: U5.2, U25.1, U31.1, U34.1, U35.2
A3: U23.2, U25.3, U31.3, U32.2
unnamed: U1.3, U7.1
unnamed: U4.2, U7.3, U10.2
unnamed: U2.3, U11.1
unnamed: U11.2, U16.2 (D)
unnamed: U15.1, U18.3
unnamed: U3.3, U15.2
unnamed: U2.2, U15.3
unnamed: U16.1 (~RESET), U16.5 (~RESET), U19.1 (~RESET), U19.5 (~RESET), U20.1 (~RESET), U20.5 (~RESET), U21.1 (~RESET), U21.5 (~RESET)
unnamed: U16.3 (CLK), U16.4 (~CLK), U19.3 (CLK), U19.4 (~CLK), U20.3 (CLK), U20.4 (~CLK), U21.3 (CLK), U21.4 (~CLK)
unnamed: U2.1, U17.3
unnamed: U22.1, U30.5, U35.3
unnamed: U22.2, U26.1, U30.4, U32.3
unnamed: U22.3, U23.3, U26.3
unnamed: U5.3, U22.4
unnamed: U23.1, U24.2
unnamed: U25.4, U26.4
unnamed: U27.1, U34.2
unnamed: U29.3, U30.2
unnamed: U30.1, U31.4
~A0.~A1.A2: U26.2, U27.4, U30.3

Notes on the sheet:
OUT
5, 6, 7, 8, 9, B? or low when 1,2,3,4,A
