rgalland/SNES_S-CPU_Schematics/S-CPU_kicad/dmaconfig_addr.kicad_sch

## KiCad design S-CPU_kicad/dmaconfig_addr.kicad_sch (2024-12-24, an earlier design)

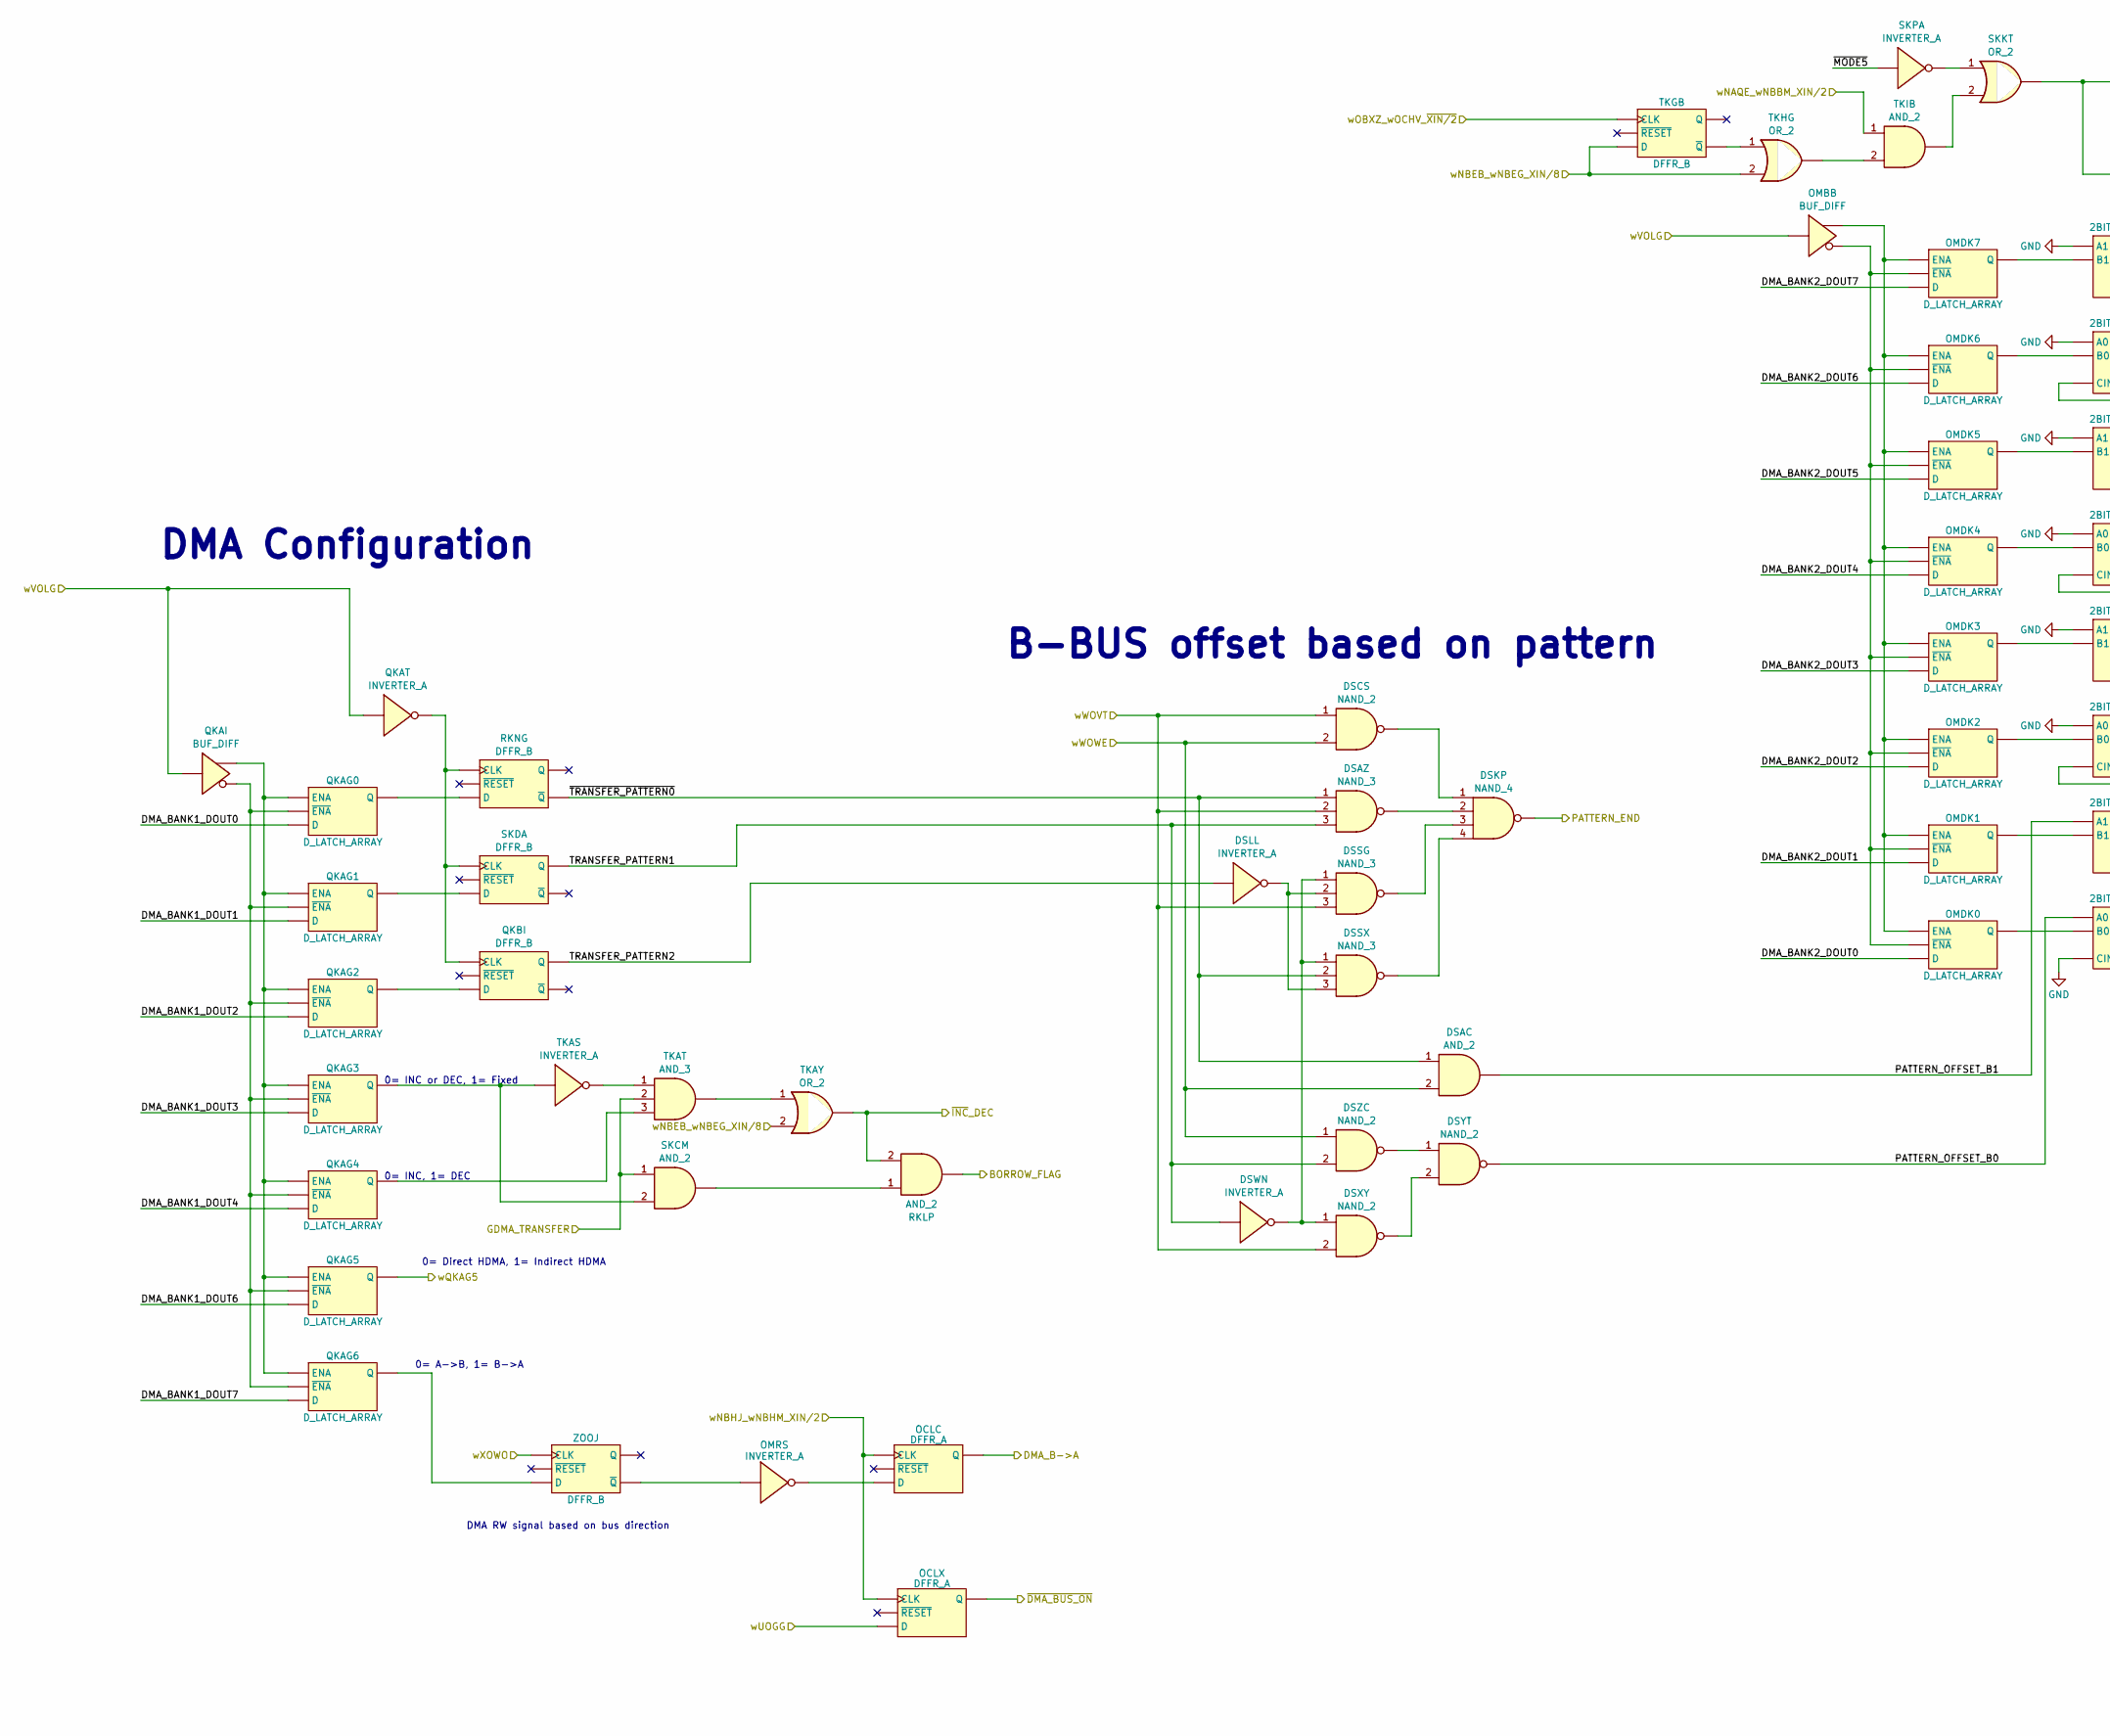
[picture p74: schematic dmaconfig_addr.kicad_sch, part in row 1, column 1]

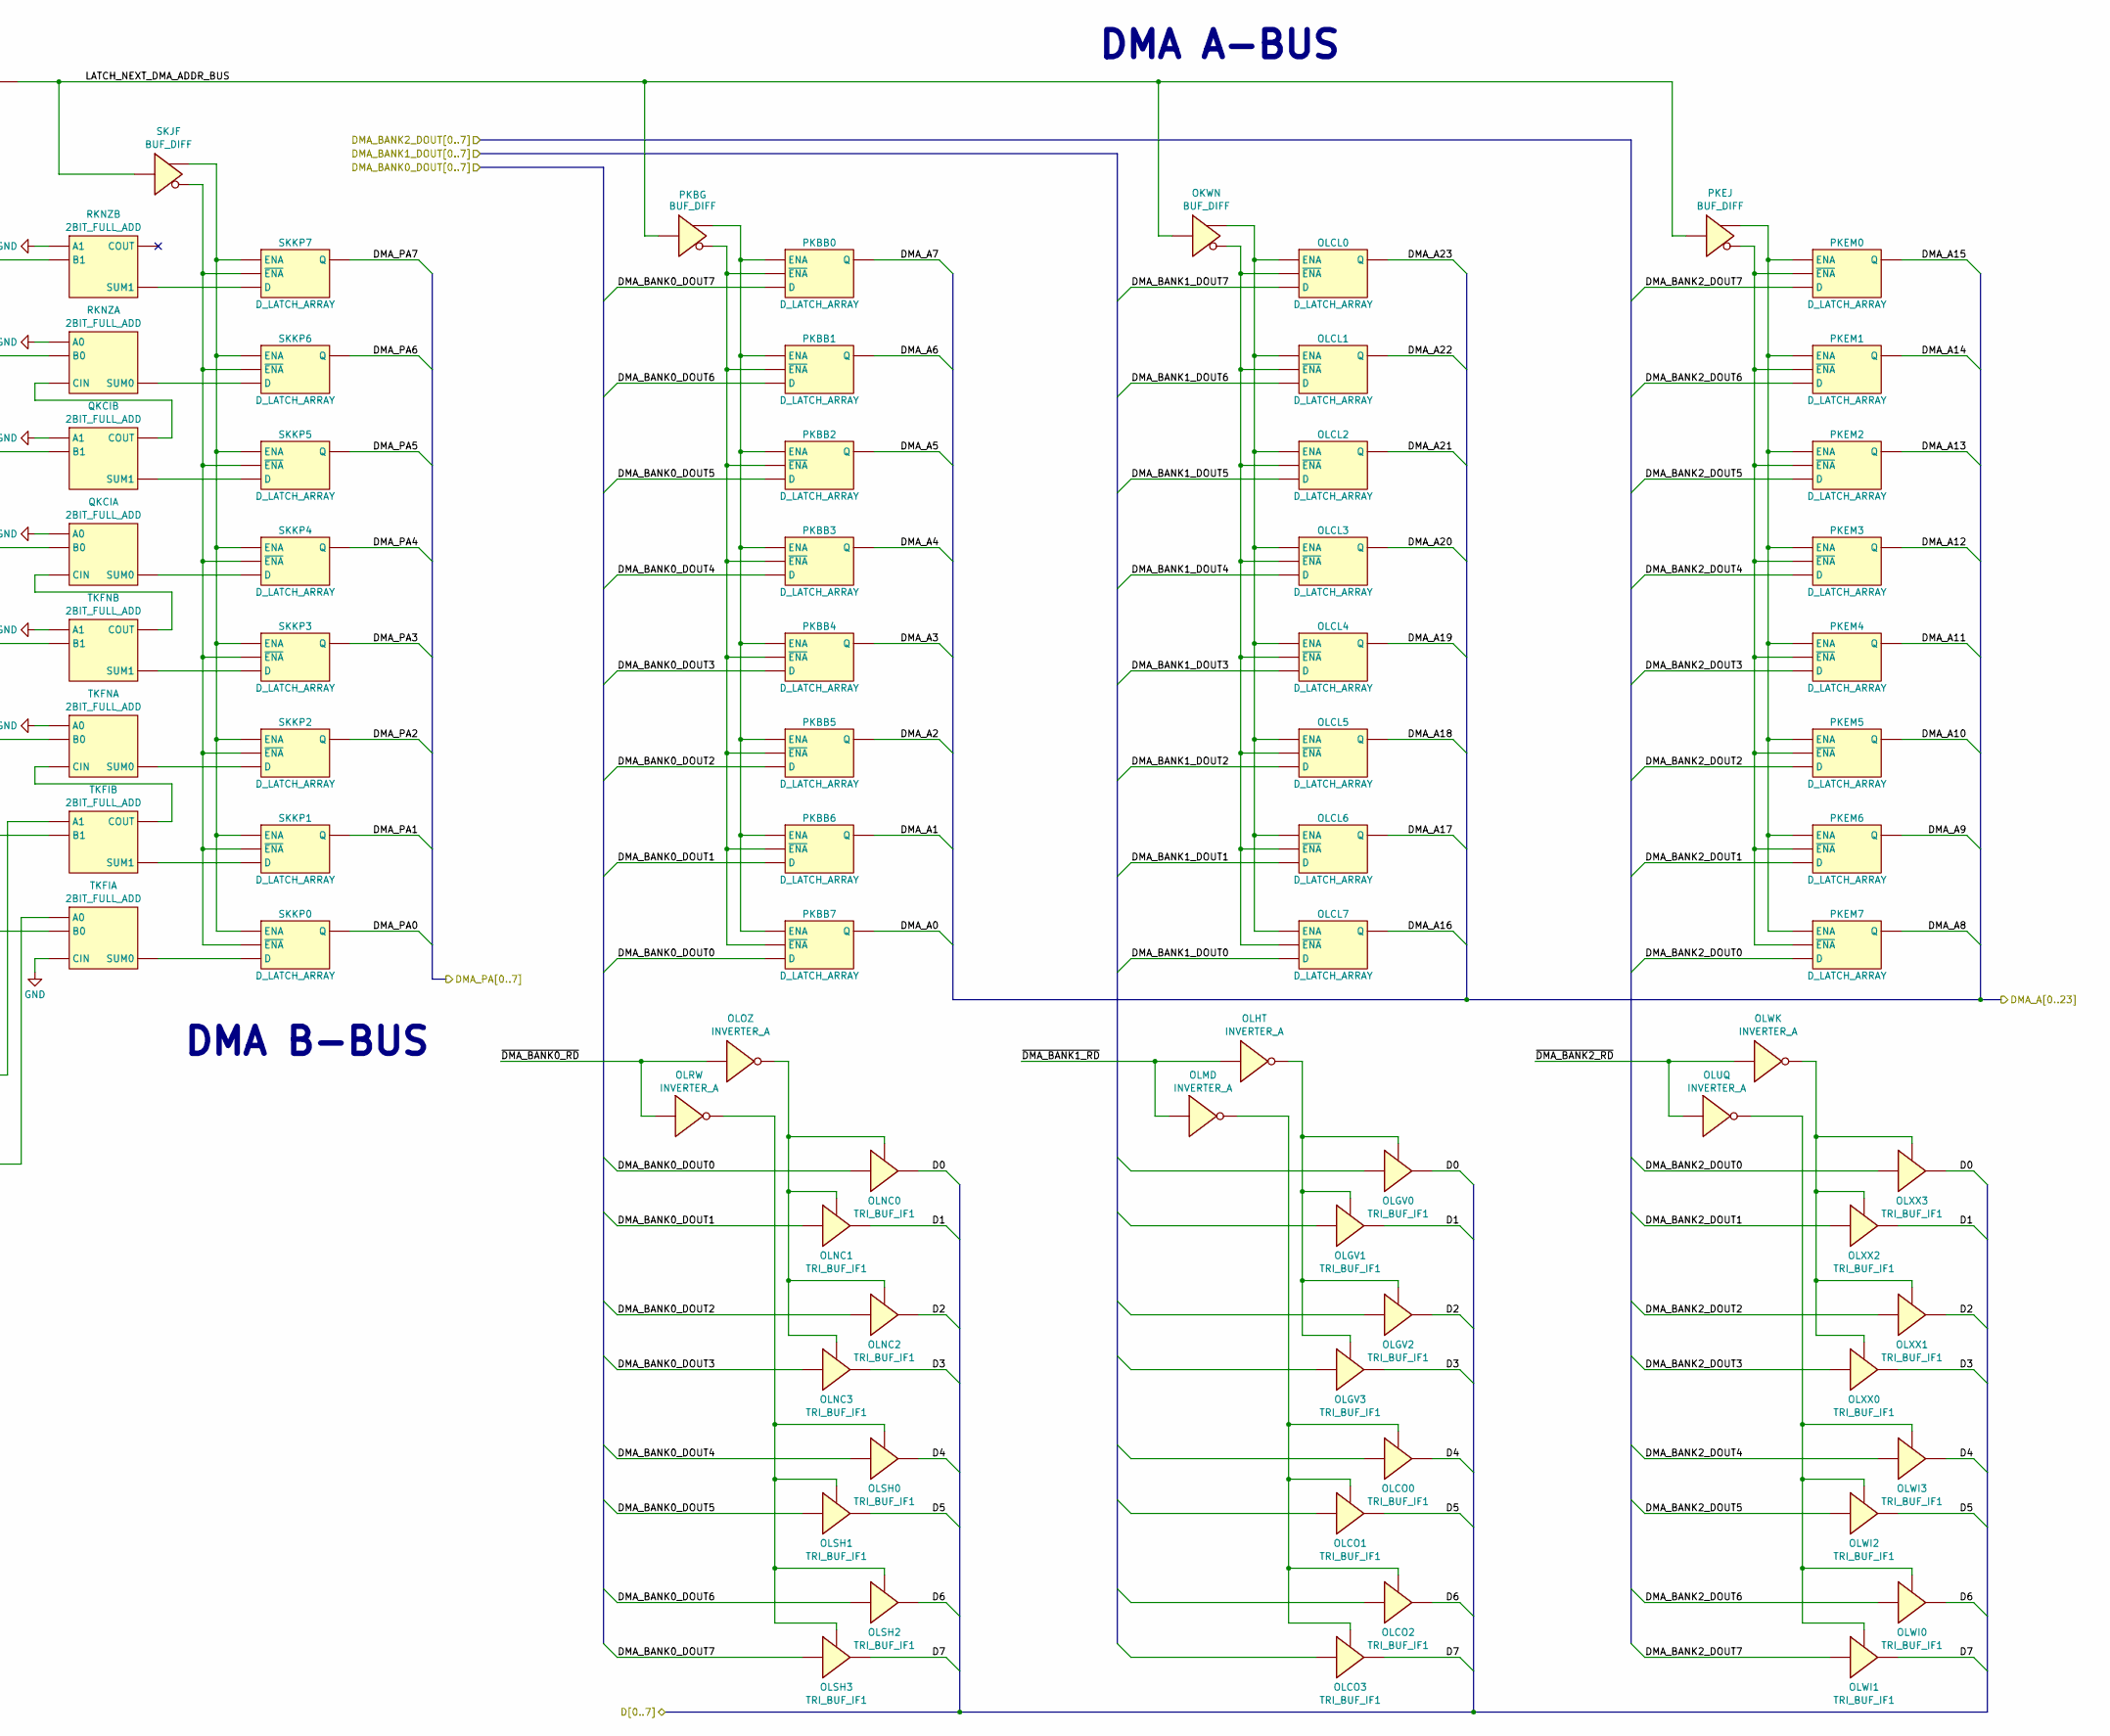
[picture p75: schematic dmaconfig_addr.kicad_sch, part in row 1, column 2]

Parts:
DSAC: AND_2
DSAZ: NAND_3
DSCS: NAND_2
DSKP: NAND_4
DSLL: INVERTER_A
DSSG: NAND_3
DSSX: NAND_3
DSWN: INVERTER_A
DSXY: NAND_2
DSYT: NAND_2
DSZC: NAND_2
OCLC: DFFR_A
OCLX: DFFR_A
OKWN: BUF_DIFF
OLCL0, OLCL1, OLCL2, OLCL3, OLCL4, OLCL5, OLCL6, OLCL7: D_LATCH_ARRAY
OLCO0, OLCO1, OLCO2, OLCO3: TRI_BUF_IF1
OLGV0, OLGV1, OLGV2, OLGV3: TRI_BUF_IF1
OLHT: INVERTER_A
OLMD: INVERTER_A
OLNC0, OLNC1, OLNC2, OLNC3: TRI_BUF_IF1
OLOZ: INVERTER_A
OLRW: INVERTER_A
OLSH0, OLSH1, OLSH2, OLSH3: TRI_BUF_IF1
OLUQ: INVERTER_A
OLWI0, OLWI1, OLWI2, OLWI3: TRI_BUF_IF1
OLWK: INVERTER_A
OLXX0, OLXX1, OLXX2, OLXX3: TRI_BUF_IF1
OMBB: BUF_DIFF
OMDK0, OMDK1, OMDK2, OMDK3, OMDK4, OMDK5, OMDK6, OMDK7: D_LATCH_ARRAY
OMRS: INVERTER_A
PKBB0, PKBB1, PKBB2, PKBB3, PKBB4, PKBB5, PKBB6, PKBB7: D_LATCH_ARRAY
PKBG: BUF_DIFF
PKEJ: BUF_DIFF
PKEM0, PKEM1, PKEM2, PKEM3, PKEM4, PKEM5, PKEM6, PKEM7: D_LATCH_ARRAY
QKAG0, QKAG1, QKAG2, QKAG3, QKAG4, QKAG5, QKAG6: D_LATCH_ARRAY
QKAI: BUF_DIFF
QKAT: INVERTER_A
QKBI: DFFR_B
QKCI: 2BIT_FULL_ADD
RKLP: AND_2
RKNG: DFFR_B
RKNZ: 2BIT_FULL_ADD
SKCM: AND_2
SKDA: DFFR_B
SKJF: BUF_DIFF
SKKP0, SKKP1, SKKP2, SKKP3, SKKP4, SKKP5, SKKP6, SKKP7: D_LATCH_ARRAY
SKKT: OR_2
SKPA: INVERTER_A
TKAS: INVERTER_A
TKAT: AND_3
TKAY: OR_2
TKFI: 2BIT_FULL_ADD
TKFN: 2BIT_FULL_ADD
TKGB: DFFR_B
TKHG: OR_2
TKIB: AND_2
ZOOJ: DFFR_B

Connections:
BORROW_FLAG: RKLP.3
D0: OLGV0.4, OLNC0.4, OLXX3.4
D1: OLGV1.4, OLNC1.4, OLXX2.4
D2: OLGV2.4, OLNC2.4, OLXX1.4
D3: OLGV3.4, OLNC3.4, OLXX0.4
D4: OLCO0.4, OLSH0.4, OLWI3.4
D5: OLCO1.4, OLSH1.4, OLWI2.4
D6: OLCO2.4, OLSH2.4, OLWI0.4
D7: OLCO3.4, OLSH3.4, OLWI1.4
DMA_A0: PKBB7.4 (Q)
DMA_A1: PKBB6.4 (Q)
DMA_A2: PKBB5.4 (Q)
DMA_A3: PKBB4.4 (Q)
DMA_A4: PKBB3.4 (Q)
DMA_A5: PKBB2.4 (Q)
DMA_A6: PKBB1.4 (Q)
DMA_A7: PKBB0.4 (Q)
DMA_A8: PKEM7.4 (Q)
DMA_A9: PKEM6.4 (Q)
DMA_A10: PKEM5.4 (Q)
DMA_A11: PKEM4.4 (Q)
DMA_A12: PKEM3.4 (Q)
DMA_A13: PKEM2.4 (Q)
DMA_A14: PKEM1.4 (Q)
DMA_A15: PKEM0.4 (Q)
DMA_A16: OLCL7.4 (Q)
DMA_A17: OLCL6.4 (Q)
DMA_A18: OLCL5.4 (Q)
DMA_A19: OLCL4.4 (Q)
DMA_A20: OLCL3.4 (Q)
DMA_A21: OLCL2.4 (Q)
DMA_A22: OLCL1.4 (Q)
DMA_A23: OLCL0.4 (Q)
DMA_B->A: OCLC.6 (Q)
DMA_BANK0_DOUT0: OLNC0.1 (IN), OLNC0.3 (IN), PKBB7.2 (D)
DMA_BANK0_DOUT1: OLNC1.1 (IN), OLNC1.3 (IN), PKBB6.2 (D)
DMA_BANK0_DOUT2: OLNC2.1 (IN), OLNC2.3 (IN), PKBB5.2 (D)
DMA_BANK0_DOUT3: OLNC3.1 (IN), OLNC3.3 (IN), PKBB4.2 (D)
DMA_BANK0_DOUT4: OLSH0.1 (IN), OLSH0.3 (IN), PKBB3.2 (D)
DMA_BANK0_DOUT5: OLSH1.1 (IN), OLSH1.3 (IN), PKBB2.2 (D)
DMA_BANK0_DOUT6: OLSH2.1 (IN), OLSH2.3 (IN), PKBB1.2 (D)
DMA_BANK0_DOUT7: OLSH3.1 (IN), OLSH3.3 (IN), PKBB0.2 (D)
DMA_BANK1_DOUT0: OLCL7.2 (D), QKAG0.2 (D)
DMA_BANK1_DOUT1: OLCL6.2 (D), QKAG1.2 (D)
DMA_BANK1_DOUT2: OLCL5.2 (D), QKAG2.2 (D)
DMA_BANK1_DOUT3: OLCL4.2 (D), QKAG3.2 (D)
DMA_BANK1_DOUT4: OLCL3.2 (D), QKAG4.2 (D)
DMA_BANK1_DOUT5: OLCL2.2 (D)
DMA_BANK1_DOUT6: OLCL1.2 (D), QKAG5.2 (D)
DMA_BANK1_DOUT7: OLCL0.2 (D), QKAG6.2 (D)
DMA_BANK2_DOUT0: OLXX3.1 (IN), OLXX3.3 (IN), OMDK0.2 (D), PKEM7.2 (D)
DMA_BANK2_DOUT1: OLXX2.1 (IN), OLXX2.3 (IN), OMDK1.2 (D), PKEM6.2 (D)
DMA_BANK2_DOUT2: OLXX1.1 (IN), OLXX1.3 (IN), OMDK2.2 (D), PKEM5.2 (D)
DMA_BANK2_DOUT3: OLXX0.1 (IN), OLXX0.3 (IN), OMDK3.2 (D), PKEM4.2 (D)
DMA_BANK2_DOUT4: OLWI3.1 (IN), OLWI3.3 (IN), OMDK4.2 (D), PKEM3.2 (D)
DMA_BANK2_DOUT5: OLWI2.1 (IN), OLWI2.3 (IN), OMDK5.2 (D), PKEM2.2 (D)
DMA_BANK2_DOUT6: OLWI0.1 (IN), OLWI0.3 (IN), OMDK6.2 (D), PKEM1.2 (D)
DMA_BANK2_DOUT7: OLWI1.1 (IN), OLWI1.3 (IN), OMDK7.2 (D), PKEM0.2 (D)
DMA_PA0: SKKP0.4 (Q)
DMA_PA1: SKKP1.4 (Q)
DMA_PA2: SKKP2.4 (Q)
DMA_PA3: SKKP3.4 (Q)
DMA_PA4: SKKP4.4 (Q)
DMA_PA5: SKKP5.4 (Q)
DMA_PA6: SKKP6.4 (Q)
DMA_PA7: SKKP7.4 (Q)
GDMA_TRANSFER: SKCM.1, TKAT.2
GND: QKCI.13 (A0), QKCI.24 (A1), RKNZ.13 (A0), RKNZ.24 (A1), TKFI.2 (CIN), TKFN.13 (A0), TKFN.24 (A1)
LATCH_NEXT_DMA_ADDR_BUS: OKWN.1, PKBG.1, PKEJ.1, SKJF.1, SKKT.3
unnamed: DSAZ.4, DSKP.2
unnamed: DSCS.3, DSKP.1
unnamed: DSKP.3, DSSG.4
unnamed: DSKP.4, DSSX.4
unnamed: DSLL.2, DSSG.2, DSSX.3
unnamed: DSSG.1, DSSX.1, DSWN.2, DSXY.1
unnamed: DSXY.3, DSYT.2
unnamed: DSYT.1, DSZC.3
unnamed: OCLC.1 (~RESET), OCLC.5 (~RESET)
unnamed: OCLC.2 (D), OMRS.2
unnamed: OCLX.1 (~RESET), OCLX.5 (~RESET)
unnamed: OKWN.2, OLCL0.1 (~ENA), OLCL0.3 (ENA), OLCL1.1 (~ENA), OLCL1.3 (ENA), OLCL2.1 (~ENA), OLCL2.3 (ENA), OLCL3.1 (~ENA), OLCL3.3 (ENA), OLCL4.1 (~ENA), OLCL4.3 (ENA), OLCL5.1 (~ENA), OLCL5.3 (ENA), OLCL6.1 (~ENA), OLCL6.3 (ENA), OLCL7.1 (~ENA), OLCL7.3 (ENA)
unnamed: OLCO0.1 (IN), OLCO0.3 (IN)
unnamed: OLCO0.2 (~ENA), OLCO1.2 (~ENA), OLCO2.2 (~ENA), OLCO3.2 (~ENA), OLMD.2
unnamed: OLCO1.1 (IN), OLCO1.3 (IN)
unnamed: OLCO2.1 (IN), OLCO2.3 (IN)
unnamed: OLCO3.1 (IN), OLCO3.3 (IN)
unnamed: OLGV0.1 (IN), OLGV0.3 (IN)
unnamed: OLGV0.2 (~ENA), OLGV1.2 (~ENA), OLGV2.2 (~ENA), OLGV3.2 (~ENA), OLHT.2
unnamed: OLGV1.1 (IN), OLGV1.3 (IN)
unnamed: OLGV2.1 (IN), OLGV2.3 (IN)
unnamed: OLGV3.1 (IN), OLGV3.3 (IN)
unnamed: OLNC0.2 (~ENA), OLNC1.2 (~ENA), OLNC2.2 (~ENA), OLNC3.2 (~ENA), OLOZ.2
unnamed: OLRW.2, OLSH0.2 (~ENA), OLSH1.2 (~ENA), OLSH2.2 (~ENA), OLSH3.2 (~ENA)
unnamed: OLUQ.2, OLWI0.2 (~ENA), OLWI1.2 (~ENA), OLWI2.2 (~ENA), OLWI3.2 (~ENA)
unnamed: OLWK.2, OLXX0.2 (~ENA), OLXX1.2 (~ENA), OLXX2.2 (~ENA), OLXX3.2 (~ENA)
unnamed: OMBB.2, OMDK0.1 (~ENA), OMDK0.3 (ENA), OMDK1.1 (~ENA), OMDK1.3 (ENA), OMDK2.1 (~ENA), OMDK2.3 (ENA), OMDK3.1 (~ENA), OMDK3.3 (ENA), OMDK4.1 (~ENA), OMDK4.3 (ENA), OMDK5.1 (~ENA), OMDK5.3 (ENA), OMDK6.1 (~ENA), OMDK6.3 (ENA), OMDK7.1 (~ENA), OMDK7.3 (ENA)
unnamed: OMDK0.4 (Q), TKFI.9 (B0)
unnamed: OMDK1.4 (Q), TKFI.23 (B1)
unnamed: OMDK2.4 (Q), TKFN.9 (B0)
unnamed: OMDK3.4 (Q), TKFN.23 (B1)
unnamed: OMDK4.4 (Q), QKCI.9 (B0)
unnamed: OMDK5.4 (Q), QKCI.23 (B1)
unnamed: OMDK6.4 (Q), RKNZ.9 (B0)
unnamed: OMDK7.4 (Q), RKNZ.23 (B1)
unnamed: OMRS.1, ZOOJ.6 (~Q)
unnamed: PKBB0.1 (~ENA), PKBB1.1 (~ENA), PKBB2.1 (~ENA), PKBB3.1 (~ENA), PKBB4.1 (~ENA), PKBB5.1 (~ENA), PKBB6.1 (~ENA), PKBB7.1 (~ENA), PKBG.2
unnamed: PKBB0.3 (ENA), PKBB1.3 (ENA), PKBB2.3 (ENA), PKBB3.3 (ENA), PKBB4.3 (ENA), PKBB5.3 (ENA), PKBB6.3 (ENA), PKBB7.3 (ENA), PKBG.2
unnamed: PKEJ.2, PKEM0.1 (~ENA), PKEM0.3 (ENA), PKEM1.1 (~ENA), PKEM1.3 (ENA), PKEM2.1 (~ENA), PKEM2.3 (ENA), PKEM3.1 (~ENA), PKEM3.3 (ENA), PKEM4.1 (~ENA), PKEM4.3 (ENA), PKEM5.1 (~ENA), PKEM5.3 (ENA), PKEM6.1 (~ENA), PKEM6.3 (ENA), PKEM7.1 (~ENA), PKEM7.3 (ENA)
unnamed: QKAG0.1 (~ENA), QKAG1.1 (~ENA), QKAG2.1 (~ENA), QKAG3.1 (~ENA), QKAG4.1 (~ENA), QKAG5.1 (~ENA), QKAG6.1 (~ENA), QKAI.2
unnamed: QKAG0.3 (ENA), QKAG1.3 (ENA), QKAG2.3 (ENA), QKAG3.3 (ENA), QKAG4.3 (ENA), QKAG5.3 (ENA), QKAG6.3 (ENA), QKAI.2
unnamed: QKAG0.4 (Q), RKNG.2 (D)
unnamed: QKAG1.4 (Q), SKDA.2 (D)
unnamed: QKAG2.4 (Q), QKBI.2 (D)
unnamed: QKAG3.4 (Q), SKCM.2, TKAS.1
unnamed: QKAG4.4 (Q), TKAT.3
unnamed: QKAG6.4 (Q), ZOOJ.2 (D)
unnamed: QKAT.2, QKBI.3 (CLK), QKBI.4 (~CLK), RKNG.3 (CLK), RKNG.4 (~CLK), SKDA.3 (CLK), SKDA.4 (~CLK)
unnamed: QKBI.1 (~RESET), QKBI.5 (~RESET)
unnamed: QKCI.2 (CIN), TKFN.28 (COUT)
unnamed: QKCI.4 (SUM0), SKKP4.2 (D)
unnamed: QKCI.17 (SUM1), SKKP5.2 (D)
unnamed: QKCI.28 (COUT), RKNZ.2 (CIN)
unnamed: RKLP.1, SKCM.3
unnamed: RKNG.1 (~RESET), RKNG.5 (~RESET)
unnamed: RKNZ.4 (SUM0), SKKP6.2 (D)
unnamed: RKNZ.17 (SUM1), SKKP7.2 (D)
unnamed: SKDA.1 (~RESET), SKDA.5 (~RESET)
unnamed: SKJF.2, SKKP0.1 (~ENA), SKKP0.3 (ENA), SKKP1.1 (~ENA), SKKP1.3 (ENA), SKKP2.1 (~ENA), SKKP2.3 (ENA), SKKP3.1 (~ENA), SKKP3.3 (ENA), SKKP4.1 (~ENA), SKKP4.3 (ENA), SKKP5.1 (~ENA), SKKP5.3 (ENA), SKKP6.1 (~ENA), SKKP6.3 (ENA), SKKP7.1 (~ENA), SKKP7.3 (ENA)
unnamed: SKKP0.2 (D), TKFI.4 (SUM0)
unnamed: SKKP1.2 (D), TKFI.17 (SUM1)
unnamed: SKKP2.2 (D), TKFN.4 (SUM0)
unnamed: SKKP3.2 (D), TKFN.17 (SUM1)
unnamed: SKKT.1, SKPA.2
unnamed: SKKT.2, TKIB.3
unnamed: TKAS.2, TKAT.1
unnamed: TKAT.4, TKAY.1
unnamed: TKFI.28 (COUT), TKFN.2 (CIN)
unnamed: TKGB.1 (~RESET), TKGB.5 (~RESET)
unnamed: TKGB.6 (~Q), TKHG.1
unnamed: TKHG.3, TKIB.2
unnamed: ZOOJ.1 (~RESET), ZOOJ.5 (~RESET)
PATTERN_END: DSKP.5
PATTERN_OFFSET_B0: DSYT.3, TKFI.13 (A0)
PATTERN_OFFSET_B1: DSAC.3, TKFI.24 (A1)
TRANSFER_PATTERN1: DSAZ.3, DSWN.1, DSZC.2, SKDA.7 (Q)
TRANSFER_PATTERN2: DSLL.1, QKBI.7 (Q)
wNAQE_wNBBM_XIN/2: TKIB.1
wNBEB_wNBEG_XIN/8: TKAY.2, TKGB.2 (D), TKHG.2
wNBHJ_wNBHM_XIN/2: OCLC.3 (CLK), OCLC.4 (~CLK), OCLX.3 (CLK), OCLX.4 (~CLK)
wOBXZ_wOCHV_~XIN/2: TKGB.3 (CLK), TKGB.4 (~CLK)
wQKAG5: QKAG5.4 (Q)
wUOGG: OCLX.2 (D)
wVOLG: OMBB.1, QKAI.1, QKAT.1
wWOVT: DSAZ.2, DSCS.1, DSSG.3, DSXY.2
wWOWE: DSAC.2, DSCS.2, DSZC.1
wXOWO: ZOOJ.3 (CLK), ZOOJ.4 (~CLK)
~DMA_BANK0_RD: OLOZ.1, OLRW.1
~DMA_BANK1_RD: OLHT.1, OLMD.1
~DMA_BANK2_RD: OLUQ.1, OLWK.1
~DMA_BUS_ON: OCLX.6 (Q)
~INC_DEC: RKLP.2, TKAY.3
~MODE5: SKPA.1
~TRANSFER_PATTERN0: DSAC.1, DSAZ.1, DSSX.2, RKNG.6 (~Q)

Notes on the sheet:
DMA B-BUS
B-BUS offset based on pattern
DMA A-BUS
DMA RW signal based on bus direction
0= Direct HDMA, 1= Indirect HDMA
0= INC, 1= DEC
0= INC or DEC, 1= Fixed
0= A->B, 1= B->A
DMA Configuration
