rgalland/SNES_S-CPU_Schematics/S-CPU_kicad/dmalogic.kicad_sch

## KiCad design S-CPU_kicad/dmalogic.kicad_sch (2024-12-24, an earlier design)

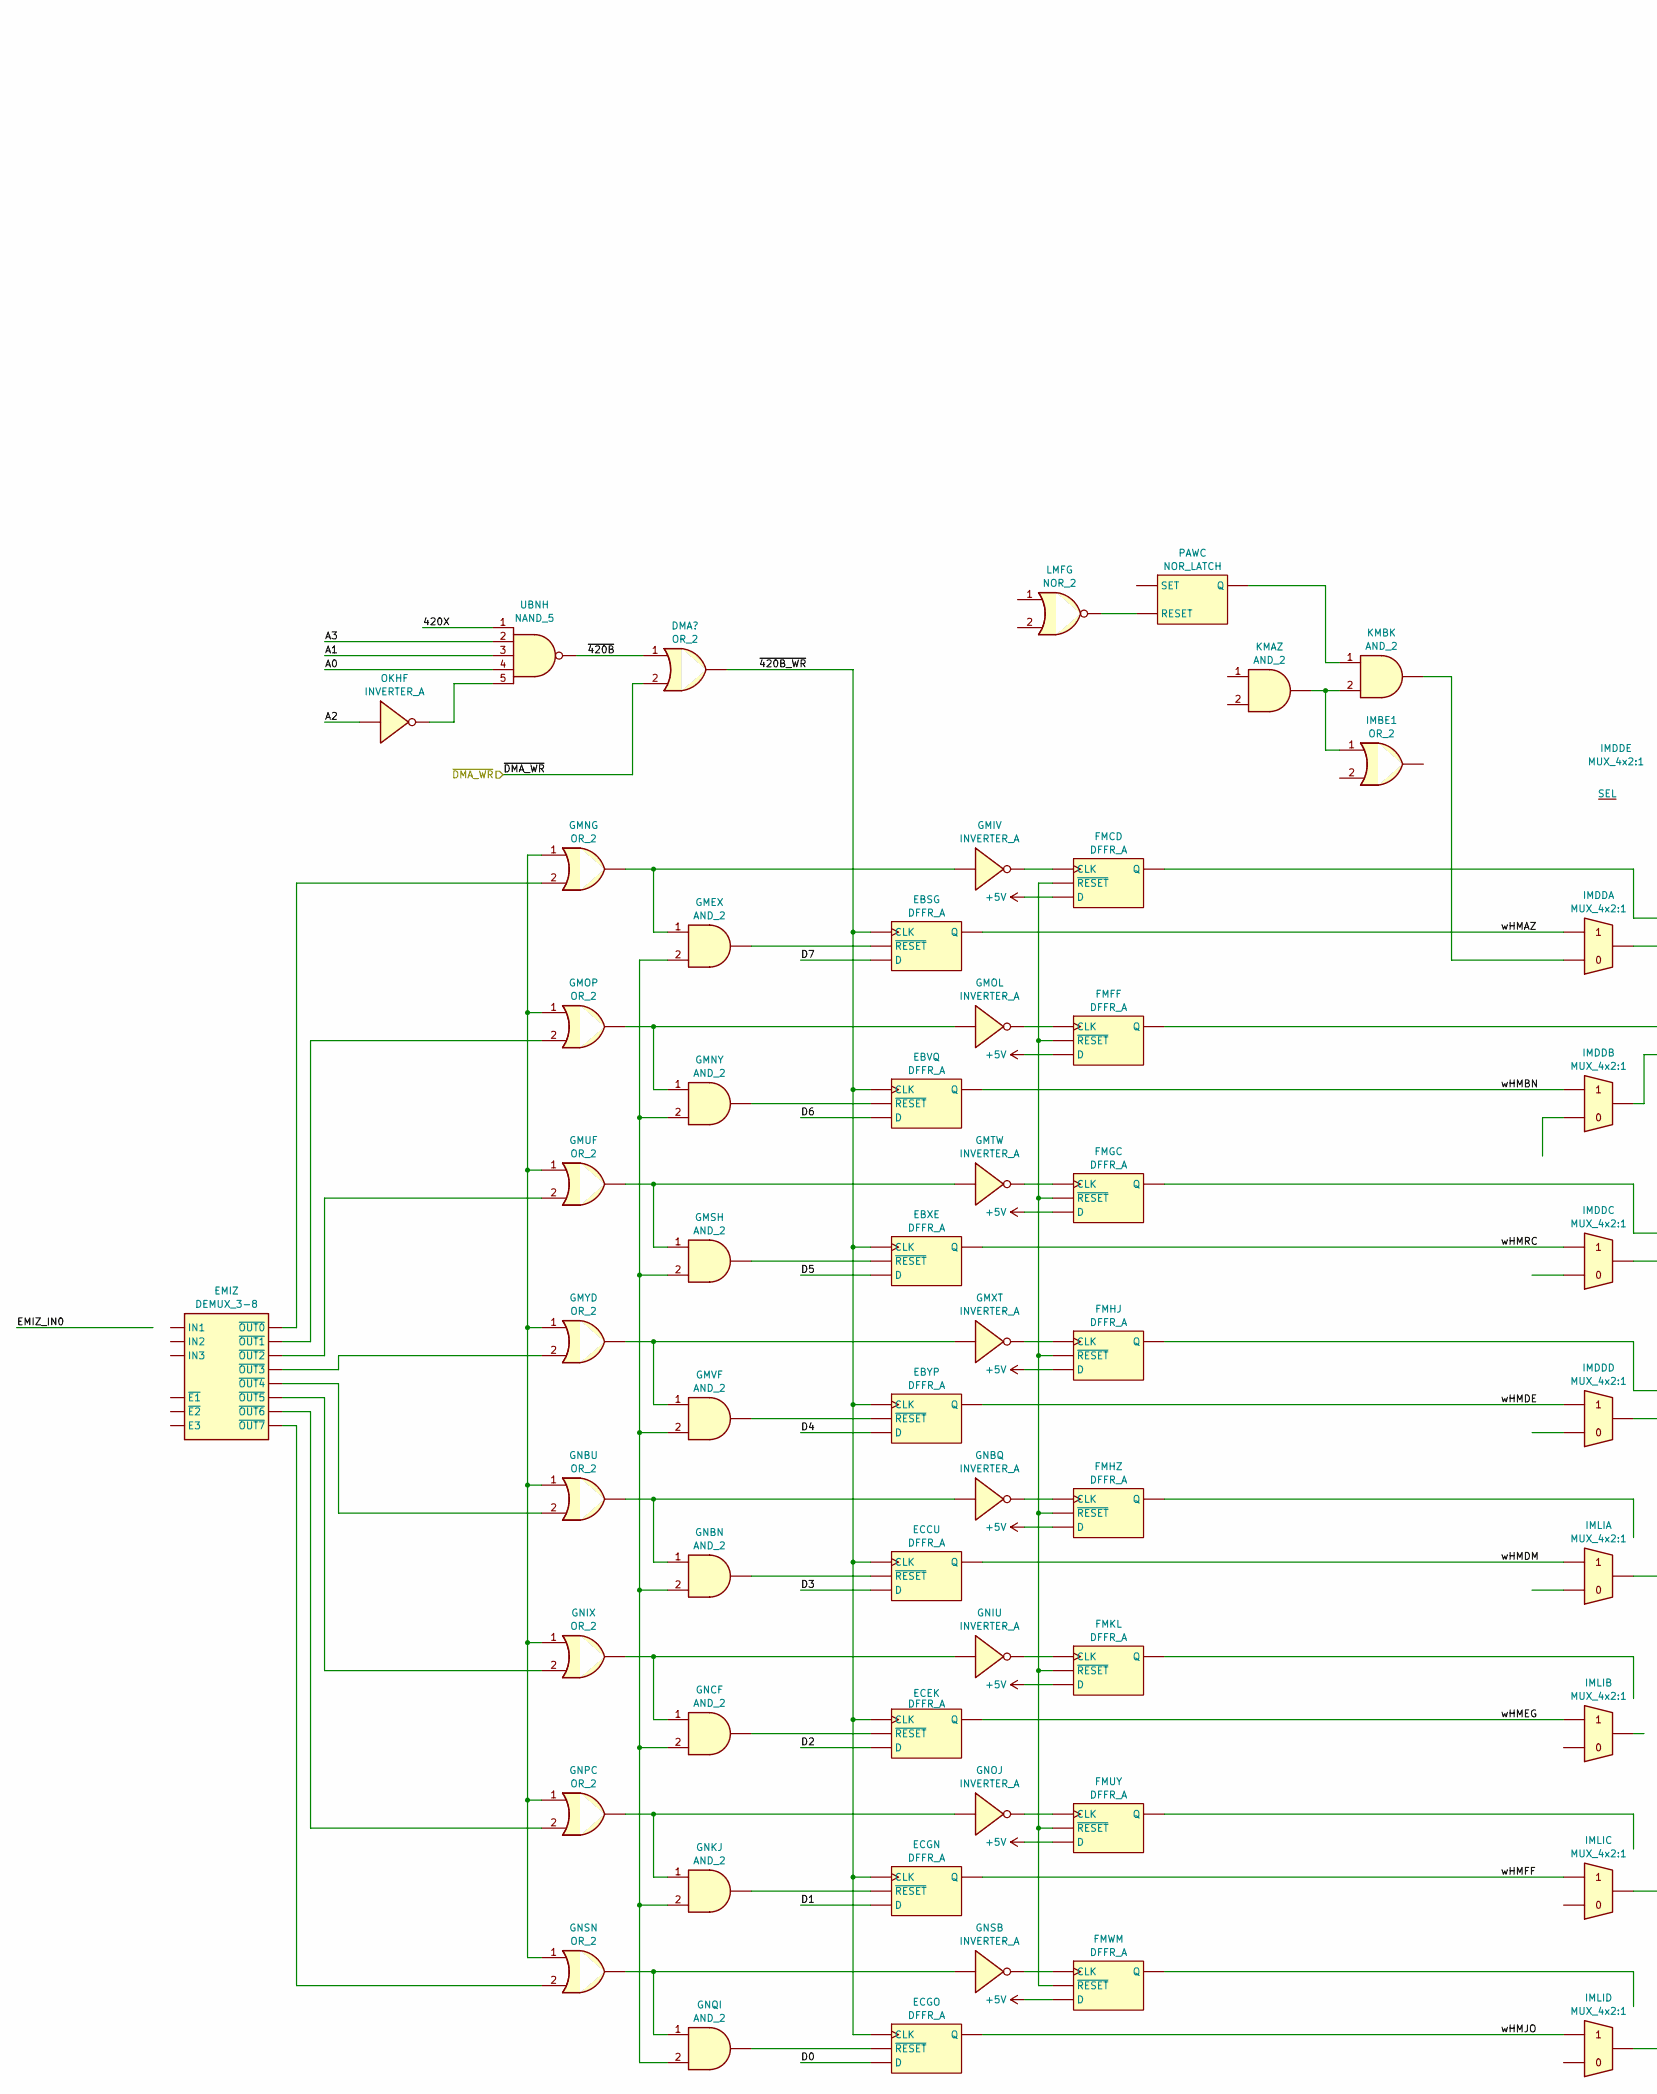
[picture p76: schematic dmalogic.kicad_sch, part in row 1, column 1]

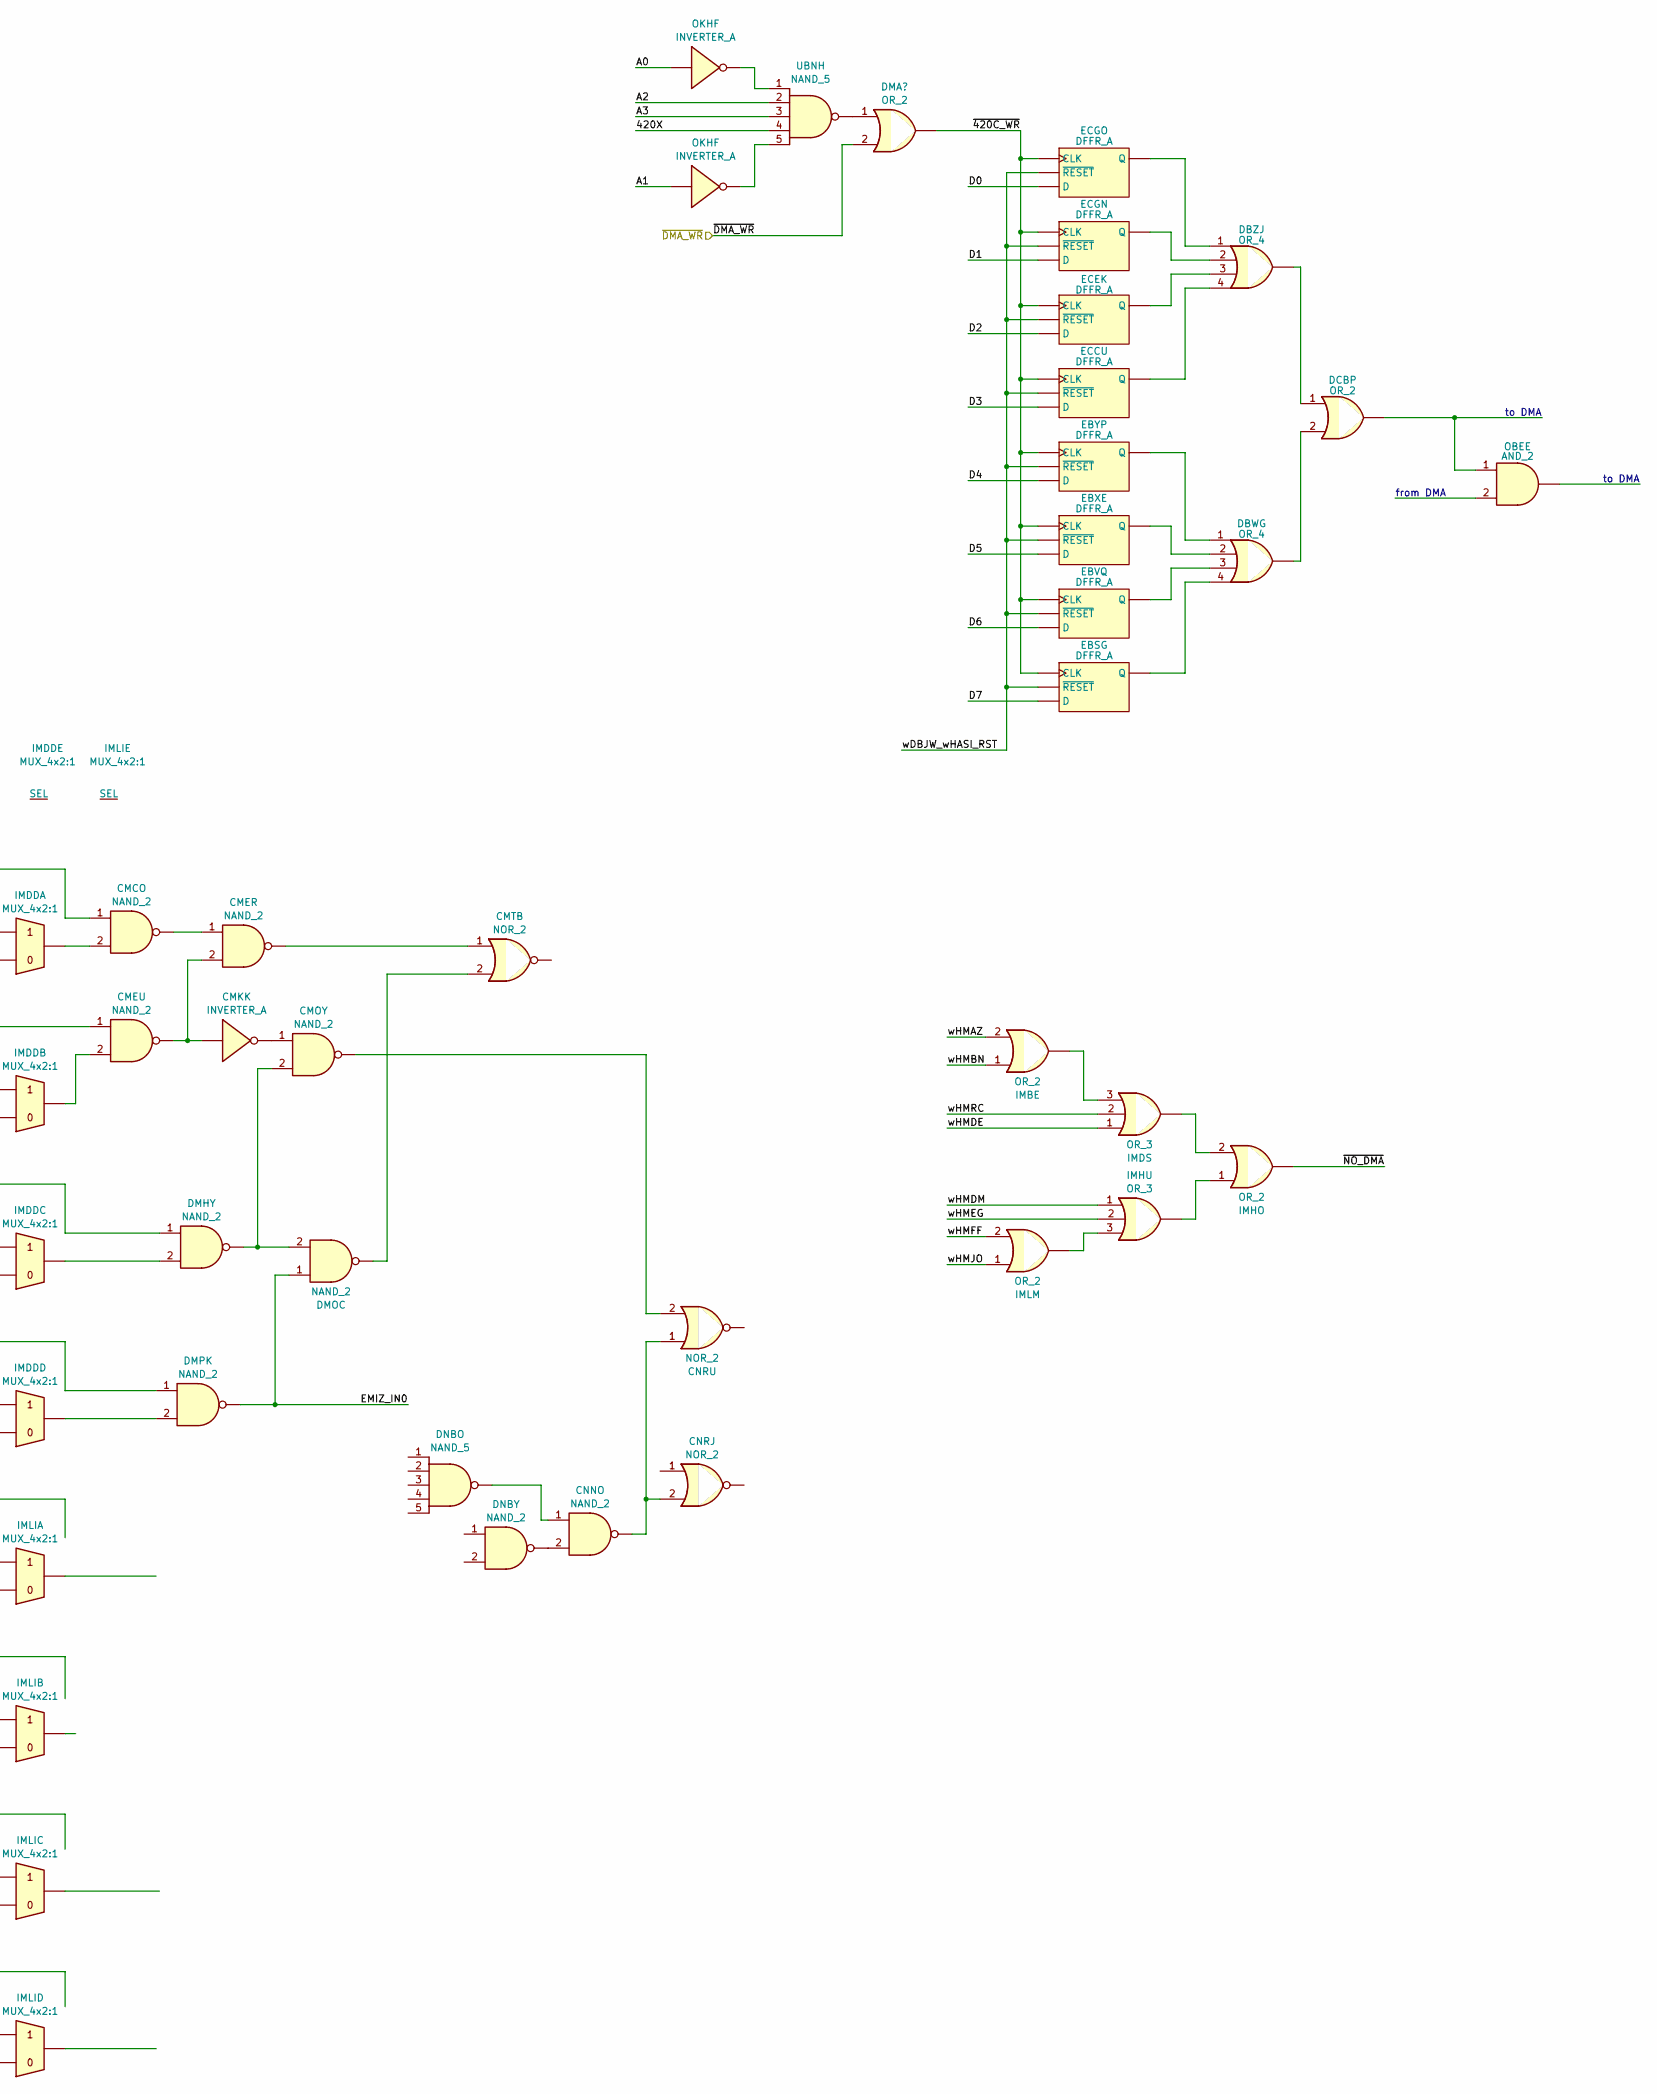
[picture p77: schematic dmalogic.kicad_sch, part in row 1, column 2]

Parts:
CMCO: NAND_2
CMER: NAND_2
CMEU: NAND_2
CMKK: INVERTER_A
CMOY: NAND_2
CMTB: NOR_2
CNNO: NAND_2
CNRJ: NOR_2
CNRU: NOR_2
DBWG: OR_4
DBZJ: OR_4
DCBP: OR_2
DMA24: OR_2
DMHY: NAND_2
DMOC: NAND_2
DMPK: NAND_2
DNBO: NAND_5
DNBY: NAND_2
EBSG: DFFR_A
EBVQ: DFFR_A
EBXE: DFFR_A
EBYP: DFFR_A
ECCU: DFFR_A
ECEK: DFFR_A
ECGN: DFFR_A
ECGO: DFFR_A
EMIZ: DEMUX_3-8
FMCD: DFFR_A
FMFF: DFFR_A
FMGC: DFFR_A
FMHJ: DFFR_A
FMHZ: DFFR_A
FMKL: DFFR_A
FMUY: DFFR_A
FMWM: DFFR_A
GMEX: AND_2
GMIV: INVERTER_A
GMNG: OR_2
GMNY: AND_2
GMOL: INVERTER_A
GMOP: OR_2
GMSH: AND_2
GMTW: INVERTER_A
GMUF: OR_2
GMVF: AND_2
GMXT: INVERTER_A
GMYD: OR_2
GNBN: AND_2
GNBQ: INVERTER_A
GNBU: OR_2
GNCF: AND_2
GNIU: INVERTER_A
GNIX: OR_2
GNKJ: AND_2
GNOJ: INVERTER_A
GNPC: OR_2
GNQI: AND_2
GNSB: INVERTER_A
GNSN: OR_2
HMDF: OR_2
IMBE, IMBE1: OR_2
IMDD: MUX_4x2:1
IMDS: OR_3
IMHO: OR_2
IMHU: OR_3
IMLI: MUX_4x2:1
IMLM: OR_2
KMAZ: AND_2
KMBK: AND_2
LMFG: NOR_2
OBEE: AND_2
OKHF: INVERTER_A
PAWC: NOR_LATCH
UBNH: NAND_5

Connections:
420X: UBNH.1, UBNH.4
+5V: FMCD.2 (D), FMFF.2 (D), FMGC.2 (D), FMHJ.2 (D), FMHZ.2 (D), FMKL.2 (D), FMUY.2 (D), FMWM.2 (D)
A0: OKHF.1, UBNH.4
A1: OKHF.1, UBNH.3
A2: OKHF.1, UBNH.2
A3: UBNH.2, UBNH.3
D0: ECGO.2 (D)
D1: ECGN.2 (D)
D2: ECEK.2 (D)
D3: ECCU.2 (D)
D4: EBYP.2 (D)
D5: EBXE.2 (D)
D6: EBVQ.2 (D)
D7: EBSG.2 (D)
EMIZ_IN0: DMOC.1, DMPK.3
unnamed: CMCO.1, FMCD.6 (Q)
unnamed: CMCO.2, IMDD.7
unnamed: CMCO.3, CMER.1
unnamed: CMER.2, CMEU.3, CMKK.1
unnamed: CMER.3, CMTB.1
unnamed: CMEU.1, FMFF.6 (Q)
unnamed: CMEU.2, IMDD.9
unnamed: CMKK.2, CMOY.1
unnamed: CMOY.2, DMHY.3, DMOC.2
unnamed: CMOY.3, CNRU.2
unnamed: CMTB.2, DMOC.3
unnamed: CNNO.1, DNBO.6
unnamed: CNNO.2, DNBY.3
unnamed: CNNO.3, CNRJ.2, CNRU.1
unnamed: DBWG.1, EBYP.6 (Q)
unnamed: DBWG.2, EBXE.6 (Q)
unnamed: DBWG.3, EBVQ.6 (Q)
unnamed: DBWG.4, EBSG.6 (Q)
unnamed: DBWG.5, DCBP.2
unnamed: DBZJ.1, ECGO.6 (Q)
unnamed: DBZJ.2, ECGN.6 (Q)
unnamed: DBZJ.3, ECEK.6 (Q)
unnamed: DBZJ.4, ECCU.6 (Q)
unnamed: DBZJ.5, DCBP.1
unnamed: DCBP.3, OBEE.1
unnamed: DMA24.1, UBNH.6
unnamed: DMHY.1, FMGC.6 (Q)
unnamed: DMHY.2, IMDD.20
unnamed: DMPK.1, FMHJ.6 (Q)
unnamed: DMPK.2, IMDD.22
unnamed: EBSG.1 (~RESET), EBSG.5 (~RESET), GMEX.3
unnamed: EBVQ.1 (~RESET), EBVQ.5 (~RESET), GMNY.3
unnamed: EBXE.1 (~RESET), EBXE.5 (~RESET), GMSH.3
unnamed: EBYP.1 (~RESET), EBYP.5 (~RESET), GMVF.3
unnamed: ECCU.1 (~RESET), ECCU.5 (~RESET), GNBN.3
unnamed: ECEK.1 (~RESET), ECEK.5 (~RESET), GNCF.3
unnamed: ECGN.1 (~RESET), ECGN.5 (~RESET), GNKJ.3
unnamed: ECGO.1 (~RESET), ECGO.5 (~RESET), GNQI.3
unnamed: EMIZ., GMNG.2, GMOP.2, GMUF.2, GMYD.2, GNBU.2, GNIX.2, GNPC.2, GNSN.2
unnamed: FMCD.1 (~RESET), FMCD.5 (~RESET), FMFF.1 (~RESET), FMFF.5 (~RESET), FMGC.1 (~RESET), FMGC.5 (~RESET), FMHJ.1 (~RESET), FMHJ.5 (~RESET), FMHZ.1 (~RESET), FMHZ.5 (~RESET), FMKL.1 (~RESET), FMKL.5 (~RESET), FMUY.1 (~RESET), FMUY.5 (~RESET), FMWM.1 (~RESET), FMWM.5 (~RESET)
unnamed: FMCD.3 (CLK), FMCD.4 (~CLK), GMIV.2
unnamed: FMFF.3 (CLK), FMFF.4 (~CLK), GMOL.2
unnamed: FMGC.3 (CLK), FMGC.4 (~CLK), GMTW.2
unnamed: FMHJ.3 (CLK), FMHJ.4 (~CLK), GMXT.2
unnamed: FMHZ.3 (CLK), FMHZ.4 (~CLK), GNBQ.2
unnamed: FMKL.3 (CLK), FMKL.4 (~CLK), GNIU.2
unnamed: FMUY.3 (CLK), FMUY.4 (~CLK), GNOJ.2
unnamed: FMWM.3 (CLK), FMWM.4 (~CLK), GNSB.2
unnamed: GMEX.1, GMIV.1, GMNG.3
unnamed: GMEX.2, GMNY.2, GMSH.2, GMVF.2, GNBN.2, GNCF.2, GNKJ.2, GNQI.2
unnamed: GMNG.1, GMOP.1, GMUF.1, GMYD.1, GNBU.1, GNIX.1, GNPC.1, GNSN.1
unnamed: GMNY.1, GMOL.1, GMOP.3
unnamed: GMSH.1, GMTW.1, GMUF.3
unnamed: GMVF.1, GMXT.1, GMYD.3
unnamed: GNBN.1, GNBQ.1, GNBU.3
unnamed: GNCF.1, GNIU.1, GNIX.3
unnamed: GNKJ.1, GNOJ.1, GNPC.3
unnamed: GNQI.1, GNSB.1, GNSN.3
unnamed: IMBE1.1, KMAZ.3, KMBK.2
unnamed: IMBE.3, IMDS.3
unnamed: IMDD.4, KMBK.3
unnamed: IMDS.4, IMHO.2
unnamed: IMHO.1, IMHU.4
unnamed: IMHU.3, IMLM.3
unnamed: KMBK.1, PAWC.3 (Q)
unnamed: LMFG.3, PAWC.4 (RESET)
unnamed: OKHF.2, UBNH.1, UBNH.5
wDBJW_wHASI_RST: EBSG.1 (~RESET), EBSG.5 (~RESET), EBVQ.1 (~RESET), EBVQ.5 (~RESET), EBXE.1 (~RESET), EBXE.5 (~RESET), EBYP.1 (~RESET), EBYP.5 (~RESET), ECCU.1 (~RESET), ECCU.5 (~RESET), ECEK.1 (~RESET), ECEK.5 (~RESET), ECGN.1 (~RESET), ECGN.5 (~RESET), ECGO.1 (~RESET), ECGO.5 (~RESET)
wHMAZ: EBSG.6 (Q), IMBE.2, IMDD.5
wHMBN: EBVQ.6 (Q), IMBE.1, IMDD.13
wHMDE: EBYP.6 (Q), IMDD.25, IMDS.1
wHMDM: ECCU.6 (Q), IMHU.1, IMLI.5
wHMEG: ECEK.6 (Q), IMHU.2, IMLI.13
wHMFF: ECGN.6 (Q), IMLI.15, IMLM.2
wHMJO: ECGO.6 (Q), IMLI.25, IMLM.1
wHMRC: EBXE.6 (Q), IMDD.15, IMDS.2
~420B_WR: EBSG.3 (CLK), EBSG.4 (~CLK), EBVQ.3 (CLK), EBVQ.4 (~CLK), EBXE.3 (CLK), EBXE.4 (~CLK), EBYP.3 (CLK), EBYP.4 (~CLK), ECCU.3 (CLK), ECCU.4 (~CLK), ECEK.3 (CLK), ECEK.4 (~CLK), ECGN.3 (CLK), ECGN.4 (~CLK), ECGO.3 (CLK), ECGO.4 (~CLK), HMDF.3
~420B: HMDF.1, UBNH.6
~420C_WR: DMA24.3, EBSG.3 (CLK), EBSG.4 (~CLK), EBVQ.3 (CLK), EBVQ.4 (~CLK), EBXE.3 (CLK), EBXE.4 (~CLK), EBYP.3 (CLK), EBYP.4 (~CLK), ECCU.3 (CLK), ECCU.4 (~CLK), ECEK.3 (CLK), ECEK.4 (~CLK), ECGN.3 (CLK), ECGN.4 (~CLK), ECGO.3 (CLK), ECGO.4 (~CLK)
~DMA_WR: DMA24.2, HMDF.2
~NO_DMA: IMHO.3

Notes on the sheet:
to DMA
from DMA
