rgalland/SNES_S-CPU_Schematics/S-CPU_kicad/dmastartstop.kicad_sch

## KiCad design S-CPU_kicad/dmastartstop.kicad_sch (2024-12-24, an earlier design)

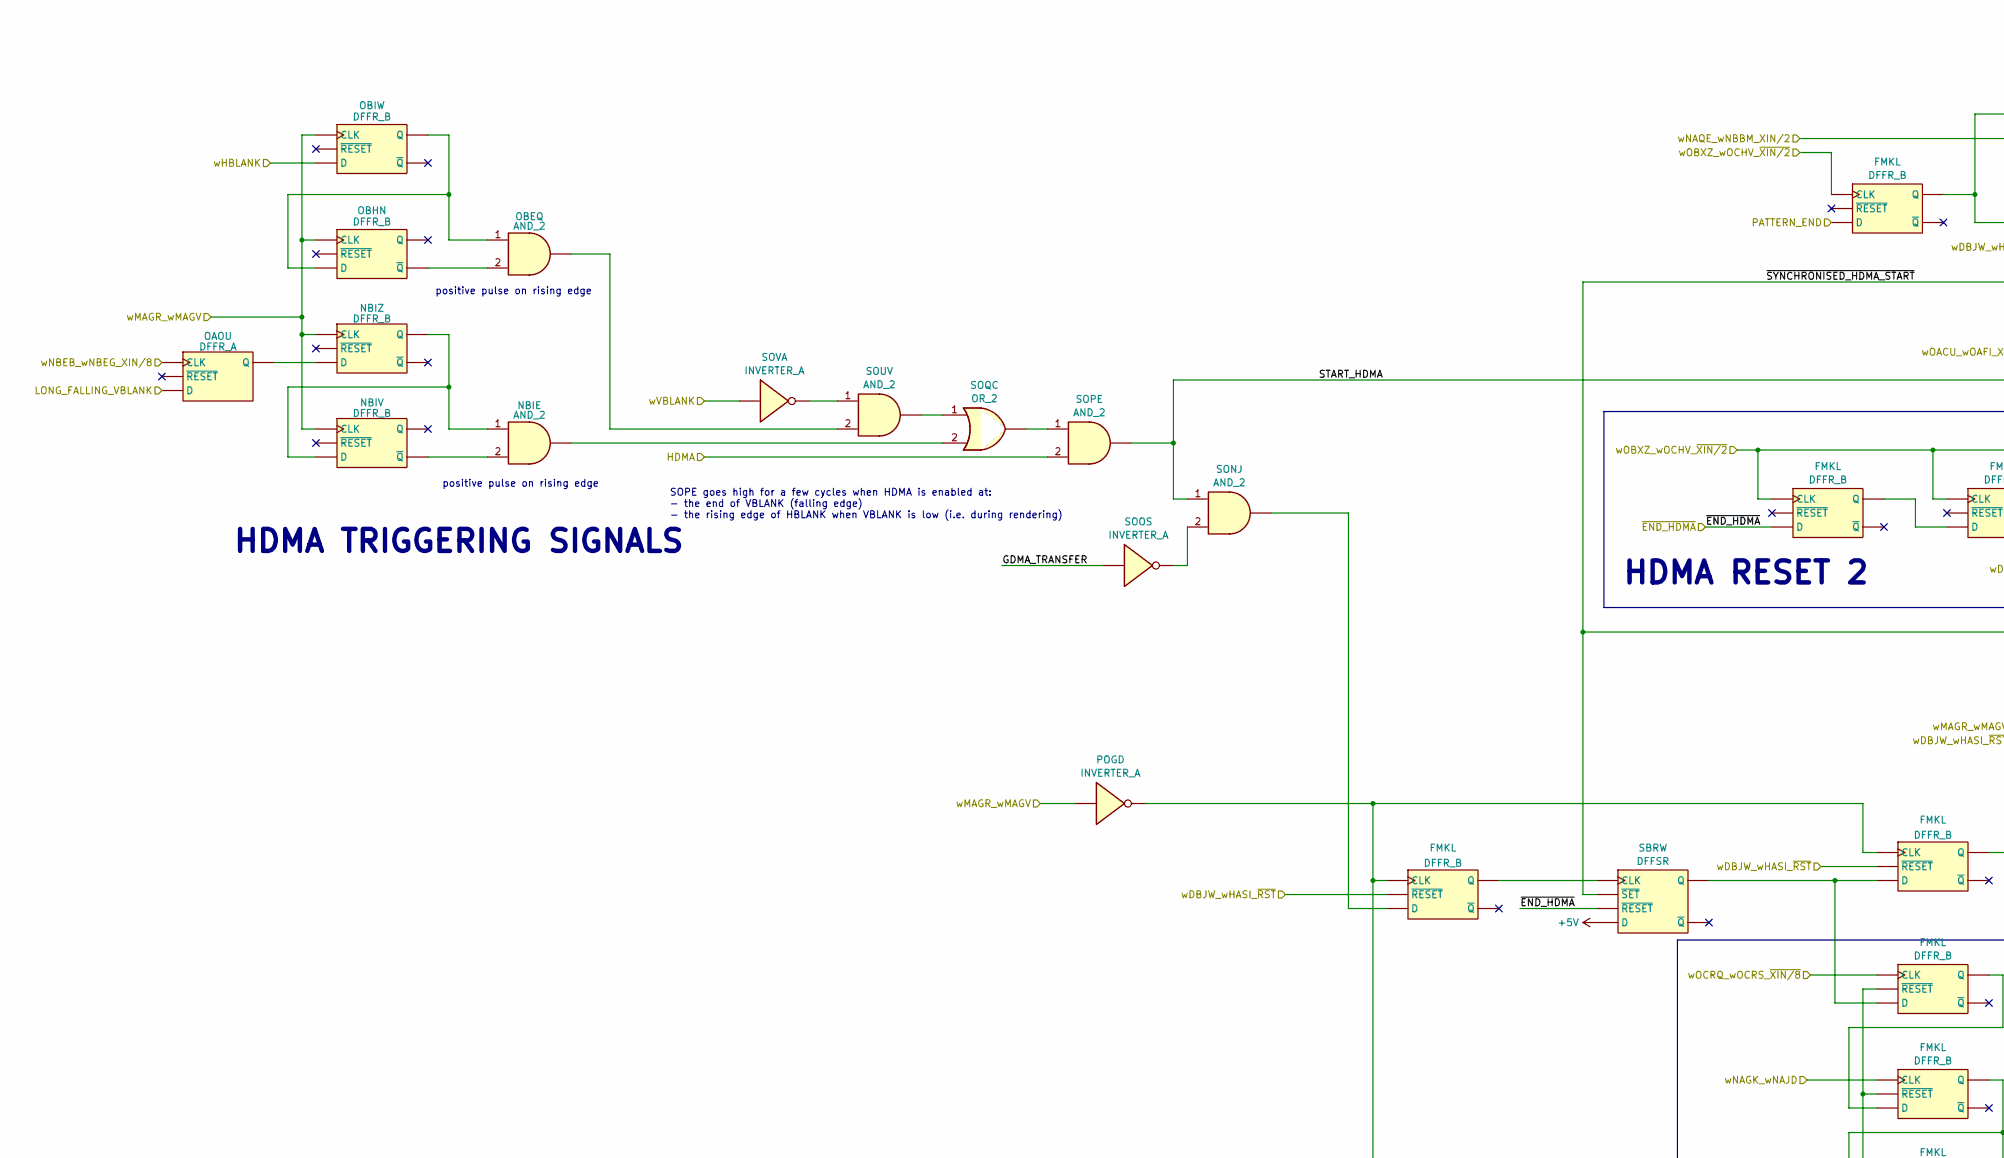
[picture p78: schematic dmastartstop.kicad_sch, part in row 1, column 1]

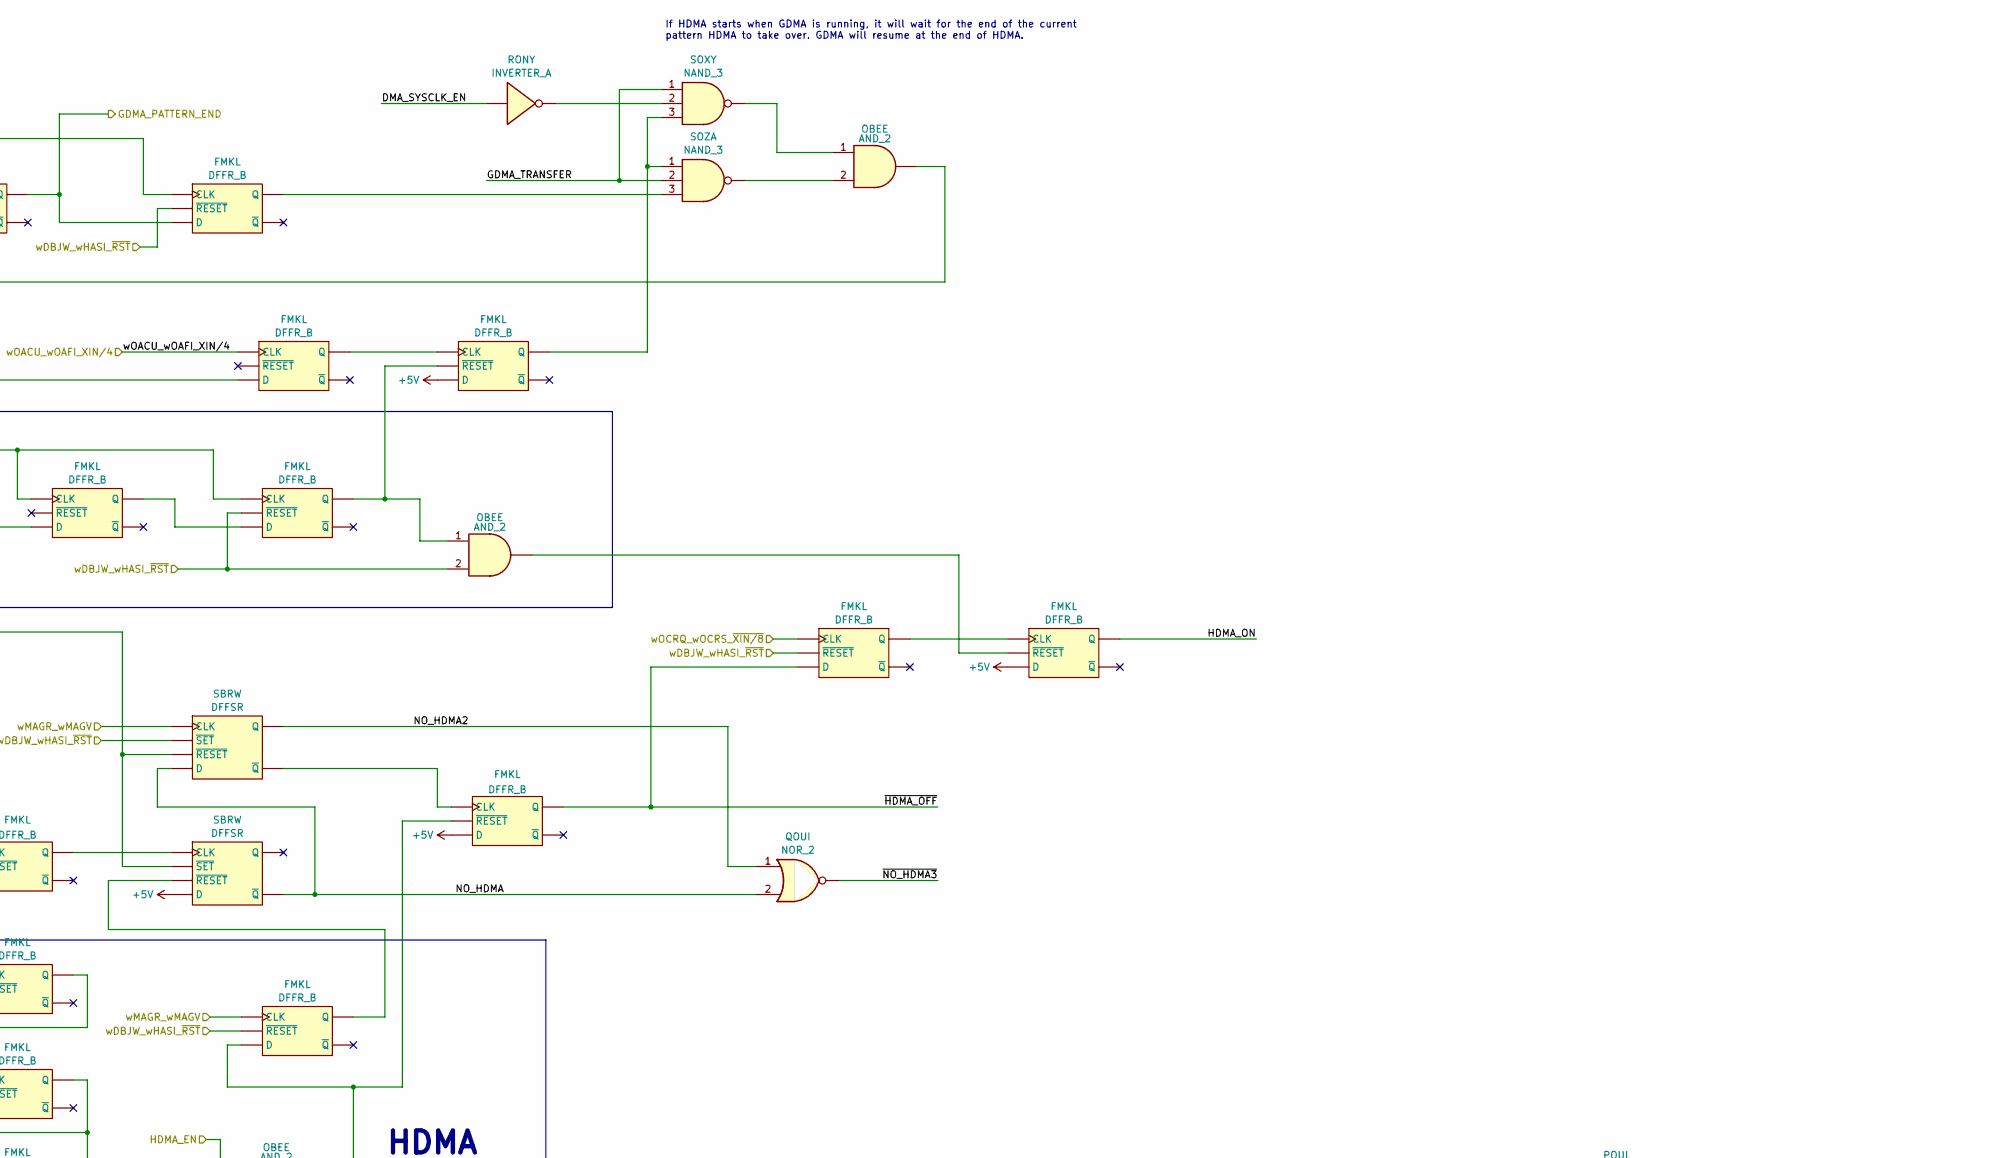
[picture p79: schematic dmastartstop.kicad_sch, part in row 1, column 2]

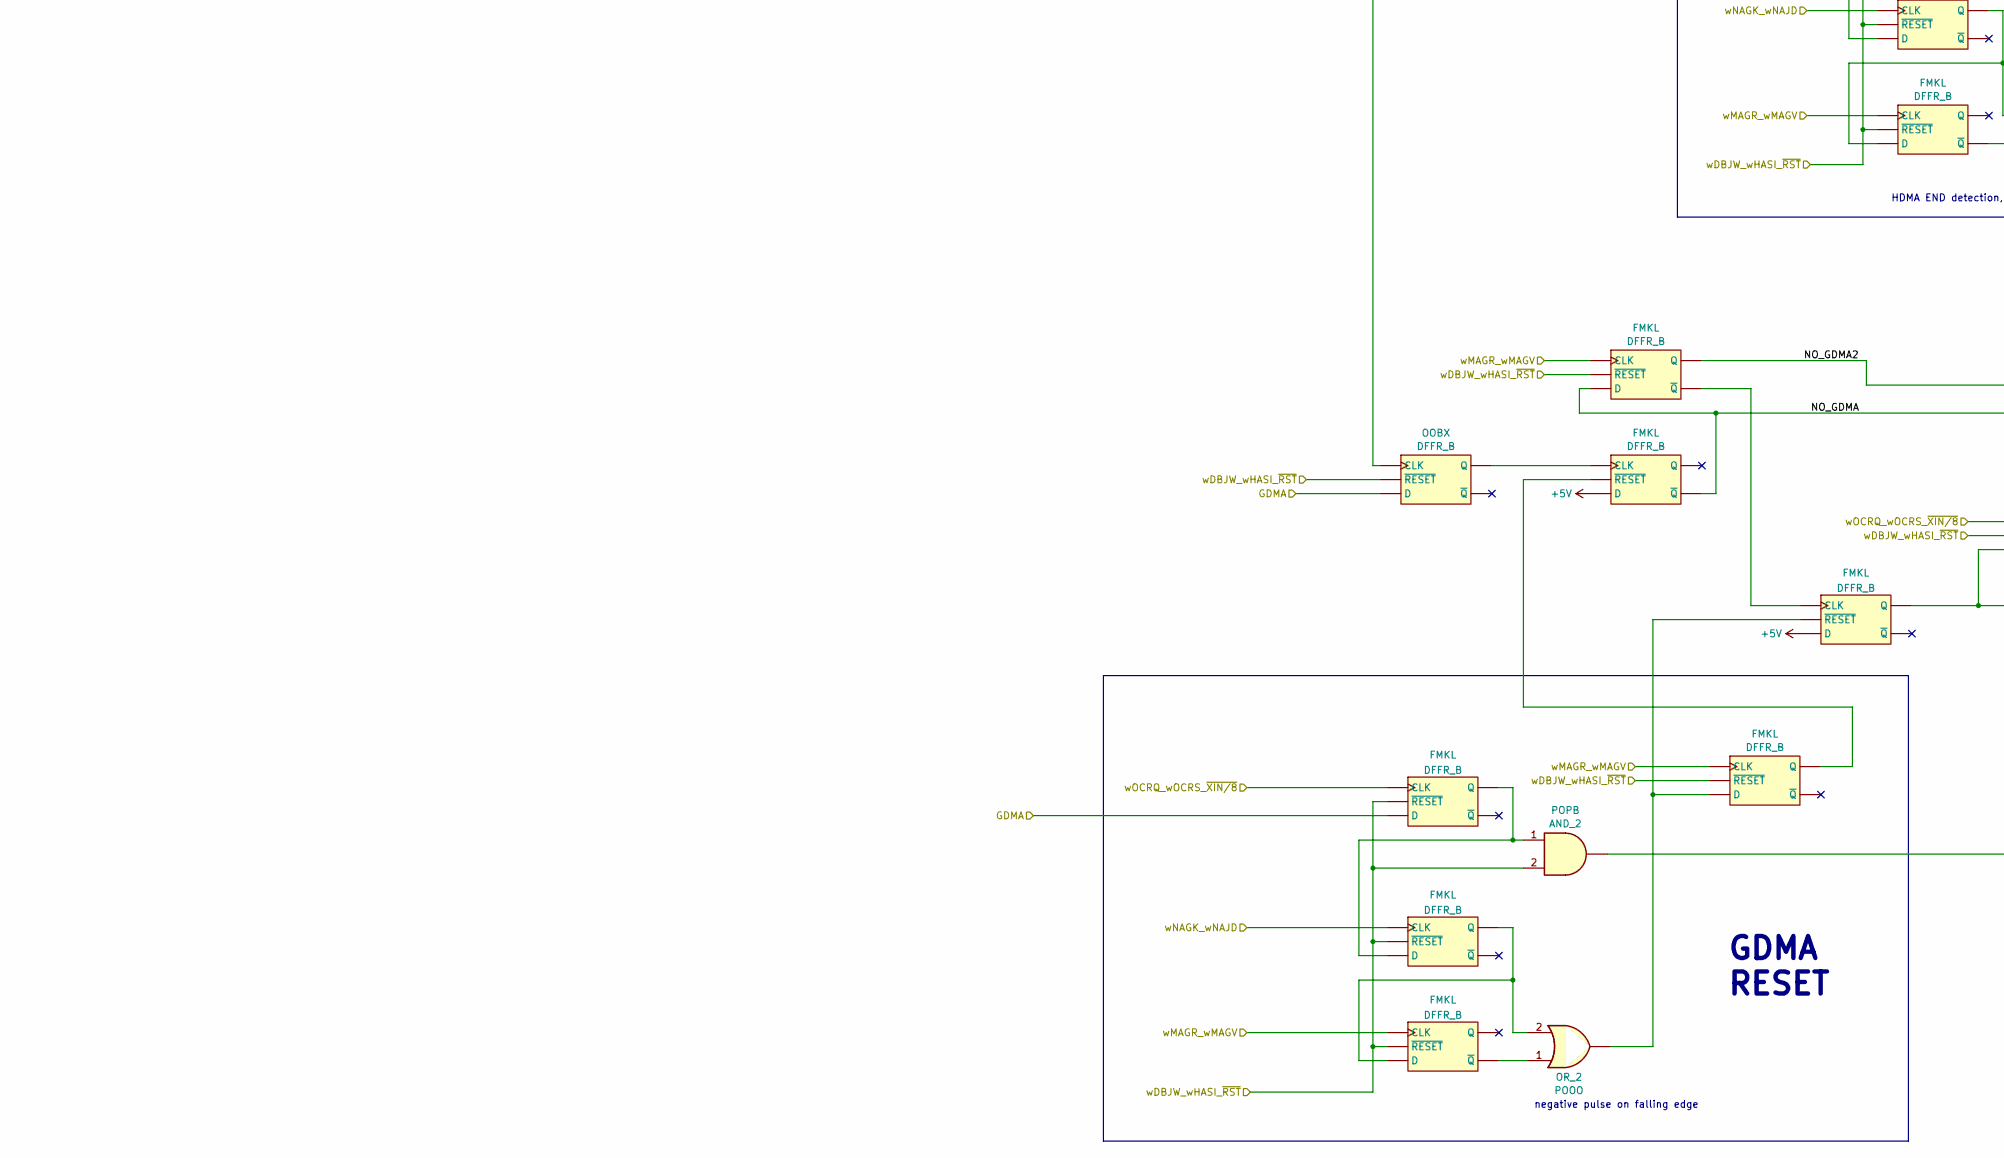
[picture p80: schematic dmastartstop.kicad_sch, part in row 2, column 1]

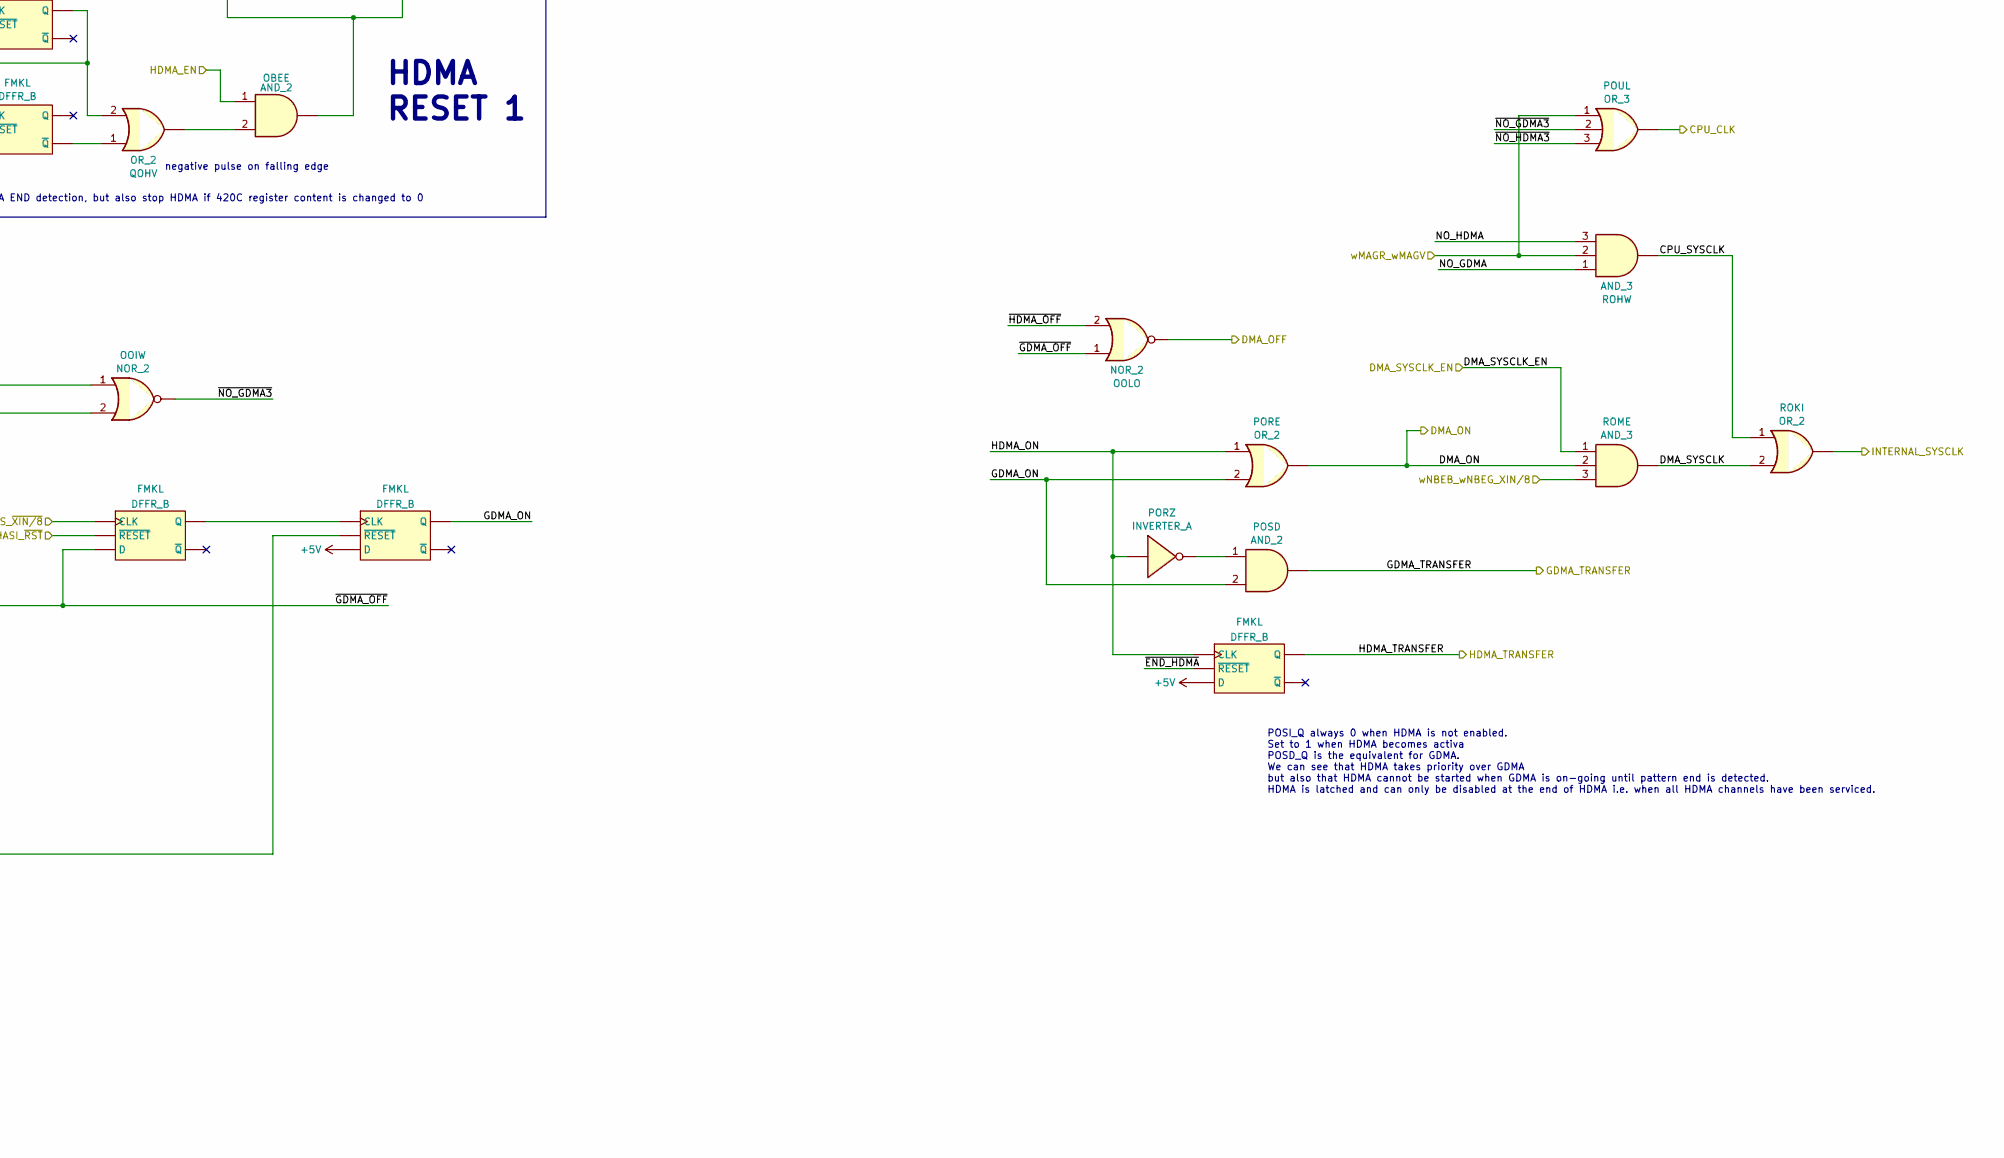
[picture p81: schematic dmastartstop.kicad_sch, part in row 2, column 2]

Parts:
FMKL: DFFR_B
NBIE: AND_2
NBIV: DFFR_B
NBIZ: DFFR_B
OAOU: DFFR_A
OBEE: AND_2
OBEQ: AND_2
OBHN: DFFR_B
OBIW: DFFR_B
OOBX: DFFR_B
OOIW: NOR_2
OOLO: NOR_2
POGD: INVERTER_A
POOO: OR_2
POPB: AND_2
PORE: OR_2
PORZ: INVERTER_A
POSD: AND_2
POUL: OR_3
QOHV: OR_2
QOUI: NOR_2
ROHW: AND_3
ROKI: OR_2
ROME: AND_3
RONY: INVERTER_A
SBRW: DFFSR
SONJ: AND_2
SOOS: INVERTER_A
SOPE: AND_2
SOQC: OR_2
SOUV: AND_2
SOVA: INVERTER_A
SOXY: NAND_3
SOZA: NAND_3

Connections:
+5V: FMKL.2 (D), SBRW.2 (D)
CPU_CLK: POUL.4
CPU_SYSCLK: ROHW.4, ROKI.1
DMA_OFF: OOLO.3
DMA_ON: PORE.3, ROME.2
DMA_SYSCLK: ROKI.2, ROME.4
DMA_SYSCLK_EN: ROME.1, RONY.1
GDMA: FMKL.2 (D), OOBX.2 (D)
GDMA_ON: FMKL.7 (Q), PORE.2, POSD.2
GDMA_PATTERN_END: FMKL.2 (D), FMKL.7 (Q)
GDMA_TRANSFER: POSD.3, SOOS.1, SOXY.1, SOZA.2
HDMA: SOPE.2
HDMA_EN: OBEE.1
HDMA_ON: FMKL.3 (CLK), FMKL.4 (~CLK), FMKL.7 (Q), PORE.1, PORZ.1
HDMA_TRANSFER: FMKL.7 (Q)
INTERNAL_SYSCLK: ROKI.3
LONG_FALLING_VBLANK: OAOU.2 (D)
NO_GDMA: FMKL.2 (D), FMKL.6 (~Q), OOIW.2, ROHW.1
NO_GDMA2: FMKL.7 (Q), OOIW.1
NO_HDMA: QOUI.2, ROHW.3, SBRW.2 (D), SBRW.4 (~Q)
NO_HDMA2: QOUI.1, SBRW.5 (Q)
unnamed: FMKL.1 (~RESET), FMKL.2 (D), FMKL.5 (~RESET), FMKL.7 (Q), OBEE.1, OBEE.3, POOO.3, POPB.3
unnamed: FMKL.2 (D), FMKL.7 (Q), POOO.2, POPB.1, QOHV.2, SBRW.5 (Q), SONJ.3
unnamed: FMKL.3 (CLK), FMKL.4 (~CLK), FMKL.6 (~Q), FMKL.7 (Q), OOBX.3 (CLK), OOBX.4 (~CLK), OOBX.7 (Q), POGD.2, SBRW.4 (~Q)
unnamed: FMKL.6 (~Q), POOO.1, QOHV.1
unnamed: FMKL.7 (Q), SBRW.6 (~RESET), SBRW.7 (CLK), SOXY.3, SOZA.1, SOZA.3
unnamed: NBIE.1, NBIV.2 (D), NBIZ.7 (Q)
unnamed: NBIE.2, NBIV.6 (~Q)
unnamed: NBIE.3, SOQC.2
unnamed: NBIV.1 (~RESET), NBIV.5 (~RESET)
unnamed: NBIZ.1 (~RESET), NBIZ.5 (~RESET)
unnamed: NBIZ.2 (D), OAOU.6 (Q)
unnamed: OAOU.1 (~RESET), OAOU.5 (~RESET)
unnamed: OBEE.1, SOXY.4
unnamed: OBEE.2, QOHV.3, SOZA.4
unnamed: OBEQ.1, OBHN.2 (D), OBIW.7 (Q)
unnamed: OBEQ.2, OBHN.6 (~Q)
unnamed: OBEQ.3, SOUV.2
unnamed: OBHN.1 (~RESET), OBHN.5 (~RESET)
unnamed: OBIW.1 (~RESET), OBIW.5 (~RESET)
unnamed: PORZ.2, POSD.1
unnamed: RONY.2, SOXY.2
unnamed: SONJ.2, SOOS.2
unnamed: SOPE.1, SOQC.3
unnamed: SOQC.1, SOUV.3
unnamed: SOUV.1, SOVA.2
PATTERN_END: FMKL.2 (D)
START_HDMA: FMKL.2 (D), SONJ.1, SOPE.3
wDBJW_wHASI_~RST: FMKL.1 (~RESET), FMKL.5 (~RESET), OBEE.2, OOBX.1 (~RESET), OOBX.5 (~RESET), POPB.2, SBRW.1 (~SET), SBRW.3 (~SET)
wHBLANK: OBIW.2 (D)
wMAGR_wMAGV: FMKL.3 (CLK), FMKL.4 (~CLK), NBIV.3 (CLK), NBIV.4 (~CLK), NBIZ.3 (CLK), NBIZ.4 (~CLK), OBHN.3 (CLK), OBHN.4 (~CLK), OBIW.3 (CLK), OBIW.4 (~CLK), POGD.1, POUL.1, ROHW.2, SBRW.7 (CLK)
wNAGK_wNAJD: FMKL.3 (CLK), FMKL.4 (~CLK)
wNAQE_wNBBM_XIN/2: FMKL.3 (CLK), FMKL.4 (~CLK)
wNBEB_wNBEG_XIN/8: OAOU.3 (CLK), OAOU.4 (~CLK), ROME.3
wOACU_wOAFI_XIN/4: FMKL.3 (CLK), FMKL.4 (~CLK)
wOBXZ_wOCHV_~XIN/2: FMKL.3 (CLK), FMKL.4 (~CLK)
wOCRQ_wOCRS_~XIN/8: FMKL.3 (CLK), FMKL.4 (~CLK)
wVBLANK: SOVA.1
~END_HDMA: FMKL.1 (~RESET), FMKL.2 (D), FMKL.5 (~RESET), SBRW.6 (~RESET)
~GDMA_OFF: FMKL.2 (D), FMKL.7 (Q), OOLO.1
~HDMA_OFF: FMKL.2 (D), FMKL.7 (Q), OOLO.2
~NO_GDMA3: OOIW.3, POUL.2
~NO_HDMA3: POUL.3, QOUI.3
~SYNCHRONISED_HDMA_START: OBEE.3, SBRW.1 (~SET), SBRW.3 (~SET), SBRW.6 (~RESET)

Notes on the sheet:
If HDMA starts when GDMA is running, it will wait for the end of the current pattern HDMA to take over. GDMA will resume at the end of HDMA.
HDMA TRIGGERING SIGNALS
SOPE goes high for a few cycles when HDMA is enabled at: - the end of VBLANK (falling edge) - the rising edge of HBLANK when VBLANK is low (i.e. during rendering)
HDMA END detection, but also stop HDMA if 420C register content is changed to 0
HDMA RESET 2
negative pulse on falling edge
POSI_Q always 0 when HDMA is not enabled. Set to 1 when HDMA becomes activa POSD_Q is the equivalent for GDMA. We can see that HDMA takes priority over GDMA but also that HDMA cannot be started when GDMA is on-going until pattern end is detected. HDMA is latched and can only be disabled at the end 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
HDMA RESET 1
positive pulse on rising edge
GDMA RESET
