rgalland/SNES_S-CPU_Schematics/S-CPU_kicad/fastromreg.kicad_sch

## KiCad design S-CPU_kicad/fastromreg.kicad_sch (2024-12-24, an earlier design)

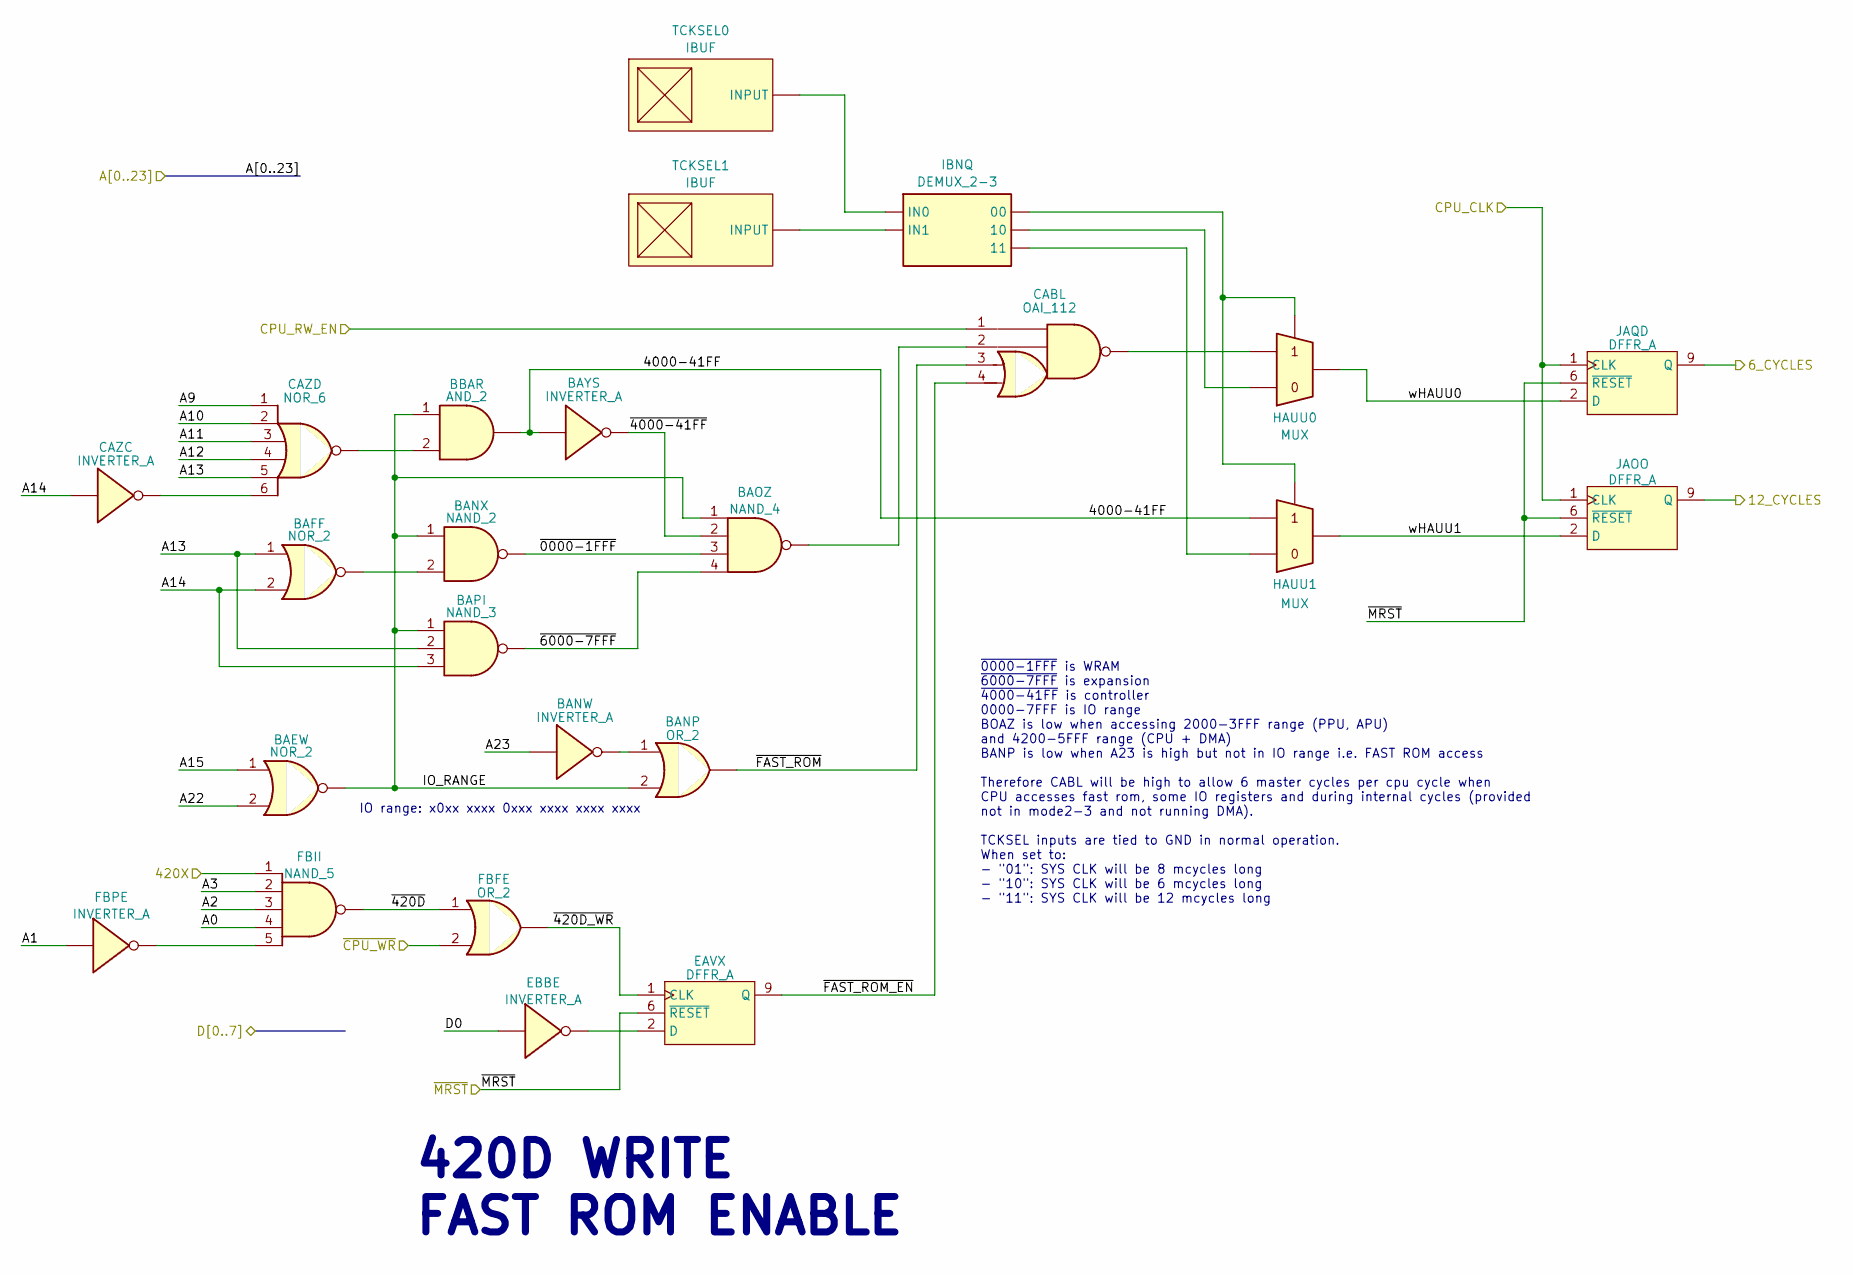
[picture p82: schematic fastromreg.kicad_sch]

Parts:
BAEW: NOR_2
BAFF: NOR_2
BANP: OR_2
BANW: INVERTER_A
BANX: NAND_2
BAOZ: NAND_4
BAPI: NAND_3
BAYS: INVERTER_A
BBAR: AND_2
CABL: OAI_112
CAZC: INVERTER_A
CAZD: NOR_6
EAVX: DFFR_A
EBBE: INVERTER_A
FBFE: OR_2
FBII: NAND_5
FBPE: INVERTER_A
HAUU0, HAUU1: MUX
IBNQ: DEMUX_2-3
JAOO: DFFR_A
JAQD: DFFR_A
TCKSEL0, TCKSEL1: IBUF

Connections:
6_CYCLES: JAQD.9 (Q)
12_CYCLES: JAOO.9 (Q)
420X: FBII.1
4000-41FF: BAYS.1, BBAR.3, HAUU1.2
A0: FBII.4
A1: FBPE.1
A2: FBII.3
A3: FBII.2
A9: CAZD.1
A10: CAZD.2
A11: CAZD.3
A12: CAZD.4
A13: BAFF.1, BAPI.2, CAZD.5
A14: BAFF.2, BAPI.3, CAZC.1
A15: BAEW.1
A22: BAEW.2
A23: BANW.1
CPU_CLK: JAOO.1 (CLK), JAQD.1 (CLK)
CPU_RW_EN: CABL.1
D0: EBBE.1
IO_RANGE: BAEW.3, BANP.2, BANX.1, BAOZ.1, BAPI.1, BBAR.1
unnamed: BAFF.3, BANX.2
unnamed: BANP.1, BANW.2
unnamed: BAOZ.5, CABL.2
unnamed: BBAR.2, CAZD.7
unnamed: CABL.5, HAUU0.2
unnamed: CAZC.2, CAZD.6
unnamed: EAVX.2 (D), EBBE.2
unnamed: FBII.5, FBPE.2
unnamed: HAUU0.1, HAUU1.1, IBNQ.
unnamed: HAUU0.3, IBNQ.
unnamed: HAUU1.3, IBNQ.
unnamed: IBNQ., TCKSEL0.1, TCKSEL1.1
wHAUU0: HAUU0.4, JAQD.2 (D)
wHAUU1: HAUU1.4, JAOO.2 (D)
~0000-1FFF: BANX.3, BAOZ.3
~420D_WR: EAVX.1 (CLK), FBFE.3
~420D: FBFE.1, FBII.6
~4000-41FF: BAOZ.2, BAYS.2
~6000-7FFF: BAOZ.4, BAPI.4
~CPU_WR: FBFE.2
~FAST_ROM_EN: CABL.4, EAVX.9 (Q)
~FAST_ROM: BANP.3, CABL.3
~MRST: EAVX.6 (~RESET), JAOO.6 (~RESET), JAQD.6 (~RESET)

Notes on the sheet:
420D WRITE FAST ROM ENABLE
~{0000-1FFF} is WRAM ~{6000-7FFF} is expansion ~{4000-41FF} is controller 0000-7FFF is IO range BOAZ is low when accessing 2000-3FFF range (PPU, APU) and 4200-5FFF range (CPU + DMA) BANP is low when A23 is high but not in IO range i.e. FAST ROM access Therefore CABL will be high to allow 6 master c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
IO range: x0xx xxxx 0xxx xxxx xxxx xxxx
