rgalland/SNES_S-CPU_Schematics/S-CPU_kicad/joypads.kicad_sch

## KiCad design S-CPU_kicad/joypads.kicad_sch (2024-12-24, an earlier design)

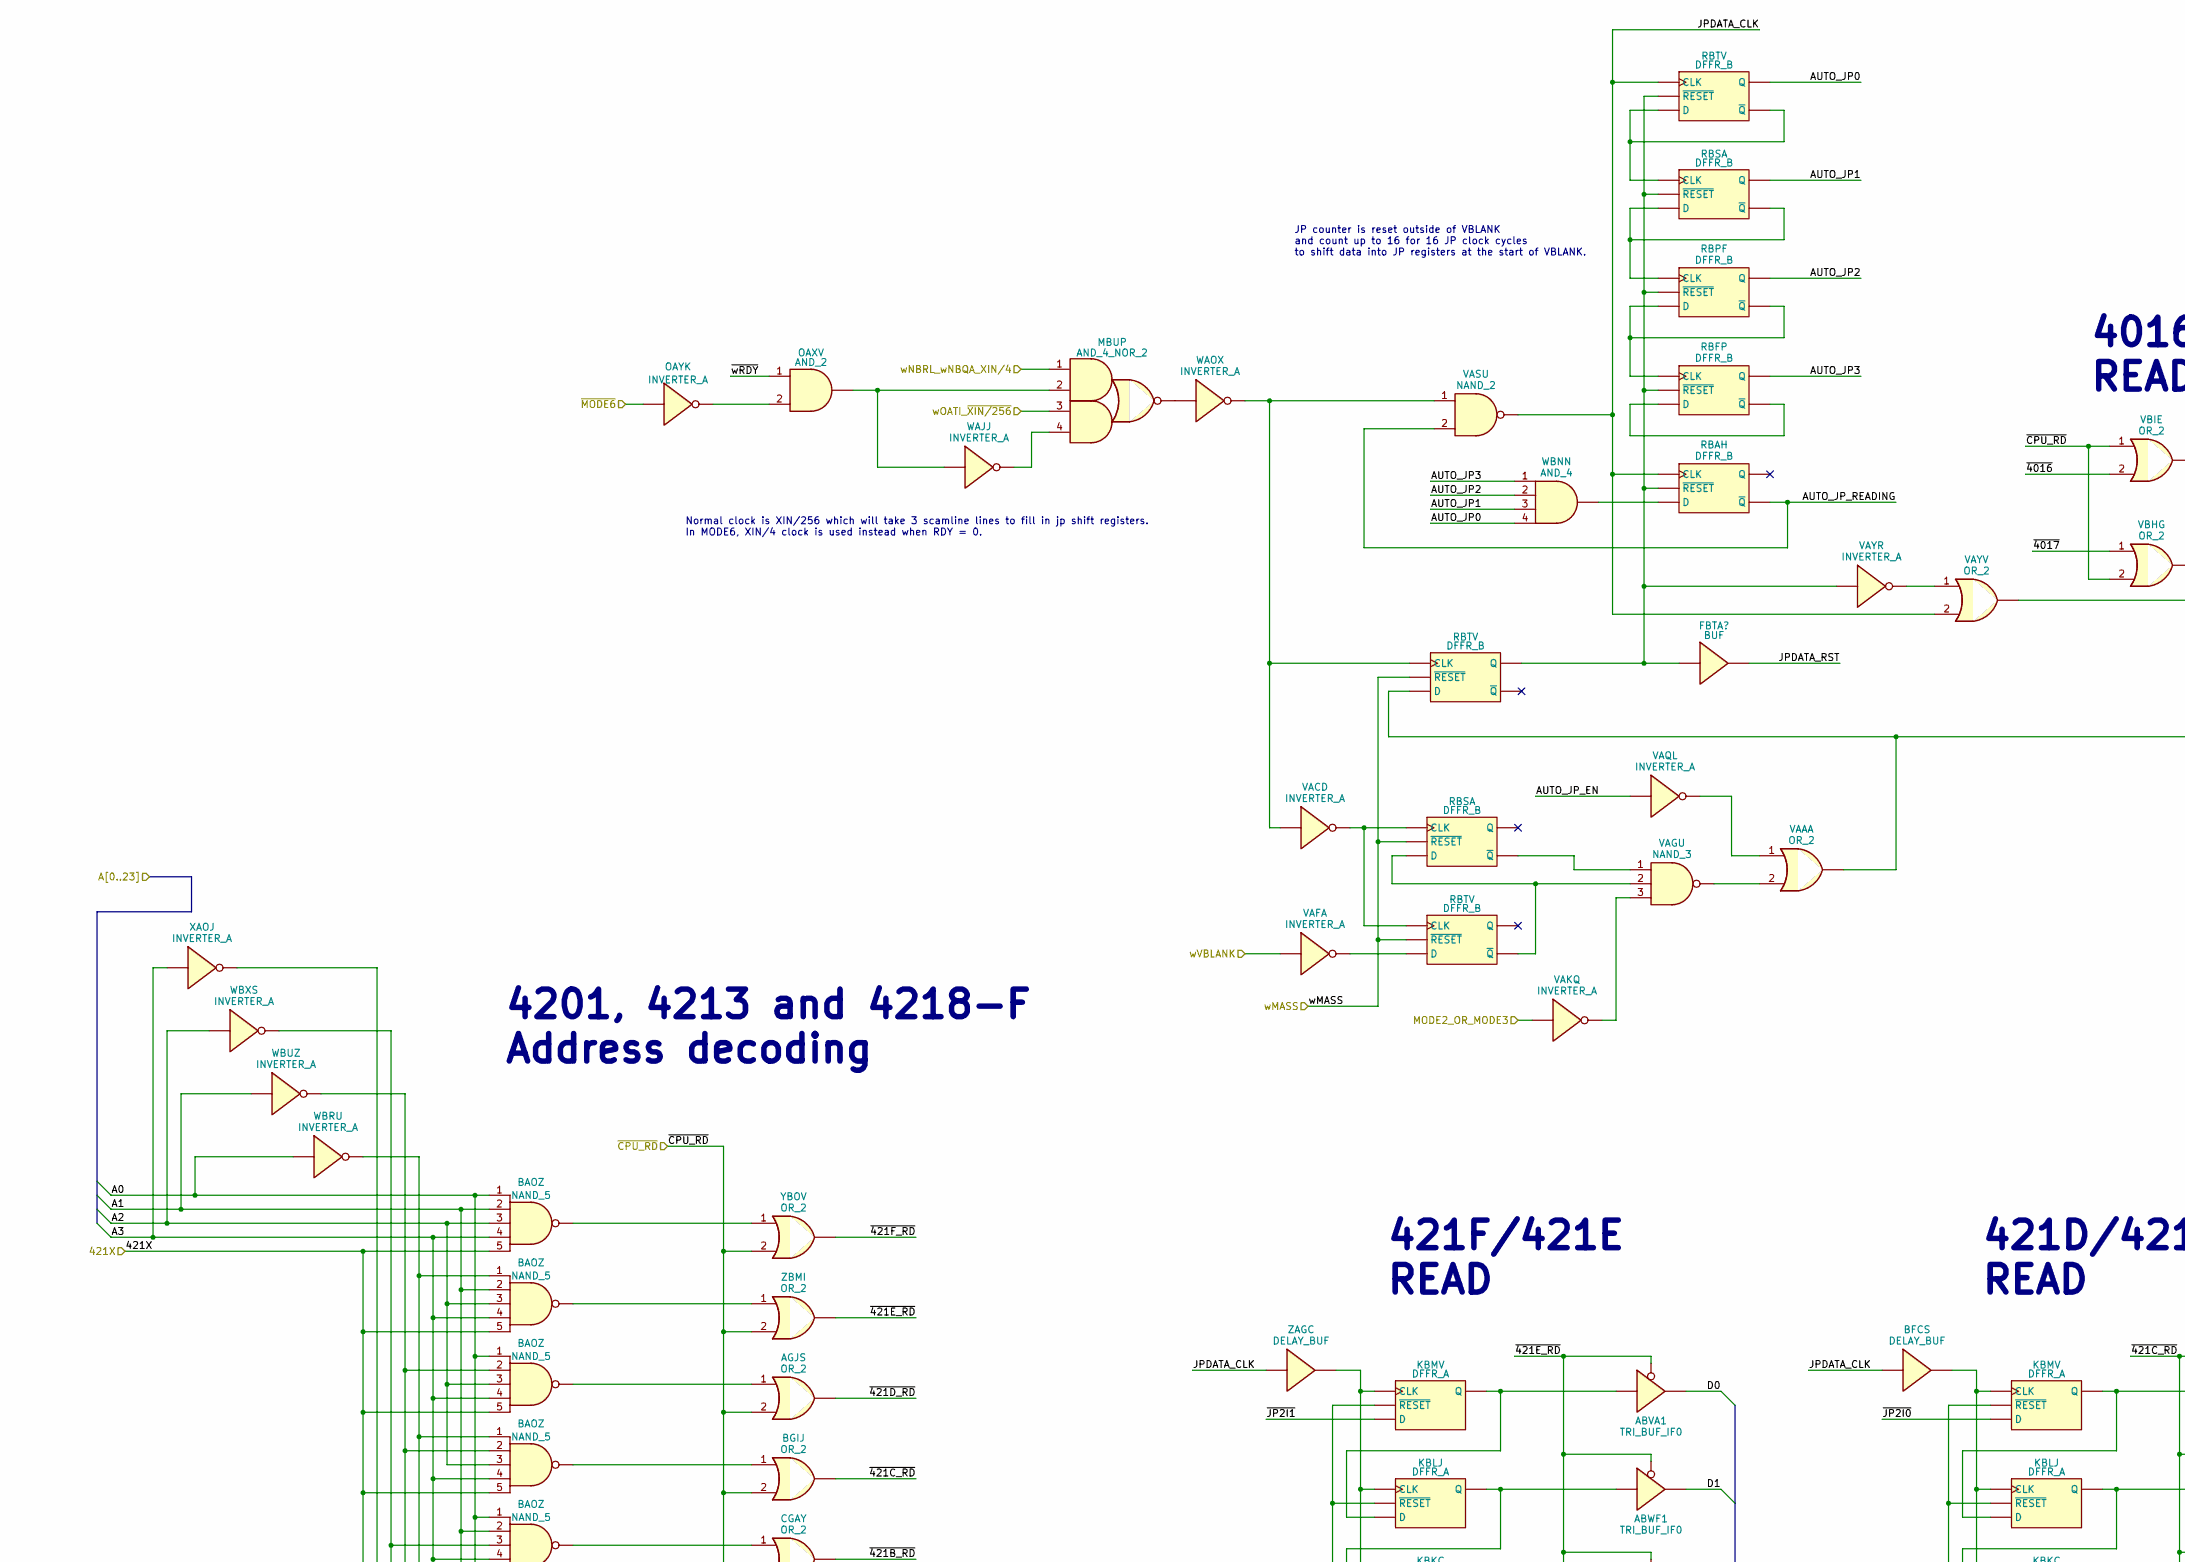
[picture p83: schematic joypads.kicad_sch, part in row 1, column 1]

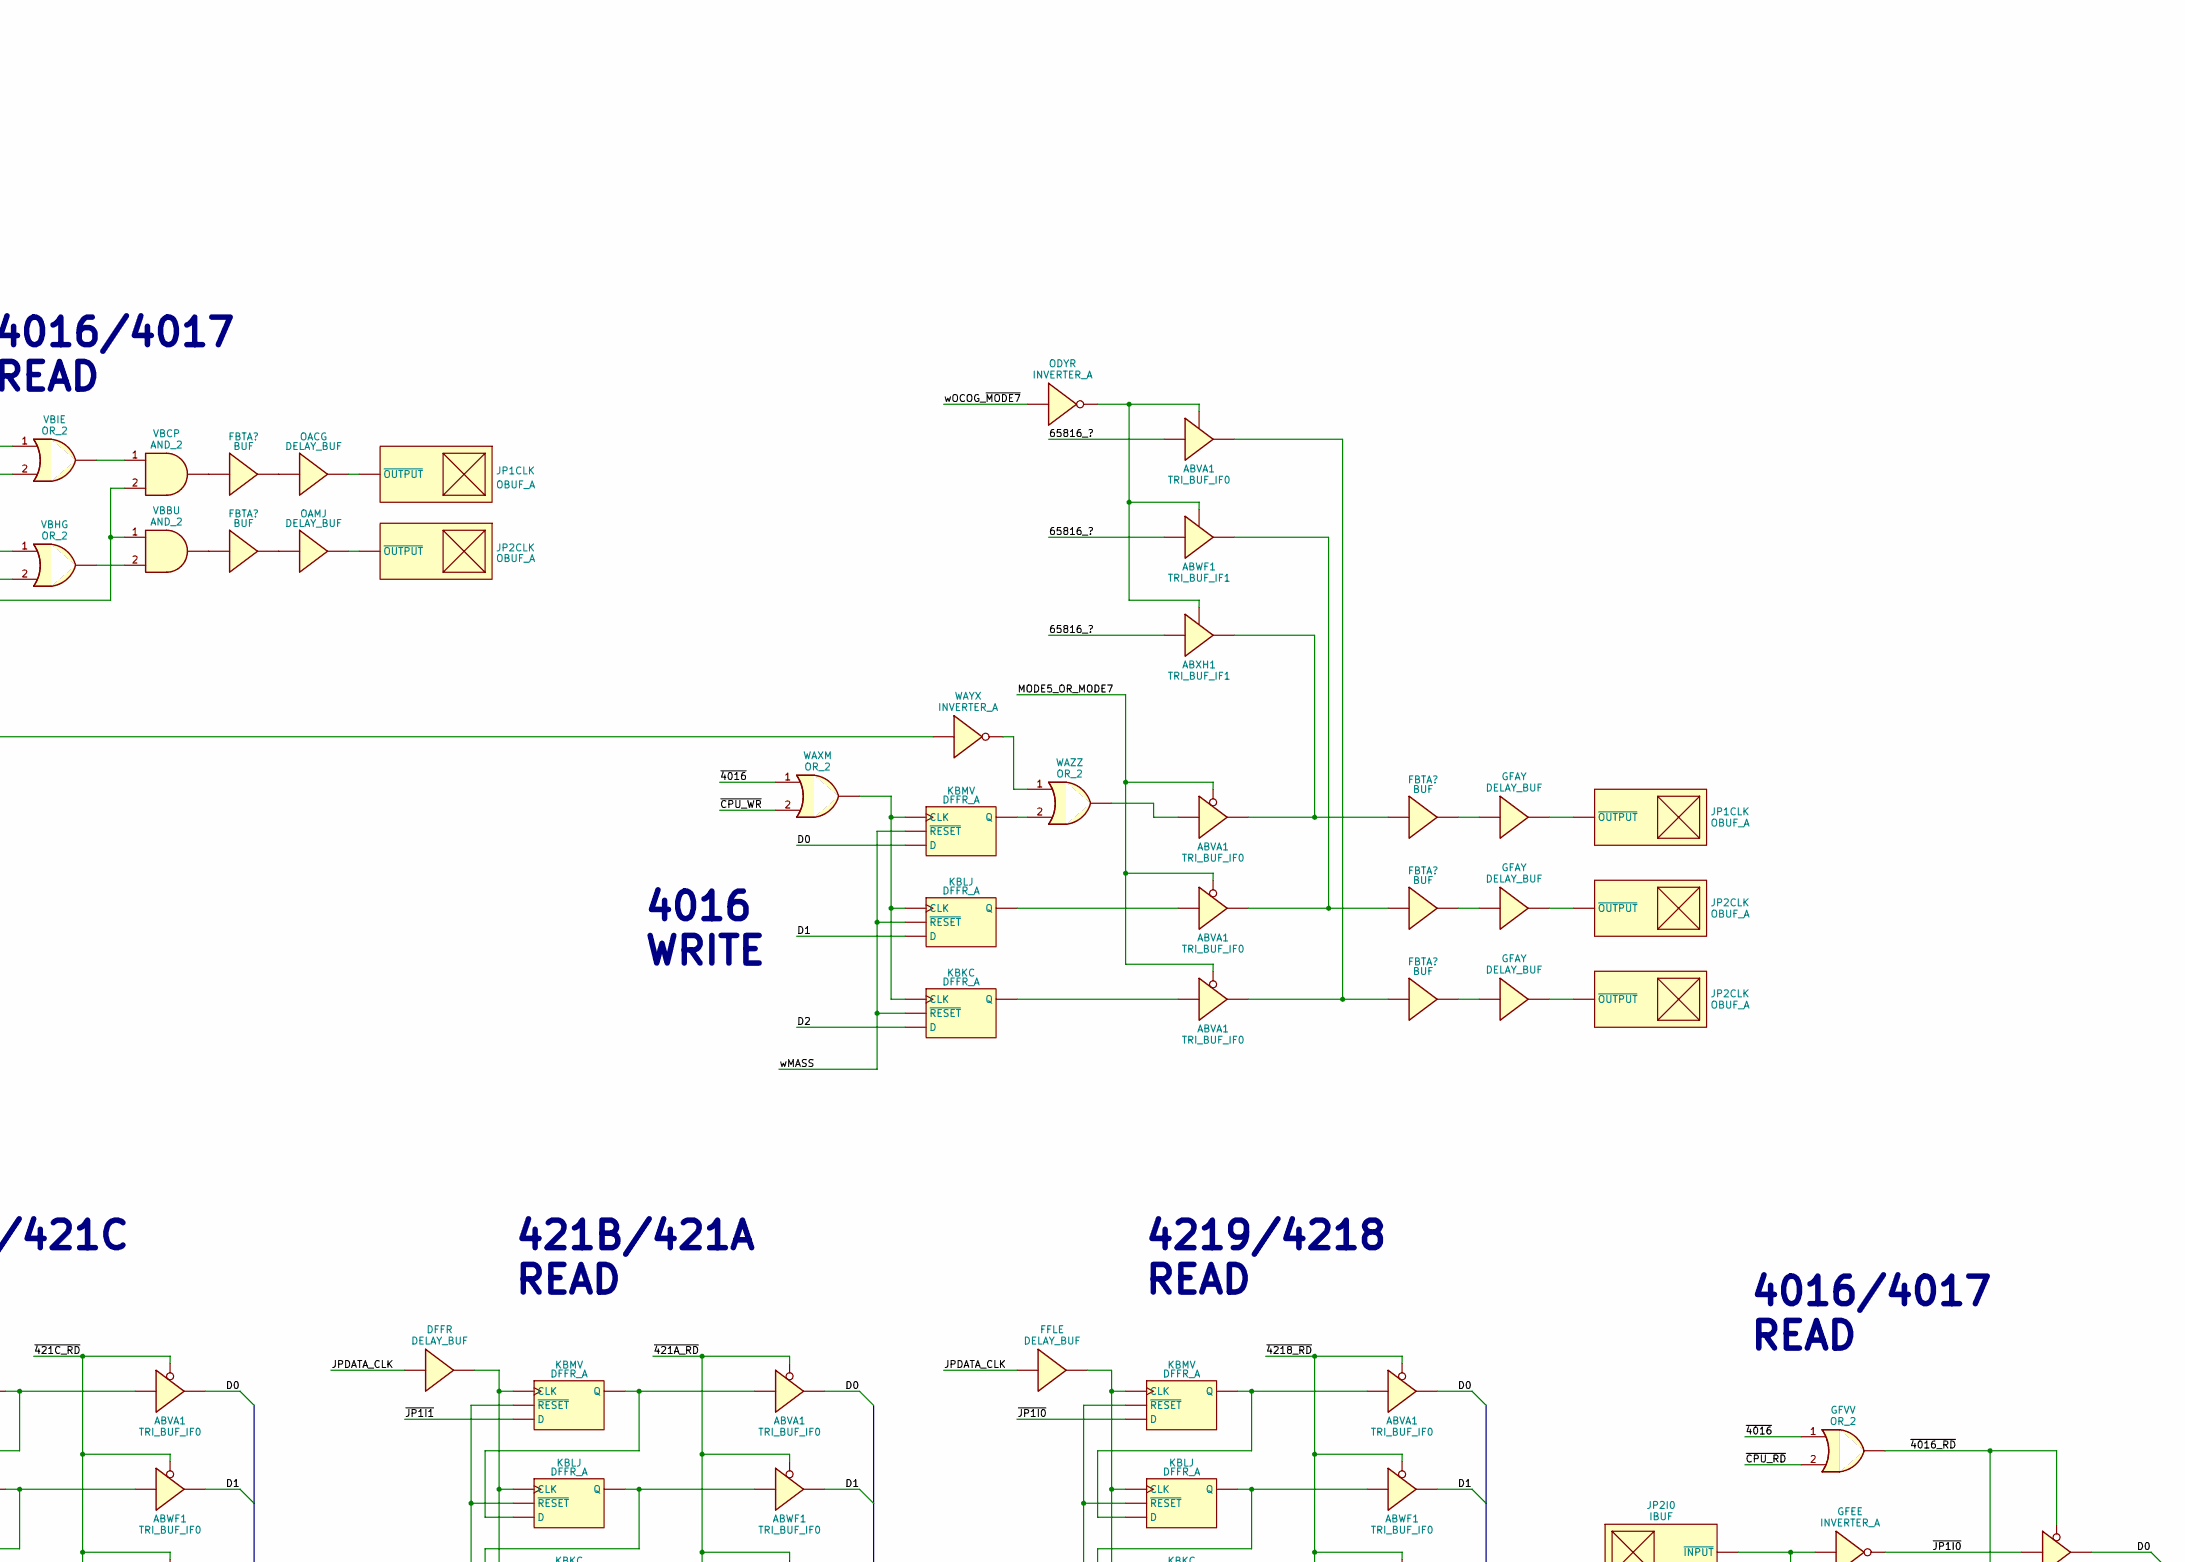
[picture p84: schematic joypads.kicad_sch, part in row 1, column 2]

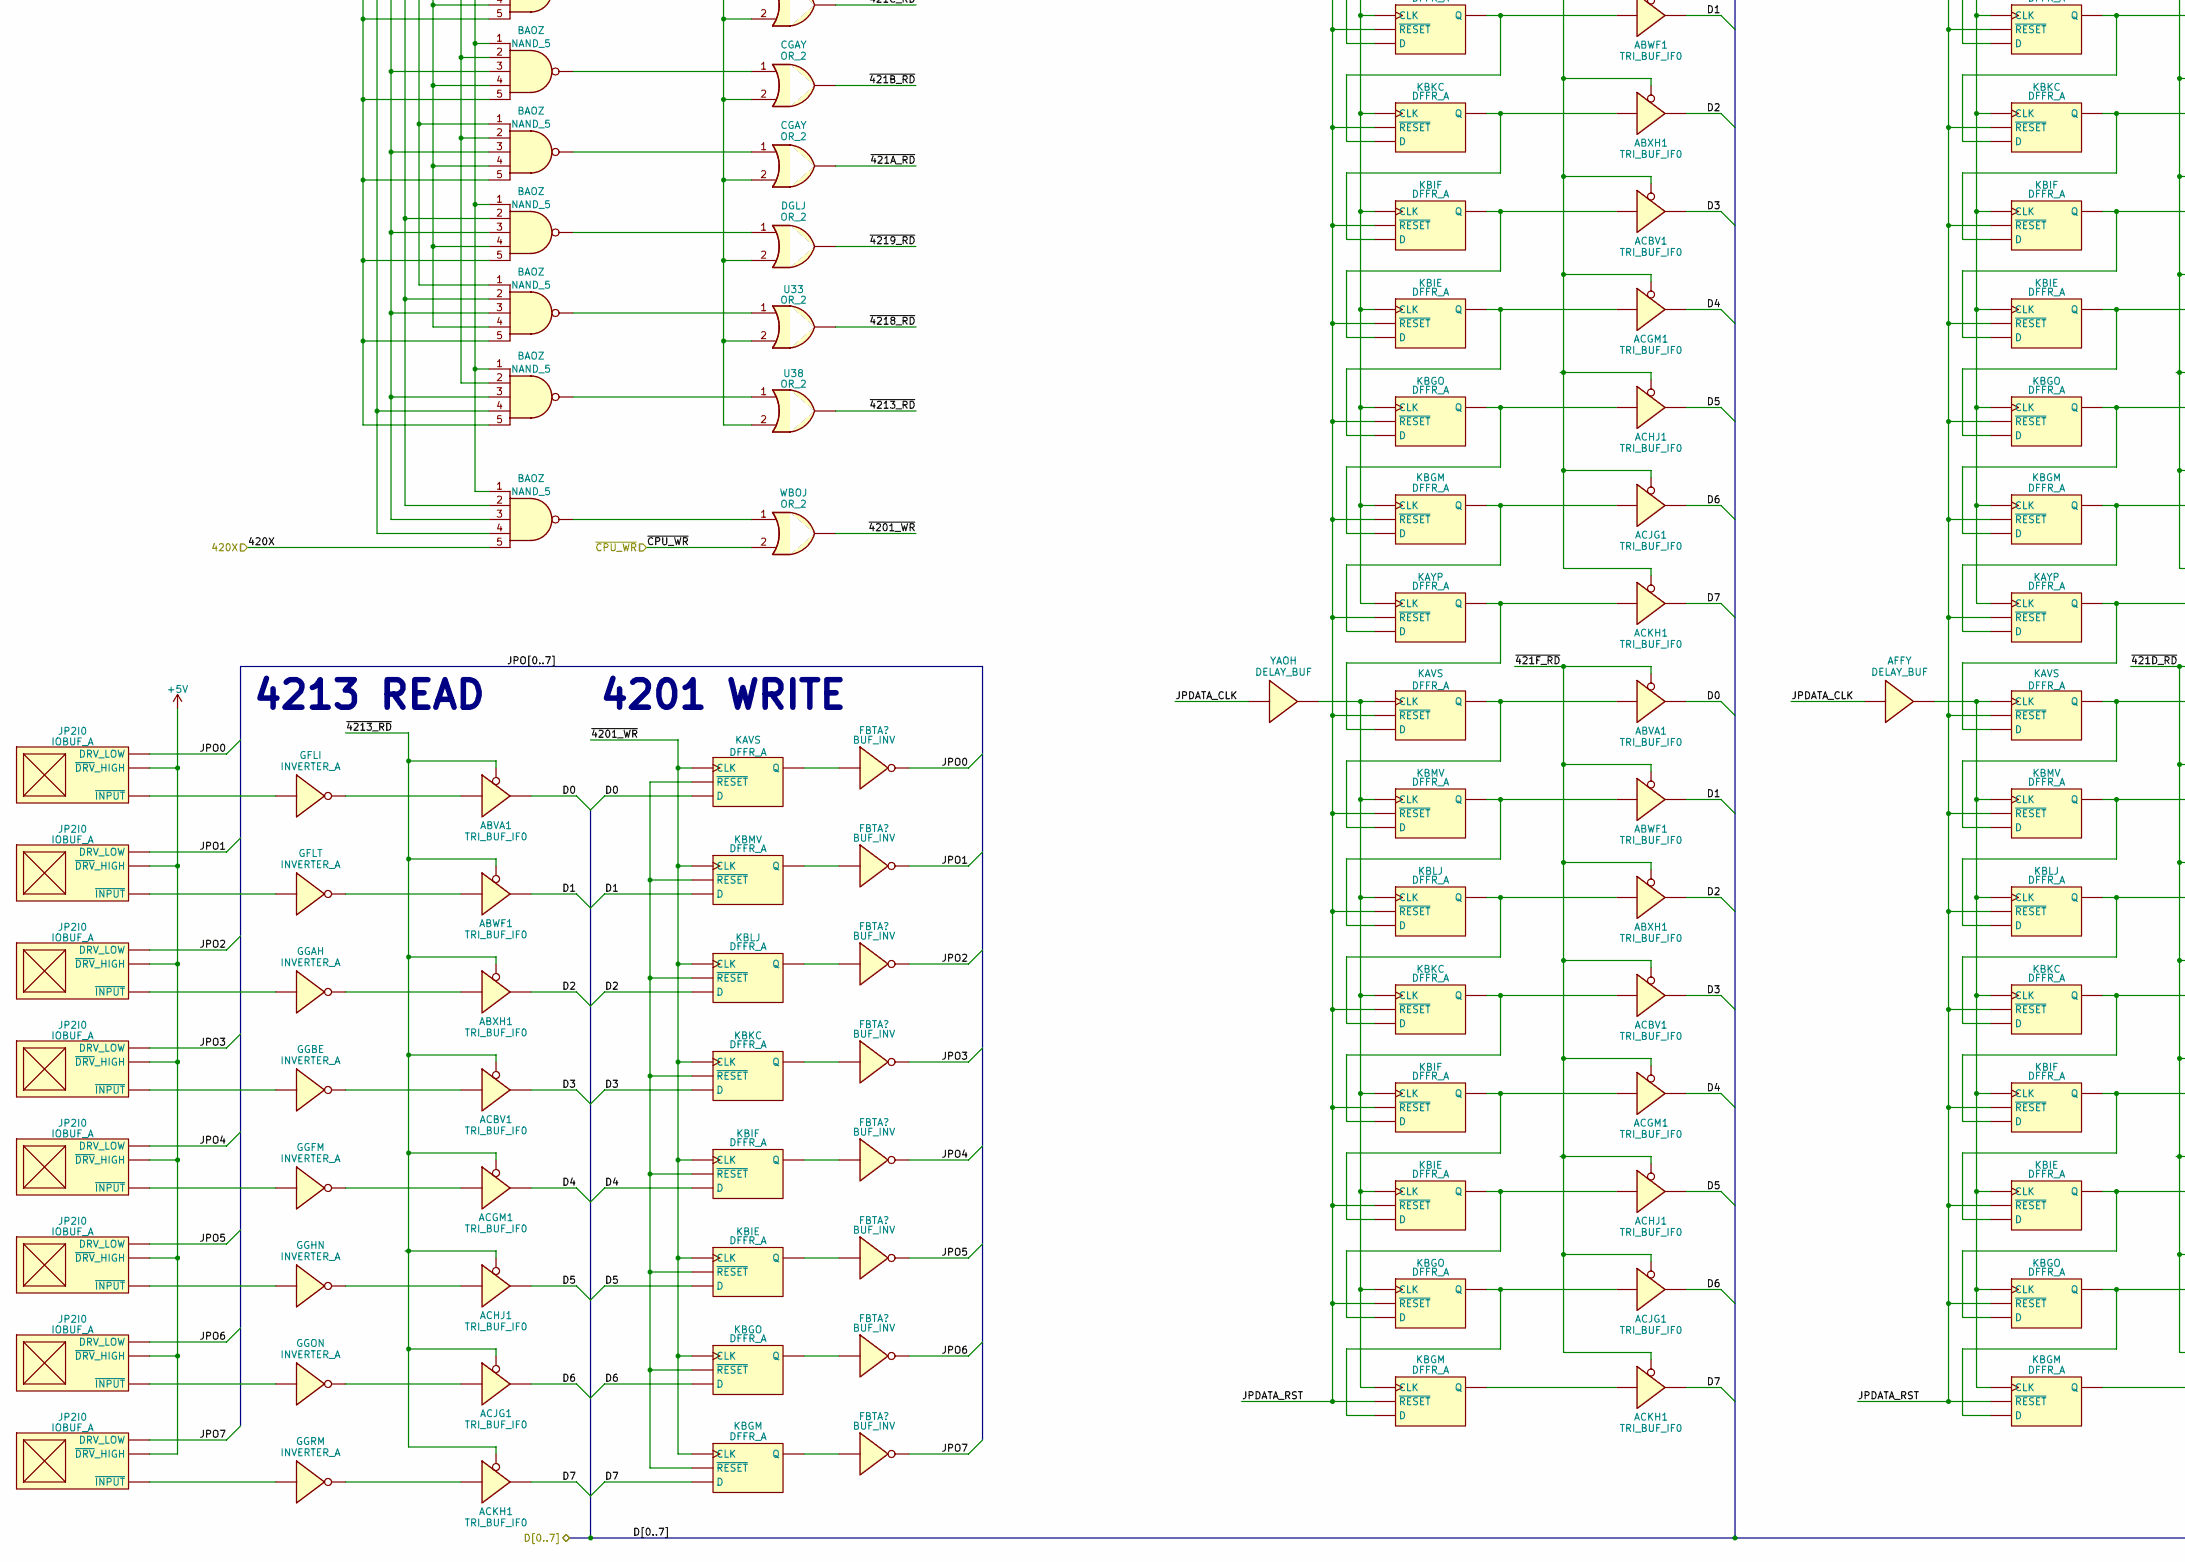
[picture p85: schematic joypads.kicad_sch, part in row 2, column 1]

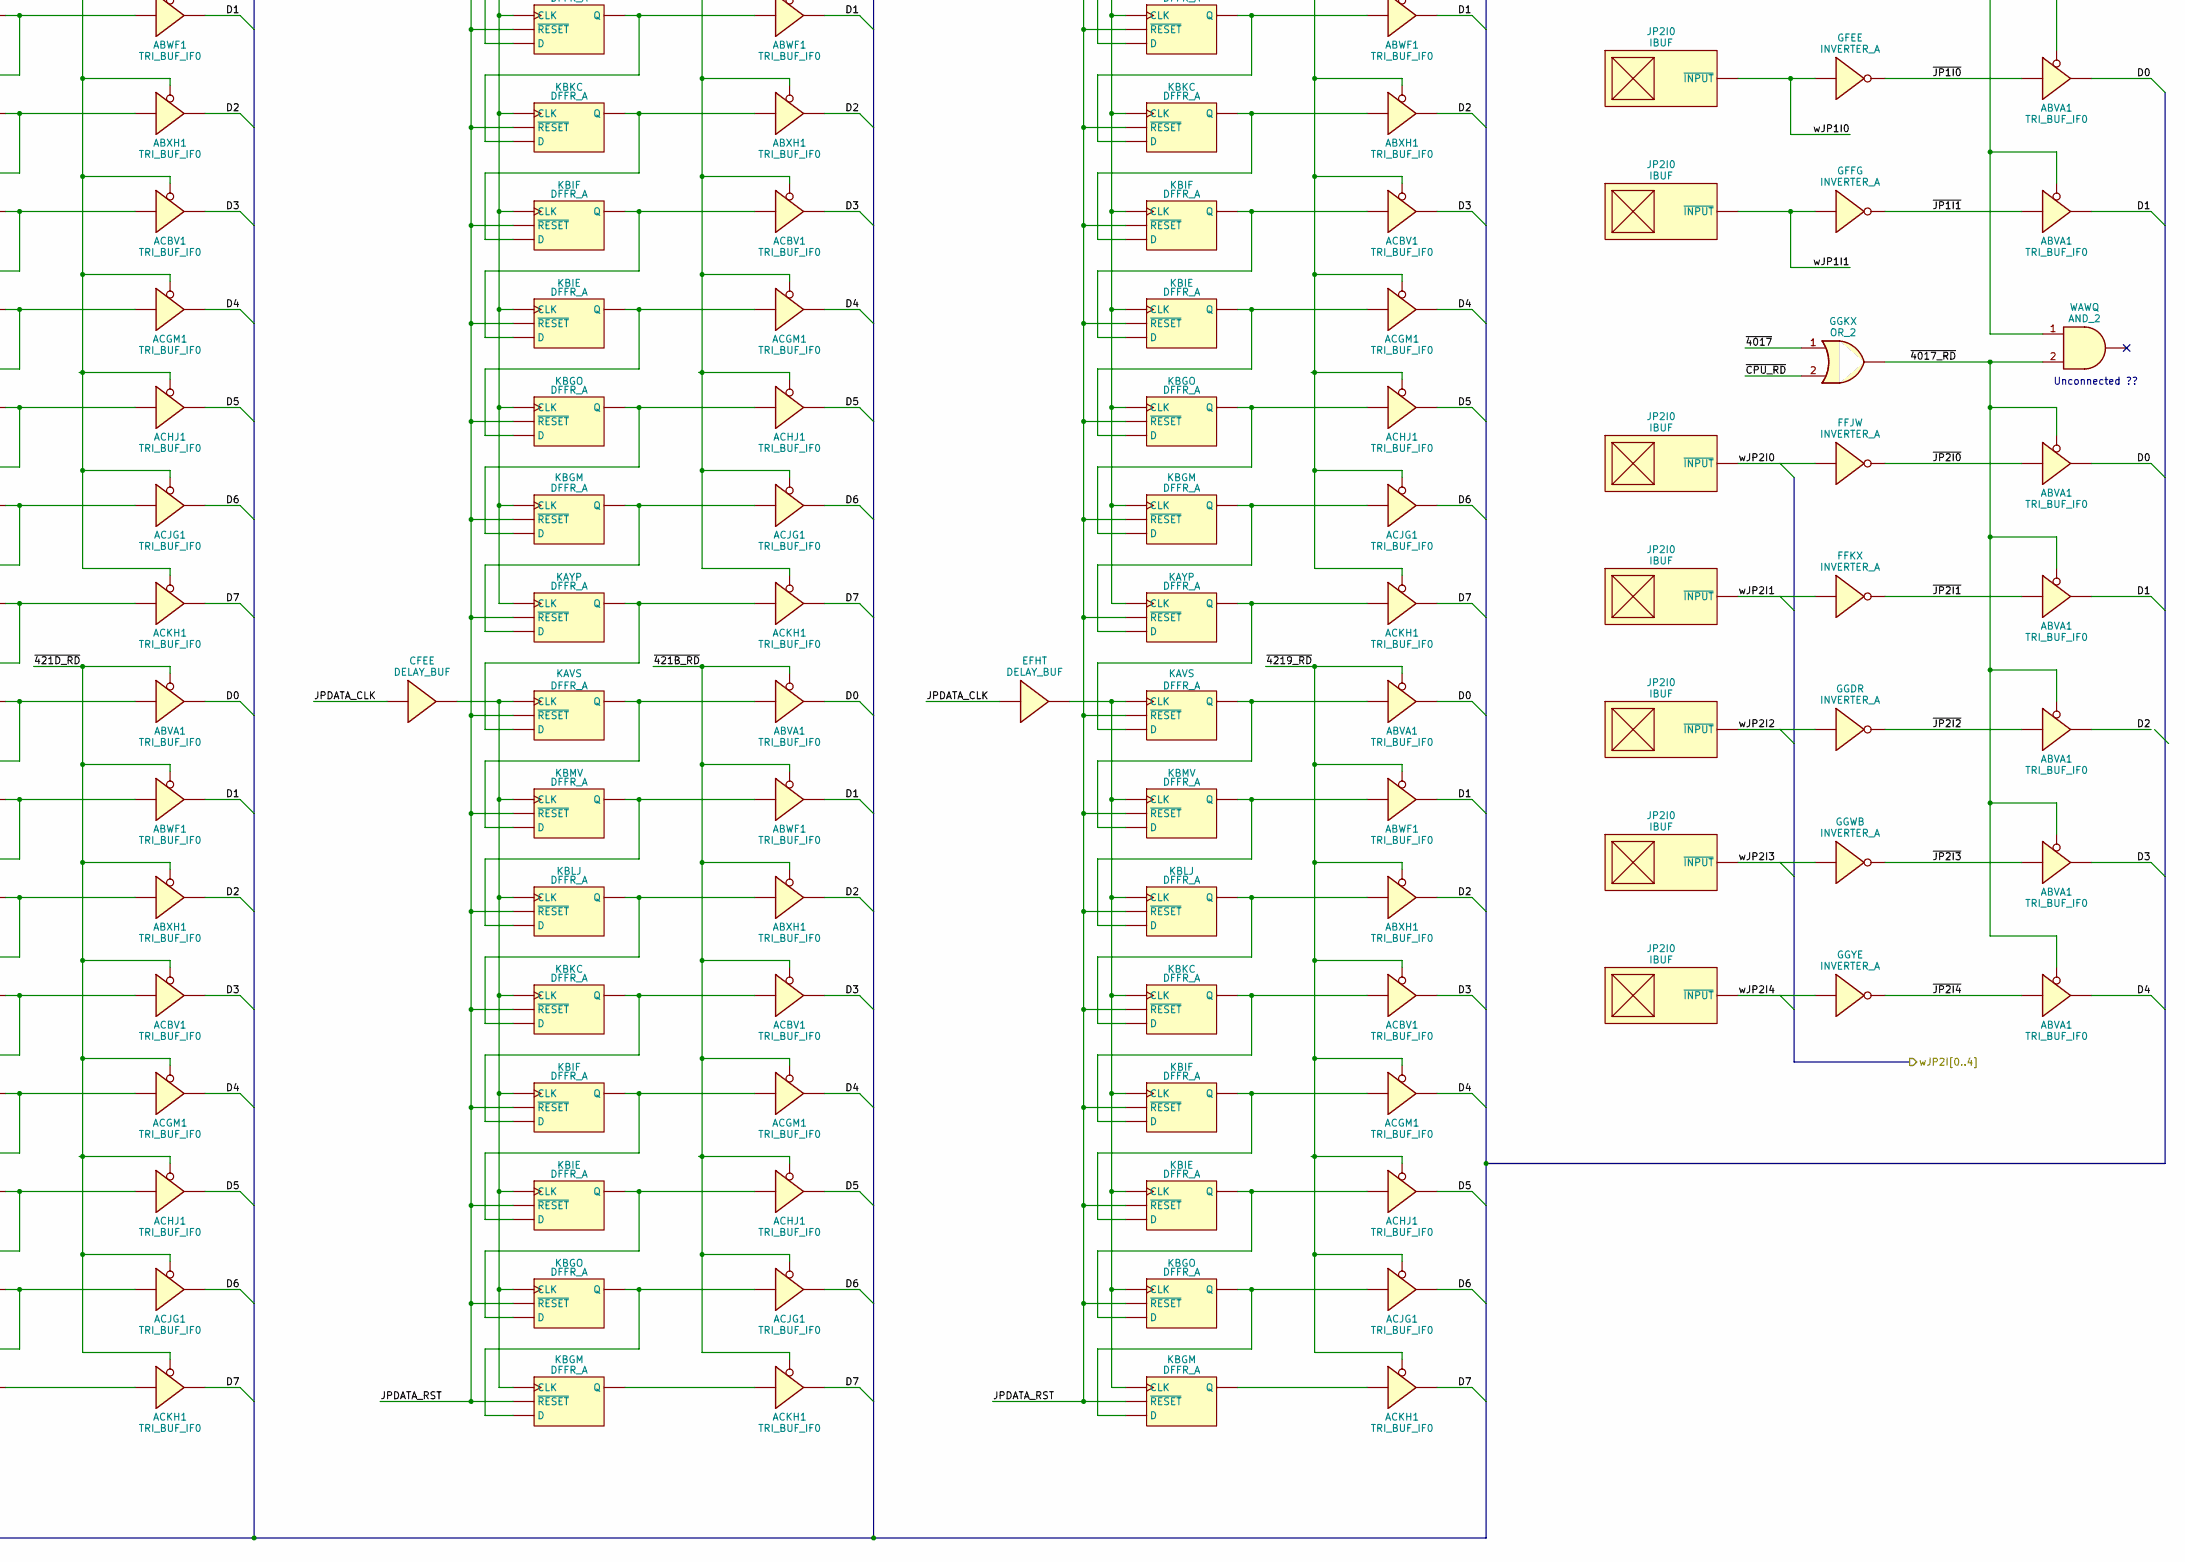
[picture p86: schematic joypads.kicad_sch, part in row 2, column 2]

Parts:
ABVA1: TRI_BUF_IF0
ABWF1: TRI_BUF_IF0
ABXH1: TRI_BUF_IF0
ACBV1: TRI_BUF_IF0
ACGM1: TRI_BUF_IF0
ACHJ1: TRI_BUF_IF0
ACJG1: TRI_BUF_IF0
ACKH1: TRI_BUF_IF0
AFDJ: BUF_INV
AFFY: DELAY_BUF
AGJS: OR_2
BAOZ: NAND_5
BFAR: BUF_INV
BFCS: DELAY_BUF
BGIJ: OR_2
CFDM: BUF_INV
CFEE: DELAY_BUF
CGAY: OR_2
DFBW: BUF_INV
DFFR: DELAY_BUF
DGLJ: OR_2
EFEZ: BUF
EFGJ: BUF_INV
EFHT: DELAY_BUF
FFHX: BUF
FFJW: INVERTER_A
FFKX: INVERTER_A
FFLE: DELAY_BUF
GFAY: DELAY_BUF
GFCS: BUF
GFEE: INVERTER_A
GFFG: INVERTER_A
GFLI: INVERTER_A
GFLT: INVERTER_A
GFVV: OR_2
GGAH: INVERTER_A
GGBE: INVERTER_A
GGDR: INVERTER_A
GGFM: INVERTER_A
GGHN: INVERTER_A
GGKX: OR_2
GGON: INVERTER_A
GGRM: INVERTER_A
GGWB: INVERTER_A
GGYE: INVERTER_A
JP1CLK, JP2CLK: OBUF_A
JP2I0: IOBUF_A
KAVS: DFFR_A
KAYP: DFFR_A
KBGM: DFFR_A
KBGO: DFFR_A
KBIE: DFFR_A
KBIF: DFFR_A
KBKC: DFFR_A
KBLJ: DFFR_A
KBMV: DFFR_A
MBUP: AND_4_NOR_2
OACG: DELAY_BUF
OAMJ: DELAY_BUF
OAXV: AND_2
OAYK: INVERTER_A
ODYR: INVERTER_A
RBAH: DFFR_B
RBFP: DFFR_B
RBPF: DFFR_B
RBSA: DFFR_B
RBTV: DFFR_B
U33, U38: OR_2
VAAA: OR_2
VAAG: BUF
VACD: INVERTER_A
VAFA: INVERTER_A
VAGU: NAND_3
VAKQ: INVERTER_A
VAQL: INVERTER_A
VASJ: BUF
VASU: NAND_2
VAYR: INVERTER_A
VAYV: OR_2
VBBU: AND_2
VBCP: AND_2
VBHG: OR_2
VBIE: OR_2
WAAH: BUF
WAJJ: INVERTER_A
WAOX: INVERTER_A
WAWQ: AND_2
WAXM: OR_2
WAYX: INVERTER_A
WAZZ: OR_2
WBNN: AND_4
WBOJ: OR_2
WBRU: INVERTER_A
WBUZ: INVERTER_A
WBXS: INVERTER_A
XAAX: BUF_INV
XAOJ: INVERTER_A
YAAV: BUF_INV
YAOH: DELAY_BUF
YBOV: OR_2
ZAAT: BUF_INV
ZAGC: DELAY_BUF
ZBMI: OR_2

Connections:
420X: BAOZ.5
421X: BAOZ.5
65816_?: ABVA1.1 (IN), ABVA1.3 (IN), ABWF1.1 (IN), ABWF1.3 (IN), ABXH1.1 (IN), ABXH1.3 (IN)
+5V: JP2I0.3 (~DRV_HIGH)
A0: BAOZ.1, WBRU.1
A1: BAOZ.2, WBUZ.1
A2: BAOZ.3, WBXS.1
A3: BAOZ.4, XAOJ.1
AUTO_JP0: RBTV.7 (Q), WBNN.4
AUTO_JP1: RBSA.7 (Q), WBNN.3
AUTO_JP2: RBPF.7 (Q), WBNN.2
AUTO_JP3: RBFP.7 (Q), WBNN.1
AUTO_JP_EN: VAQL.1
AUTO_JP_READING: RBAH.6 (~Q), VASU.2
D0: ABVA1.4, KAVS.2 (D), KBMV.2 (D)
D1: ABVA1.4, ABWF1.4, KBLJ.2 (D), KBMV.2 (D)
D2: ABVA1.4, ABXH1.4, KBKC.2 (D), KBLJ.2 (D)
D3: ABVA1.4, ACBV1.4, KBKC.2 (D)
D4: ABVA1.4, ACGM1.4, KBIF.2 (D)
D5: ACHJ1.4, KBIE.2 (D)
D6: ACJG1.4, KBGO.2 (D)
D7: ACKH1.4, KBGM.2 (D)
JPDATA_CLK: AFFY.1, BFCS.1, CFEE.1, DFFR.1, EFHT.1, FFLE.1, RBAH.3 (CLK), RBAH.4 (~CLK), RBTV.3 (CLK), RBTV.4 (~CLK), VASU.3, VAYV.2, YAOH.1, ZAGC.1
JPDATA_RST: KAVS.1 (~RESET), KAVS.5 (~RESET), KAYP.1 (~RESET), KAYP.5 (~RESET), KBGM.1 (~RESET), KBGM.5 (~RESET), KBGO.1 (~RESET), KBGO.5 (~RESET), KBIE.1 (~RESET), KBIE.5 (~RESET), KBIF.1 (~RESET), KBIF.5 (~RESET), KBKC.1 (~RESET), KBKC.5 (~RESET), KBLJ.1 (~RESET), KBLJ.5 (~RESET), KBMV.1 (~RESET), KBMV.5 (~RESET), VASJ.2
JPO0: JP2I0.1 (~INPUT), XAAX.2
JPO1: JP2I0.1 (~INPUT), YAAV.2
JPO2: JP2I0.1 (~INPUT), ZAAT.2
JPO3: AFDJ.2, JP2I0.1 (~INPUT)
JPO4: BFAR.2, JP2I0.1 (~INPUT)
JPO5: CFDM.2, JP2I0.1 (~INPUT)
JPO6: DFBW.2, JP2I0.1 (~INPUT)
JPO7: EFGJ.2, JP2I0.1 (~INPUT)
MODE2_OR_MODE3: VAKQ.1
MODE5_OR_MODE7: ABVA1.2 (~ENA)
unnamed: ABVA1.1 (IN), ABVA1.3 (IN), GFLI.2, KAVS.6 (Q), KBKC.6 (Q), KBLJ.2 (D), KBLJ.6 (Q), KBMV.2 (D), KBMV.6 (Q), WAZZ.3
unnamed: ABVA1.2 (~ENA), ABWF1.2 (~ENA), ABXH1.2 (~ENA), ODYR.2
unnamed: ABVA1.4, ABWF1.4, ABXH1.4, EFEZ.1, FFHX.1, GFCS.1
unnamed: ABWF1.1 (IN), ABWF1.3 (IN), GFLT.2, KBKC.2 (D), KBLJ.2 (D), KBLJ.6 (Q), KBMV.6 (Q)
unnamed: ABXH1.1 (IN), ABXH1.3 (IN), GGAH.2, KBIF.2 (D), KBKC.2 (D), KBKC.6 (Q), KBLJ.6 (Q)
unnamed: ACBV1.1 (IN), ACBV1.3 (IN), GGBE.2, KBIE.2 (D), KBIF.2 (D), KBIF.6 (Q), KBKC.6 (Q)
unnamed: ACGM1.1 (IN), ACGM1.3 (IN), GGFM.2, KBGO.2 (D), KBIE.2 (D), KBIE.6 (Q), KBIF.6 (Q)
unnamed: ACHJ1.1 (IN), ACHJ1.3 (IN), GGHN.2, KBGM.2 (D), KBGO.2 (D), KBGO.6 (Q), KBIE.6 (Q)
unnamed: ACJG1.1 (IN), ACJG1.3 (IN), GGON.2, KAYP.2 (D), KBGM.2 (D), KBGM.6 (Q), KBGO.6 (Q)
unnamed: ACKH1.1 (IN), ACKH1.3 (IN), GGRM.2, KAVS.2 (D), KAYP.6 (Q), KBGM.6 (Q)
unnamed: AFDJ.1, KBKC.6 (Q)
unnamed: AFFY.2, KAVS.3 (CLK), KAVS.4 (~CLK), KBGM.3 (CLK), KBGM.4 (~CLK), KBGO.3 (CLK), KBGO.4 (~CLK), KBIE.3 (CLK), KBIE.4 (~CLK), KBIF.3 (CLK), KBIF.4 (~CLK), KBKC.3 (CLK), KBKC.4 (~CLK), KBLJ.3 (CLK), KBLJ.4 (~CLK), KBMV.3 (CLK), KBMV.4 (~CLK)
unnamed: AGJS.1, BAOZ.6
unnamed: BAOZ.1, WBRU.2
unnamed: BAOZ.2, WBUZ.2
unnamed: BAOZ.3, WBXS.2
unnamed: BAOZ.4, XAOJ.2
unnamed: BAOZ.6, BGIJ.1, CGAY.1, DGLJ.1, U33.1, U38.1, WBOJ.1, YBOV.1, ZBMI.1
unnamed: BFAR.1, KBIF.6 (Q)
unnamed: BFCS.2, KAYP.3 (CLK), KAYP.4 (~CLK), KBGM.3 (CLK), KBGM.4 (~CLK), KBGO.3 (CLK), KBGO.4 (~CLK), KBIE.3 (CLK), KBIE.4 (~CLK), KBIF.3 (CLK), KBIF.4 (~CLK), KBKC.3 (CLK), KBKC.4 (~CLK), KBLJ.3 (CLK), KBLJ.4 (~CLK), KBMV.3 (CLK), KBMV.4 (~CLK)
unnamed: CFDM.1, KBIE.6 (Q)
unnamed: CFEE.2, KAVS.3 (CLK), KAVS.4 (~CLK), KBGM.3 (CLK), KBGM.4 (~CLK), KBGO.3 (CLK), KBGO.4 (~CLK), KBIE.3 (CLK), KBIE.4 (~CLK), KBIF.3 (CLK), KBIF.4 (~CLK), KBKC.3 (CLK), KBKC.4 (~CLK), KBLJ.3 (CLK), KBLJ.4 (~CLK), KBMV.3 (CLK), KBMV.4 (~CLK)
unnamed: DFBW.1, KBGO.6 (Q)
unnamed: DFFR.2, KAYP.3 (CLK), KAYP.4 (~CLK), KBGM.3 (CLK), KBGM.4 (~CLK), KBGO.3 (CLK), KBGO.4 (~CLK), KBIE.3 (CLK), KBIE.4 (~CLK), KBIF.3 (CLK), KBIF.4 (~CLK), KBKC.3 (CLK), KBKC.4 (~CLK), KBLJ.3 (CLK), KBLJ.4 (~CLK), KBMV.3 (CLK), KBMV.4 (~CLK)
unnamed: EFEZ.2, GFAY.1
unnamed: EFGJ.1, KBGM.6 (Q)
unnamed: EFHT.2, KAVS.3 (CLK), KAVS.4 (~CLK), KBGM.3 (CLK), KBGM.4 (~CLK), KBGO.3 (CLK), KBGO.4 (~CLK), KBIE.3 (CLK), KBIE.4 (~CLK), KBIF.3 (CLK), KBIF.4 (~CLK), KBKC.3 (CLK), KBKC.4 (~CLK), KBLJ.3 (CLK), KBLJ.4 (~CLK), KBMV.3 (CLK), KBMV.4 (~CLK)
unnamed: FFHX.2, GFAY.1
unnamed: FFLE.2, KAYP.3 (CLK), KAYP.4 (~CLK), KBGM.3 (CLK), KBGM.4 (~CLK), KBGO.3 (CLK), KBGO.4 (~CLK), KBIE.3 (CLK), KBIE.4 (~CLK), KBIF.3 (CLK), KBIF.4 (~CLK), KBKC.3 (CLK), KBKC.4 (~CLK), KBLJ.3 (CLK), KBLJ.4 (~CLK), KBMV.3 (CLK), KBMV.4 (~CLK)
unnamed: GFAY.1, GFCS.2
unnamed: GFAY.2, JP1CLK.1, JP2CLK.1
unnamed: GFLI.1, JP2I0.2 (~INPUT)
unnamed: GFLT.1, JP2I0.2 (~INPUT)
unnamed: GGAH.1, JP2I0.2 (~INPUT)
unnamed: GGBE.1, JP2I0.2 (~INPUT)
unnamed: GGFM.1, JP2I0.2 (~INPUT)
unnamed: GGHN.1, JP2I0.2 (~INPUT)
unnamed: GGON.1, JP2I0.2 (~INPUT)
unnamed: GGRM.1, JP2I0.2 (~INPUT)
unnamed: JP1CLK.1, OACG.2
unnamed: JP2CLK.1, OAMJ.2
unnamed: KAVS.1 (~RESET), KAVS.5 (~RESET), KBGM.1 (~RESET), KBGM.5 (~RESET), KBGO.1 (~RESET), KBGO.5 (~RESET), KBIE.1 (~RESET), KBIE.5 (~RESET), KBIF.1 (~RESET), KBIF.5 (~RESET), KBKC.1 (~RESET), KBKC.5 (~RESET), KBLJ.1 (~RESET), KBLJ.5 (~RESET), KBMV.1 (~RESET), KBMV.5 (~RESET)
unnamed: KAVS.3 (CLK), KAVS.4 (~CLK), KBGM.3 (CLK), KBGM.4 (~CLK), KBGO.3 (CLK), KBGO.4 (~CLK), KBIE.3 (CLK), KBIE.4 (~CLK), KBIF.3 (CLK), KBIF.4 (~CLK), KBKC.3 (CLK), KBKC.4 (~CLK), KBLJ.3 (CLK), KBLJ.4 (~CLK), KBMV.3 (CLK), KBMV.4 (~CLK), YAOH.2
unnamed: KAVS.6 (Q), XAAX.1
unnamed: KAYP.3 (CLK), KAYP.4 (~CLK), KBGM.3 (CLK), KBGM.4 (~CLK), KBGO.3 (CLK), KBGO.4 (~CLK), KBIE.3 (CLK), KBIE.4 (~CLK), KBIF.3 (CLK), KBIF.4 (~CLK), KBKC.3 (CLK), KBKC.4 (~CLK), KBLJ.3 (CLK), KBLJ.4 (~CLK), KBMV.3 (CLK), KBMV.4 (~CLK), ZAGC.2
unnamed: KBKC.3 (CLK), KBKC.4 (~CLK), KBLJ.3 (CLK), KBLJ.4 (~CLK), KBMV.3 (CLK), KBMV.4 (~CLK), WAXM.3
unnamed: KBLJ.6 (Q), ZAAT.1
unnamed: KBMV.6 (Q), WAZZ.2, YAAV.1
unnamed: MBUP.2, OAXV.3, WAJJ.1
unnamed: MBUP.3, WAOX.1
unnamed: MBUP.4, WAJJ.2
unnamed: OACG.1, WAAH.2
unnamed: OAMJ.1, VAAG.2
unnamed: OAXV.2, OAYK.2
unnamed: RBAH.1 (~RESET), RBAH.5 (~RESET), RBFP.1 (~RESET), RBFP.5 (~RESET), RBPF.1 (~RESET), RBPF.5 (~RESET), RBSA.1 (~RESET), RBSA.5 (~RESET), RBTV.1 (~RESET), RBTV.5 (~RESET), RBTV.7 (Q), VASJ.1, VAYR.1
unnamed: RBAH.2 (D), WBNN.5
unnamed: RBFP.2 (D), RBFP.6 (~Q)
unnamed: RBFP.3 (CLK), RBFP.4 (~CLK), RBPF.2 (D), RBPF.6 (~Q)
unnamed: RBPF.3 (CLK), RBPF.4 (~CLK), RBSA.2 (D), RBSA.6 (~Q)
unnamed: RBSA.2 (D), RBTV.6 (~Q), VAGU.2
unnamed: RBSA.3 (CLK), RBSA.4 (~CLK), RBTV.2 (D), RBTV.3 (CLK), RBTV.4 (~CLK), RBTV.6 (~Q), VACD.2
unnamed: RBSA.6 (~Q), VAGU.1
unnamed: RBTV.2 (D), VAAA.3, VAFA.2, WAYX.1
unnamed: RBTV.3 (CLK), RBTV.4 (~CLK), VACD.1, VASU.1, WAOX.2
unnamed: VAAA.1, VAQL.2
unnamed: VAAA.2, VAGU.4
unnamed: VAAG.1, VBBU.3
unnamed: VAGU.3, VAKQ.2
unnamed: VAYR.2, VAYV.1
unnamed: VAYV.3, VBBU.1, VBCP.2
unnamed: VBBU.2, VBHG.3
unnamed: VBCP.1, VBIE.3
unnamed: VBCP.3, WAAH.1
unnamed: WAYX.2, WAZZ.1
wJP1I0: GFEE.1, JP2I0.1 (~INPUT)
wJP1I1: GFFG.1, JP2I0.1 (~INPUT)
wJP2I0: FFJW.1, JP2I0.1 (~INPUT)
wJP2I1: FFKX.1, JP2I0.1 (~INPUT)
wJP2I2: GGDR.1, JP2I0.1 (~INPUT)
wJP2I3: GGWB.1, JP2I0.1 (~INPUT)
wJP2I4: GGYE.1, JP2I0.1 (~INPUT)
wMASS: KBKC.1 (~RESET), KBKC.5 (~RESET), KBLJ.1 (~RESET), KBLJ.5 (~RESET), KBMV.1 (~RESET), KBMV.5 (~RESET), RBSA.1 (~RESET), RBSA.5 (~RESET), RBTV.1 (~RESET), RBTV.5 (~RESET)
wNBRL_wNBQA_XIN/4: MBUP.1
wOATI_~XIN/256: MBUP.3
wOCOG_~MODE7: ODYR.1
wVBLANK: VAFA.1
~421A_RD: ABVA1.2 (~ENA), ABWF1.2 (~ENA), ABXH1.2 (~ENA), ACBV1.2 (~ENA), ACGM1.2 (~ENA), ACHJ1.2 (~ENA), ACJG1.2 (~ENA), ACKH1.2 (~ENA), CGAY.3
~421B_RD: ABVA1.2 (~ENA), ABWF1.2 (~ENA), ABXH1.2 (~ENA), ACBV1.2 (~ENA), ACGM1.2 (~ENA), ACHJ1.2 (~ENA), ACJG1.2 (~ENA), ACKH1.2 (~ENA), CGAY.3
~421C_RD: ABVA1.2 (~ENA), ABWF1.2 (~ENA), ABXH1.2 (~ENA), ACBV1.2 (~ENA), ACGM1.2 (~ENA), ACHJ1.2 (~ENA), ACJG1.2 (~ENA), ACKH1.2 (~ENA), BGIJ.3
~421D_RD: ABVA1.2 (~ENA), ABWF1.2 (~ENA), ABXH1.2 (~ENA), ACBV1.2 (~ENA), ACGM1.2 (~ENA), ACHJ1.2 (~ENA), ACJG1.2 (~ENA), ACKH1.2 (~ENA), AGJS.3
~421E_RD: ABVA1.2 (~ENA), ABWF1.2 (~ENA), ABXH1.2 (~ENA), ACBV1.2 (~ENA), ACGM1.2 (~ENA), ACHJ1.2 (~ENA), ACJG1.2 (~ENA), ACKH1.2 (~ENA), ZBMI.3
~421F_RD: ABVA1.2 (~ENA), ABWF1.2 (~ENA), ABXH1.2 (~ENA), ACBV1.2 (~ENA), ACGM1.2 (~ENA), ACHJ1.2 (~ENA), ACJG1.2 (~ENA), ACKH1.2 (~ENA), YBOV.3
~4016_RD: ABVA1.2 (~ENA), GFVV.3, WAWQ.1
~4016: GFVV.1, VBIE.2, WAXM.1
~4017_RD: ABVA1.2 (~ENA), GGKX.3, WAWQ.2
~4017: GGKX.1, VBHG.1
~4201_WR: KAVS.3 (CLK), KAVS.4 (~CLK), KBGM.3 (CLK), KBGM.4 (~CLK), KBGO.3 (CLK), KBGO.4 (~CLK), KBIE.3 (CLK), KBIE.4 (~CLK), KBIF.3 (CLK), KBIF.4 (~CLK), KBKC.3 (CLK), KBKC.4 (~CLK), KBLJ.3 (CLK), KBLJ.4 (~CLK), KBMV.3 (CLK), KBMV.4 (~CLK), WBOJ.3
~4213_RD: ABVA1.2 (~ENA), ABWF1.2 (~ENA), ABXH1.2 (~ENA), ACBV1.2 (~ENA), ACGM1.2 (~ENA), ACHJ1.2 (~ENA), ACJG1.2 (~ENA), ACKH1.2 (~ENA), U38.3
~4218_RD: ABVA1.2 (~ENA), ABWF1.2 (~ENA), ABXH1.2 (~ENA), ACBV1.2 (~ENA), ACGM1.2 (~ENA), ACHJ1.2 (~ENA), ACJG1.2 (~ENA), ACKH1.2 (~ENA), U33.3
~4219_RD: ABVA1.2 (~ENA), ABWF1.2 (~ENA), ABXH1.2 (~ENA), ACBV1.2 (~ENA), ACGM1.2 (~ENA), ACHJ1.2 (~ENA), ACJG1.2 (~ENA), ACKH1.2 (~ENA), DGLJ.3
~CPU_RD: AGJS.2, BGIJ.2, CGAY.2, DGLJ.2, GFVV.2, GGKX.2, U33.2, U38.2, VBHG.2, VBIE.1, YBOV.2, ZBMI.2
~CPU_WR: WAXM.2, WBOJ.2
~JP1I0: ABVA1.1 (IN), ABVA1.3 (IN), GFEE.2, KBMV.2 (D)
~JP1I1: ABVA1.1 (IN), ABVA1.3 (IN), GFFG.2, KBMV.2 (D)
~JP2I0: ABVA1.1 (IN), ABVA1.3 (IN), FFJW.2, KBMV.2 (D)
~JP2I1: ABVA1.1 (IN), ABVA1.3 (IN), FFKX.2, KBMV.2 (D)
~JP2I2: ABVA1.1 (IN), ABVA1.3 (IN), GGDR.2
~JP2I3: ABVA1.1 (IN), ABVA1.3 (IN), GGWB.2
~JP2I4: ABVA1.1 (IN), ABVA1.3 (IN), GGYE.2
~MODE6: OAYK.1
~wRDY: OAXV.1

Notes on the sheet:
Unconnected ??
421F/421E READ
4201 WRITE
JP counter is reset outside of VBLANK and count up to 16 for 16 JP clock cycles to shift data into JP registers at the start of VBLANK.
4016/4017 READ
4016 WRITE
421B/421A READ
Normal clock is XIN/256 which will take 3 scamline lines to fill in jp shift registers. In MODE6, XIN/4 clock is used instead when RDY = 0.
421D/421C READ
4219/4218 READ
4201, 4213 and 4218-F Address decoding
4213 READ
