rgalland/SNES_S-CPU_Schematics/S-CPU_kicad/legacyjpregs.kicad_sch

## KiCad design S-CPU_kicad/legacyjpregs.kicad_sch (2024-12-24, an earlier design)

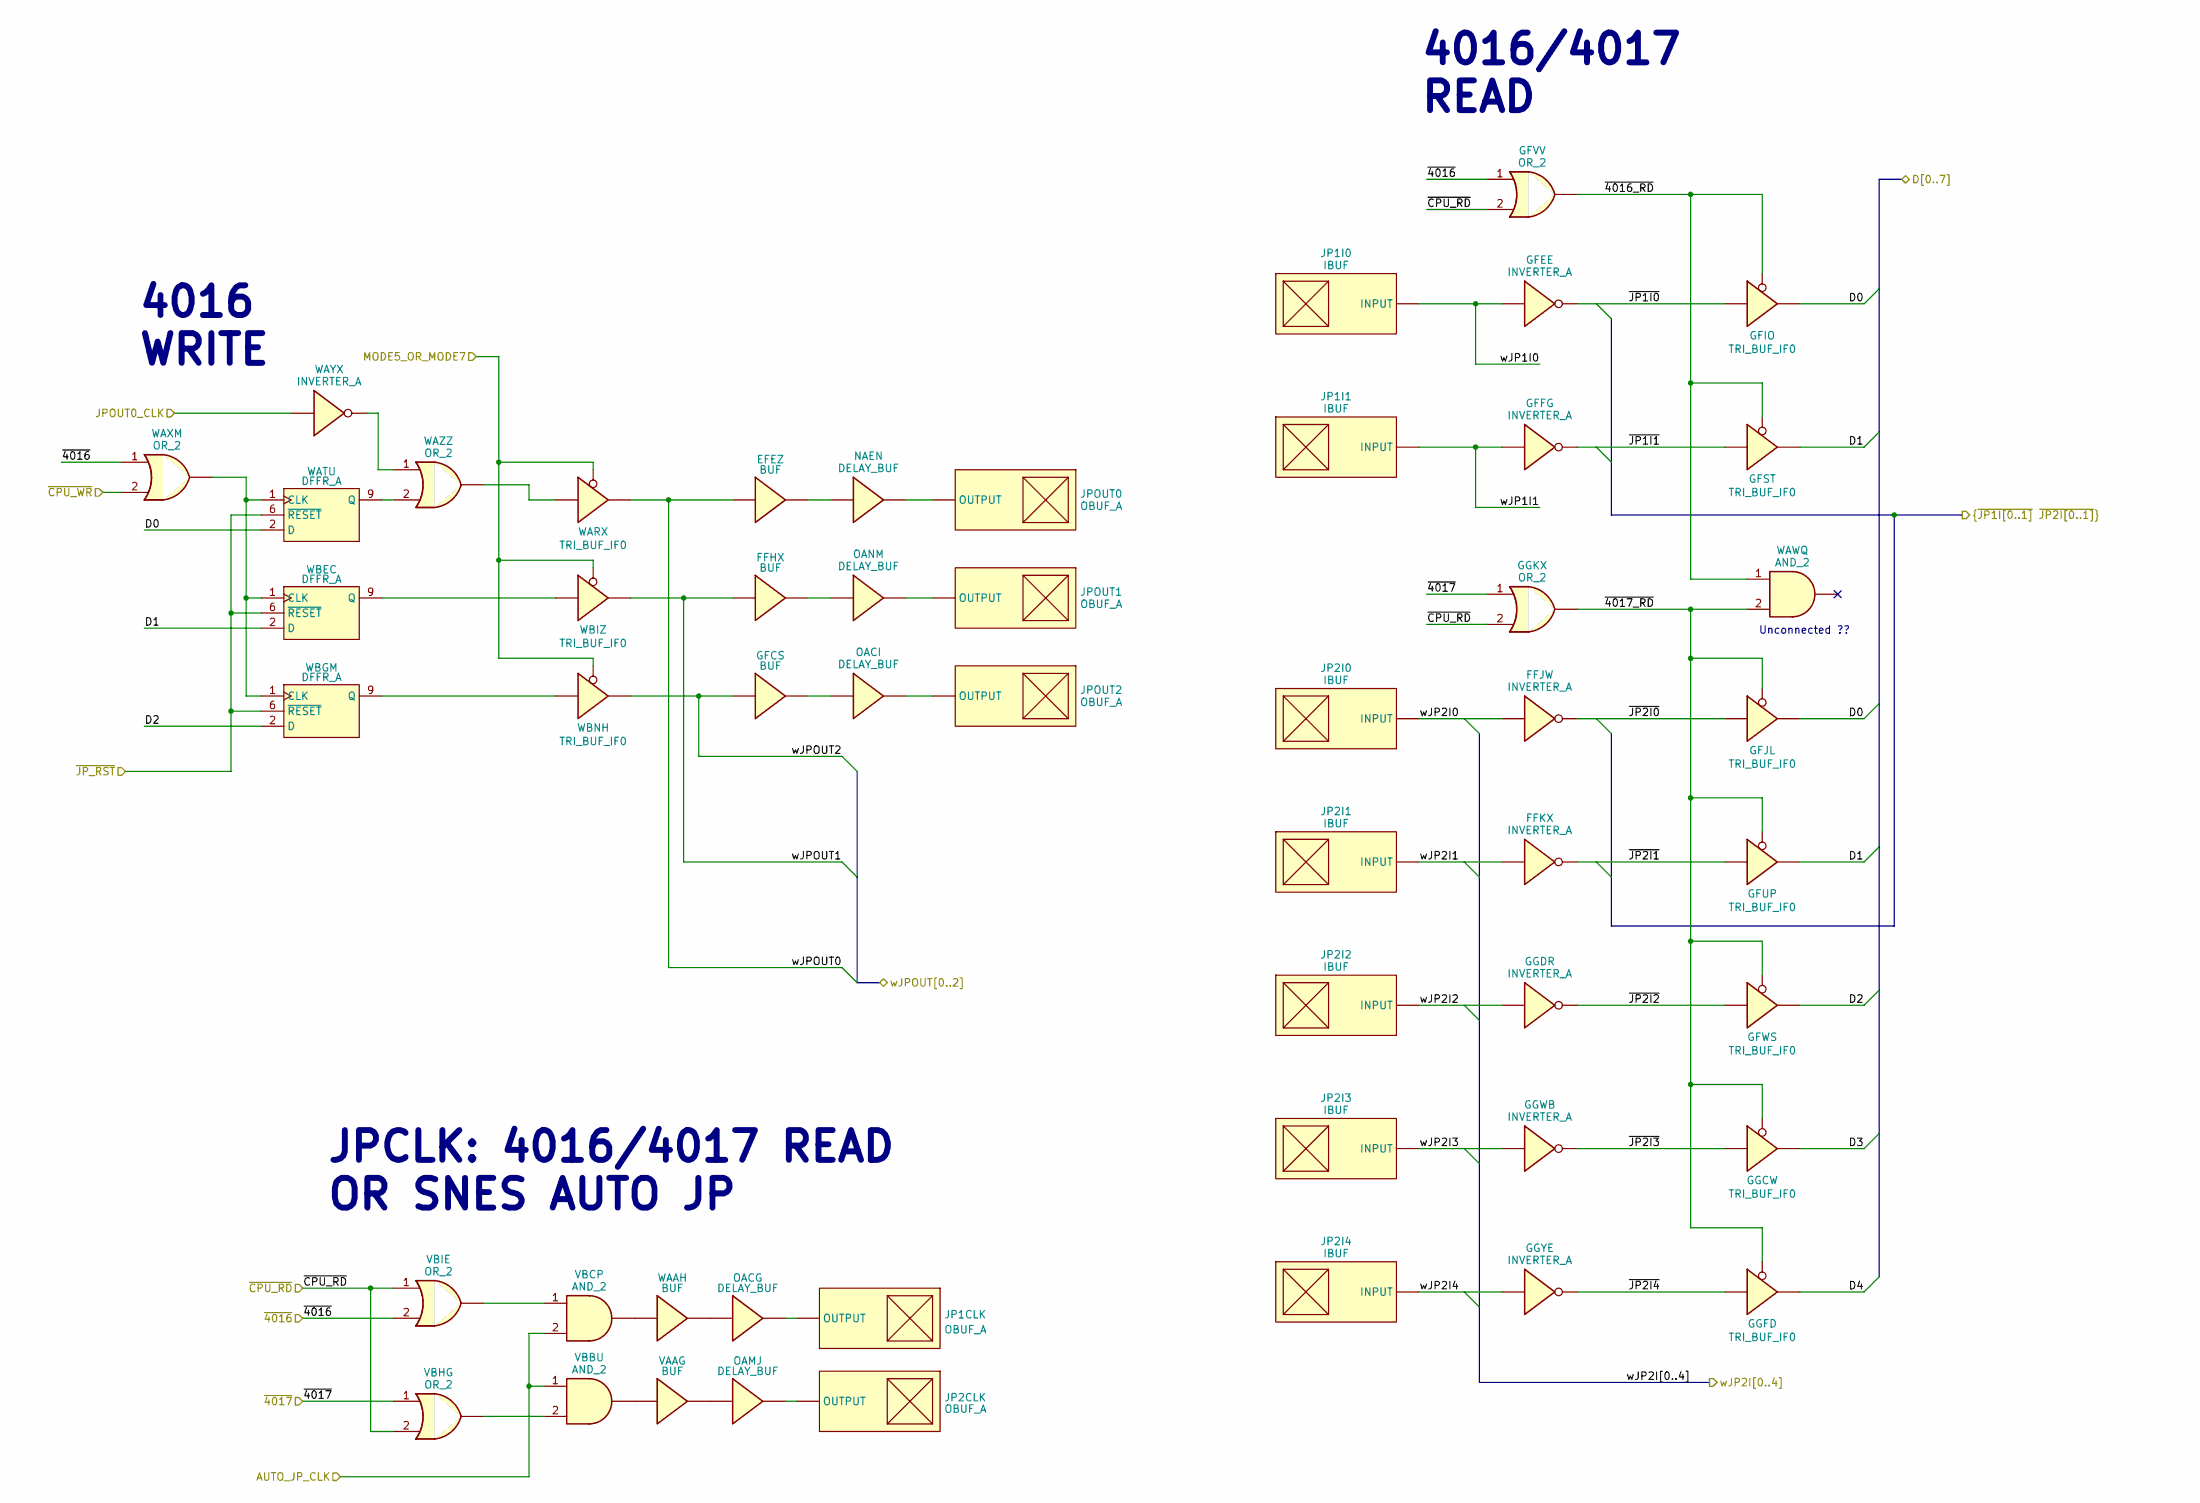
[picture p87: schematic legacyjpregs.kicad_sch]

Parts:
EFEZ: BUF
FFHX: BUF
FFJW: INVERTER_A
FFKX: INVERTER_A
GFCS: BUF
GFEE: INVERTER_A
GFFG: INVERTER_A
GFIO: TRI_BUF_IF0
GFJL: TRI_BUF_IF0
GFST: TRI_BUF_IF0
GFUP: TRI_BUF_IF0
GFVV: OR_2
GFWS: TRI_BUF_IF0
GGCW: TRI_BUF_IF0
GGDR: INVERTER_A
GGFD: TRI_BUF_IF0
GGKX: OR_2
GGWB: INVERTER_A
GGYE: INVERTER_A
JP1CLK, JP2CLK: OBUF_A
JP1I0, JP1I1, JP2I0, JP2I1, JP2I2, JP2I3, JP2I4: IBUF
JPOUT0, JPOUT1, JPOUT2: OBUF_A
NAEN: DELAY_BUF
OACG: DELAY_BUF
OACI: DELAY_BUF
OAMJ: DELAY_BUF
OANM: DELAY_BUF
VAAG: BUF
VBBU: AND_2
VBCP: AND_2
VBHG: OR_2
VBIE: OR_2
WAAH: BUF
WARX: TRI_BUF_IF0
WATU: DFFR_A
WAWQ: AND_2
WAXM: OR_2
WAYX: INVERTER_A
WAZZ: OR_2
WBEC: DFFR_A
WBGM: DFFR_A
WBIZ: TRI_BUF_IF0
WBNH: TRI_BUF_IF0

Connections:
AUTO_JP_CLK: VBBU.1, VBCP.2
D0: GFIO.4, GFJL.4, WATU.2 (D)
D1: GFST.4, GFUP.4, WBEC.2 (D)
D2: GFWS.4, WBGM.2 (D)
D3: GGCW.4
D4: GGFD.4
JPOUT0_CLK: WAYX.1
MODE5_OR_MODE7: WARX.2 (~ENA), WBIZ.2 (~ENA), WBNH.2 (~ENA)
unnamed: EFEZ.2, NAEN.1
unnamed: FFHX.2, OANM.1
unnamed: GFCS.2, OACI.1
unnamed: JP1CLK.1, OACG.2
unnamed: JP2CLK.1, OAMJ.2
unnamed: JPOUT0.1, NAEN.2
unnamed: JPOUT1.1, OANM.2
unnamed: JPOUT2.1, OACI.2
unnamed: OACG.1, WAAH.2
unnamed: OAMJ.1, VAAG.2
unnamed: VAAG.1, VBBU.3
unnamed: VBBU.2, VBHG.3
unnamed: VBCP.1, VBIE.3
unnamed: VBCP.3, WAAH.1
unnamed: WARX.1 (IN), WARX.3 (IN), WAZZ.3
unnamed: WATU.1 (CLK), WAXM.3, WBEC.1 (CLK), WBGM.1 (CLK)
unnamed: WATU.9 (Q), WAZZ.2
unnamed: WAYX.2, WAZZ.1
unnamed: WBEC.9 (Q), WBIZ.1 (IN), WBIZ.3 (IN)
unnamed: WBGM.9 (Q), WBNH.1 (IN), WBNH.3 (IN)
wJP1I0: GFEE.1, JP1I0.1
wJP1I1: GFFG.1, JP1I1.1
wJP2I0: FFJW.1, JP2I0.1
wJP2I1: FFKX.1, JP2I1.1
wJP2I2: GGDR.1, JP2I2.1
wJP2I3: GGWB.1, JP2I3.1
wJP2I4: GGYE.1, JP2I4.1
wJPOUT0: EFEZ.1, WARX.4
wJPOUT1: FFHX.1, WBIZ.4
wJPOUT2: GFCS.1, WBNH.4
~4016_RD: GFIO.2 (~ENA), GFST.2 (~ENA), GFVV.3, WAWQ.1
~4016: GFVV.1, VBIE.2, WAXM.1
~4017_RD: GFJL.2 (~ENA), GFUP.2 (~ENA), GFWS.2 (~ENA), GGCW.2 (~ENA), GGFD.2 (~ENA), GGKX.3, WAWQ.2
~4017: GGKX.1, VBHG.1
~CPU_RD: GFVV.2, GGKX.2, VBHG.2, VBIE.1
~CPU_WR: WAXM.2
~JP1I0: GFEE.2, GFIO.1 (IN), GFIO.3 (IN)
~JP1I1: GFFG.2, GFST.1 (IN), GFST.3 (IN)
~JP2I0: FFJW.2, GFJL.1 (IN), GFJL.3 (IN)
~JP2I1: FFKX.2, GFUP.1 (IN), GFUP.3 (IN)
~JP2I2: GFWS.1 (IN), GFWS.3 (IN), GGDR.2
~JP2I3: GGCW.1 (IN), GGCW.3 (IN), GGWB.2
~JP2I4: GGFD.1 (IN), GGFD.3 (IN), GGYE.2
~JP_RST: WATU.6 (~RESET), WBEC.6 (~RESET), WBGM.6 (~RESET)

Notes on the sheet:
JPCLK: 4016/4017 READ OR SNES AUTO JP
Unconnected ??
4016 WRITE
4016/4017 READ
