rgalland/SNES_S-CPU_Schematics/S-CPU_kicad/modes.kicad_sch

## KiCad design S-CPU_kicad/modes.kicad_sch (2024-12-24, an earlier design)

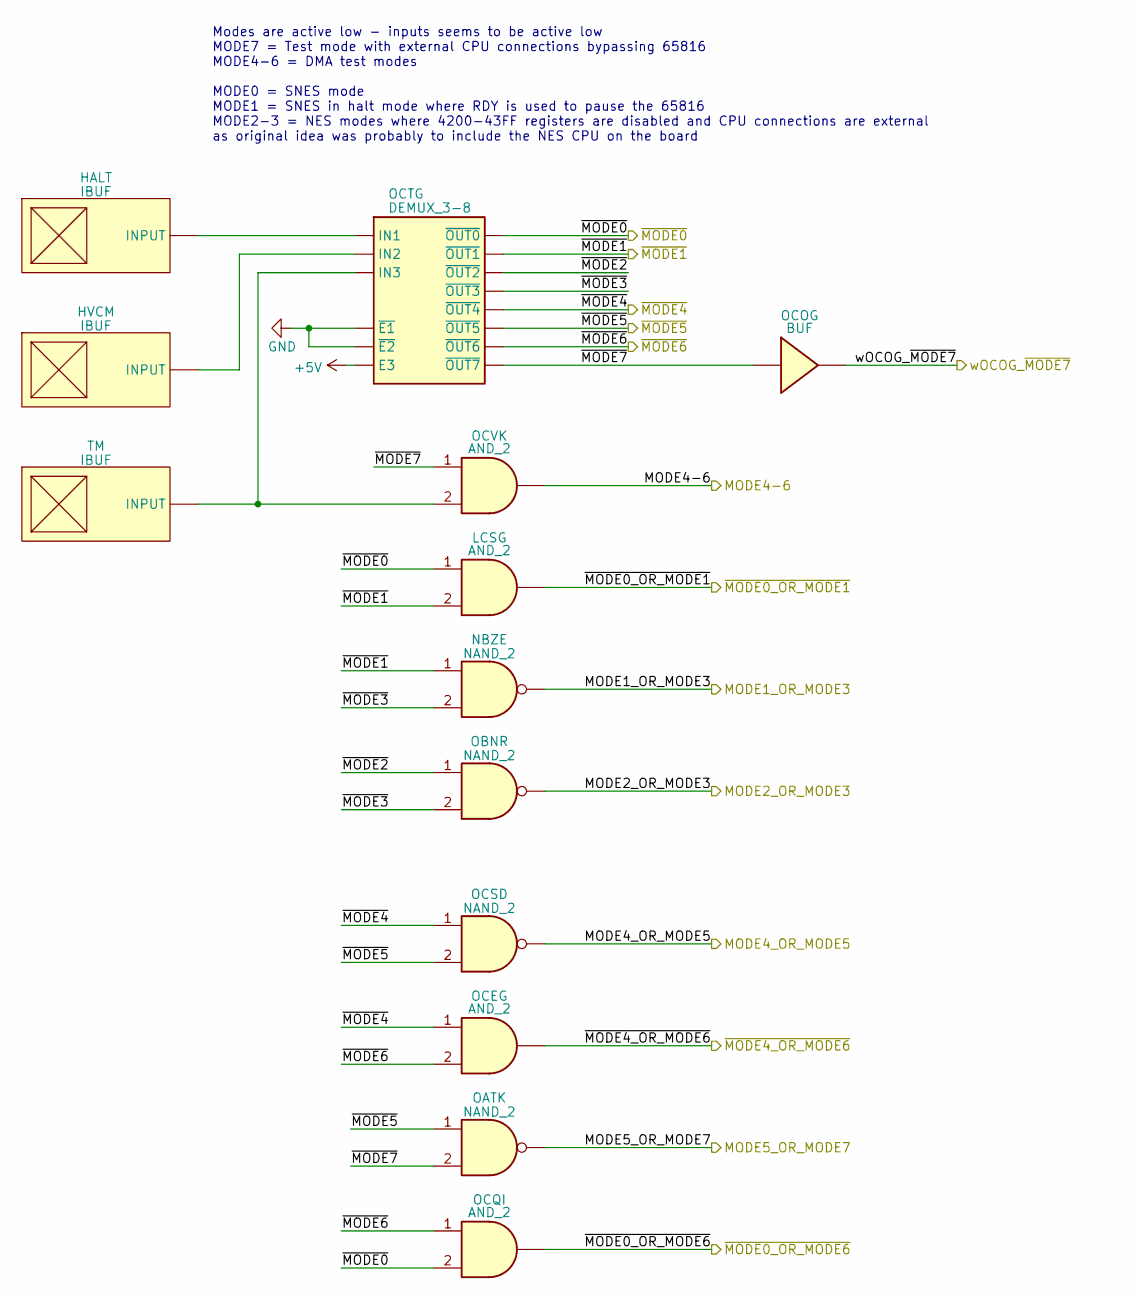
[picture p88: schematic modes.kicad_sch]

Parts:
HALT: IBUF
HVCM: IBUF
LCSG: AND_2
NBZE: NAND_2
OATK: NAND_2
OBNR: NAND_2
OCEG: AND_2
OCOG: BUF
OCQI: AND_2
OCSD: NAND_2
OCTG: DEMUX_3-8
OCVK: AND_2
TM: IBUF

Connections:
+5V: OCTG.
GND: OCTG.
MODE1_OR_MODE3: NBZE.3
MODE2_OR_MODE3: OBNR.3
MODE4-6: OCVK.3
MODE4_OR_MODE5: OCSD.3
MODE5_OR_MODE7: OATK.3
unnamed: HALT.1, OCTG.
unnamed: HVCM.1, OCTG.
unnamed: OCTG., OCVK.2, TM.1
wOCOG_~MODE7: OCOG.2
~MODE0_OR_MODE1: LCSG.3
~MODE0_OR_MODE6: OCQI.3
~MODE0: LCSG.1, OCQI.2, OCTG.
~MODE1: LCSG.2, NBZE.1, OCTG.
~MODE2: OBNR.1, OCTG.
~MODE3: NBZE.2, OBNR.2, OCTG.
~MODE4_OR_MODE6: OCEG.3
~MODE4: OCEG.1, OCSD.1, OCTG.
~MODE5: OATK.1, OCSD.2, OCTG.
~MODE6: OCEG.2, OCQI.1, OCTG.
~MODE7: OATK.2, OCOG.1, OCTG., OCVK.1

Notes on the sheet:
Modes are active low - inputs seems to be active low MODE7 = Test mode with external CPU connections bypassing 65816 MODE4-6 = DMA test modes MODE0 = SNES mode MODE1 = SNES in halt mode where RDY is used to pause the 65816 MODE2-3 = NES modes where 4200-43FF registers are disabled and CPU connectio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
