rgalland/SNES_S-CPU_Schematics/S-CPU_kicad/productremainder.kicad_sch

## KiCad design S-CPU_kicad/productremainder.kicad_sch (2024-12-24, an earlier design)

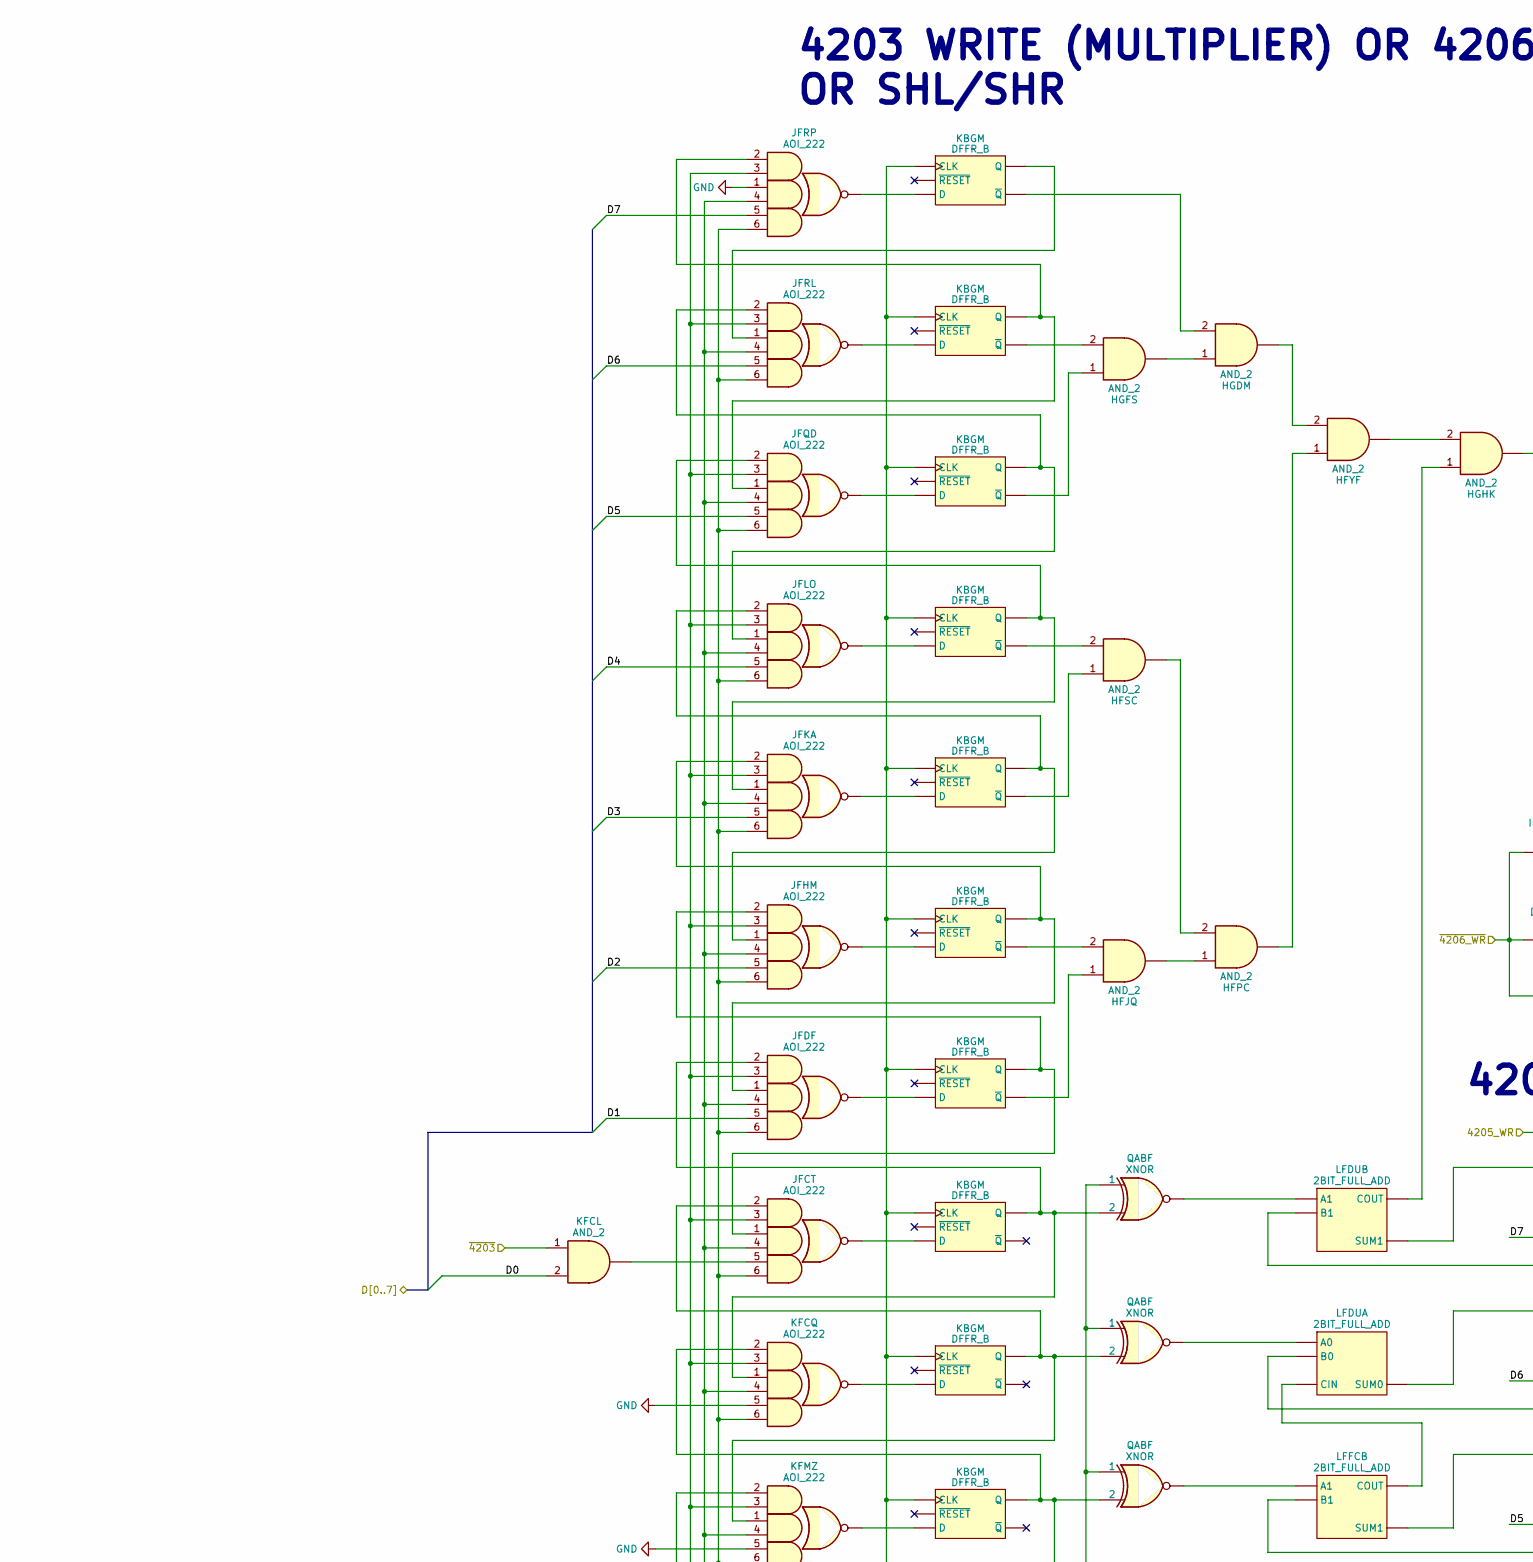
[picture p89: schematic productremainder.kicad_sch, part in row 1, column 1]

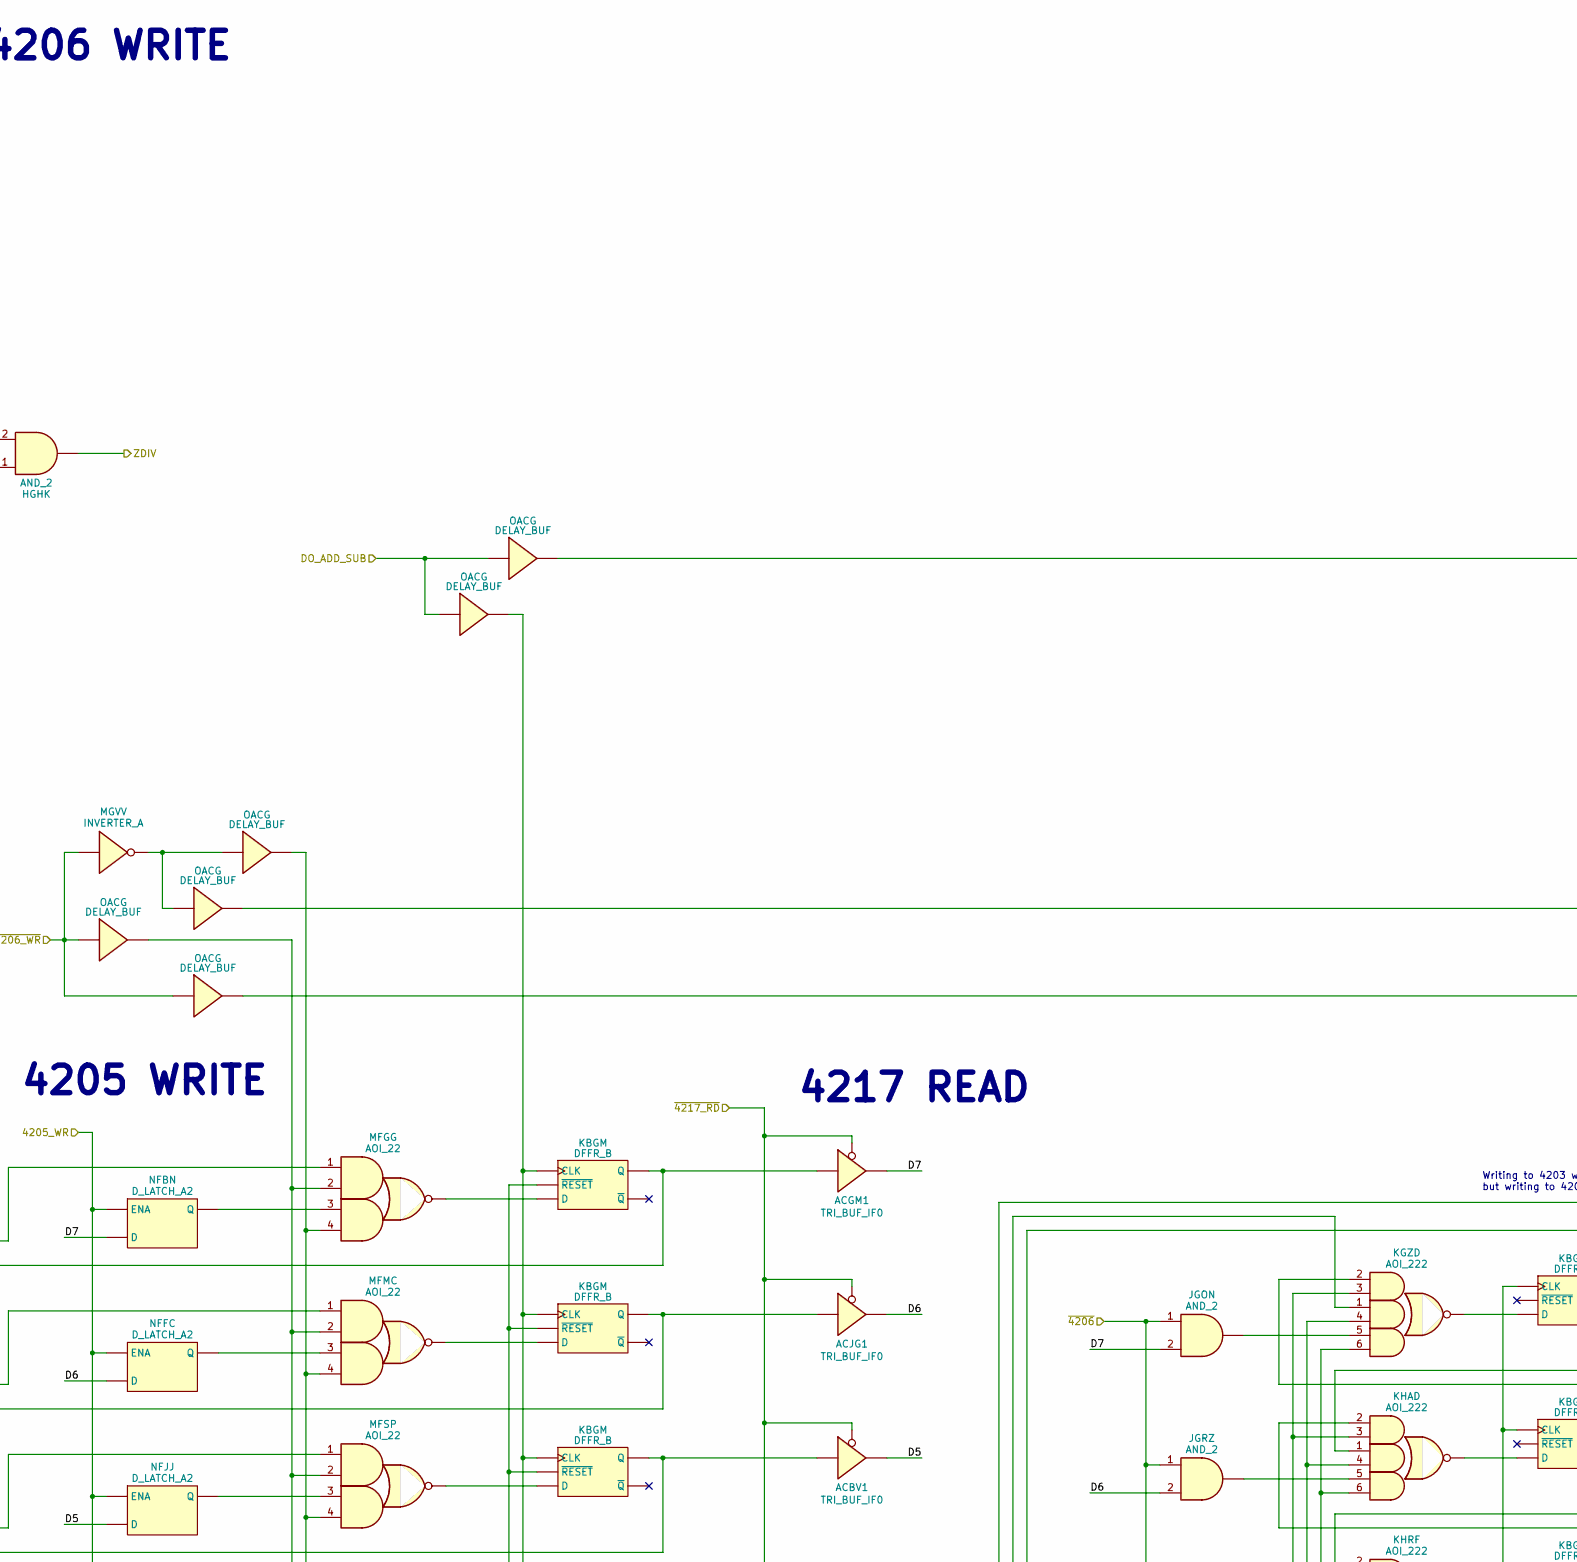
[picture p90: schematic productremainder.kicad_sch, part in row 1, column 2]

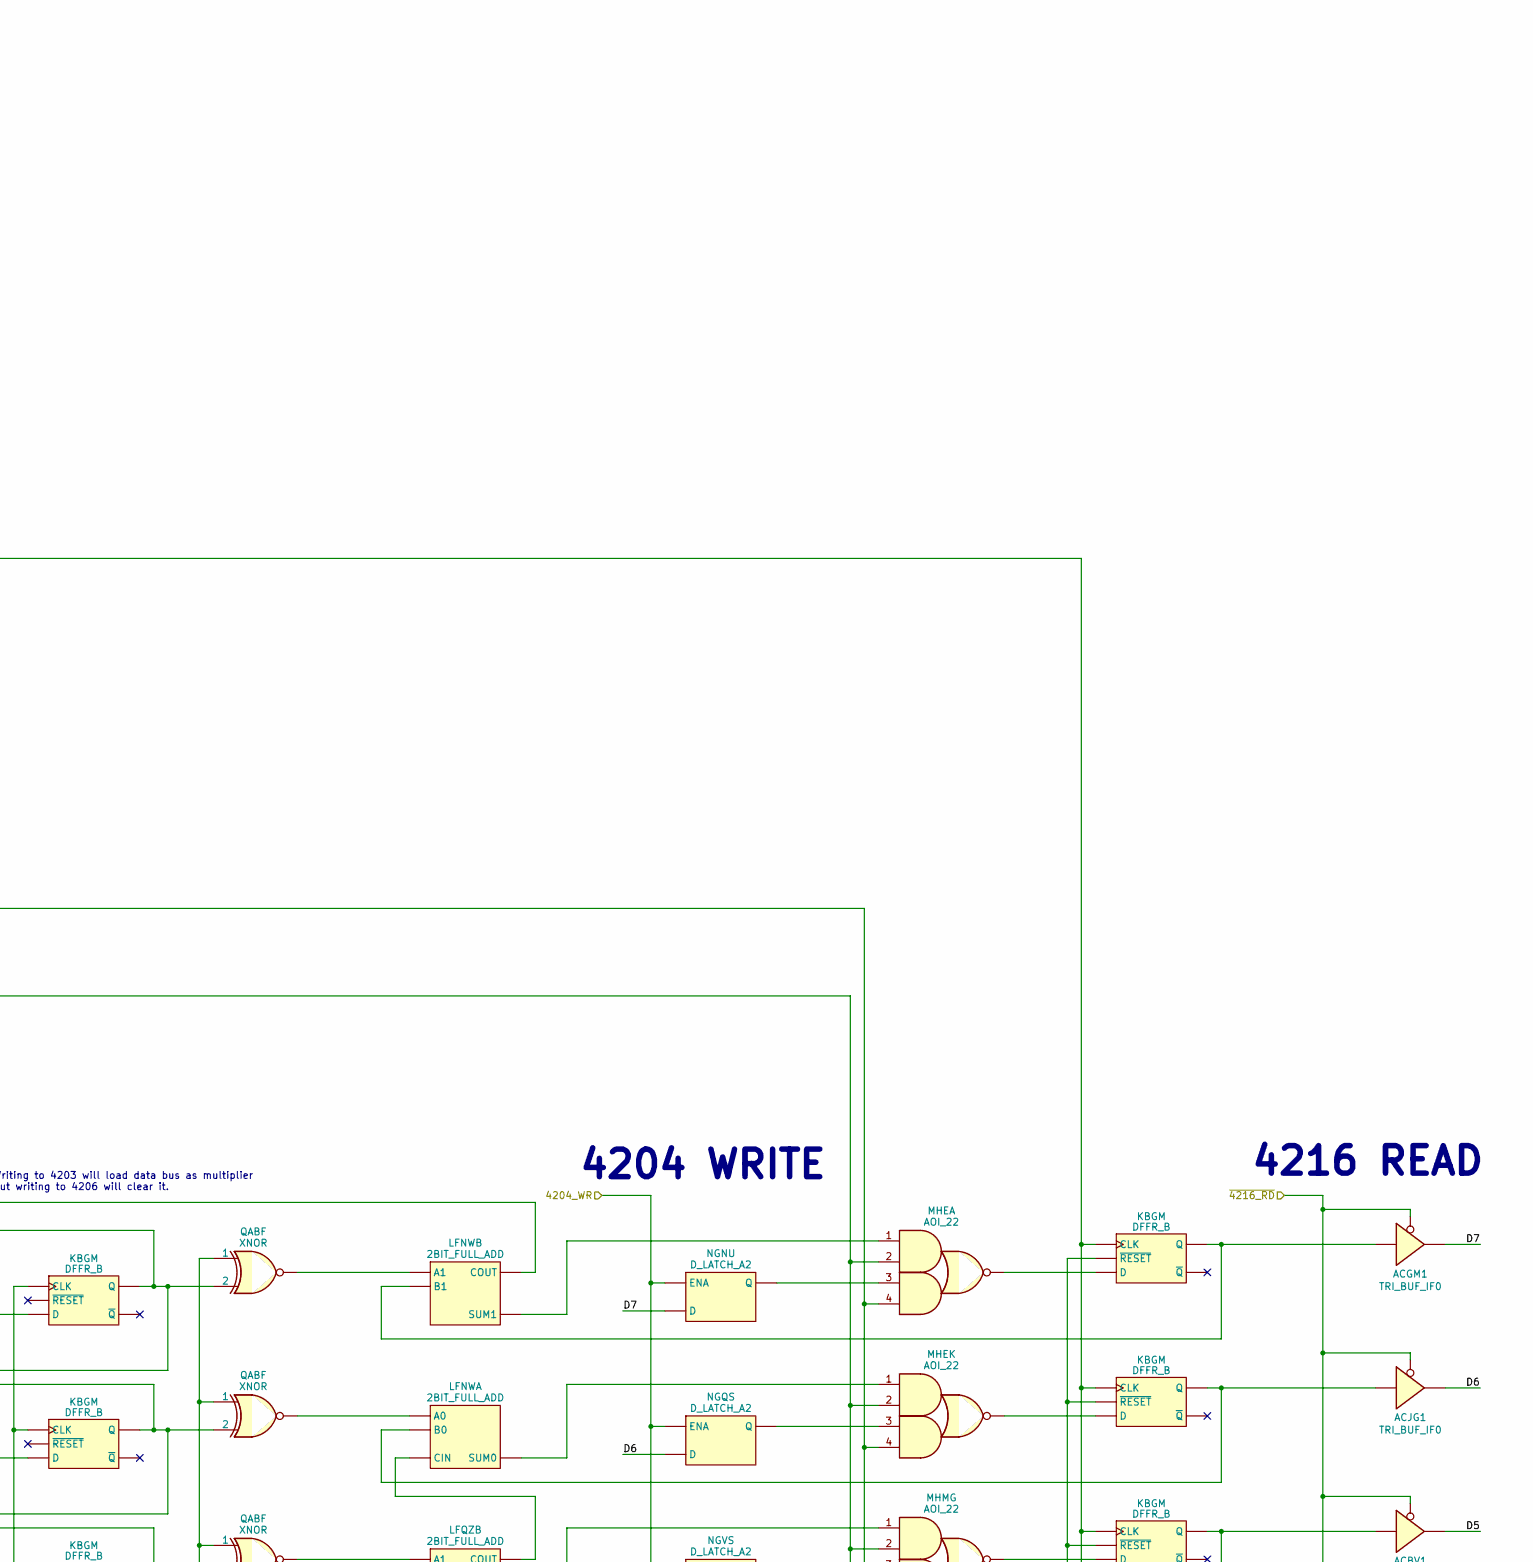
[picture p91: schematic productremainder.kicad_sch, part in row 1, column 3]

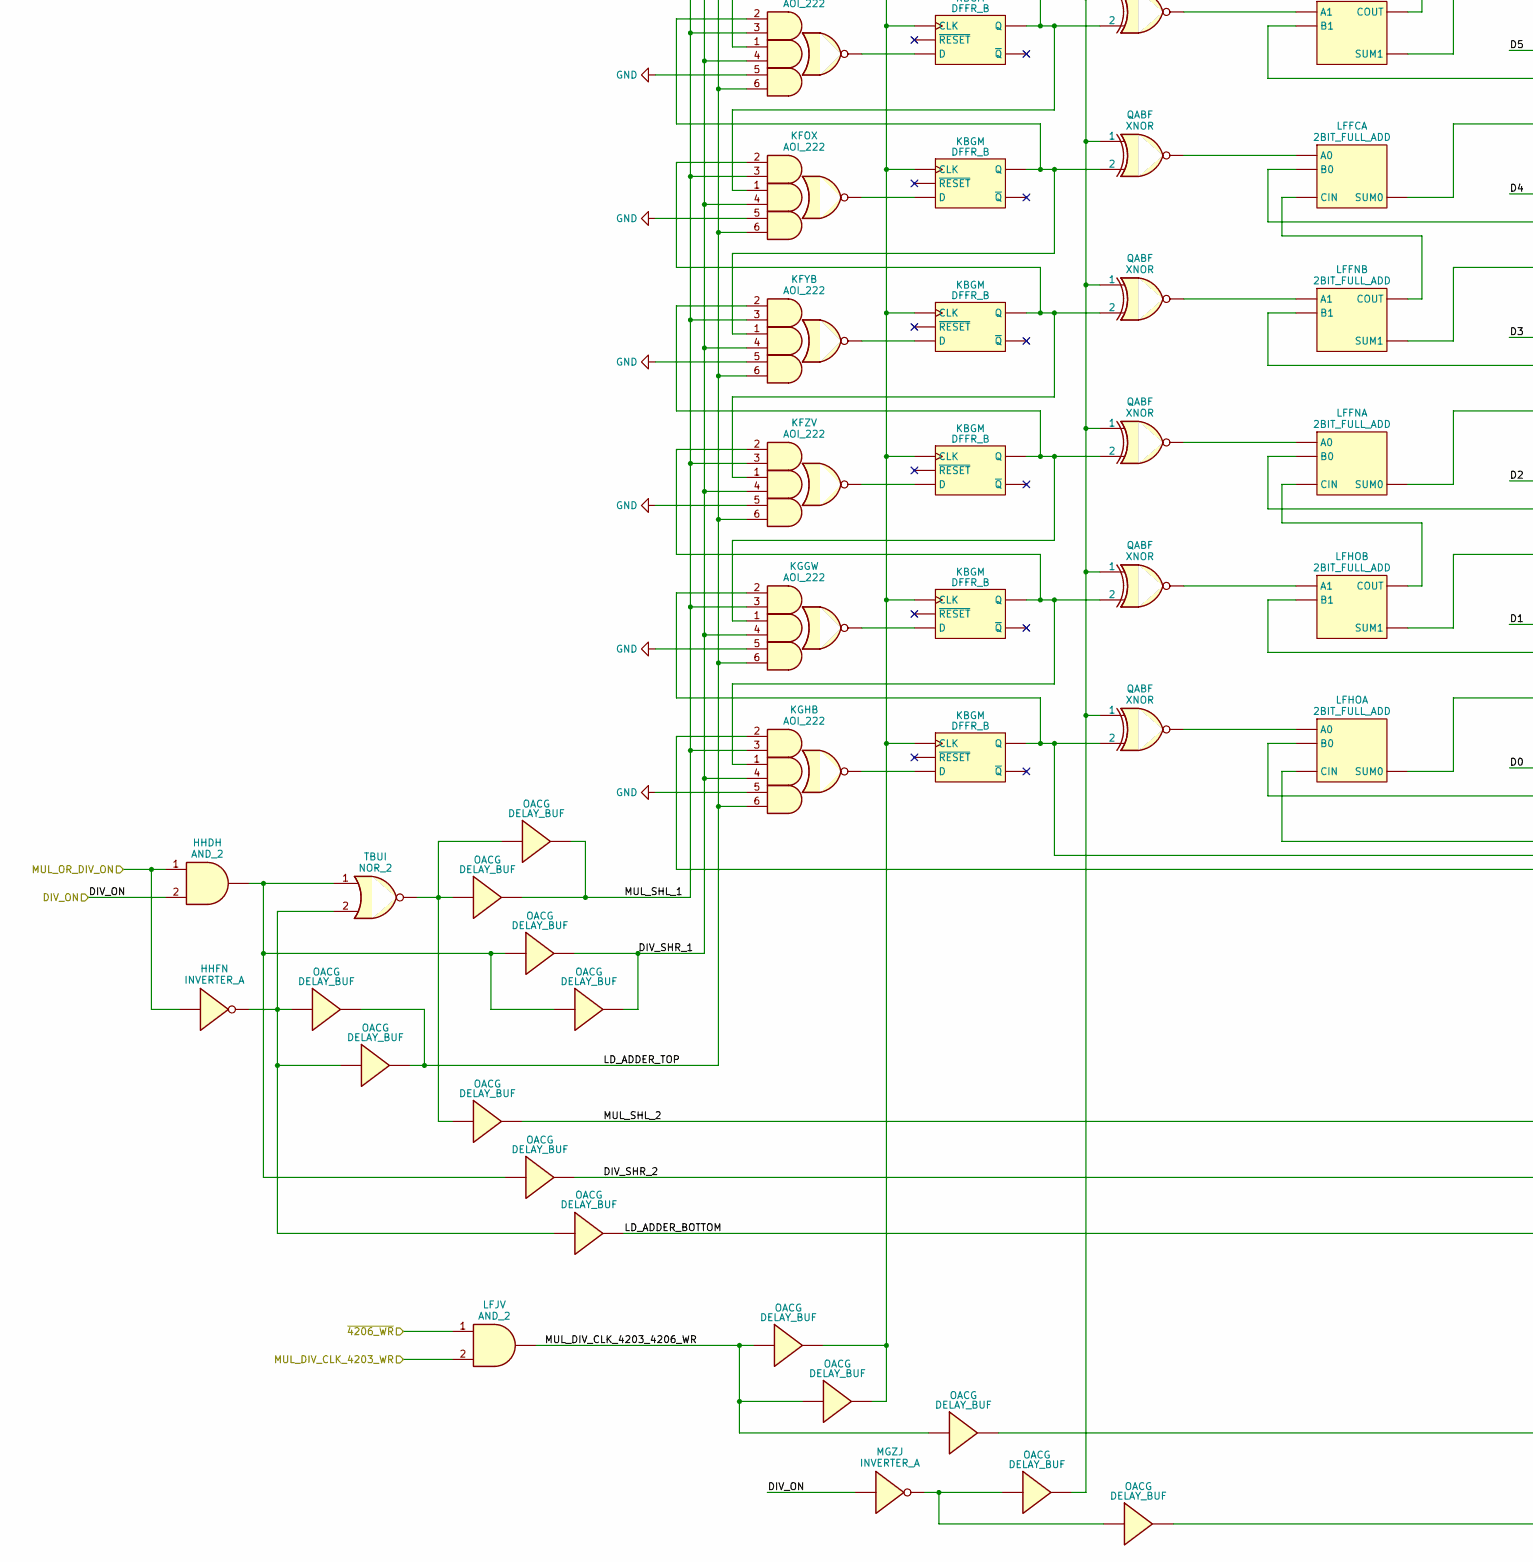
[picture p92: schematic productremainder.kicad_sch, part in row 2, column 1]

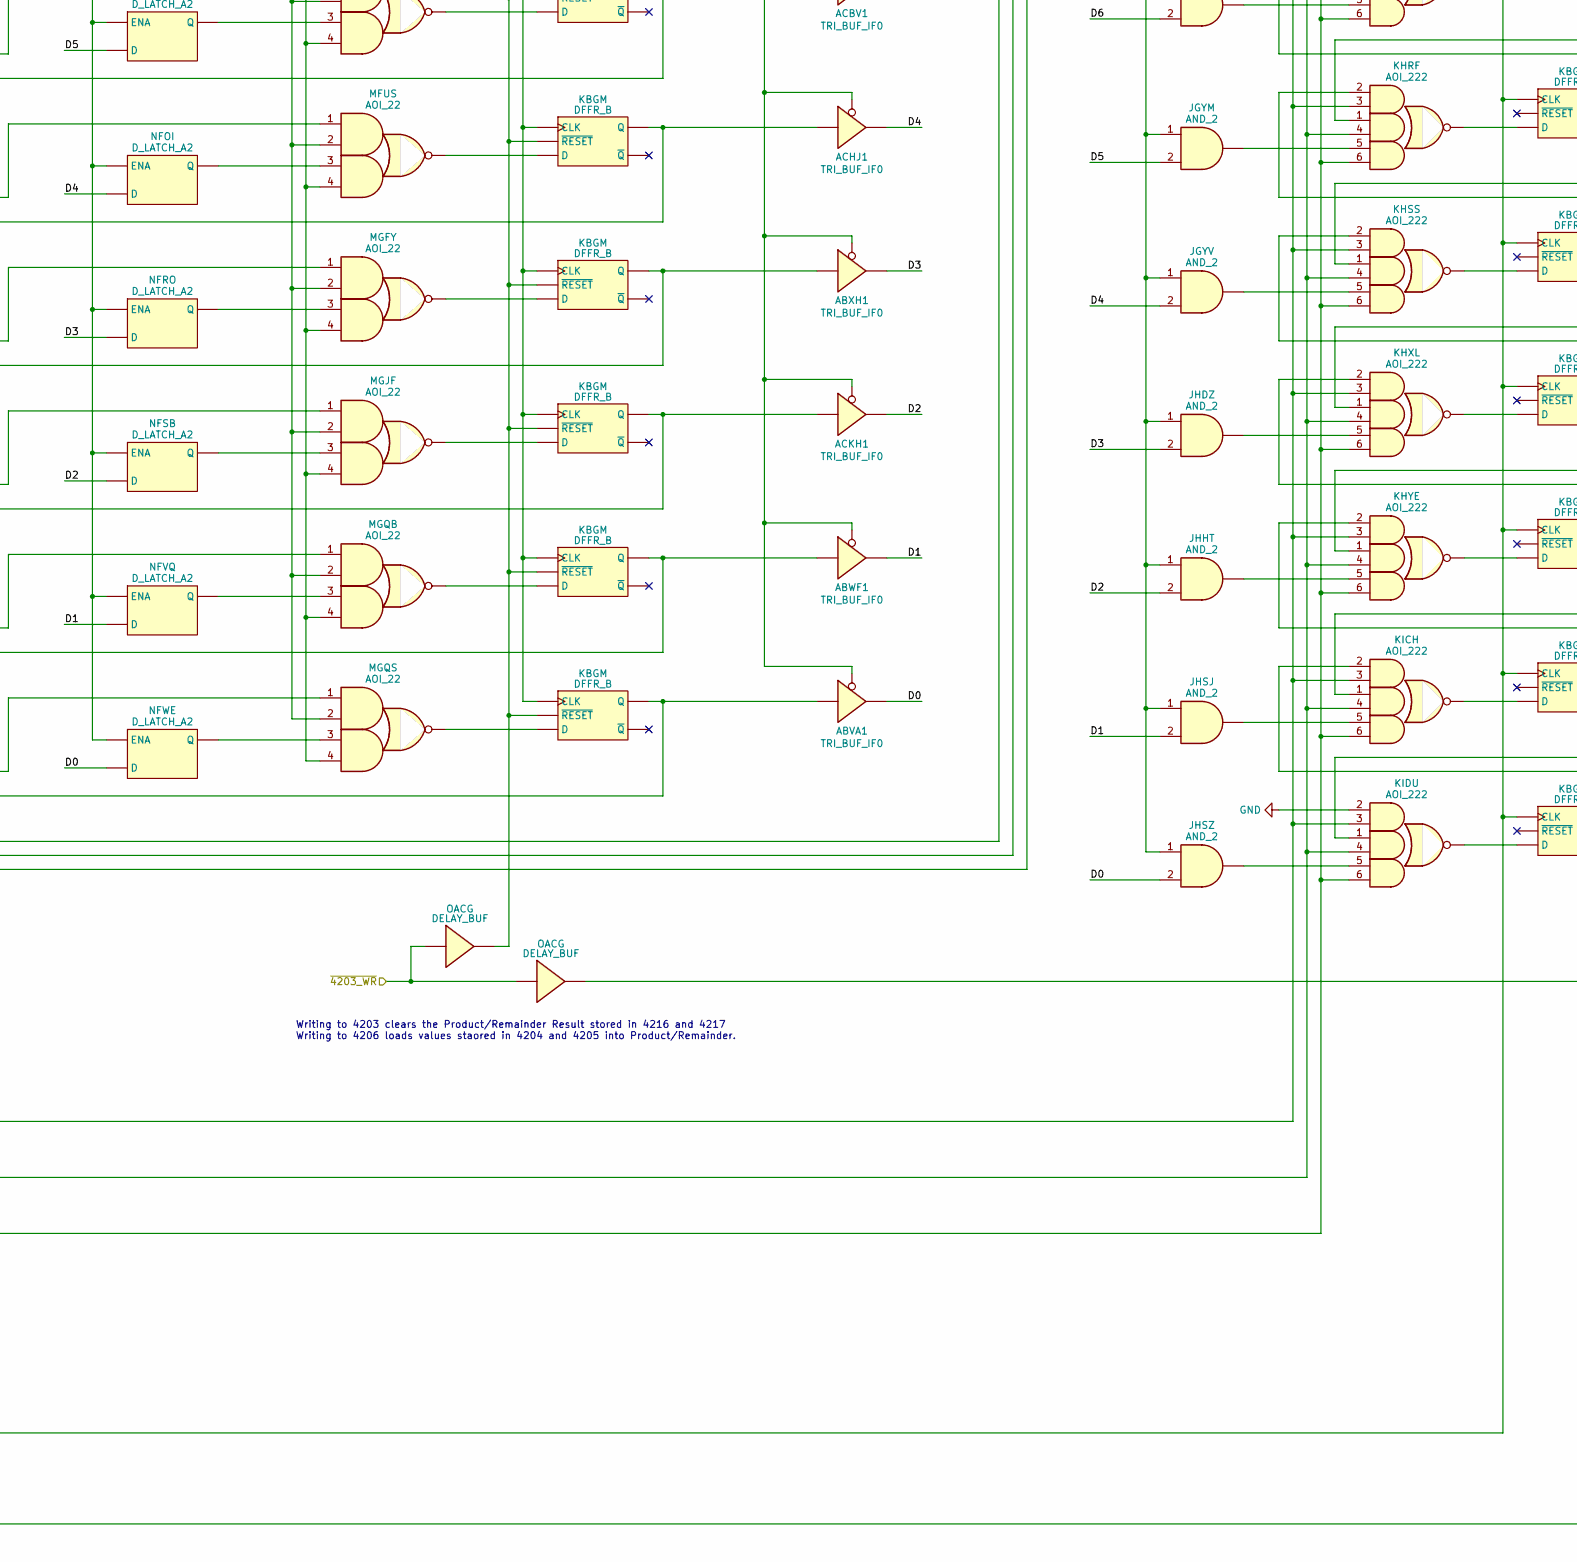
[picture p93: schematic productremainder.kicad_sch, part in row 2, column 2]

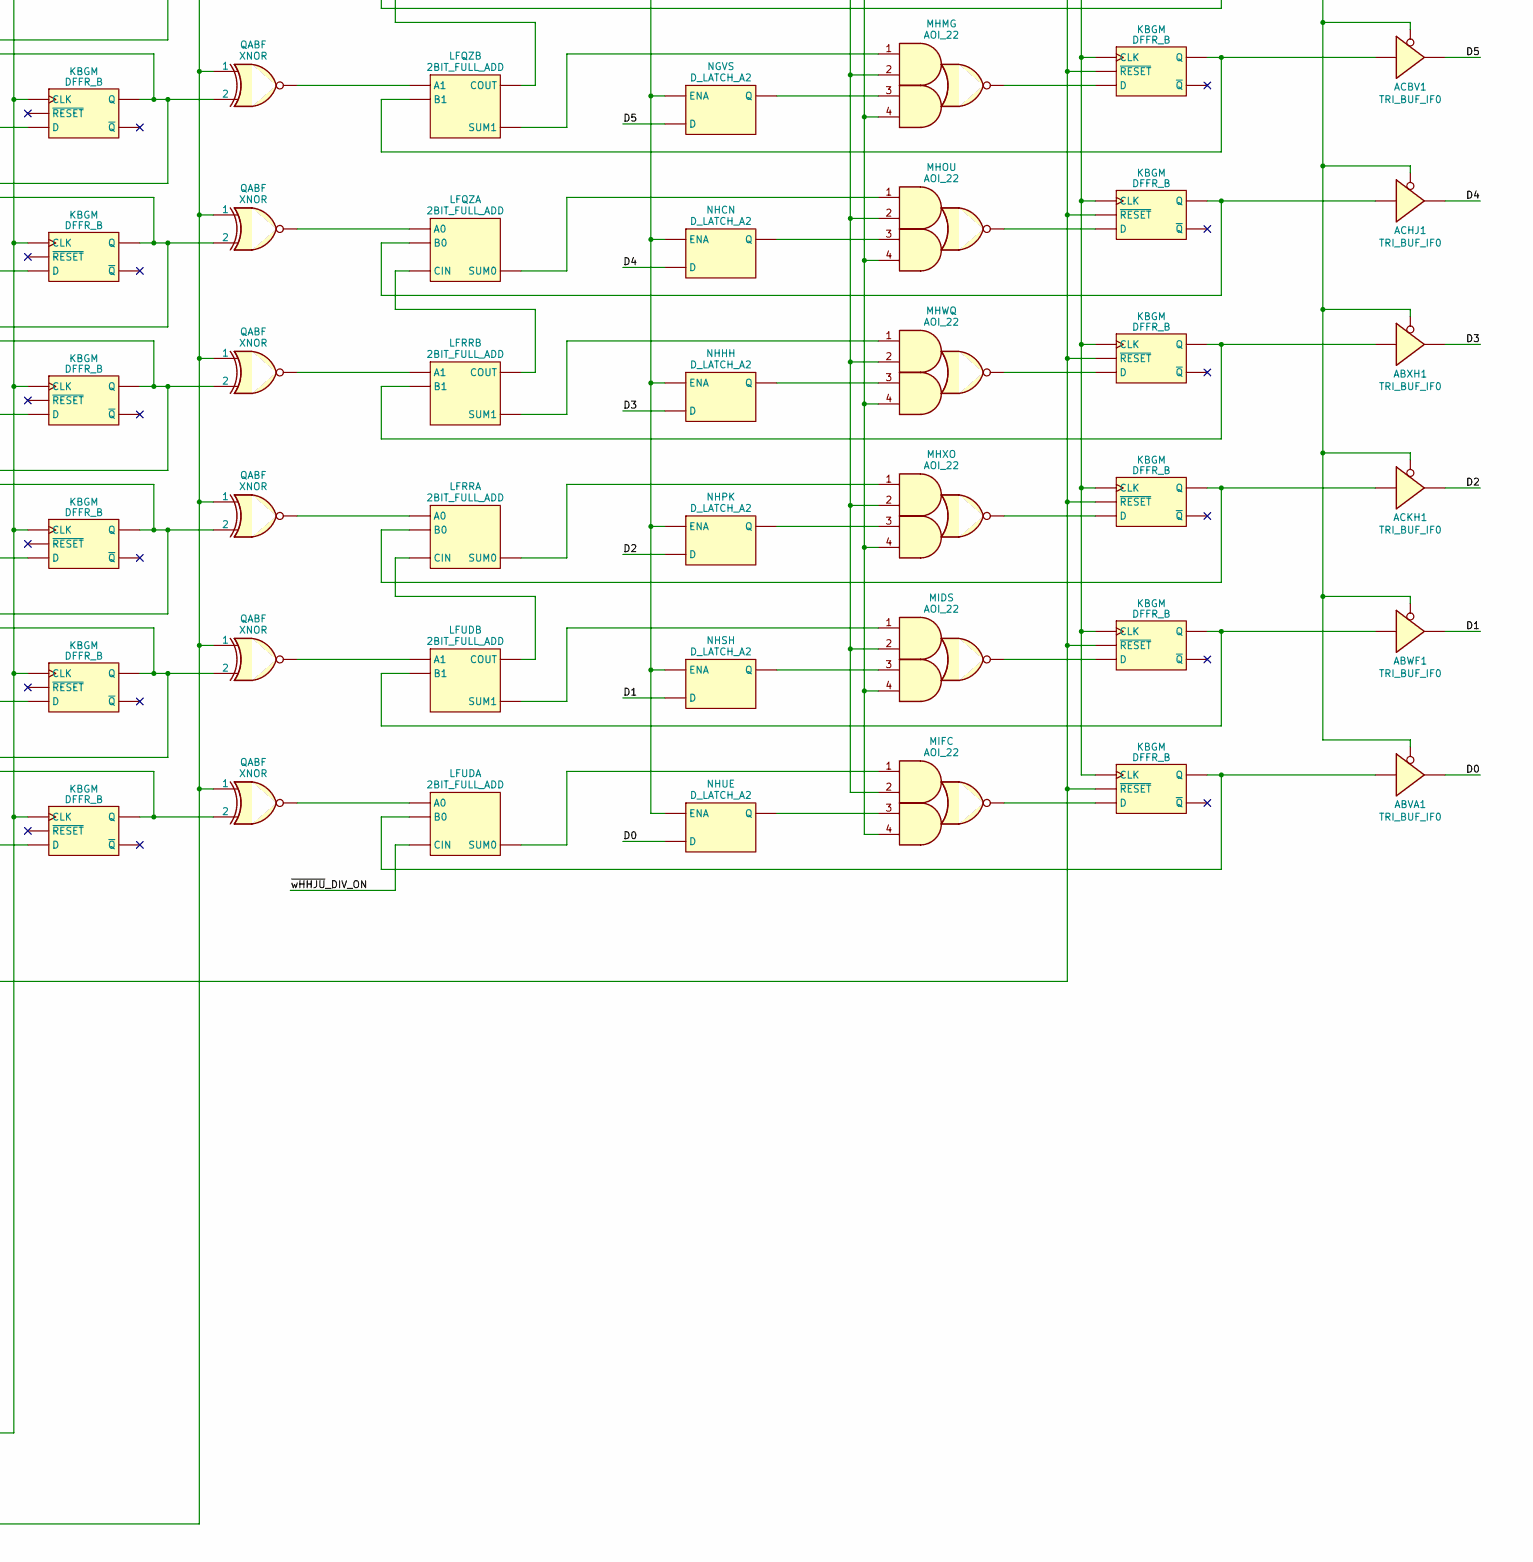
[picture p94: schematic productremainder.kicad_sch, part in row 2, column 3]

Parts:
ABVA1: TRI_BUF_IF0
ABWF1: TRI_BUF_IF0
ABXH1: TRI_BUF_IF0
ACBV1: TRI_BUF_IF0
ACGM1: TRI_BUF_IF0
ACHJ1: TRI_BUF_IF0
ACJG1: TRI_BUF_IF0
ACKH1: TRI_BUF_IF0
HFJQ: AND_2
HFPC: AND_2
HFSC: AND_2
HFYF: AND_2
HGDM: AND_2
HGFS: AND_2
HGHK: AND_2
HHDH: AND_2
HHFN: INVERTER_A
JFCT: AOI_222
JFDF: AOI_222
JFHM: AOI_222
JFKA: AOI_222
JFLO: AOI_222
JFQD: AOI_222
JFRL: AOI_222
JFRP: AOI_222
JGON: AND_2
JGRZ: AND_2
JGYM: AND_2
JGYV: AND_2
JHDZ: AND_2
JHHT: AND_2
JHSJ: AND_2
JHSZ: AND_2
KBGM: DFFR_B
KFCL: AND_2
KFCQ: AOI_222
KFMZ: AOI_222
KFOX: AOI_222
KFYB: AOI_222
KFZV: AOI_222
KGGW: AOI_222
KGHB: AOI_222
KGZD: AOI_222
KHAD: AOI_222
KHRF: AOI_222
KHSS: AOI_222
KHXL: AOI_222
KHYE: AOI_222
KICH: AOI_222
KIDU: AOI_222
LFDU: 2BIT_FULL_ADD
LFFC: 2BIT_FULL_ADD
LFFN: 2BIT_FULL_ADD
LFHO: 2BIT_FULL_ADD
LFJV: AND_2
LFNW: 2BIT_FULL_ADD
LFQZ: 2BIT_FULL_ADD
LFRR: 2BIT_FULL_ADD
LFUD: 2BIT_FULL_ADD
MFGG: AOI_22
MFMC: AOI_22
MFSP: AOI_22
MFUS: AOI_22
MGFY: AOI_22
MGJF: AOI_22
MGQB: AOI_22
MGQS: AOI_22
MGVV: INVERTER_A
MGZJ: INVERTER_A
MHEA: AOI_22
MHEK: AOI_22
MHMG: AOI_22
MHOU: AOI_22
MHWQ: AOI_22
MHXO: AOI_22
MIDS: AOI_22
MIFC: AOI_22
NFBN: D_LATCH_A2
NFFC: D_LATCH_A2
NFJJ: D_LATCH_A2
NFOI: D_LATCH_A2
NFRO: D_LATCH_A2
NFSB: D_LATCH_A2
NFVQ: D_LATCH_A2
NFWE: D_LATCH_A2
NGNU: D_LATCH_A2
NGQS: D_LATCH_A2
NGVS: D_LATCH_A2
NHCN: D_LATCH_A2
NHHH: D_LATCH_A2
NHPK: D_LATCH_A2
NHSH: D_LATCH_A2
NHUE: D_LATCH_A2
OACG: DELAY_BUF
QABF: XNOR
TBUI: NOR_2

Connections:
4204_WR: NGNU.1 (~ENA), NGNU.3 (ENA), NGQS.1 (~ENA), NGQS.3 (ENA), NGVS.1 (~ENA), NGVS.3 (ENA), NHCN.1 (~ENA), NHCN.3 (ENA), NHHH.1 (~ENA), NHHH.3 (ENA), NHPK.1 (~ENA), NHPK.3 (ENA), NHSH.1 (~ENA), NHSH.3 (ENA), NHUE.1 (~ENA), NHUE.3 (ENA)
4205_WR: NFBN.1 (~ENA), NFBN.3 (ENA), NFFC.1 (~ENA), NFFC.3 (ENA), NFJJ.1 (~ENA), NFJJ.3 (ENA), NFOI.1 (~ENA), NFOI.3 (ENA), NFRO.1 (~ENA), NFRO.3 (ENA), NFSB.1 (~ENA), NFSB.3 (ENA), NFVQ.1 (~ENA), NFVQ.3 (ENA), NFWE.1 (~ENA), NFWE.3 (ENA)
D0: ABVA1.4, JHSZ.2, KFCL.2, NFWE.2 (D), NHUE.2 (D)
D1: ABWF1.4, JFDF.5, JHSJ.2, NFVQ.2 (D), NHSH.2 (D)
D2: ACKH1.4, JFHM.5, JHHT.2, NFSB.2 (D), NHPK.2 (D)
D3: ABXH1.4, JFKA.5, JHDZ.2, NFRO.2 (D), NHHH.2 (D)
D4: ACHJ1.4, JFLO.5, JGYV.2, NFOI.2 (D), NHCN.2 (D)
D5: ACBV1.4, JFQD.5, JGYM.2, NFJJ.2 (D), NGVS.2 (D)
D6: ACJG1.4, JFRL.5, JGRZ.2, NFFC.2 (D), NGQS.2 (D)
D7: ACGM1.4, JFRP.5, JGON.2, NFBN.2 (D), NGNU.2 (D)
DIV_ON: HHDH.2, MGZJ.1
DIV_SHR_1: JFCT.4, JFDF.4, JFHM.4, JFKA.4, JFLO.4, JFQD.4, JFRL.4, JFRP.4, KFCQ.4, KFMZ.4, KFOX.4, KFYB.4, KFZV.4, KGGW.4, KGHB.4, OACG.2
DIV_SHR_2: KGZD.4, KHAD.4, KHRF.4, KHSS.4, KHXL.4, KHYE.4, KICH.4, KIDU.4, OACG.2
DO_ADD_SUB: OACG.1
GND: JFRP.1, KFCQ.5, KFMZ.5, KFOX.5, KFYB.5, KFZV.5, KGGW.5, KGHB.5, KIDU.2
LD_ADDER_BOTTOM: KGZD.6, KHAD.6, KHRF.6, KHSS.6, KHXL.6, KHYE.6, KICH.6, KIDU.6, OACG.2
LD_ADDER_TOP: JFCT.6, JFDF.6, JFHM.6, JFKA.6, JFLO.6, JFQD.6, JFRL.6, JFRP.6, KFCQ.6, KFMZ.6, KFOX.6, KFYB.6, KFZV.6, KGGW.6, KGHB.6, OACG.2
MUL_DIV_CLK_4203_4206_WR: LFJV.3, OACG.1
MUL_DIV_CLK_4203_WR: LFJV.2
MUL_OR_DIV_ON: HHDH.1, HHFN.1
MUL_SHL_1: JFCT.3, JFDF.3, JFHM.3, JFKA.3, JFLO.3, JFQD.3, JFRL.3, JFRP.3, KFCQ.3, KFMZ.3, KFOX.3, KFYB.3, KFZV.3, KGGW.3, KGHB.3, OACG.2
MUL_SHL_2: KGZD.3, KHAD.3, KHRF.3, KHSS.3, KHXL.3, KHYE.3, KICH.3, KIDU.3, OACG.2
unnamed: ABVA1.1 (IN), ABVA1.3 (IN), KBGM.7 (Q), LFHO.9 (B0), LFUD.9 (B0)
unnamed: ABWF1.1 (IN), ABWF1.3 (IN), KBGM.7 (Q), LFHO.23 (B1), LFUD.23 (B1)
unnamed: ABXH1.1 (IN), ABXH1.3 (IN), KBGM.7 (Q), LFFN.23 (B1), LFRR.23 (B1)
unnamed: ACBV1.1 (IN), ACBV1.3 (IN), KBGM.7 (Q), LFFC.23 (B1), LFQZ.23 (B1)
unnamed: ACGM1.1 (IN), ACGM1.3 (IN), KBGM.7 (Q), LFDU.23 (B1), LFNW.23 (B1)
unnamed: ACHJ1.1 (IN), ACHJ1.3 (IN), KBGM.7 (Q), LFFC.9 (B0), LFQZ.9 (B0)
unnamed: ACJG1.1 (IN), ACJG1.3 (IN), KBGM.7 (Q), LFDU.9 (B0), LFNW.9 (B0)
unnamed: ACKH1.1 (IN), ACKH1.3 (IN), KBGM.7 (Q), LFFN.9 (B0), LFRR.9 (B0)
unnamed: HFJQ.1, KBGM.6 (~Q)
unnamed: HFJQ.2, KBGM.6 (~Q)
unnamed: HFJQ.3, HFPC.1
unnamed: HFPC.2, HFSC.3
unnamed: HFPC.3, HFYF.1
unnamed: HFSC.1, KBGM.6 (~Q)
unnamed: HFSC.2, KBGM.6 (~Q)
unnamed: HFYF.2, HGDM.3
unnamed: HFYF.3, HGHK.2
unnamed: HGDM.1, HGFS.3
unnamed: HGDM.2, KBGM.6 (~Q)
unnamed: HGFS.1, KBGM.6 (~Q)
unnamed: HGFS.2, KBGM.6 (~Q)
unnamed: HGHK.1, LFDU.28 (COUT)
unnamed: HHDH.3, OACG.1, TBUI.1
unnamed: HHFN.2, OACG.1, TBUI.2
unnamed: JFCT.1, JFHM.2, KBGM.7 (Q)
unnamed: JFCT.2, KBGM.7 (Q), KFMZ.1, QABF.3 (2)
unnamed: JFCT.3, KBGM.2 (D)
unnamed: JFCT.5, KFCL.3
unnamed: JFDF.1, JFKA.2, KBGM.7 (Q)
unnamed: JFDF.2, KBGM.7 (Q), KFCQ.1, QABF.3 (2)
unnamed: JFDF.3, KBGM.2 (D)
unnamed: JFHM.1, JFLO.2, KBGM.7 (Q)
unnamed: JFHM.3, KBGM.2 (D)
unnamed: JFKA.1, JFQD.2, KBGM.7 (Q)
unnamed: JFKA.3, KBGM.2 (D)
unnamed: JFLO.1, JFRL.2, KBGM.7 (Q)
unnamed: JFLO.3, KBGM.2 (D)
unnamed: JFQD.1, JFRP.2, KBGM.7 (Q)
unnamed: JFQD.3, KBGM.2 (D)
unnamed: JFRL.1, KBGM.7 (Q)
unnamed: JFRL.3, KBGM.2 (D)
unnamed: JFRP.3, KBGM.2 (D)
unnamed: JGON.3, KGZD.5
unnamed: JGRZ.3, KHAD.5
unnamed: JGYM.3, KHRF.5
unnamed: JGYV.3, KHSS.5
unnamed: JHDZ.3, KHXL.5
unnamed: JHHT.3, KHYE.5
unnamed: JHSJ.3, KICH.5
unnamed: JHSZ.3, KIDU.5
unnamed: KBGM.1 (~RESET), KBGM.5 (~RESET), OACG.2
unnamed: KBGM.2 (D), KFCQ.3, KFMZ.3, KFOX.3, KFYB.3, KFZV.3, KGGW.3, KGHB.3, KGZD.3, KHAD.3, KHRF.3, KHSS.3, KHXL.3, KHYE.3, KICH.3, KIDU.3, MFGG.3, MFMC.3, MFSP.3, MFUS.3, MGFY.3, MGJF.3, MGQB.3, MGQS.3, MHEA.3, MHEK.3, MHMG.3, MHOU.3, MHWQ.3, MHXO.3, MIDS.3, MIFC.3
unnamed: KBGM.3 (CLK), KBGM.4 (~CLK), OACG.2
unnamed: KBGM.7 (Q), KFCQ.2, KFMZ.2, KFOX.1, KFOX.2, KFYB.1, KFYB.2, KFZV.1, KFZV.2, KGGW.1, KGGW.2, KGHB.1, KGHB.2, KGZD.1, KGZD.2, KHAD.1, KHAD.2, KHRF.1, KHRF.2, KHSS.1, KHSS.2, KHXL.1, KHXL.2, KHYE.1, KHYE.2, KICH.1, KICH.2, KIDU.1, QABF.3 (2)
unnamed: LFDU.2 (CIN), LFFC.28 (COUT)
unnamed: LFDU.4 (SUM0), MFMC.1
unnamed: LFDU.13 (A0), QABF.1
unnamed: LFDU.17 (SUM1), MFGG.1
unnamed: LFDU.24 (A1), QABF.1
unnamed: LFFC.2 (CIN), LFFN.28 (COUT)
unnamed: LFFC.4 (SUM0), MFUS.1
unnamed: LFFC.13 (A0), QABF.1
unnamed: LFFC.17 (SUM1), MFSP.1
unnamed: LFFC.24 (A1), QABF.1
unnamed: LFFN.2 (CIN), LFHO.28 (COUT)
unnamed: LFFN.4 (SUM0), MGJF.1
unnamed: LFFN.13 (A0), QABF.1
unnamed: LFFN.17 (SUM1), MGFY.1
unnamed: LFFN.24 (A1), QABF.1
unnamed: LFHO.2 (CIN), LFNW.28 (COUT)
unnamed: LFHO.4 (SUM0), MGQS.1
unnamed: LFHO.13 (A0), QABF.1
unnamed: LFHO.17 (SUM1), MGQB.1
unnamed: LFHO.24 (A1), QABF.1
unnamed: LFNW.2 (CIN), LFQZ.28 (COUT)
unnamed: LFNW.4 (SUM0), MHEK.1
unnamed: LFNW.13 (A0), QABF.1
unnamed: LFNW.17 (SUM1), MHEA.1
unnamed: LFNW.24 (A1), QABF.1
unnamed: LFQZ.2 (CIN), LFRR.28 (COUT)
unnamed: LFQZ.4 (SUM0), MHOU.1
unnamed: LFQZ.13 (A0), QABF.1
unnamed: LFQZ.17 (SUM1), MHMG.1
unnamed: LFQZ.24 (A1), QABF.1
unnamed: LFRR.2 (CIN), LFUD.28 (COUT)
unnamed: LFRR.4 (SUM0), MHXO.1
unnamed: LFRR.13 (A0), QABF.1
unnamed: LFRR.17 (SUM1), MHWQ.1
unnamed: LFRR.24 (A1), QABF.1
unnamed: LFUD.4 (SUM0), MIFC.1
unnamed: LFUD.13 (A0), QABF.1
unnamed: LFUD.17 (SUM1), MIDS.1
unnamed: LFUD.24 (A1), QABF.1
unnamed: MFGG.2, MFMC.2, MFSP.2, MFUS.2, MGFY.2, MGJF.2, MGQB.2, MGQS.2, OACG.2
unnamed: MFGG.3, NFBN.4 (Q)
unnamed: MFGG.4, MFMC.4, MFSP.4, MFUS.4, MGFY.4, MGJF.4, MGQB.4, MGQS.4, OACG.2
unnamed: MFMC.3, NFFC.4 (Q)
unnamed: MFSP.3, NFJJ.4 (Q)
unnamed: MFUS.3, NFOI.4 (Q)
unnamed: MGFY.3, NFRO.4 (Q)
unnamed: MGJF.3, NFSB.4 (Q)
unnamed: MGQB.3, NFVQ.4 (Q)
unnamed: MGQS.3, NFWE.4 (Q)
unnamed: MGVV.2, OACG.1
unnamed: MGZJ.2, OACG.1
unnamed: MHEA.2, MHEK.2, MHMG.2, MHOU.2, MHWQ.2, MHXO.2, MIDS.2, MIFC.2, OACG.2
unnamed: MHEA.3, NGNU.4 (Q)
unnamed: MHEA.4, MHEK.4, MHMG.4, MHOU.4, MHWQ.4, MHXO.4, MIDS.4, MIFC.4, OACG.2
unnamed: MHEK.3, NGQS.4 (Q)
unnamed: MHMG.3, NGVS.4 (Q)
unnamed: MHOU.3, NHCN.4 (Q)
unnamed: MHWQ.3, NHHH.4 (Q)
unnamed: MHXO.3, NHPK.4 (Q)
unnamed: MIDS.3, NHSH.4 (Q)
unnamed: MIFC.3, NHUE.4 (Q)
unnamed: OACG.1, TBUI.3
unnamed: OACG.2, QABF.2 (1)
ZDIV: HGHK.3
~4203_WR: OACG.1
~4203: KFCL.1
~4206_WR: LFJV.1, MGVV.1, OACG.1
~4206: JGON.1, JGRZ.1, JGYM.1, JGYV.1, JHDZ.1, JHHT.1, JHSJ.1, JHSZ.1
~4216_RD: ABVA1.2 (~ENA), ABWF1.2 (~ENA), ABXH1.2 (~ENA), ACBV1.2 (~ENA), ACGM1.2 (~ENA), ACHJ1.2 (~ENA), ACJG1.2 (~ENA), ACKH1.2 (~ENA)
~4217_RD: ABVA1.2 (~ENA), ABWF1.2 (~ENA), ABXH1.2 (~ENA), ACBV1.2 (~ENA), ACGM1.2 (~ENA), ACHJ1.2 (~ENA), ACJG1.2 (~ENA), ACKH1.2 (~ENA)
~wHHJU_DIV_ON: LFUD.2 (CIN)

Notes on the sheet:
4205 WRITE
Writing to 4203 will load data bus as multiplier but writing to 4206 will clear it.
4217 READ
4204 WRITE
4203 WRITE (MULTIPLIER) OR 4206 WRITE OR SHL/SHR
Writing to 4203 clears the Product/Remainder Result stored in 4216 and 4217 Writing to 4206 loads values staored in 4204 and 4205 into Product/Remainder.
4216 READ
