rgalland/SNES_S-CPU_Schematics/S-CPU_kicad/rw_decoding.kicad_sch

## KiCad design S-CPU_kicad/rw_decoding.kicad_sch (2024-12-24, an earlier design)

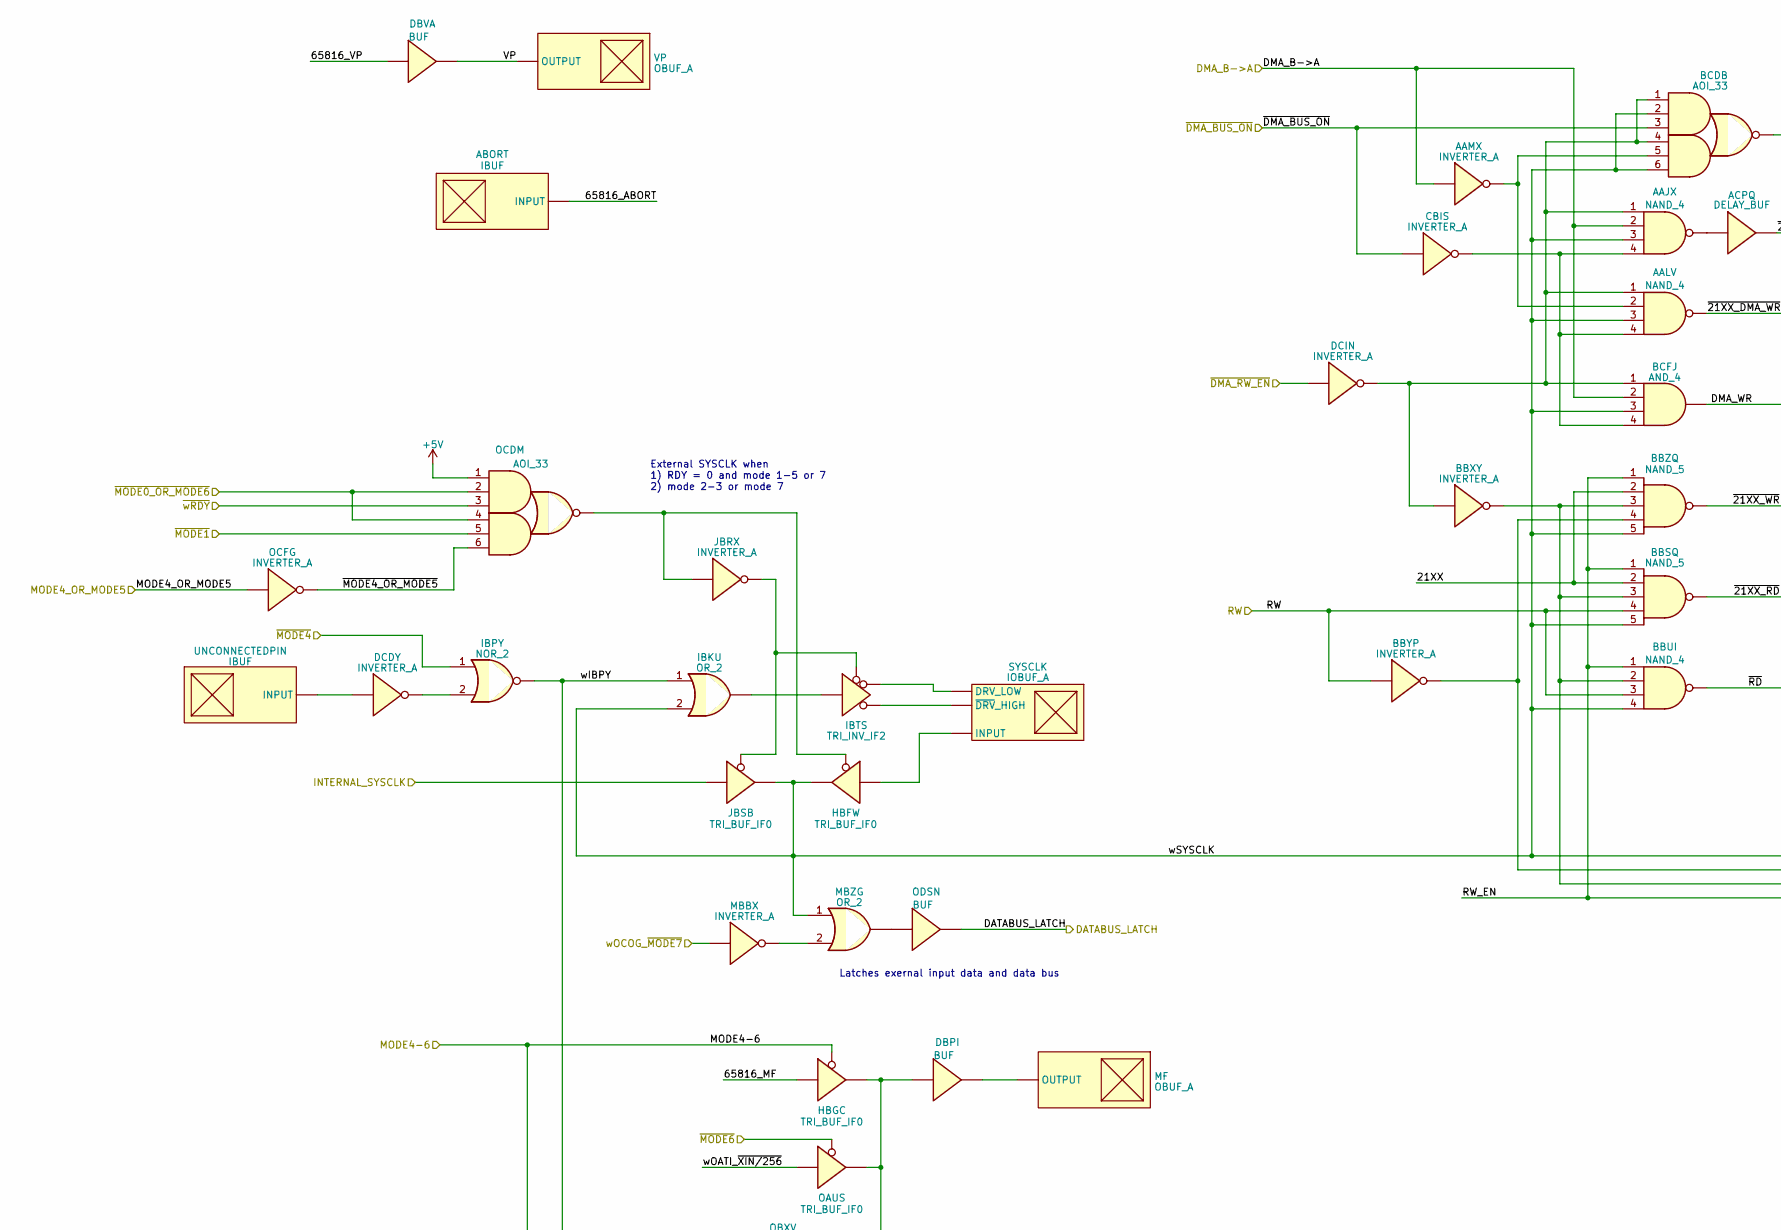
[picture p95: schematic rw_decoding.kicad_sch, part in row 1, column 1]

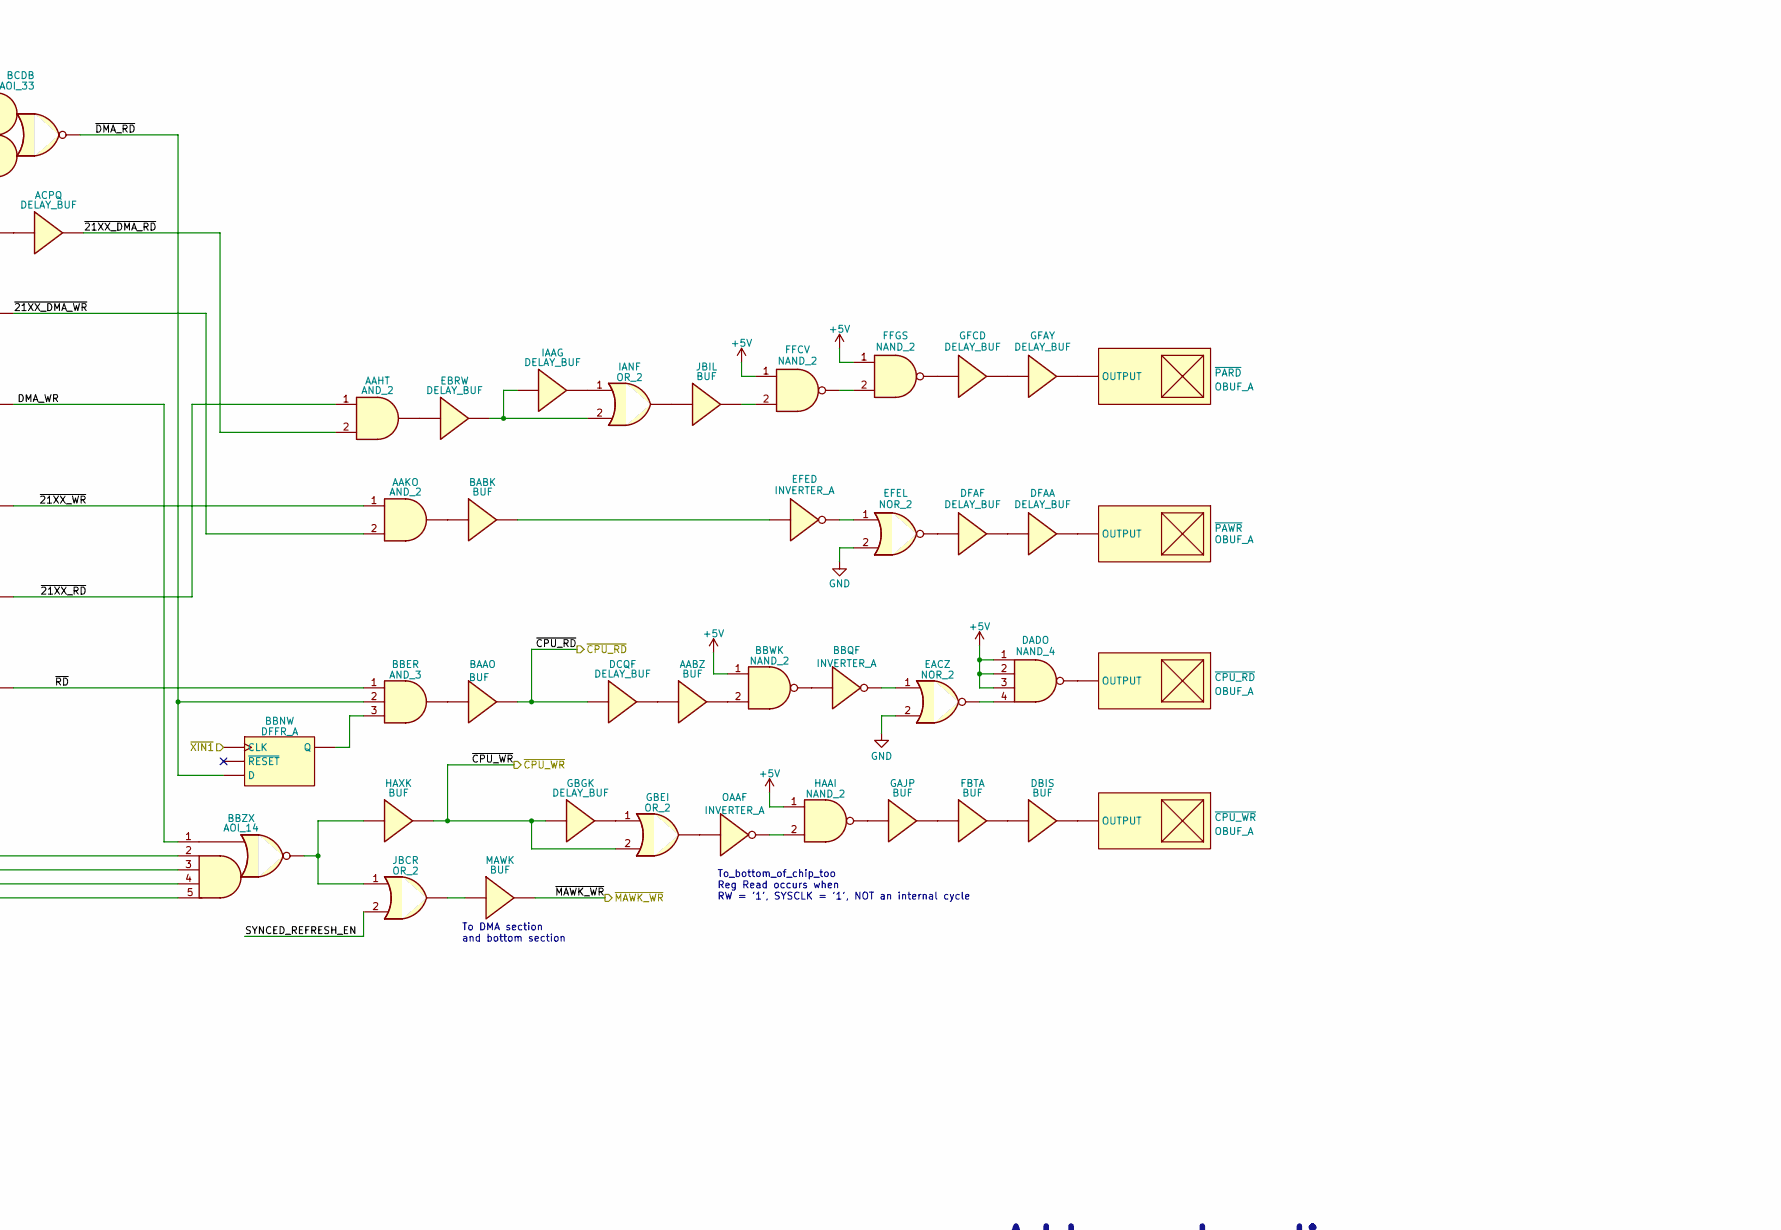
[picture p96: schematic rw_decoding.kicad_sch, part in row 1, column 2]

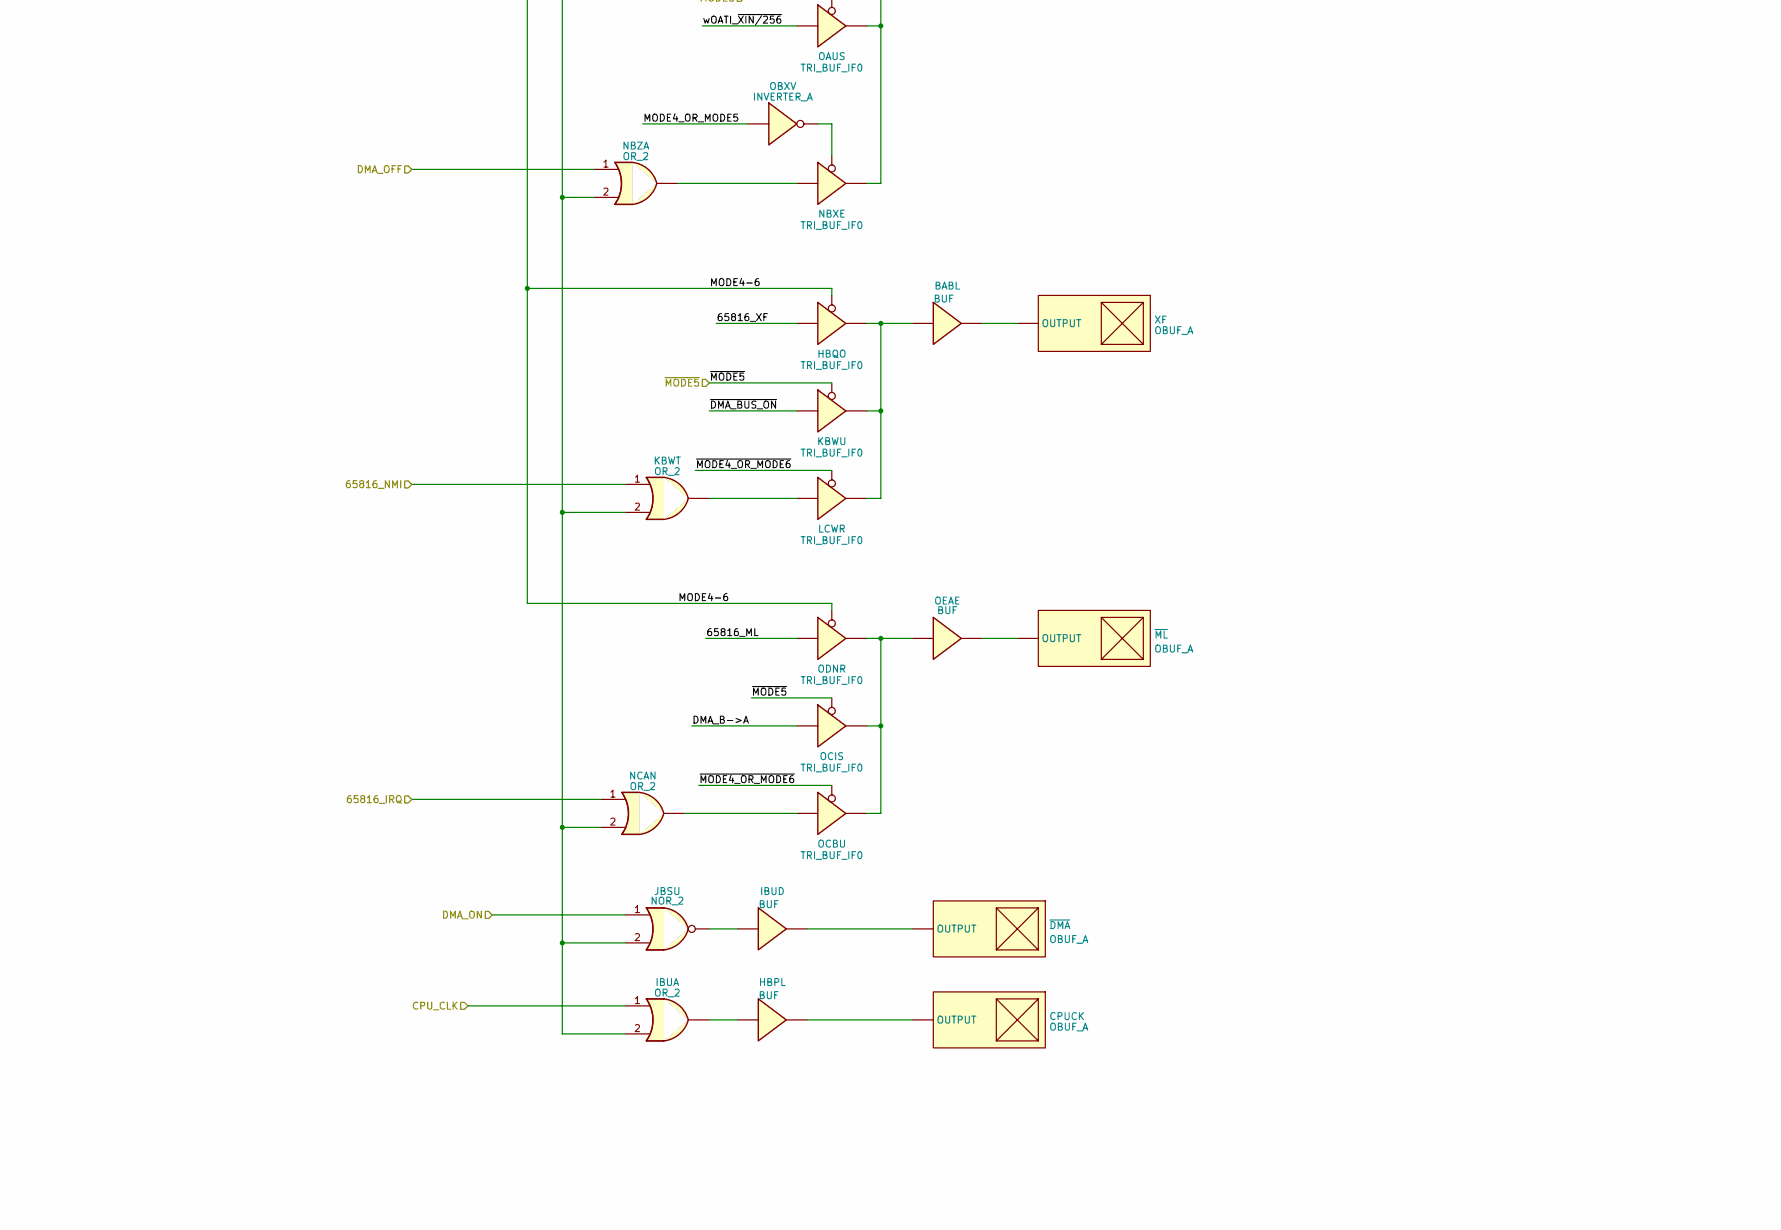
[picture p97: schematic rw_decoding.kicad_sch, part in row 2, column 1]

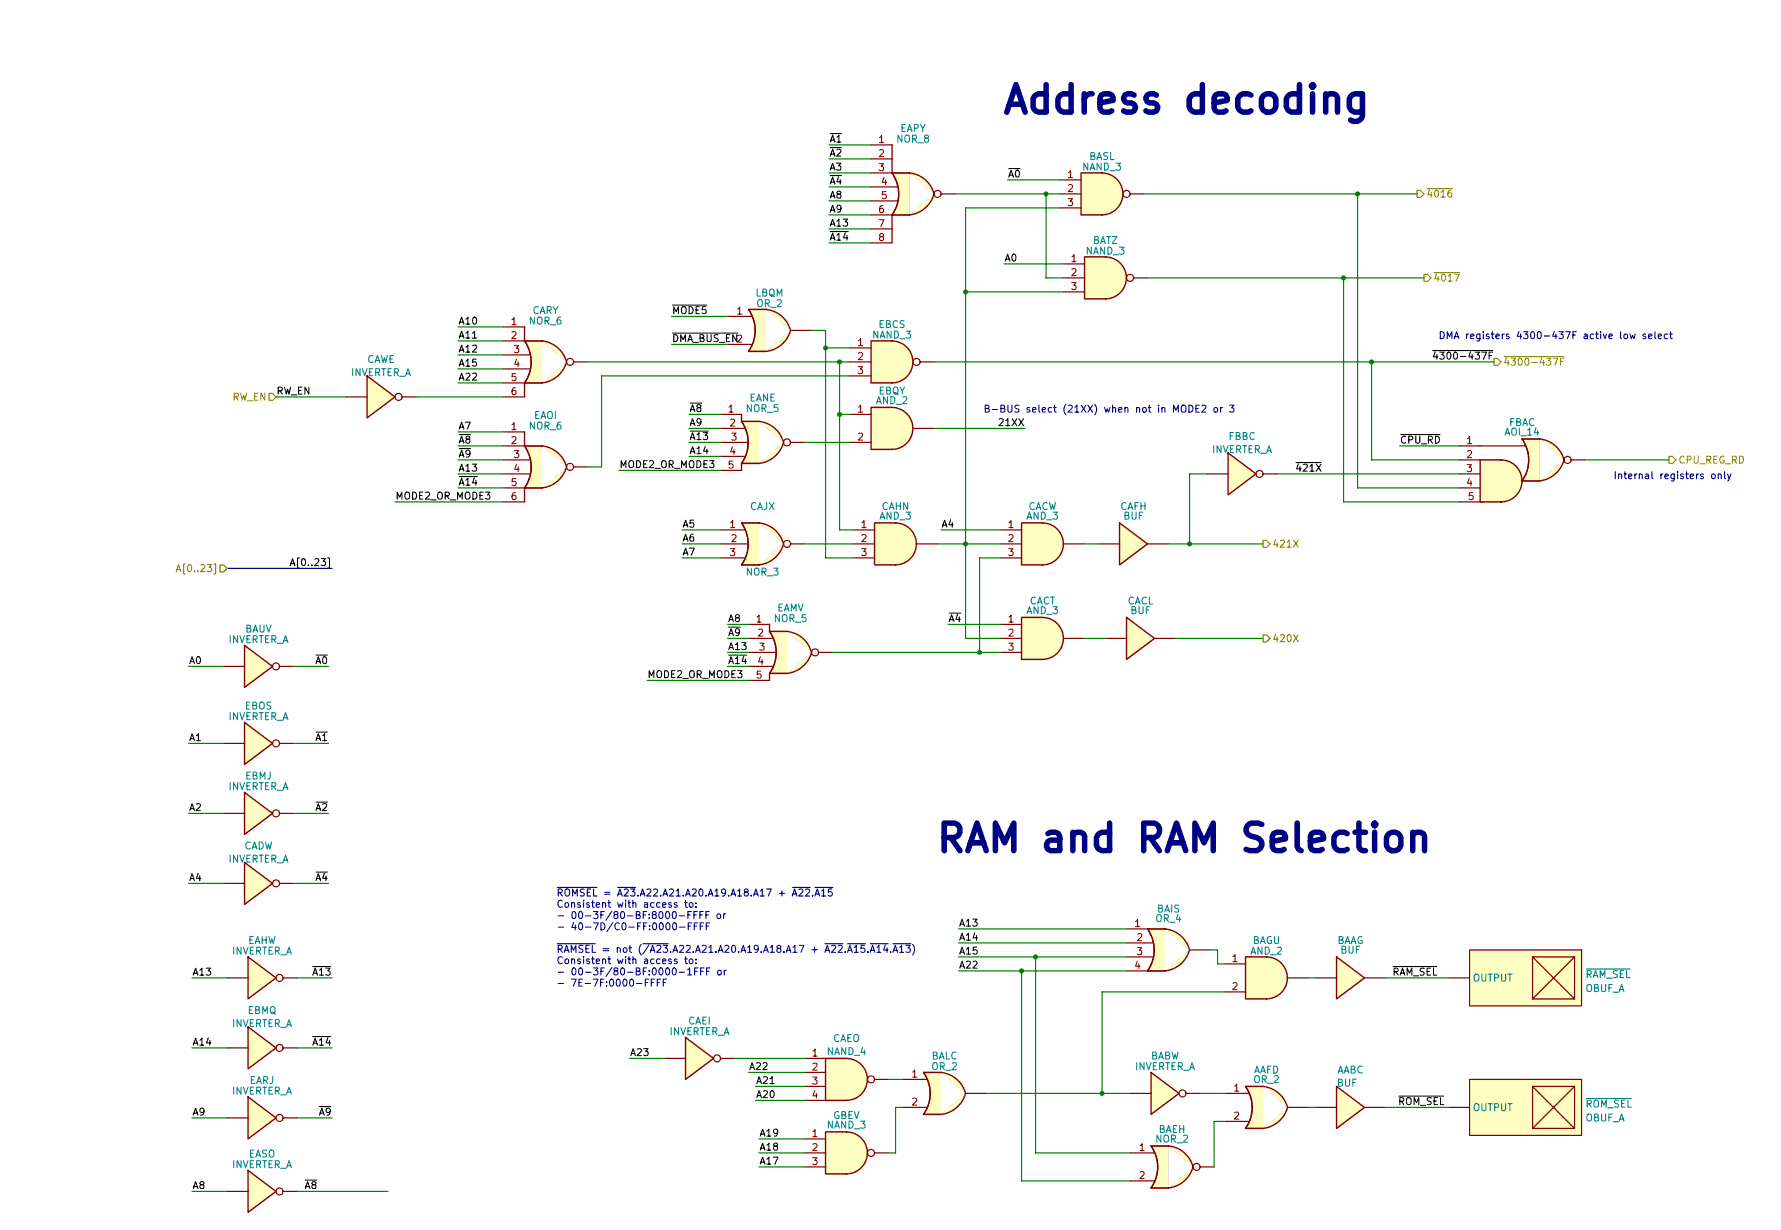
[picture p98: schematic rw_decoding.kicad_sch, part in row 2, column 2]

Parts:
AABC: BUF
AABZ: BUF
AAFD: OR_2
AAHT: AND_2
AAJX: NAND_4
AAKO: AND_2
AALV: NAND_4
AAMX: INVERTER_A
ABORT: IBUF
ACPQ: DELAY_BUF
BAAG: BUF
BAAO: BUF
BABK: BUF
BABL: BUF
BABW: INVERTER_A
BAEH: NOR_2
BAGU: AND_2
BAIS: OR_4
BALC: OR_2
BASL: NAND_3
BATZ: NAND_3
BAUV: INVERTER_A
BBER: AND_3
BBNW: DFFR_A
BBQF: INVERTER_A
BBSQ: NAND_5
BBUI: NAND_4
BBWK: NAND_2
BBXY: INVERTER_A
BBYP: INVERTER_A
BBZQ: NAND_5
BBZX: AOI_14
BCDB: AOI_33
BCFJ: AND_4
CACL: BUF
CACT: AND_3
CACW: AND_3
CADW: INVERTER_A
CAEI: INVERTER_A
CAEO: NAND_4
CAFH: BUF
CAHN: AND_3
CAJX: NOR_3
CARY: NOR_6
CAWE: INVERTER_A
CBIS: INVERTER_A
CPUCK: OBUF_A
DADO: NAND_4
DBIS: BUF
DBPI: BUF
DBVA: BUF
DCDY: INVERTER_A
DCIN: INVERTER_A
DCQF: DELAY_BUF
DFAA: DELAY_BUF
DFAF: DELAY_BUF
EACZ: NOR_2
EAHW: INVERTER_A
EAMV: NOR_5
EANE: NOR_5
EAOI: NOR_6
EAPY: NOR_8
EARJ: INVERTER_A
EASO: INVERTER_A
EBCS: NAND_3
EBMJ: INVERTER_A
EBMQ: INVERTER_A
EBOS: INVERTER_A
EBQY: AND_2
EBRW: DELAY_BUF
EFED: INVERTER_A
EFEL: NOR_2
FBAC: AOI_14
FBBC: INVERTER_A
FBTA: BUF
FFCV: NAND_2
FFGS: NAND_2
GAJP: BUF
GBEI: OR_2
GBEV: NAND_3
GBGK: DELAY_BUF
GFAY: DELAY_BUF
GFCD: DELAY_BUF
HAAI: NAND_2
HAXK: BUF
HBFW: TRI_BUF_IF0
HBGC: TRI_BUF_IF0
HBPL: BUF
HBQO: TRI_BUF_IF0
IAAG: DELAY_BUF
IANF: OR_2
IBKU: OR_2
IBPY: NOR_2
IBTS: TRI_INV_IF2
IBUA: OR_2
IBUD: BUF
JBCR: OR_2
JBIL: BUF
JBRX: INVERTER_A
JBSB: TRI_BUF_IF0
JBSU: NOR_2
KBWT: OR_2
KBWU: TRI_BUF_IF0
LBQM: OR_2
LCWR: TRI_BUF_IF0
MAWK: BUF
MBBX: INVERTER_A
MBZG: OR_2
MF: OBUF_A
NBXE: TRI_BUF_IF0
NBZA: OR_2
NCAN: OR_2
OAAF: INVERTER_A
OAUS: TRI_BUF_IF0
OBXV: INVERTER_A
OCBU: TRI_BUF_IF0
OCDM: AOI_33
OCFG: INVERTER_A
OCIS: TRI_BUF_IF0
ODNR: TRI_BUF_IF0
ODSN: BUF
OEAE: BUF
SYSCLK: IOBUF_A
UNCONNECTEDPIN: IBUF
VP: OBUF_A
XF: OBUF_A
~{CPU_RD}: OBUF_A
~{CPU_WR}: OBUF_A
~{DMA}: OBUF_A
~{ML}: OBUF_A
~{PARD}: OBUF_A
~{PAWR}: OBUF_A
~{RAM_SEL}: OBUF_A
~{ROM_SEL}: OBUF_A

Connections:
21XX: BBSQ.2, BBZQ.2, EBQY.3
420X: CACL.2
421X: CAFH.2, FBBC.1
65816_ABORT: ABORT.1
65816_IRQ: NCAN.1
65816_MF: HBGC.1 (IN), HBGC.3 (IN)
65816_ML: ODNR.1 (IN), ODNR.3 (IN)
65816_NMI: KBWT.1
65816_VP: DBVA.1
65816_XF: HBQO.1 (IN), HBQO.3 (IN)
+5V: BBWK.1, DADO.1, DADO.2, DADO.3, FFCV.1, FFGS.1, HAAI.1, OCDM.1
A0: BATZ.1, BAUV.1
A1: EBOS.1
A2: EBMJ.1
A3: EAPY.3
A4: CACW.1, CADW.1
A5: CAJX.1
A6: CAJX.2
A7: CAJX.3, EAOI.1
A8: EAMV.1, EAPY.5, EASO.1
A9: EANE.2, EAPY.6, EARJ.1
A10: CARY.1
A11: CARY.2
A12: CARY.3
A13: BAIS.1, EAHW.1, EAMV.3, EAOI.4, EAPY.7
A14: BAIS.2, EANE.4, EBMQ.1
A15: BAEH.1, BAIS.3, CARY.4
A17: GBEV.3
A18: GBEV.2
A19: GBEV.1
A20: CAEO.4
A21: CAEO.3
A22: BAEH.2, BAIS.4, CAEO.2, CARY.5
A23: CAEI.1
CPU_CLK: IBUA.1
CPU_REG_RD: FBAC.3
DATABUS_LATCH: ODSN.2
DMA_B->A: AAJX.2, AAMX.1, BCFJ.2, OCIS.1 (IN), OCIS.3 (IN)
DMA_OFF: NBZA.1
DMA_ON: JBSU.1
DMA_WR: BBZX.1, BCFJ.5
GND: EACZ.2, EFEL.2
INTERNAL_SYSCLK: JBSB.1 (IN), JBSB.3 (IN)
MODE2_OR_MODE3: EAMV.5, EANE.5, EAOI.6
MODE4-6: HBGC.2 (~ENA), HBQO.2 (~ENA), ODNR.2 (~ENA)
MODE4_OR_MODE5: OBXV.1, OCFG.1
unnamed: AABC.1, AAFD.3
unnamed: AABZ.1, DCQF.2
unnamed: AABZ.2, BBWK.2
unnamed: AAFD.1, BABW.2
unnamed: AAFD.2, BAEH.3
unnamed: AAHT.3, EBRW.1
unnamed: AAJX.1, AALV.1, BBXY.1, BCDB.1, BCDB.4, BCFJ.1, DCIN.2
unnamed: AAJX.4, AALV.4, BCFJ.4, CBIS.2
unnamed: AAJX.5, ACPQ.1
unnamed: AAKO.3, BABK.1
unnamed: AALV.2, AAMX.2, BCDB.5
unnamed: BAAG.1, BAGU.3
unnamed: BAAO.1, BBER.4
unnamed: BABK.2, EFED.1
unnamed: BABL.1, HBQO.4, KBWU.4, LCWR.4
unnamed: BABL.2, XF.1
unnamed: BABW.1, BAGU.2, BALC.3
unnamed: BAGU.1, BAIS.5
unnamed: BALC.1, CAEO.5
unnamed: BALC.2, GBEV.4
unnamed: BASL.2, BATZ.2, EAPY.9
unnamed: BASL.3, BATZ.3, CACT.2, CACW.2, CAHN.4
unnamed: BBER.3, BBNW.6 (Q)
unnamed: BBNW.1 (~RESET), BBNW.5 (~RESET)
unnamed: BBQF.1, BBWK.3
unnamed: BBQF.2, EACZ.1
unnamed: BBSQ.3, BBUI.2, BBXY.2, BBZQ.3, BBZX.4
unnamed: BBYP.2, BBZQ.4, BBZX.3
unnamed: BBZX.3, HAXK.1, JBCR.1
unnamed: CACL.1, CACT.4
unnamed: CACT.3, CACW.3, EAMV.6
unnamed: CACW.4, CAFH.1
unnamed: CAEI.2, CAEO.1
unnamed: CAHN.1, CARY.7, EBCS.2, EBQY.1
unnamed: CAHN.2, CAJX.4
unnamed: CAHN.3, EBCS.1, LBQM.3
unnamed: CARY.6, CAWE.2
unnamed: CPUCK.1, HBPL.2
unnamed: DADO.4, EACZ.3
unnamed: DADO.5, ~{CPU_RD}.1
unnamed: DBIS.1, FBTA.2
unnamed: DBIS.2, ~{CPU_WR}.1
unnamed: DBPI.1, HBGC.4, NBXE.4, OAUS.4
unnamed: DBPI.2, MF.1
unnamed: DCDY.1, UNCONNECTEDPIN.1
unnamed: DCDY.2, IBPY.2
unnamed: DFAA.1, DFAF.2
unnamed: DFAA.2, ~{PAWR}.1
unnamed: DFAF.1, EFEL.3
unnamed: EANE.6, EBQY.2
unnamed: EAOI.7, EBCS.3
unnamed: EBRW.2, IAAG.1, IANF.2
unnamed: EFED.2, EFEL.1
unnamed: FBTA.1, GAJP.2
unnamed: FFCV.2, JBIL.2
unnamed: FFCV.3, FFGS.2
unnamed: FFGS.3, GFCD.1
unnamed: GAJP.1, HAAI.3
unnamed: GBEI.1, GBGK.2
unnamed: GBEI.3, OAAF.1
unnamed: GFAY.1, GFCD.2
unnamed: GFAY.2, ~{PARD}.1
unnamed: HAAI.2, OAAF.2
unnamed: HBFW.1 (IN), HBFW.3 (IN), SYSCLK.2 (INPUT)
unnamed: HBFW.2 (~ENA), JBRX.1, OCDM.3
unnamed: HBPL.1, IBUA.3
unnamed: IAAG.2, IANF.1
unnamed: IANF.3, JBIL.1
unnamed: IBKU.3, IBTS.2
unnamed: IBTS.1 (~ENA), JBRX.2, JBSB.2 (~ENA)
unnamed: IBTS.3, SYSCLK.1 (DRV_LOW), SYSCLK.3 (~DRV_HIGH)
unnamed: IBUD.1, JBSU.3
unnamed: IBUD.2, ~{DMA}.1
unnamed: JBCR.3, MAWK.1
unnamed: KBWT.3, LCWR.1 (IN), LCWR.3 (IN)
unnamed: MBBX.2, MBZG.2
unnamed: MBZG.3, ODSN.1
unnamed: NBXE.1 (IN), NBXE.3 (IN), NBZA.3
unnamed: NBXE.2 (~ENA), OBXV.2
unnamed: NCAN.3, OCBU.1 (IN), OCBU.3 (IN)
unnamed: OCBU.4, OCIS.4, ODNR.4, OEAE.1
unnamed: OEAE.2, ~{ML}.1
RW: BBSQ.4, BBUI.3, BBYP.1
RW_EN: BBSQ.1, BBUI.1, BBZQ.1, BBZX.5, CAWE.1
SYNCED_REFRESH_EN: JBCR.2
VP: DBVA.2, VP.1
wIBPY: IBKU.1, IBPY.3, IBUA.2, JBSU.2, KBWT.2, NBZA.2, NCAN.2
wOATI_~XIN/256: OAUS.1 (IN), OAUS.3 (IN)
wOCOG_~MODE7: MBBX.1
wSYSCLK: AAJX.3, AALV.3, BBSQ.5, BBUI.4, BBZQ.5, BBZX.2, BCDB.2, BCDB.6, BCFJ.3, HBFW.4, IBKU.2, JBSB.4, MBZG.1
~21XX_DMA_RD: AAHT.2, ACPQ.2
~21XX_DMA_WR: AAKO.2, AALV.5
~21XX_RD: AAHT.1, BBSQ.6
~21XX_WR: AAKO.1, BBZQ.6
~421X: FBAC.3, FBBC.2
~4016: BASL.4, FBAC.4
~4017: BATZ.4, FBAC.5
~4300-437F: EBCS.4, FBAC.2
~A0: BASL.1, BAUV.2
~A1: EAPY.1, EBOS.2
~A2: EAPY.2, EBMJ.2
~A4: CACT.1, CADW.2, EAPY.4
~A8: EANE.1, EAOI.2, EASO.2
~A9: EAMV.2, EAOI.3, EARJ.2
~A13: EAHW.2, EANE.3
~A14: EAMV.4, EAOI.5, EAPY.8, EBMQ.2
~CPU_RD: BAAO.2, DCQF.1, FBAC.1
~CPU_WR: GBEI.2, GBGK.1, HAXK.2
~DMA_BUS_EN: LBQM.2
~DMA_BUS_ON: BCDB.3, CBIS.1, KBWU.1 (IN), KBWU.3 (IN)
~DMA_RD: BBER.2, BBNW.2 (D), BCDB.3
~DMA_RW_EN: DCIN.1
~MAWK_WR: MAWK.2
~MODE0_OR_MODE6: OCDM.2, OCDM.4
~MODE1: OCDM.5
~MODE4_OR_MODE5: OCDM.6, OCFG.2
~MODE4_OR_MODE6: LCWR.2 (~ENA), OCBU.2 (~ENA)
~MODE4: IBPY.1
~MODE5: KBWU.2 (~ENA), LBQM.1, OCIS.2 (~ENA)
~MODE6: OAUS.2 (~ENA)
~RAM_SEL: BAAG.2, ~{RAM_SEL}.1
~RD: BBER.1, BBUI.5
~ROM_SEL: AABC.2, ~{ROM_SEL}.1
~XIN1: BBNW.3 (CLK), BBNW.4 (~CLK)
~wRDY: OCDM.3

Notes on the sheet:
External SYSCLK when 1) RDY = 0 and mode 1-5 or 7 2) mode 2-3 or mode 7
Address decoding
Internal registers only
To_bottom_of_chip_too Reg Read occurs when RW = '1', SYSCLK = '1', NOT an internal cycle
Latches exernal input data and data bus
RAM and RAM Selection
DMA registers 4300-437F active low select
To DMA section and bottom section
B-BUS select (21XX) when not in MODE2 or 3
~{ROMSEL} = ~{A23}.A22.A21.A20.A19.A18.A17 + ~{A22}.~{A15} Consistent with access to: - 00-3F/80-BF:8000-FFFF or - 40-7D/C0-FF:0000-FFFF ~{RAMSEL} = not (~{/A23}.A22.A21.A20.A19.A18.A17 + ~{A22}.~{A15}.~{A14}.~{A13}) Consistent with access to: - 00-3F/80-BF:0000-1FFF or - 7E-7F:0000-FFFF
